wrh2/sputnik/Phase0/schedule/Project Schedule Calendar.pdf

# October 2015

Sunday | Monday | Tuesday | Wednesday | Thursday | Friday | Saturday
| | | | 1 | 2 | 3
4 | 5 | 6 | 7 | 8 | 9 | 10
11 | 12 | 13 | 14 | 15 | 16 | 17
18 | 19 | 20 | 21 | 22 | 23 | 24

Gather Requirement Information from PSAS, 1 day

25 | 26 | 27 | 28 | 29 | 30 | 31
Finalize Requirements, 3 days | | Design Initial RF Schematic, 1 day? | Design Initial MCU Schematic, 1 day?
Create Proposal, 1 day | Finalize Proposal, 1 day | Finalize Requirements, 3 days

Overflow Tasks

ID | Name | Start | Finish
27 | Part Selection | Sun 10/18/15 | Tue 10/20/15
47 | Test Completed Boards | Sun 10/18/15 | Tue 10/20/15
46 | Create Project Presentation Board | Wed 10/21/15 | Thu 10/22/15
16 | Design Initial USB to UART Schematic | Tue 10/27/15 | Tue 10/27/15
17 | Design Initial Battery Charger Schematic | Tue 10/27/15 | Tue 10/27/15

# November 2015

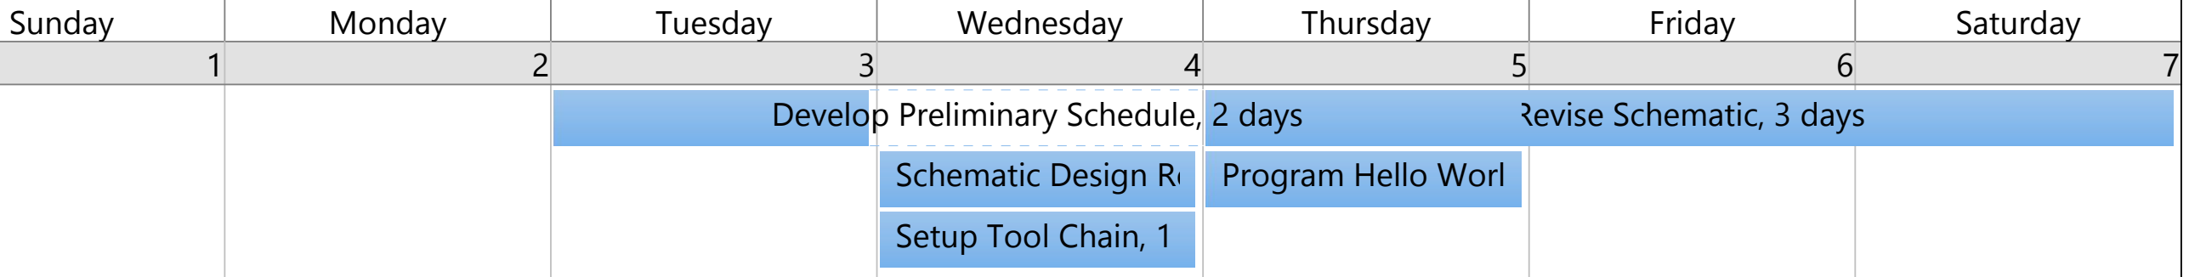
[picture p37: figure]
Sunday; Monday; Tuesday; Wednesday; Thursday; Friday; Saturday; Setup Tool Chain, 1 day

| | Develop Preliminary Schedule, 2 days | Schematic Design Review, 1 day Program Hello World, | Revise Schematic, 3 days | 1 day

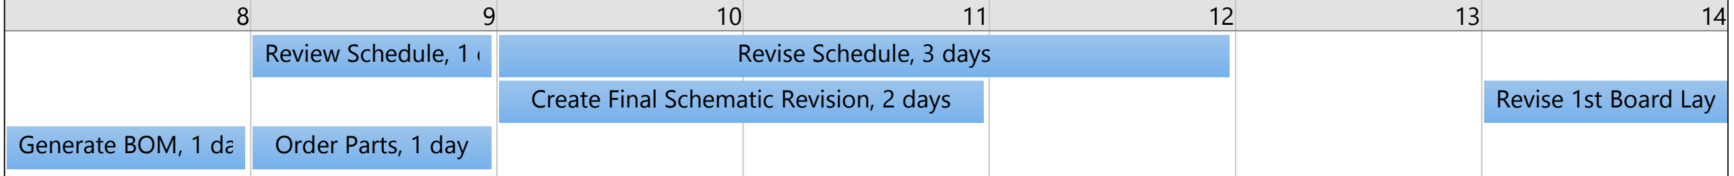
[picture p38: figure]

Generate BOM, 1 day | Review Schedule, 1 day Order Parts, 1 day | Revise Schedule, 3 days
Develop Final Board Layout, 2 days | | Order Boards, 1 day | Develop Test Plans, 3 daysReview Board Layout, 1 day

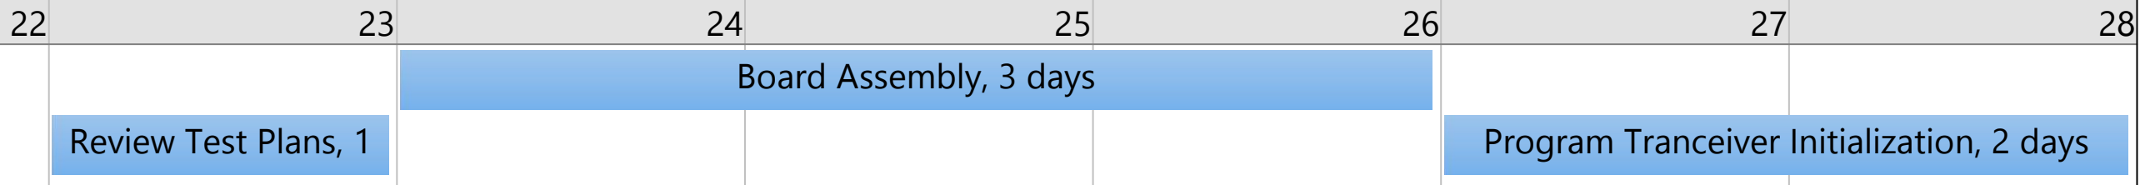
[picture p39: figure]
Review Test Plans, 1 day; Board Assembly, 3 days; Program Tranceiver Initialization, 2 days

29 | 30
Create Final Schematic Revision, 2 days | Revise 1st Board Layout, 5 days

Revise 1st Board Layout, 5 days Develop Block Diagrams, 2 days

Overflow Tasks

ID | Name | Start | Finish
21 | Develop Initial Board Layout | Thu 11/12/15 | Fri 11/13/15
26 | Create Solder Paste Stencil | Sun 11/22/15 | Sun 11/22/15
41 | Program Test of GPIO | Fri 11/27/15 | Sat 11/28/15
33 | Program Tansceiver Listening Interrupt | Sun 11/29/15 | Mon 11/30/15
35 | Program Tranceiver Broadcasting | Sun 11/29/15 | Mon 11/30/15
38 | Program Test of Timers | Sun 11/29/15 | Mon 11/30/15

# December 2015

Sunday | Monday | Tuesday | Wednesday | Thursday | Friday | Saturday
| | 1 | 2 | 3 | 4 | 5
6 | 7 | 8 | 9 | 10 | 11 | 12
Create Project Presentation Video, 3 days
13 | 14 | 15 | 16 | 17 | 18 | 19
20 | 21 | 22 | 23 | 24 | 25 | 26
27 | 28 | 29 | 30 | 31

Create Project Presentation Video, 3 days

Overflow Tasks

ID | Name | Start | Finish
39 | Program Test of SPI | Tue 12/1/15 | Wed 12/2/15
40 | Program Test of UART | Tue 12/1/15 | Wed 12/2/15
