wrh2/sputnik/Phase0/schedule/Project Schedule.pdf

ID | Task
Mode
| Task Name | Duration | Start | Finish | Predecessors
1 | Development Board for Cubesat Communication | 65 days
2 | Project Proposal
3 | Create Proposal | 1 day | Sun 10/18/15Sun 10/18/15
4 | Finalize Proposal | 1 day | Wed 10/21/15Wed 10/21/153
5 | Project Requirements
6 | Gather Requirement Information from PSAS | 6 days | Sun 10/18/15 | Fri 10/23/15
7 | Finalize Requirements | 3 days | Sat 10/24/15 Mon 10/26/156
8 | Project Schedule
10 | Schedule Review | 1 day | Mon 11/9/15Mon 11/9/159
9 | Preliminary Schedule | 2 days | Tue 11/3/15 | Wed 11/4/15
11 | Schedule Revision | 3 days | Tue 11/10/15Thu 11/12/1510
12 | Board Schematic
14 | Schematic Design Review1 day | Wed 11/4/15Wed 11/4/1513
15 | Schematic Revision | 7 days | Thu 11/5/15 | Wed 11/11/1514
13 | Preliminary Schematic | 12 days | Thu 10/22/15Mon 11/2/155
16 | Final Schematic Revision2 days | Thu 11/12/15Fri 11/13/15 | 15
17 | Board Layout
20 | Board Design Review | 1 day | Mon 11/16/15 | Mon 11/16/15 | 19
21 | Final Board Layout | 3 days | Sat 11/14/15 Mon 11/16/1516
18 | Preliminary Layout | 7 days | Tue 11/3/15 | Mon 11/9/1513
19 | Board Layout Revision | 6 days | Tue 11/10/15Sun 11/15/1518
22 | Create Boards
27 | Board Assembly | 5 days | Thu 11/26/15Mon 11/30/1526,25
23 | Part Selection | 5 days | Tue 11/3/15 | Sat 11/7/15 | 13
25 | Order and Receive Parts5 days | Fri 11/13/15 | Tue 11/17/1524
24 | Generate BOM | 1 day | Thu 11/12/15Thu 11/12/1515
26 | Order and Receive Boards9 days | Tue 11/17/15Wed 11/25/1516,21
28 | Board Programming
30 | Program Hello World | 4 days | Thu 11/5/15 | Sun 11/8/15 | 29
S | S | M

Oct 18, '15

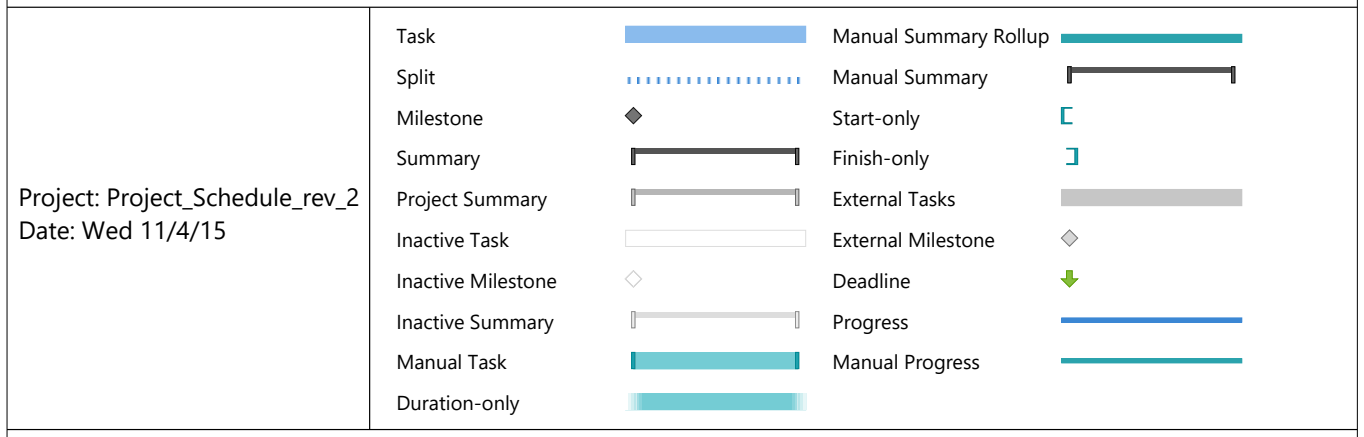
[picture p40: figure]
Task; Split; Milestone; Summary; Project Summary; Inactive Task; Inactive Milestone; Inactive Summary; Manual Task; Duration-only; Manual Summary Rollup; Manual Summary; Start-only; Finish-only; External Tasks; External Milestone; Deadline; Progress; Manual Progress; Project: Project_Schedule_rev_2 Date: Wed 11/4/15

ID | Task
Mode
Task Name | Duration | Start | Finish | Predecessors
31 | Program Transceiver | 16 days | Mon 11/9/15Tue 11/24/1530
29 | Setup Tool Chain | 1 day | Wed 11/4/15Wed 11/4/15
32 | System Design/Modeling | 5 days | Sat 11/14/15 Wed
11/18/15
33 | Test Plan | 5 days | Sat 11/21/15 Wed
11/25/15
34 | Project Presentation/Demo5 days | Thu 12/3/15 | Mon 12/7/1533
S | S | M

Oct 18, '15

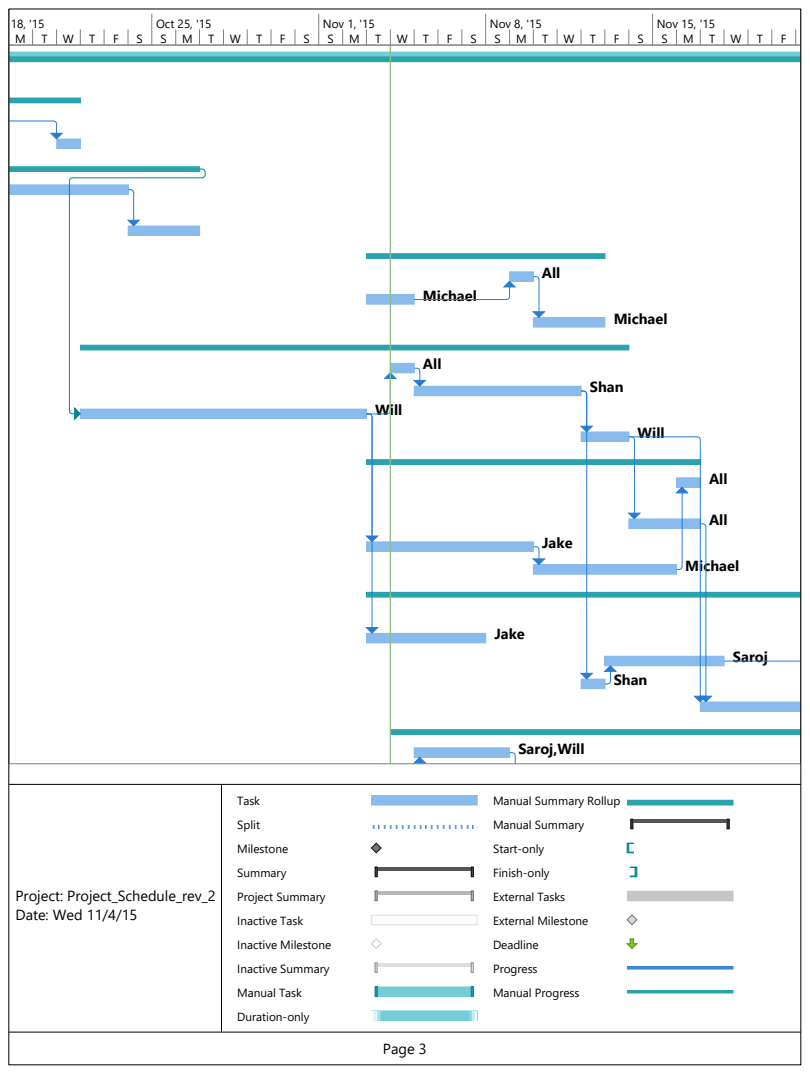
[picture p41: page 3]
All; Michael; Shan; Will; Jake; Saroj; Saroj,Will; Oct 18, '15; Oct 25, '15; Nov 1, '15; Nov 8, '15; Nov 15, '15; Task; Split; Milestone; Summary; Project Summary; Inactive Task; Inactive Milestone; Inactive Summary; Manual Task; Duration-only; Manual Summary; Start-only; Finish-only; External Tasks; External Milestone; Deadline; Progress; Manual Progress; Project: Project_Schedule_rev_2 Date: Wed 11/4/15

Manual Summary Rollup

### Will,Saroj,Michael

### All

M | T | W | T | F | S | S | M | T | W | T | F | S | S | M | T | W | T | F | S | S | M | T | W | T | F | S | S | M | T | W | T | F
Oct 18, '15 | Oct 25, '15 | Nov 1, '15 | Nov 8, '15 | Nov 15, '15

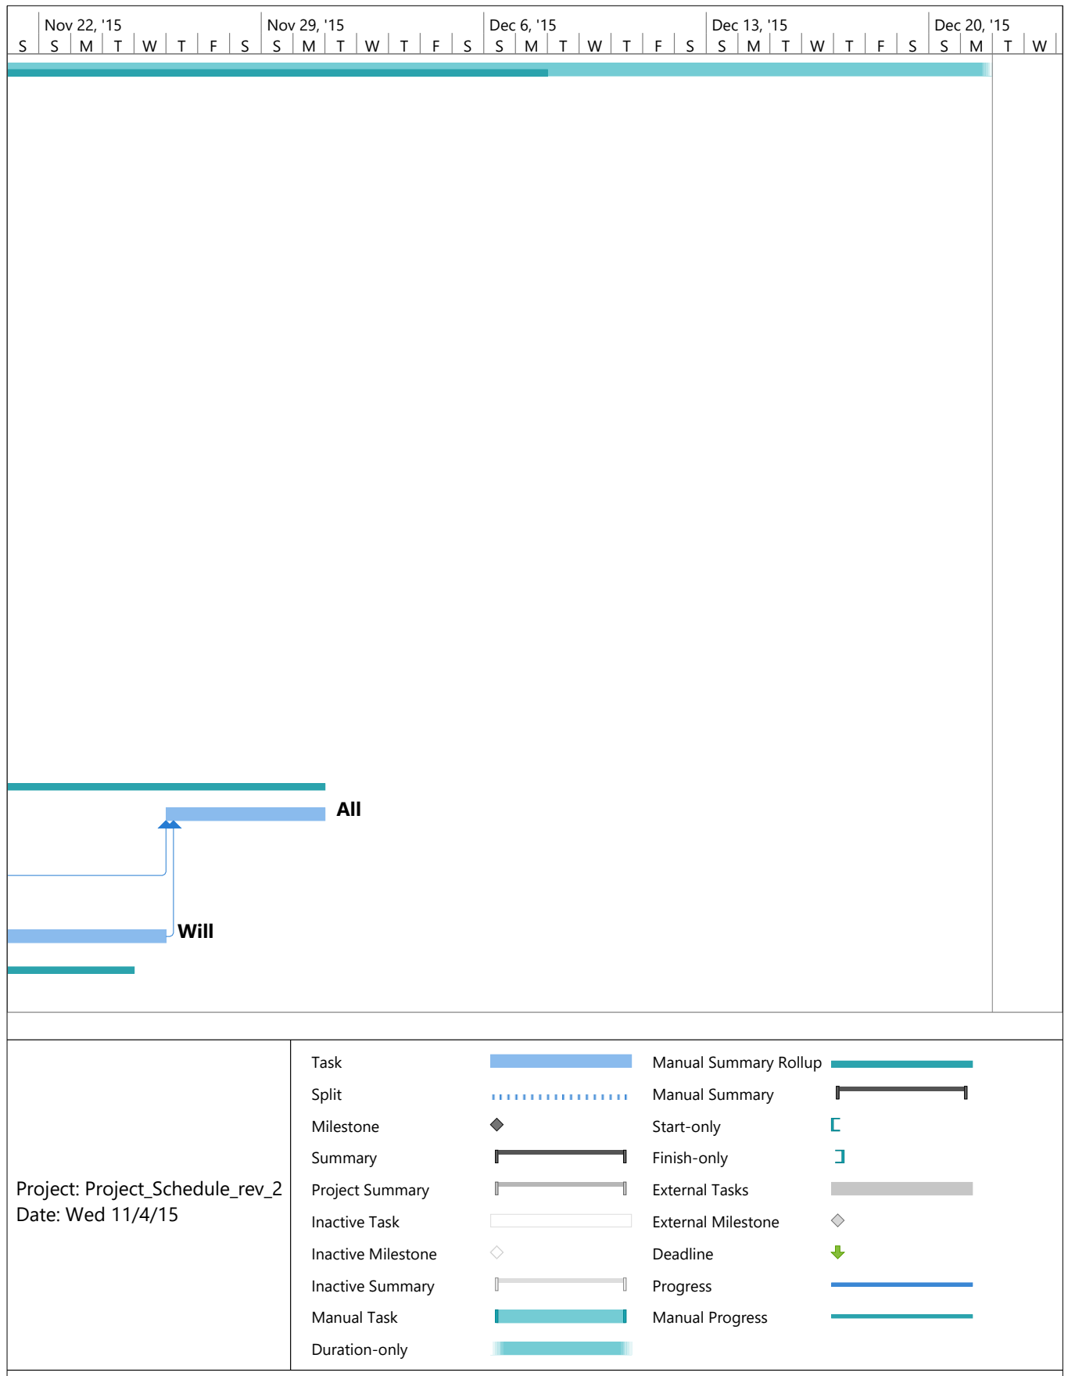
[picture p42: figure]
All; Saroj; Will; Nov 22, '15; Nov 29, '15; Dec 6, '15; Dec 13, '15; Dec 20, '15; Task; Split; Milestone; Summary; Project Summary; Inactive Task; Inactive Milestone; Inactive Summary; Manual Task; Duration-only; Manual Summary Rollup; Manual Summary; Start-only; Finish-only; External Tasks; External Milestone; Deadline; Progress; Manual Progress; Project: Project_Schedule_rev_2 Date: Wed 11/4/15

### Michael

### Will,Saroj

### All

### All

### All

S | S | M | T | W | T | F | S | S | M | T | W | T | F | S | S | M | T | W | T | F | S | S | M | T | W | T | F | S | S | M | T | W
Nov 22, '15 | Nov 29, '15 | Dec 6, '15 | Dec 13, '15 | Dec 20, '15
