wrh2/sputnik/images/phase0/BW.JPG

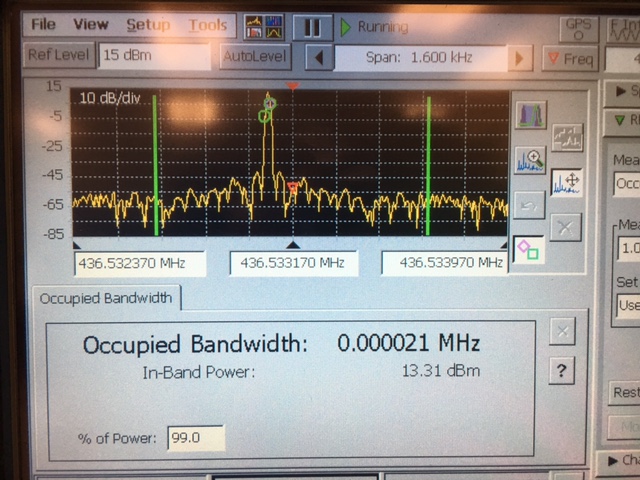
images/phase0/BW.JPG
