wrh2/sputnik/images/phase0/Channel_Power.JPG

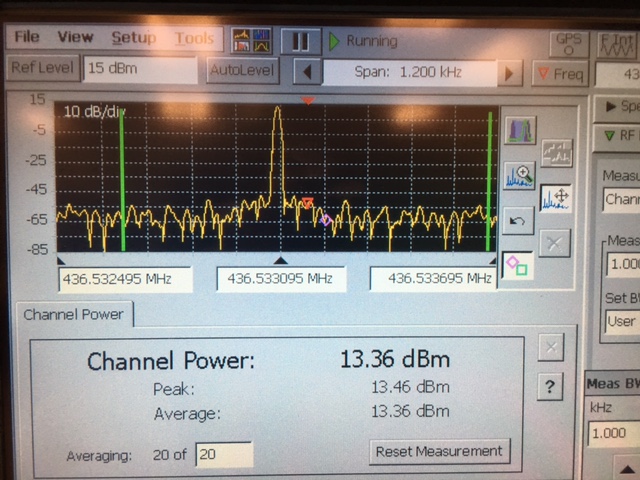
images/phase0/Channel_Power.JPG
