wrh2/sputnik/images/phase0/Field_Strength.JPG

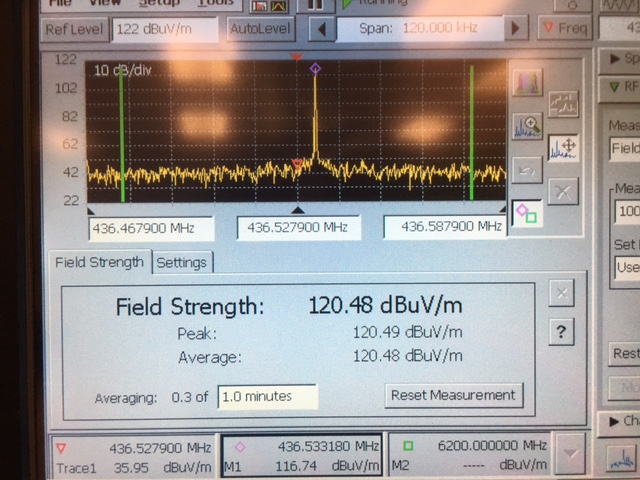
images/phase0/Field_Strength.JPG
