wrh2/sputnik/images/phase0/IMG_0521.JPG

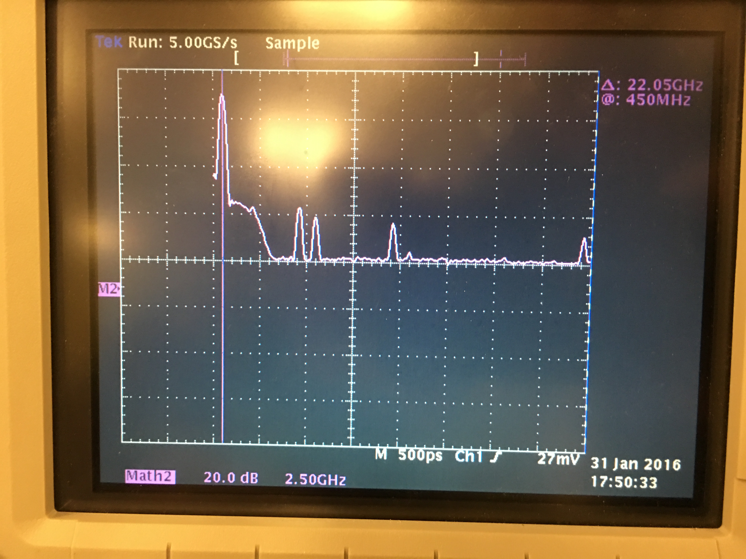
images/phase0/IMG_0521.JPG
