wrh2/sputnik/images/phase0/IMG_0522.JPG

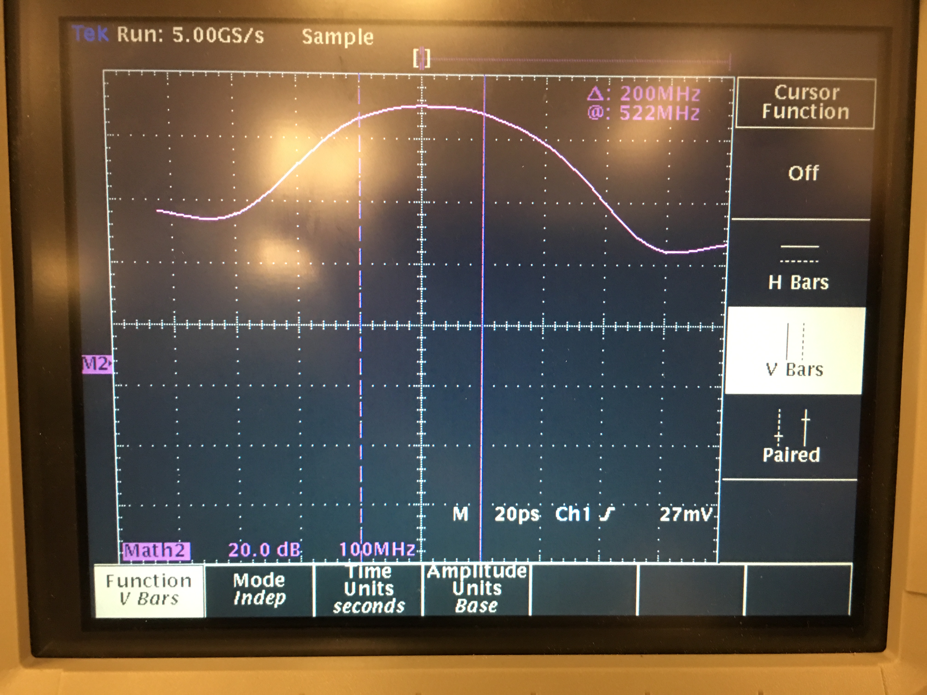
images/phase0/IMG_0522.JPG
