wrh2/sputnik/images/phase0/IMG_0523.JPG

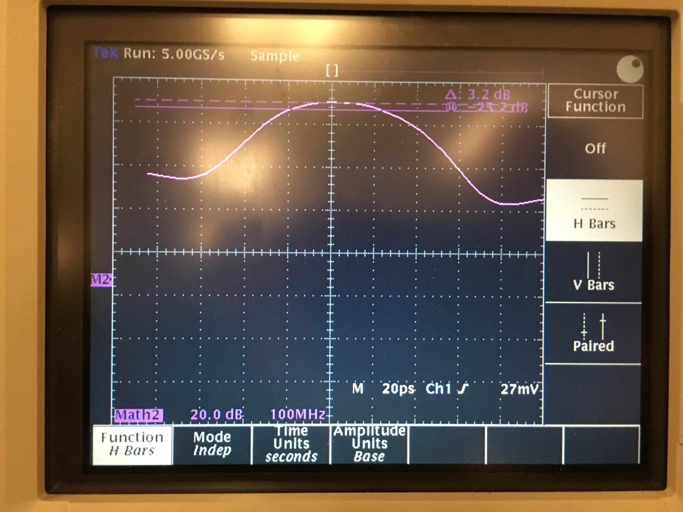
images/phase0/IMG_0523.JPG
