wrh2/sputnik/images/phase0/IMG_0524.JPG

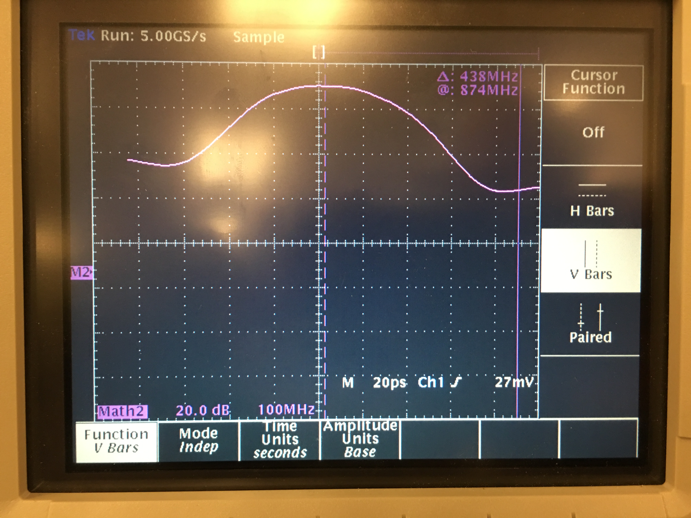
images/phase0/IMG_0524.JPG
