wrh2/sputnik/images/phase0/IMG_0525.JPG

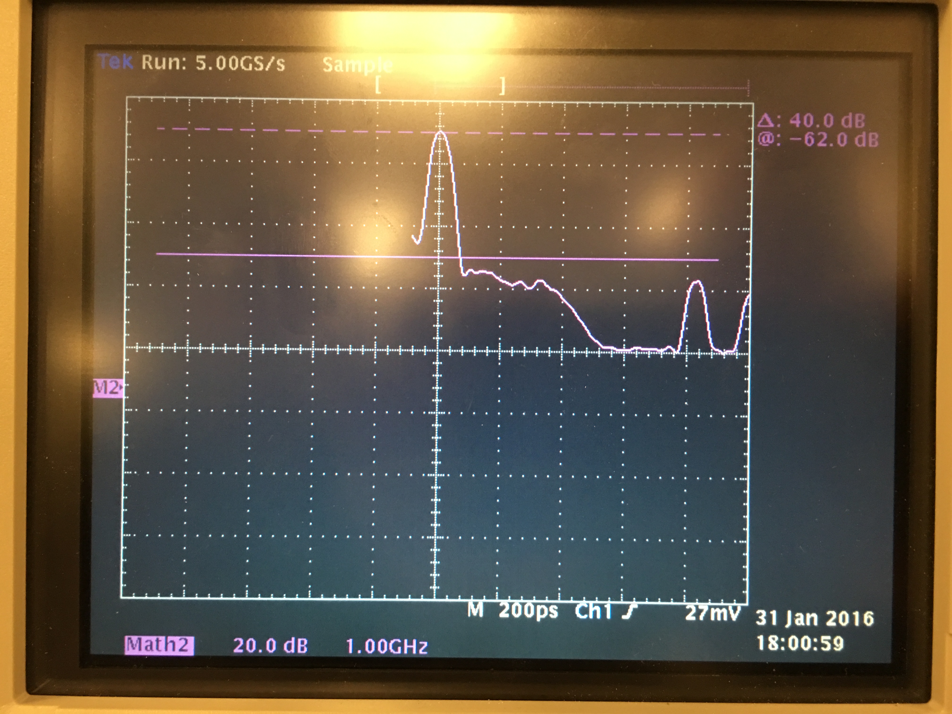
images/phase0/IMG_0525.JPG
