wrh2/sputnik/images/phase0/IMG_0526.JPG

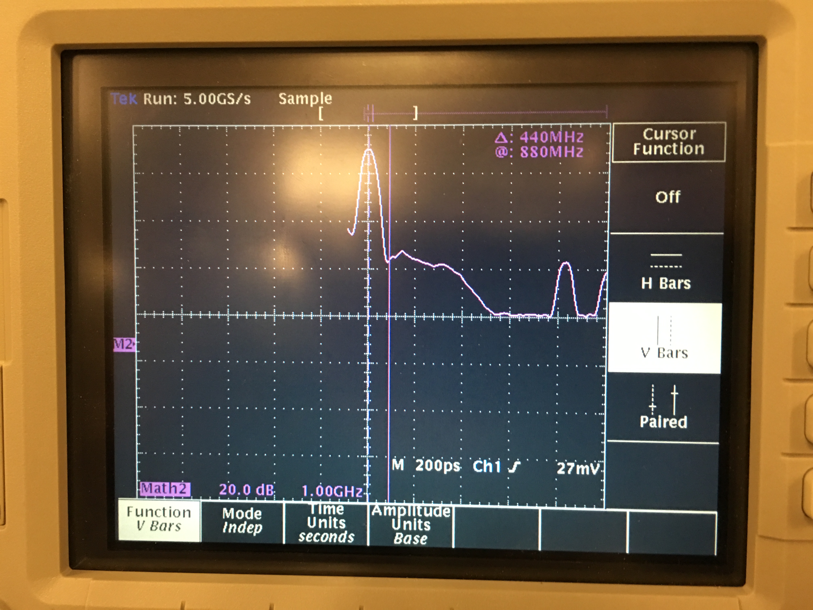
images/phase0/IMG_0526.JPG
