wrh2/sputnik/images/phase0/spurs.JPG

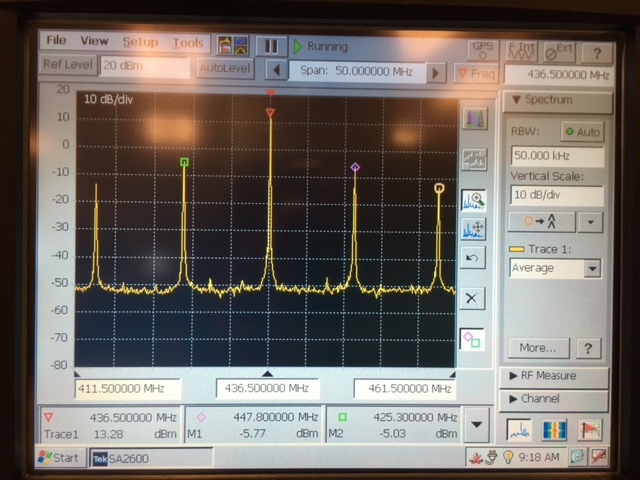
images/phase0/spurs.JPG
