wrh2/sputnik/images/phase1/phase1_HL.png

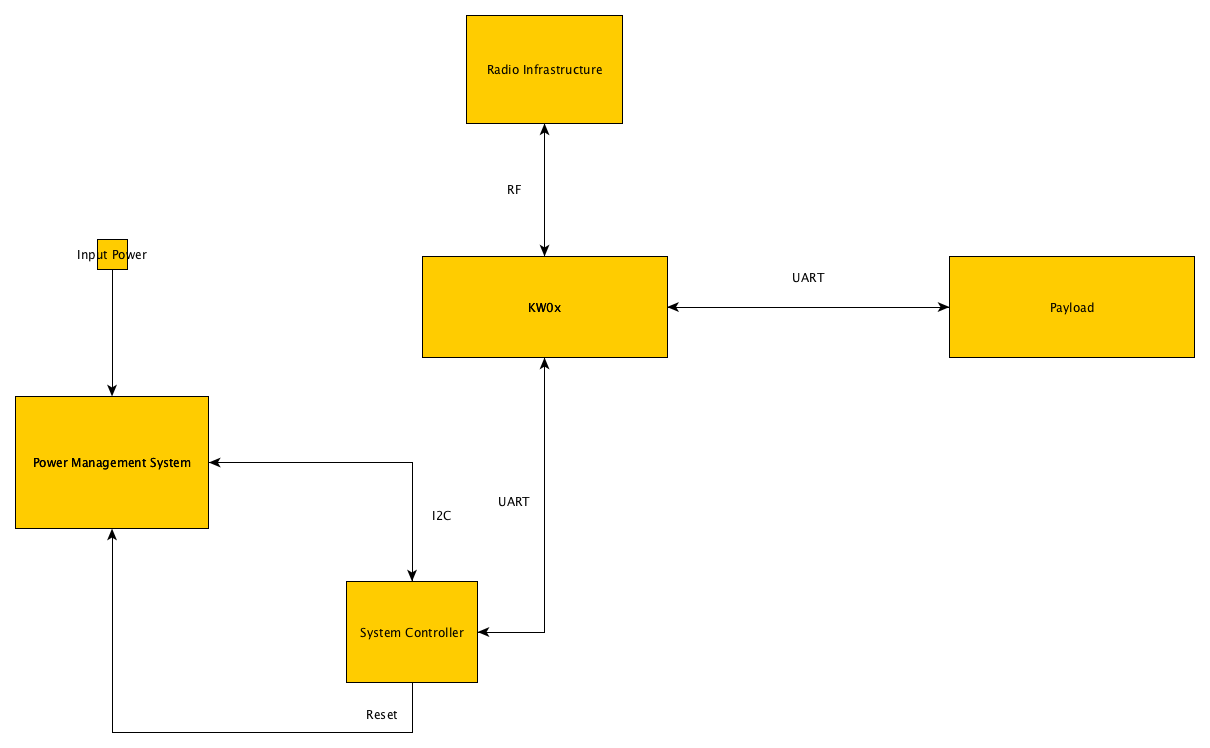
images/phase1/phase1_HL.png
