wrh2/sputnik/Phase0/eagle/psas_c3_sch.png

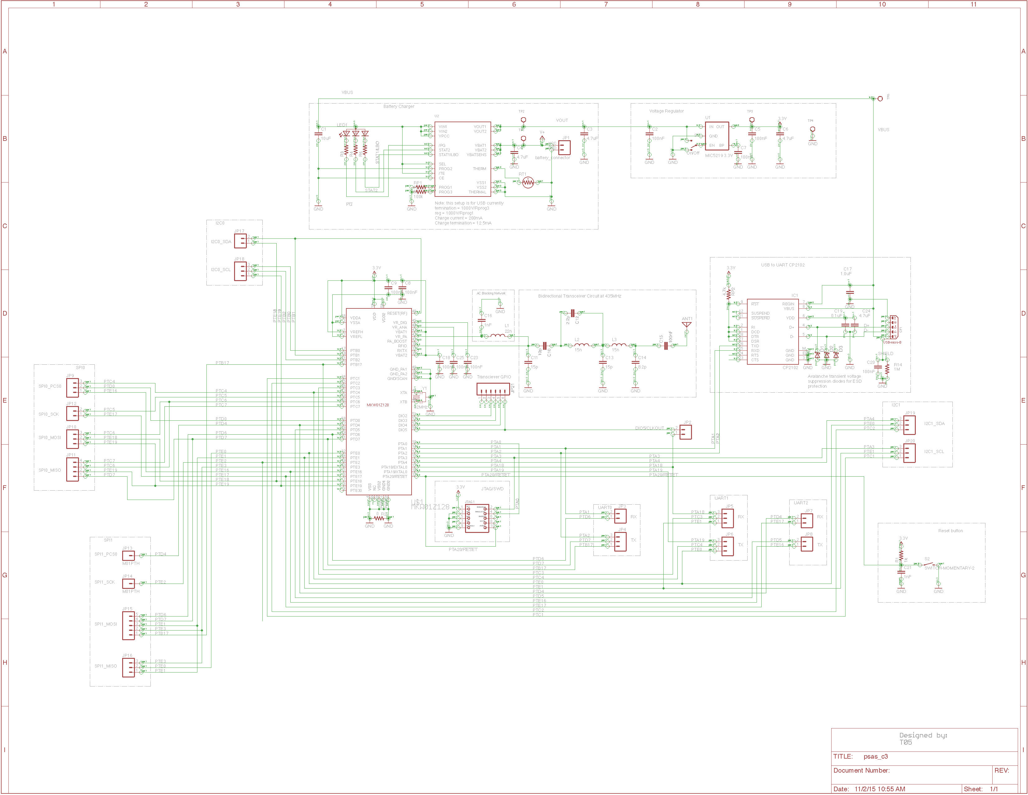
Phase0/eagle/psas_c3_sch.png
