wrh2/sputnik/Phase0/eagle/psas_c3_sch_v2.png

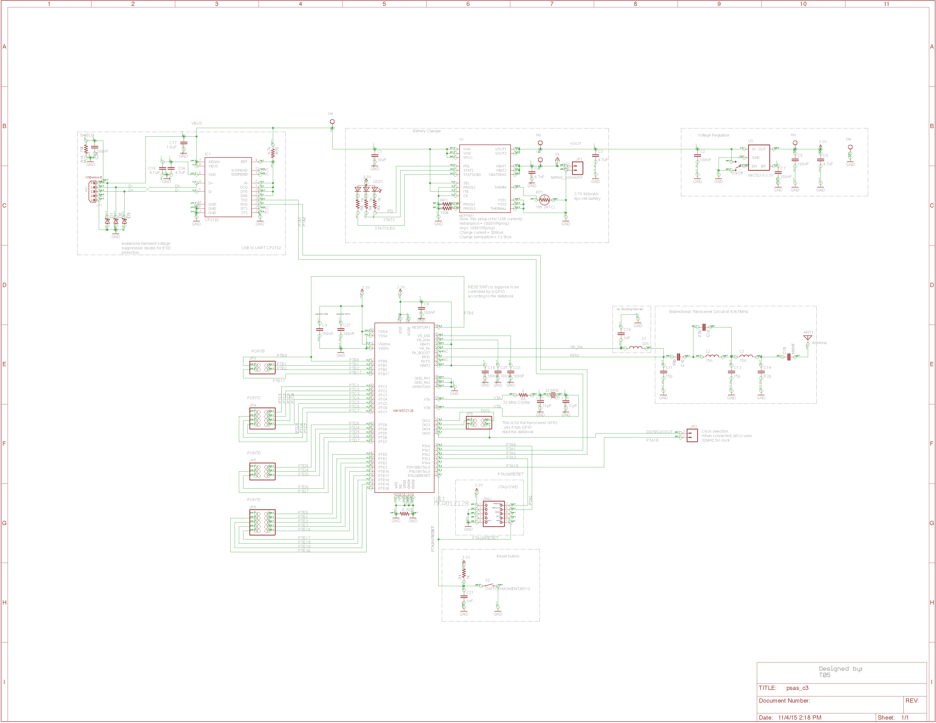
Phase0/eagle/psas_c3_sch_v2.png
