wrh2/sputnik/RF_Materials/Antenna_Filters/prototype_photos/PA210077.JPG

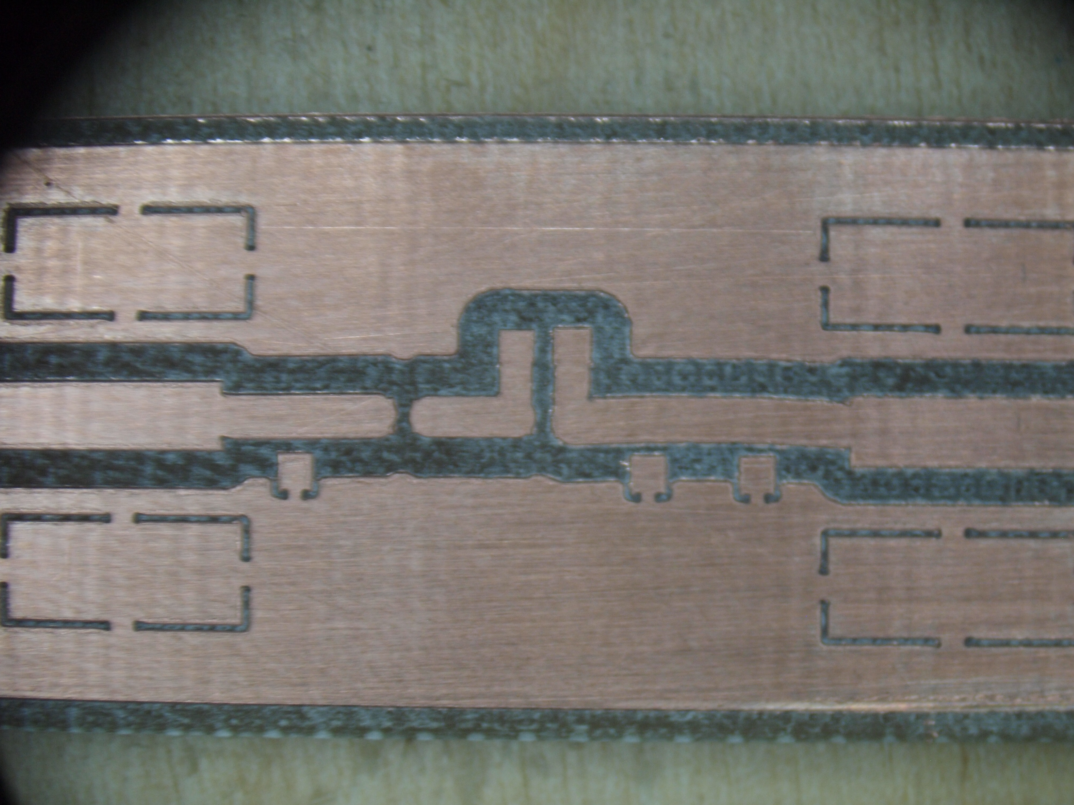
RF_Materials/Antenna_Filters/prototype_photos/PA210077.JPG
