wrh2/sputnik/RF_Materials/Antenna_Filters/prototype_photos/PA210079.JPG

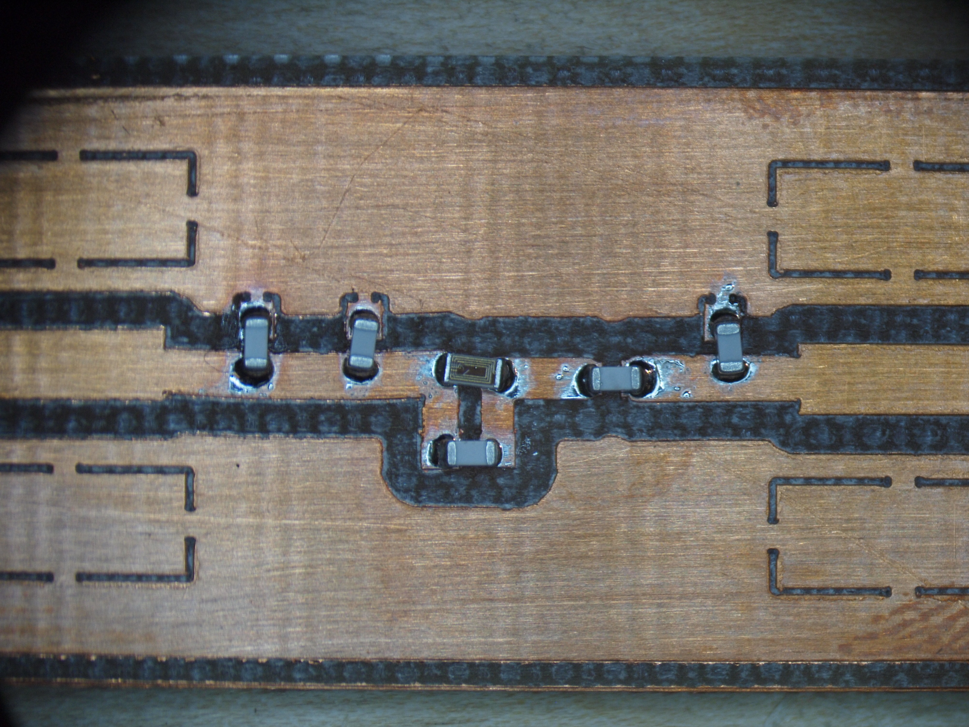
RF_Materials/Antenna_Filters/prototype_photos/PA210079.JPG
