wrh2/sputnik/RF_Materials/Antenna_Filters/prototype_photos/PA270084.JPG

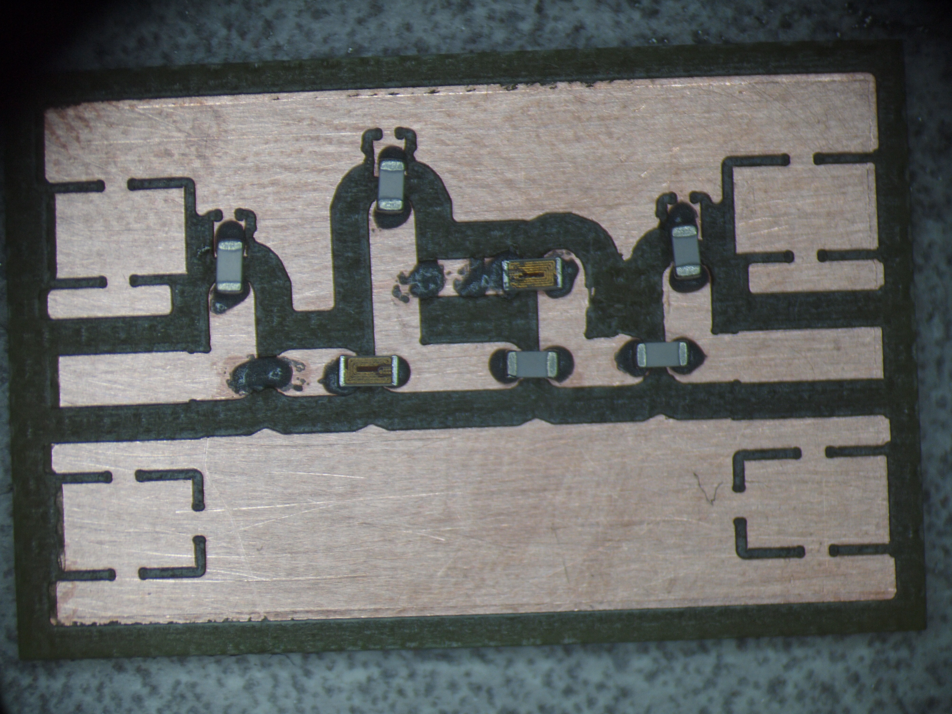
RF_Materials/Antenna_Filters/prototype_photos/PA270084.JPG
