wrh2/sputnik/RF_Materials/Antenna_Filters/prototype_photos/PA270085.JPG

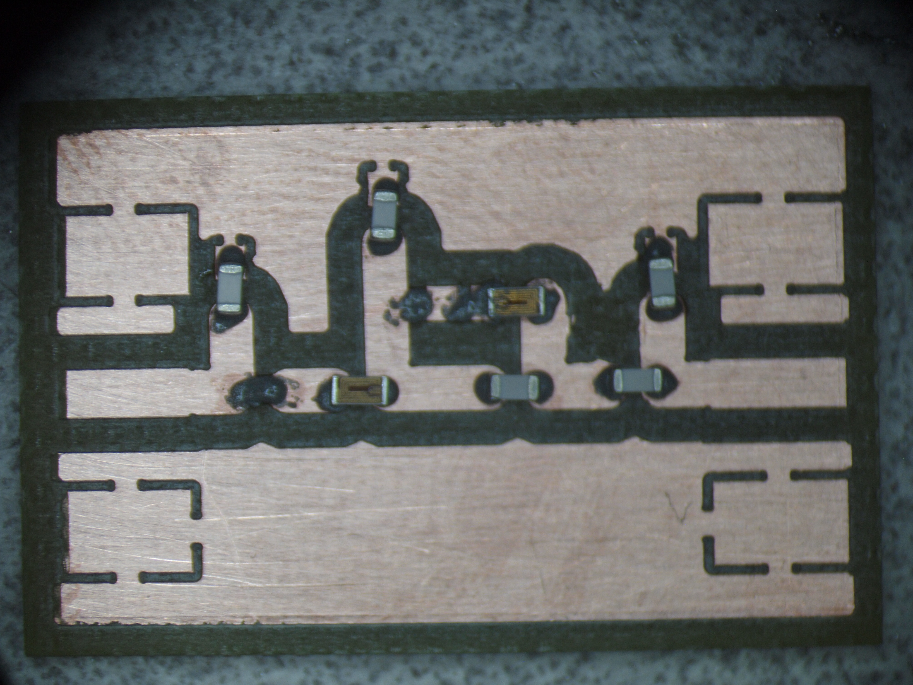
RF_Materials/Antenna_Filters/prototype_photos/PA270085.JPG
