wrh2/sputnik/Vendor Firmware/Kinetis SDK v.1.3.0 API Reference Manual/Kinetis_SDK_Block_Diagram.png

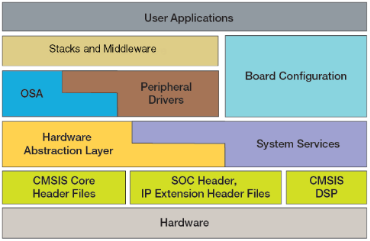
Vendor Firmware/Kinetis SDK v.1.3.0 API Reference Manual/Kinetis_SDK_Block_Diagram.png
