wrh2/sputnik/RF_Materials/Testing/RFPAtest.csv

# [0]current | [1]temp | [2]input | [3]gain | [4]attenuation | [5]output
.998 | 57 | -1.62 | 30 | 4 | 24.6
1.053 | 61 | -1 | 30 | 4 | 25.3
1.115 | 63 | 0 | 30 | 4 | 25.8
1.2 | 65 | 1.3 | 30 | 4 | 26.5
1.26 | 68.5 | 2.0 | 30 | 4 | 26.8
