wrh2/sputnik/RF_Materials/Simulations/project front end 433.asc

C1: cap; 14p
C2: cap; 2.2p
C3: cap; 0.1µ
C3a: cap; 15p
C3b: cap; 8.2p
C4: cap; 100n
Cin: cap; 15p
L1: ind; 15n
L2: ind; 15n
L3: ind; 22n
Load: res; 50
R3: res; 50
R4: res; 50
V3: voltage; 3.6
V4: voltage; SINE(0 5 1k); AC 1
Named nets: 0, Vout, Vin
.AC dec 1000 100Meg 1G
