wrh2/sputnik/RF_Materials/Antenna_Filters/LTSpice_filter_designs/DualOutPutFilter.asc

C1: cap; 2.2p
C2: cap; 15p
C3: cap; 100n
C3a: cap; 15p
C3b: cap; 8.2p
C4: cap; 15p
C5: cap; 2.2p
C6: cap; 8.2p
C7: cap; 100n
C8: cap; 15p
Cin1: cap; 15p
Cin: cap; 15p
L1: ind; 5.6n
L2: ind; 15n
L3: ind; 22n
L4: ind; 15n
L5: ind; 15n
L6: ind; 22n
Load1: res; 50
Load: res; 50
R1: res; 50
R2: res; 1e9
R3: res; 1e9
R4: res; 50
V1: voltage; ""; AC 2
V2: voltage; ""; AC 1
V3: voltage; ""; AC 2
V4: voltage; ""; AC 1
Named nets: 0, Vin, s11, s21, RFIO
.AC dec 10000 100k 100G
24p
Cauer filter
AC blocking network
Lowpass filter
24p
Cauer filter
AC blocking network
Lowpass filter
