wrh2/sputnik/RF_Materials/Antenna_Filters/LTSpice_filter_designs/project_front_end_433_with_V+version3.asc

C1: cap; 2.2p
C2: cap; 15p
C3: cap; 100n
C3a: cap; 15p
C3b: cap; 8.2p
Cin: cap; 15p
L1: ind; 15n
L2: ind; 15n
L3: ind; 22n
Load: res; 50
R1: res; 50
R3: res; 1e9
V1: voltage; ""; AC 2
V2: voltage; ""; AC 1
Named nets: 0, Vin, s11, s21
.AC dec 10000 100k 100G
24p
Cauer filter
AC blocking network
Lowpass filter
