wrh2/sputnik/RF_Materials/Antenna_Filters/LTSpice_filter_designs/Cauer_4-stage.asc

C1: cap; 602p
C3: cap; 1.9p
C5: cap; 17p
C7: cap; 602p
L1: ind; {L}
L2: ind; 7.9n
L3: ind; 71n
L4: ind; {L}
R1: res; 50
R2: res; 50
V1: voltage; SINE(0 1 400Meg); AC 1
Named nets: 0, Vin, Vout
.ac dec 100 100k 100t
.param L 0.22n
