wrh2/sputnik/RF_Materials/Antenna_Filters/LTSpice_filter_designs/Cauer_bandpass_standard.asc

C1: cap; 560p
C2: cap; 47p
C3: cap; 18p
C4: cap; 1.8p
C5: cap; 560p
C6: cap; 47p
L1: ind; 220p
L2: ind; 8.2n
L3: ind; 68n
L4: ind; 220p
R1: res; 50
R2: res; 50
V1: voltage; SINE(0 1 400Meg); AC 1
Named nets: 0, Vin, Vout
.ac dec 100 100k 100t
