wrh2/sputnik/RF_Materials/Antenna_Filters/LTSpice_filter_designs/433MHz filter with 14nH inductors.asc

C2: cap; 10p
C3: cap; 2.4p
C5: cap; 15p
C6: cap; 15p
C7: cap; 8.2p
L3: ind; 14n
L4: ind; 14n
Load: res; 50
R3: res; 50
V3: voltage; SINE(0 5 1k); AC 1
Named nets: 0, In, OUT
.ac dec 100 10 100t
