wrh2/sputnik/RF_Materials/Antenna_Filters/LTSpice_filter_designs/433MHz filter with added low pass_and increased high pass.asc

C1: cap; 7p
C2: cap; 10p
C3: cap; 2.4p
C4: cap; 3p
C5: cap; 15p
C6: cap; 15p
C7: cap; 8.2p
C8: cap; 22.5p
L1: ind; 7n
L2: ind; 16n
L3: ind; 14n
L4: ind; 14n
L5: ind; 56.3n
Load: res; 50
R3: res; 50
V3: voltage; SINE(0 5 1k); AC 1
Named nets: 0, In, OUT
.ac dec 100 10 100t
