wrh2/sputnik/RF_Materials/Antenna_Filters/LTSpice_filter_designs/433MHz filter with added low pass_vs 2.asc

C1: cap; 6.54p
C2: cap; 10p
C3: cap; 2.4p
C4: cap; 2.7p
C5: cap; 15p
C6: cap; 15p
C7: cap; 8.2p
L1: ind; 6.77n
L2: ind; 16.3n
L3: ind; 14n
L4: ind; 14n
Load: res; 50
R3: res; 50
V3: voltage; SINE(0 5 1k); AC 1
Named nets: 0, In, OUT
.ac dec 100 10 100t
