wrh2/sputnik/Vendor Firmware/Kinetis SDK v.1.3.0 API Reference Manual/group__lpuart__driver.js

var group__lpuart__driver =
[
    [ "lpuart_dma_state_t", "group__lpuart__driver.html#structlpuart__dma__state__t", [
      [ "isTxBusy", "group__lpuart__driver.html#a3a689e6b54fb17b7c5823cecb08b9a0e", null ],
      [ "isRxBusy", "group__lpuart__driver.html#a4239b25df7820ad2fbd40c017d151b90", null ],
      [ "isTxBlocking", "group__lpuart__driver.html#a84bea4d3fa9e30b7e6c1da7450ca2ee6", null ],
      [ "isRxBlocking", "group__lpuart__driver.html#a3e918f3a9816ecbf655beef6e266a62c", null ],
      [ "txIrqSync", "group__lpuart__driver.html#aa53315df3bda186ab21acc512f5ff757", null ],
      [ "rxIrqSync", "group__lpuart__driver.html#ad5a91401bf62dfa76ea65561fd3db5c3", null ],
      [ "dmaLpuartTx", "group__lpuart__driver.html#a0803017d7c560a7152fa0561023c33f8", null ],
      [ "dmaLpuartRx", "group__lpuart__driver.html#af0382804027a583672f50afb624c2ed1", null ]
    ] ],
    [ "lpuart_dma_user_config_t", "group__lpuart__driver.html#structlpuart__dma__user__config__t", [
      [ "clockSource", "group__lpuart__driver.html#a32b3c83c9b66c824bf49eea075bec03e", null ],
      [ "baudRate", "group__lpuart__driver.html#ae81d05456c27fefe36b2256d02be1c9b", null ],
      [ "parityMode", "group__lpuart__driver.html#a44200b5818a781ae1dc2400b4c35c713", null ],
      [ "stopBitCount", "group__lpuart__driver.html#a3858f79a30b208d26a1d680b9924bc7c", null ],
      [ "bitCountPerChar", "group__lpuart__driver.html#ad7588d650143f84bdefd4710ebafe274", null ]
    ] ],
    [ "lpuart_state_t", "group__lpuart__driver.html#structlpuart__state__t", [
      [ "txFifoEntryCount", "group__lpuart__driver.html#a0f7eab0bab7ae6671d9d3fb3fa05310e", null ],
      [ "txBuff", "group__lpuart__driver.html#a79927fda606bbb12346d53ff7f765ac5", null ],
      [ "rxBuff", "group__lpuart__driver.html#a1f05e6e6e1d4f81d07e99872e659f2bd", null ],
      [ "txSize", "group__lpuart__driver.html#a9df841a1813731cfd4a6b9d24d200e3f", null ],
      [ "rxSize", "group__lpuart__driver.html#a2deadfc3116883447f3c48f44604e71e", null ],
      [ "isTxBusy", "group__lpuart__driver.html#a984904d546bdca3a938543ec21f9eebf", null ],
      [ "isRxBusy", "group__lpuart__driver.html#aceb9bc59aa86d1828ba8cb159d7fa953", null ],
      [ "isTxBlocking", "group__lpuart__driver.html#aab191956c24287f40c1248bb39622cff", null ],
      [ "isRxBlocking", "group__lpuart__driver.html#acaf7d16fb526a357d3f2debc79b862b7", null ],
      [ "txIrqSync", "group__lpuart__driver.html#a68e12f88dc53743327f093db788ccbe1", null ],
      [ "rxIrqSync", "group__lpuart__driver.html#ad4396a435b923aa96c7d135c5af35098", null ],
      [ "rxCallback", "group__lpuart__driver.html#aa41155f86d7c5044c34076e18dbcb911", null ],
      [ "rxCallbackParam", "group__lpuart__driver.html#a682b85e3a1e70ecccd7d443a0fec961a", null ],
      [ "txCallback", "group__lpuart__driver.html#a567b26956e5ed3f445486dd4548a0b7d", null ],
      [ "txCallbackParam", "group__lpuart__driver.html#acce178541939c8cd48a62e0d6ea49afe", null ]
    ] ],
    [ "lpuart_user_config_t", "group__lpuart__driver.html#structlpuart__user__config__t", [
      [ "clockSource", "group__lpuart__driver.html#adf5616486d24dfa8d0d7a10bfdbf910e", null ],
      [ "baudRate", "group__lpuart__driver.html#a838c0f0439ea4d5bed2b0bf908ee9b74", null ],
      [ "parityMode", "group__lpuart__driver.html#ac6e3ed134826929f1a2bfbbb7126690f", null ],
      [ "stopBitCount", "group__lpuart__driver.html#ad566a09f6a9edf689eb83e7ad7802072", null ],
      [ "bitCountPerChar", "group__lpuart__driver.html#a20608b8b3f959345c6f5d69db967b76c", null ]
    ] ],
    [ "lpuart_edma_state_t", "group__lpuart__driver.html#structlpuart__edma__state__t", [
      [ "isTxBusy", "group__lpuart__driver.html#a6631de98722ba199382ba16d42d2b79e", null ],
      [ "isRxBusy", "group__lpuart__driver.html#a4c83bc7dc02ad3a233d69f08be30a873", null ],
      [ "isTxBlocking", "group__lpuart__driver.html#a9ae19f11bd76bc1fe0c290cc50de4726", null ],
      [ "isRxBlocking", "group__lpuart__driver.html#a090267e2e6e06304aa02197fa18e3e3e", null ],
      [ "txIrqSync", "group__lpuart__driver.html#a80e910501014d0cb82c5ae247ff53902", null ],
      [ "rxIrqSync", "group__lpuart__driver.html#abedae58f55b129c8e97ee0d236ee4d81", null ],
      [ "edmaLpuartTx", "group__lpuart__driver.html#aa75e1ab75755e98d854eafa916ada999", null ],
      [ "edmaLpuartRx", "group__lpuart__driver.html#ac40f68885bc04eb3866f895510d9ddd0", null ]
    ] ],
    [ "lpuart_edma_user_config_t", "group__lpuart__driver.html#structlpuart__edma__user__config__t", [
      [ "clockSource", "group__lpuart__driver.html#a6a774b677bc2c328d56d0cf924cf9b2e", null ],
      [ "baudRate", "group__lpuart__driver.html#acb2483eabdfc3a2d23d35008ae67a666", null ],
      [ "parityMode", "group__lpuart__driver.html#aaee6726a0fb8a404c2d69b574683586c", null ],
      [ "stopBitCount", "group__lpuart__driver.html#afdbc013e0149b7012950e316a8a54c0f", null ],
      [ "bitCountPerChar", "group__lpuart__driver.html#ac70443e806978dbb0384edfb605120bb", null ]
    ] ],
    [ "lpuart_rx_callback_t", "group__lpuart__driver.html#gae0e1521e8a5c398ded255b4e36b41e4d", null ],
    [ "lpuart_tx_callback_t", "group__lpuart__driver.html#ga60256f1c1ba46e8d782a65652ddb7839", null ],
    [ "LPUART_DRV_DmaInit", "group__lpuart__driver.html#ga064269ac98e83e64b82d21ba1aff609d", null ],
    [ "LPUART_DRV_DmaDeinit", "group__lpuart__driver.html#ga0c6a401a0e31556630c35db18e0039f0", null ],
    [ "LPUART_DRV_DmaSendDataBlocking", "group__lpuart__driver.html#ga895b47dff3caa0c4980bc18a3e3ced7f", null ],
    [ "LPUART_DRV_DmaSendData", "group__lpuart__driver.html#ga418843ddf234a07da1846f2aa8c3de34", null ],
    [ "LPUART_DRV_DmaGetTransmitStatus", "group__lpuart__driver.html#ga2d9e6996101e54c7a7ea386794806033", null ],
    [ "LPUART_DRV_DmaAbortSendingData", "group__lpuart__driver.html#ga1a2b42f7116473f4b8b1b333353982a9", null ],
    [ "LPUART_DRV_DmaReceiveDataBlocking", "group__lpuart__driver.html#gadc708acb4ce03500db3cc61ba4d556e3", null ],
    [ "LPUART_DRV_DmaReceiveData", "group__lpuart__driver.html#ga05ee28edb3dba0c61f03a82db7e6b6b8", null ],
    [ "LPUART_DRV_DmaGetReceiveStatus", "group__lpuart__driver.html#ga63c0b5b001e22819e6c95dbbc9ed0693", null ],
    [ "LPUART_DRV_DmaAbortReceivingData", "group__lpuart__driver.html#ga93c78fd45df40e79528ef7719f3dda4e", null ],
    [ "LPUART_DRV_Init", "group__lpuart__driver.html#gaa2018ae76bd49730483a8baae25c53f6", null ],
    [ "LPUART_DRV_Deinit", "group__lpuart__driver.html#gabd4450191129e27133c3e9d7b9b0835b", null ],
    [ "LPUART_DRV_InstallRxCallback", "group__lpuart__driver.html#gadd244afb53632ae945f06eb26c8f75ed", null ],
    [ "LPUART_DRV_InstallTxCallback", "group__lpuart__driver.html#gad69abd22677c3bad6ad2272f5c5c6b46", null ],
    [ "LPUART_DRV_SendDataBlocking", "group__lpuart__driver.html#ga39f1029b67e998a3d6bb37713a92c07a", null ],
    [ "LPUART_DRV_SendData", "group__lpuart__driver.html#ga324abd6831da2a38d37f02e6e407364d", null ],
    [ "LPUART_DRV_GetTransmitStatus", "group__lpuart__driver.html#gad07fff86ac66ba3ad124d9f6667bf4c8", null ],
    [ "LPUART_DRV_AbortSendingData", "group__lpuart__driver.html#ga6220d004196297778a295f18ae6f7a56", null ],
    [ "LPUART_DRV_ReceiveDataBlocking", "group__lpuart__driver.html#gae3fbdc9c2c35d844a32f72a4621429e9", null ],
    [ "LPUART_DRV_ReceiveData", "group__lpuart__driver.html#ga83af85267fa43659a6b30ee73ae4666e", null ],
    [ "LPUART_DRV_GetReceiveStatus", "group__lpuart__driver.html#ga8fd64e4e817e5a212da5d7aebe9e41e4", null ],
    [ "LPUART_DRV_AbortReceivingData", "group__lpuart__driver.html#gaa4d27bb305848e284ec7378b380ca755", null ],
    [ "LPUART_DRV_EdmaInit", "group__lpuart__driver.html#ga2e4a5a1c2e9f2dbae1752397b89e7e3e", null ],
    [ "LPUART_DRV_EdmaDeinit", "group__lpuart__driver.html#ga11246aa932598eef5afcfd8c728c4e11", null ],
    [ "LPUART_DRV_EdmaSendDataBlocking", "group__lpuart__driver.html#ga952e9ea150c1ed05cc9e5b099d8f8052", null ],
    [ "LPUART_DRV_EdmaSendData", "group__lpuart__driver.html#gadabd0e9c30fd7a50a7a03e11632526a3", null ],
    [ "LPUART_DRV_EdmaGetTransmitStatus", "group__lpuart__driver.html#ga3f5df97b1be4b65125d6ac45db6efdcb", null ],
    [ "LPUART_DRV_EdmaAbortSendingData", "group__lpuart__driver.html#gac702acc3061f98fe54f5ae3148ae3271", null ],
    [ "LPUART_DRV_EdmaReceiveDataBlocking", "group__lpuart__driver.html#ga4b4b255b05556b358ee97805fc67bf42", null ],
    [ "LPUART_DRV_EdmaReceiveData", "group__lpuart__driver.html#ga2e1167a6579821c40895f749a9544033", null ],
    [ "LPUART_DRV_EdmaGetReceiveStatus", "group__lpuart__driver.html#ga09d3edd194a36db527e10ca22c5fc831", null ],
    [ "LPUART_DRV_EdmaAbortReceivingData", "group__lpuart__driver.html#ga07f856d5aa814e920a03d126349936db", null ],
    [ "g_lpuartBase", "group__lpuart__driver.html#gab74388760f721ce45a2b67ba94c621da", null ],
    [ "g_lpuartBase", "group__lpuart__driver.html#gab74388760f721ce45a2b67ba94c621da", null ],
    [ "g_lpuartRxTxIrqId", "group__lpuart__driver.html#ga508fad7b5e3ffdec93efedbac9820b3a", null ],
    [ "g_lpuartBase", "group__lpuart__driver.html#gab74388760f721ce45a2b67ba94c621da", null ]
];
