wrh2/sputnik/Vendor Firmware/Kinetis SDK v.1.3.0 API Reference Manual/group__pwm__driver.js

var group__pwm__driver =
[
    [ "pwm_module_signal_setup_t", "group__pwm__driver.html#structpwm__module__signal__setup__t", [
      [ "pwmPeriod", "group__pwm__driver.html#ae7a4e767daaae462fa391f80dd93aa96", null ],
      [ "pwmType", "group__pwm__driver.html#af4c39111efa221cfe49294eb077357e5", null ],
      [ "pwmAPulseWidth", "group__pwm__driver.html#adfb1d1060fee7df63c525f214ad952c7", null ],
      [ "pwmBPulseWidth", "group__pwm__driver.html#ac0e34740e7d3486ad25e12e3a3a22df1", null ],
      [ "pwmAPolarity", "group__pwm__driver.html#aa4dc33ce84916f12bb7410f2f9d3f8f6", null ],
      [ "pwmBPolarity", "group__pwm__driver.html#aca418b4dc30eac2cbbd09ceb4a7164bf", null ]
    ] ],
    [ "FLEXPWM_NO_PWM_OUT_SIGNAL", "group__pwm__driver.html#ga09f64a61d040ce88a55cd7e702cd8faf", null ],
    [ "pwm_signal_type_t", "group__pwm__driver.html#ga418690e72e12a50d4cf390edee77a1c9", [
      [ "kFlexPwmSignedCenterAligned", "group__pwm__driver.html#gga418690e72e12a50d4cf390edee77a1c9aa9ea7ec7245d938f20044140073a9e0b", null ],
      [ "kFlexPwmCenterAligned", "group__pwm__driver.html#gga418690e72e12a50d4cf390edee77a1c9a5ac7f65075678930e6bac42da7474acb", null ],
      [ "kFlexPwmSignedEdgeAligned", "group__pwm__driver.html#gga418690e72e12a50d4cf390edee77a1c9a899fa90b38f59d993e37a1612b16c3bf", null ],
      [ "kFlexPwmEdgeAligned", "group__pwm__driver.html#gga418690e72e12a50d4cf390edee77a1c9abca6f6313ddd36534e47ac6dacf08978", null ]
    ] ],
    [ "PWM_DRV_Init", "group__pwm__driver.html#ga1a1d74230862ca6224fb2286a69f9e75", null ],
    [ "PWM_DRV_Deinit", "group__pwm__driver.html#ga1a2586fb78a71ffaebf159f22a54f231", null ],
    [ "PWM_DRV_SetupPwm", "group__pwm__driver.html#ga11e45fd13c20af3dd4a8923cab6dd4ba", null ],
    [ "PWM_DRV_UpdatePwmSignal", "group__pwm__driver.html#ga866d91538827c871556e725d5de94d4b", null ],
    [ "PWM_DRV_SetTriggerCmd", "group__pwm__driver.html#ga4ca7aa594b836ba1cd088c5add60edb9", null ],
    [ "PWM_DRV_SetTriggerVal", "group__pwm__driver.html#ga6693fefc5c6a7170d1043f75df53fff9", null ],
    [ "PWM_DRV_SetupFault", "group__pwm__driver.html#ga62183e85b3fd98253421d1733cc5559d", null ],
    [ "PWM_DRV_CounterStart", "group__pwm__driver.html#ga1c203c4456d092f0239ed078df085dcc", null ],
    [ "PWM_DRV_CounterStop", "group__pwm__driver.html#ga622e0a0707dd094df8371ca446d2b072", null ],
    [ "PWM_DRV_SetExternalClkFreq", "group__pwm__driver.html#ga77bf6fc02c1b931c639765dfac5bcc30", null ],
    [ "g_pwmBase", "group__pwm__driver.html#ga915ef3b006e3bb275904165021dab135", null ],
    [ "g_pwmCmpIrqId", "group__pwm__driver.html#ga328076863f8f0934ee12db7f489038d4", null ]
];
