wrh2/sputnik/Vendor Firmware/Kinetis SDK v.1.3.0 API Reference Manual/group__flexio__uart__driver.js

var group__flexio__uart__driver =
[
    [ "flexio_uart_dmastate_t", "group__flexio__uart__driver.html#structflexio__uart__dmastate__t", [
      [ "isTxBusy", "group__flexio__uart__driver.html#a0b95a94c7cf63712cfe23538db27b72c", null ],
      [ "isRxBusy", "group__flexio__uart__driver.html#aad8f9894693d8c3127c4b783208c54a5", null ],
      [ "isTxBlocking", "group__flexio__uart__driver.html#ac911a6de51c93d611de033d52b8695d0", null ],
      [ "isRxBlocking", "group__flexio__uart__driver.html#a472fdf35aefb848847eb339f421b05fa", null ],
      [ "txIrqSync", "group__flexio__uart__driver.html#a1d619424f27a422bc37673e0e3325216", null ],
      [ "rxIrqSync", "group__flexio__uart__driver.html#a2cda41debc3700c267b16f20934d8b4a", null ],
      [ "dmaUartTx", "group__flexio__uart__driver.html#a4547c34fa0e113c274ef498fcb1540b0", null ],
      [ "dmaUartRx", "group__flexio__uart__driver.html#ab62ed167e91aadb6f4169686d2d0cbfb", null ]
    ] ],
    [ "flexio_uartdma_userconfig_t", "group__flexio__uart__driver.html#structflexio__uartdma__userconfig__t", [
      [ "baudRate", "group__flexio__uart__driver.html#a22dbfeeadbf3d23ae1c3be1386746763", null ],
      [ "bitCountPerChar", "group__flexio__uart__driver.html#a8c9f5e6b05bda80b2fb624a90507bf2e", null ],
      [ "uartMode", "group__flexio__uart__driver.html#a468aab8fb5bf197ba7686b676d6b254b", null ],
      [ "txConfig", "group__flexio__uart__driver.html#aeda5df060392965a5dc0b7c22817963e", null ],
      [ "rxConfig", "group__flexio__uart__driver.html#a3179673a223ddc43f6276375f4465935", null ]
    ] ],
    [ "flexio_uartedma_userconfig_t", "group__flexio__uart__driver.html#structflexio__uartedma__userconfig__t", null ],
    [ "flexio_uart_edmastate_t", "group__flexio__uart__driver.html#structflexio__uart__edmastate__t", [
      [ "isTxBlocking", "group__flexio__uart__driver.html#a46586a9bd384a3df9451056c573d40ed", null ],
      [ "isRxBlocking", "group__flexio__uart__driver.html#a4d3aa957fdca8b6cb93d1712fc7c1310", null ],
      [ "txIrqSync", "group__flexio__uart__driver.html#a9f591f3ba660bfdbf2d58cbca85677a4", null ],
      [ "rxIrqSync", "group__flexio__uart__driver.html#abe65392c7f67c05326435197adf81960", null ],
      [ "edmaUartTx", "group__flexio__uart__driver.html#a4c5ceacbfc18e3749e2ee228696820df", null ],
      [ "edmaUartRx", "group__flexio__uart__driver.html#a84bf996be5517021fcb42aaf8f665261", null ]
    ] ],
    [ "FLEXIO_UART_DRV_DmaInit", "group__flexio__uart__driver.html#ga5d0551193d4ff9d8a4d48e3cdc4a34f4", null ],
    [ "FLEXIO_UART_DRV_DmaDeinit", "group__flexio__uart__driver.html#ga8708579ba9702a99fe85f045caac732a", null ],
    [ "FLEXIO_UART_DRV_DmaSendDataBlocking", "group__flexio__uart__driver.html#gafbfda157e07ced0d8fb32046a1fd6536", null ],
    [ "FLEXIO_UART_DRV_DmaSendData", "group__flexio__uart__driver.html#gaa2df52ca2dab29927967d6deb89883c1", null ],
    [ "FLEXIO_UART_DRV_DmaGetTransmitStatus", "group__flexio__uart__driver.html#gac93bdfe387676b6e58400eaf7d4edda3", null ],
    [ "FLEXIO_UART_DRV_DmaAbortSendingData", "group__flexio__uart__driver.html#gacd2c9931bd6caa54ccdad571a33a6dc5", null ],
    [ "FLEXIO_UART_DRV_DmaReceiveDataBlocking", "group__flexio__uart__driver.html#ga0acf6c1e8e3fac6e941d417959d4af9b", null ],
    [ "FLEXIO_UART_DRV_DmaReceiveData", "group__flexio__uart__driver.html#ga201685aab6833150fc15dde63156ae50", null ],
    [ "FLEXIO_UART_DRV_DmaGetReceiveStatus", "group__flexio__uart__driver.html#gae5eadc701e0dd177827b79cd4c7149ad", null ],
    [ "FLEXIO_UART_DRV_DmaAbortReceivingData", "group__flexio__uart__driver.html#ga783ceef2efbaa8b214363f4d5077d2f3", null ],
    [ "FLEXIO_UART_DRV_EdmaInit", "group__flexio__uart__driver.html#ga18465ea2edd72b40ce692e03ab4b0b04", null ],
    [ "FLEXIO_UART_DRV_EdmaDeinit", "group__flexio__uart__driver.html#gaff6b6b1cb459b86ba48a61124053a0bf", null ],
    [ "FLEXIO_UART_DRV_EdmaSendDataBlocking", "group__flexio__uart__driver.html#ga9444f700b548a15f9545f9c3cd91c71d", null ],
    [ "FLEXIO_UART_DRV_EdmaSendData", "group__flexio__uart__driver.html#ga8b04a16c91159de11e18a42bf68d178d", null ],
    [ "FLEXIO_UART_DRV_EdmaGetTransmitStatus", "group__flexio__uart__driver.html#ga6f33d0100f2fd67a0d2d06d9c8d4eee0", null ],
    [ "FLEXIO_UART_DRV_EdmaAbortSendingData", "group__flexio__uart__driver.html#gaa5175bbefb66ae395dcc29d34d619a22", null ],
    [ "FLEXIO_UART_DRV_EdmaReceiveDataBlocking", "group__flexio__uart__driver.html#gaa72f4acd1090f172d83ecad7c862b572", null ],
    [ "FLEXIO_UART_DRV_EdmaReceiveData", "group__flexio__uart__driver.html#gae973cd081a3b380ac23156d291cb6ec5", null ],
    [ "FLEXIO_UART_DRV_EdmaGetReceiveStatus", "group__flexio__uart__driver.html#gaa8c6ebea85db1b9d8bb0605b1eb5bdc8", null ],
    [ "FLEXIO_UART_DRV_EdmaAbortReceivingData", "group__flexio__uart__driver.html#ga0f0c5187036a77d01de875988269a258", null ]
];
