wrh2/sputnik/Vendor Firmware/Kinetis SDK v.1.3.0 API Reference Manual/group__gpio__driver.js

var group__gpio__driver =
[
    [ "gpio_input_pin_t", "group__gpio__driver.html#structgpio__input__pin__t", null ],
    [ "gpio_output_pin_t", "group__gpio__driver.html#structgpio__output__pin__t", [
      [ "outputLogic", "group__gpio__driver.html#a8024cb60c6eeaa32fa0d570a67e8d45e", null ]
    ] ],
    [ "gpio_input_pin_user_config_t", "group__gpio__driver.html#structgpio__input__pin__user__config__t", [
      [ "pinName", "group__gpio__driver.html#ab5c2397746c6ec120adb9a3555166ee5", null ],
      [ "config", "group__gpio__driver.html#ab011e274e7ede3bff48d1917b3edf27f", null ]
    ] ],
    [ "gpio_output_pin_user_config_t", "group__gpio__driver.html#structgpio__output__pin__user__config__t", [
      [ "pinName", "group__gpio__driver.html#a52acf3d87b64423a342297710c0a5a8f", null ],
      [ "config", "group__gpio__driver.html#a9fd82561736c3006a94f42c4c5f9cb71", null ]
    ] ],
    [ "GPIO_PINS_OUT_OF_RANGE", "group__gpio__driver.html#ga8fadf6d1f11818123c5881043e5bac33", null ],
    [ "GPIO_PORT_SHIFT", "group__gpio__driver.html#ga4bd03957600cd62f4ba25af9281a223a", null ],
    [ "GPIO_MAKE_PIN", "group__gpio__driver.html#ga55cb7776e46f0c3b2f1875ccd86b92ef", null ],
    [ "GPIO_EXTRACT_PORT", "group__gpio__driver.html#gab9a0c385d01c2bd3abc5a3197dc527a5", null ],
    [ "GPIO_EXTRACT_PIN", "group__gpio__driver.html#ga058c4c49b327b09c72c832e363e3464d", null ],
    [ "GPIO_DRV_Init", "group__gpio__driver.html#ga9534ea8266bc449c534a406a7dc0a7ac", null ],
    [ "GPIO_DRV_InputPinInit", "group__gpio__driver.html#gab5eb8dab16ae7be3d8a2d77f514fe959", null ],
    [ "GPIO_DRV_OutputPinInit", "group__gpio__driver.html#gaeeacdc15820b5689024eed02ed8c94b6", null ],
    [ "GPIO_DRV_GetPinDir", "group__gpio__driver.html#ga6a3d3963b0e96e170dd665c75a2d85b4", null ],
    [ "GPIO_DRV_SetPinDir", "group__gpio__driver.html#ga7a058a7f94fdce91104c63ede1546bc9", null ],
    [ "GPIO_DRV_WritePinOutput", "group__gpio__driver.html#ga83e07292f50ab5afe9a1b81f64678ac8", null ],
    [ "GPIO_DRV_SetPinOutput", "group__gpio__driver.html#gae56e29dc05c29f53e2961b4a3af39b3a", null ],
    [ "GPIO_DRV_ClearPinOutput", "group__gpio__driver.html#ga135e6b616e1e5f5f4d11536dc0471301", null ],
    [ "GPIO_DRV_TogglePinOutput", "group__gpio__driver.html#ga2acd89462efb8418341fe8337081414d", null ],
    [ "GPIO_DRV_ReadPinInput", "group__gpio__driver.html#ga92f2f72d3de59489976009b1629223f2", null ],
    [ "GPIO_DRV_IsPinIntPending", "group__gpio__driver.html#ga68adc8a76570f1adf6018b6bd1800fc0", null ],
    [ "GPIO_DRV_ClearPinIntFlag", "group__gpio__driver.html#ga1747d6c587b11739eb4146d62ca71fa2", null ],
    [ "g_gpioBase", "group__gpio__driver.html#ga6e6139b3705f8067d2964cbf73851092", null ],
    [ "g_portBase", "group__gpio__driver.html#ga72de1c6ffe9640f9d520866ba8633dd6", null ]
];
