wrh2/sputnik/Vendor Firmware/Kinetis SDK v.1.3.0 API Reference Manual/group__pwm__hal.js

var group__pwm__hal =
[
    [ "pwm_module_setup_t", "group__pwm__hal.html#structpwm__module__setup__t", [
      [ "cntrInitSel", "group__pwm__hal.html#a3da1959e99fa9f77d6bd823f3ac3e086", null ],
      [ "clkSrc", "group__pwm__hal.html#afc224d8d0856ea75e9b763b885bd3eca", null ],
      [ "prescale", "group__pwm__hal.html#a3c9a827e26be3476efe262e1d61d91e3", null ],
      [ "chnlPairOper", "group__pwm__hal.html#a295b12e6899325b1406099d628afa224", null ],
      [ "reloadLogic", "group__pwm__hal.html#a5d0ffe47e93799ef99821dabc79b5733", null ],
      [ "reloadFreq", "group__pwm__hal.html#a44c84a25472d35b73cbf977c505a13bb", null ],
      [ "forceTrig", "group__pwm__hal.html#a5148c1c21966302d768af784751d90eb", null ]
    ] ],
    [ "pwm_fault_setup_t", "group__pwm__hal.html#structpwm__fault__setup__t", [
      [ "automaticClearing", "group__pwm__hal.html#a43f6deac6b274d127f125d3dda7a3cd0", null ],
      [ "faultLevel", "group__pwm__hal.html#ad7e6d783b8e6e455ab04d83550444fb0", null ],
      [ "useFaultFilter", "group__pwm__hal.html#aa0b3f47288b39eb5f9d706d609478ab3", null ],
      [ "recMode", "group__pwm__hal.html#a81651a8d07504847c08bd9dc94694a05", null ]
    ] ],
    [ "pwm_capture_setup_t", "group__pwm__hal.html#structpwm__capture__setup__t", [
      [ "captureInputSel", "group__pwm__hal.html#a5adb9c4cfbff05c9df10d1d003bb42d7", null ],
      [ "edgeCompareVal", "group__pwm__hal.html#a13add871895491151b5afa30ead992f7", null ],
      [ "edge0", "group__pwm__hal.html#a18c42d72bf37d640a0efaf642bd86e22", null ],
      [ "edge1", "group__pwm__hal.html#adfaa1af226405a9cadb2d124c7a8dbc1", null ],
      [ "oneShotCapture", "group__pwm__hal.html#a372c6ae66fc3c6fbdc77ca0b3f8151a6", null ]
    ] ],
    [ "pwm_module_t", "group__pwm__hal.html#ga070c130931a957a3268f00645664e471", [
      [ "kFlexPwmModule0", "group__pwm__hal.html#gga070c130931a957a3268f00645664e471a32b6b5a776d5d0bc59b528dce9f4ad40", null ],
      [ "kFlexPwmModule1", "group__pwm__hal.html#gga070c130931a957a3268f00645664e471a7e111db770afef8abbe0bb85d9b17be4", null ],
      [ "kFlexPwmModule2", "group__pwm__hal.html#gga070c130931a957a3268f00645664e471a2183d2572b97e5c80034e38ecf4be844", null ],
      [ "kFlexPwmModule3", "group__pwm__hal.html#gga070c130931a957a3268f00645664e471aa87b86e6b55efc40b7008ea579e3450a", null ]
    ] ],
    [ "pwm_module_signal_t", "group__pwm__hal.html#ga72476b342fe9d79d45ab5f72bbd8f9ac", null ],
    [ "pwm_val_regs_t", "group__pwm__hal.html#ga2b04fe35947b2e0e0aee38a2ec8a7941", [
      [ "kFlexPwmVAL0", "group__pwm__hal.html#gga2b04fe35947b2e0e0aee38a2ec8a7941ad5227f3af8490ca79ee1fb10569a7f97", null ],
      [ "kFlexPwmVAL1", "group__pwm__hal.html#gga2b04fe35947b2e0e0aee38a2ec8a7941a4c11b3116882a1afb1be72a36a4cb569", null ],
      [ "kFlexPwmVAL2", "group__pwm__hal.html#gga2b04fe35947b2e0e0aee38a2ec8a7941abeb62a7a633741b781feac378c28329a", null ],
      [ "kFlexPwmVAL3", "group__pwm__hal.html#gga2b04fe35947b2e0e0aee38a2ec8a7941a73af89deedb153a1081341e687a744e8", null ],
      [ "kFlexPwmVAL4", "group__pwm__hal.html#gga2b04fe35947b2e0e0aee38a2ec8a7941acdde2ca90d1bca316239576cc99f375b", null ],
      [ "kFlexPwmVAL5", "group__pwm__hal.html#gga2b04fe35947b2e0e0aee38a2ec8a7941ab53442b13d7e7cff9e1692d11f91b282", null ]
    ] ],
    [ "pwm_status_t", "group__pwm__hal.html#ga4d42a1b957d0ee97d31883db86f9286f", [
      [ "kStatusPwmSuccess", "group__pwm__hal.html#gga4d42a1b957d0ee97d31883db86f9286fad14e4213f346328d16a7268b4edc8dc7", null ],
      [ "kStatusPwmError", "group__pwm__hal.html#gga4d42a1b957d0ee97d31883db86f9286fa53b2e26486baa3ba9013ef9331162a2a", null ],
      [ "kStatusPwmInvalidArgument", "group__pwm__hal.html#gga4d42a1b957d0ee97d31883db86f9286fa9328332a6cf875896c099f7f3357a37f", null ]
    ] ],
    [ "pwm_clock_src_t", "group__pwm__hal.html#ga3845aa46c7902e1e931b61d463e685ff", [
      [ "kClkSrcPwmIPBusClk", "group__pwm__hal.html#gga3845aa46c7902e1e931b61d463e685ffad8e4d15b8ee1eb8ea79ab0e873ff0624", null ],
      [ "kClkSrcPwmExtClk", "group__pwm__hal.html#gga3845aa46c7902e1e931b61d463e685ffa7bbf58f4ddcb8f0361487e2fae574d79", null ],
      [ "kClkSrcPwm0Clk", "group__pwm__hal.html#gga3845aa46c7902e1e931b61d463e685ffa4782ceb7048ad5a63a0fe89ecce4a5b0", null ]
    ] ],
    [ "pwm_clock_ps_t", "group__pwm__hal.html#ga1f97453676e34d7967af352f7ec676d4", [
      [ "kPwmDividedBy1", "group__pwm__hal.html#gga1f97453676e34d7967af352f7ec676d4abbff72c59adbd2cb03f4c23b77b7d5a6", null ],
      [ "kPwmDividedBy2", "group__pwm__hal.html#gga1f97453676e34d7967af352f7ec676d4a6cf496eb04f81ce04c178fc0de1cd62a", null ],
      [ "kPwmDividedBy4", "group__pwm__hal.html#gga1f97453676e34d7967af352f7ec676d4ae16dbf1db70031319d7c36c53e41ed47", null ],
      [ "kPwmDividedBy8", "group__pwm__hal.html#gga1f97453676e34d7967af352f7ec676d4ad00a960c243ad82598667f7e43fa4bc3", null ],
      [ "kPwmDividedBy16", "group__pwm__hal.html#gga1f97453676e34d7967af352f7ec676d4a3f39a01e53c604c61c86f8e8dd0ed15c", null ],
      [ "kPwmDividedBy32", "group__pwm__hal.html#gga1f97453676e34d7967af352f7ec676d4af03fa4bf66d5c0650ae070115c7f2da5", null ],
      [ "kPwmDividedBy64", "group__pwm__hal.html#gga1f97453676e34d7967af352f7ec676d4a1dbafd2377fd3846de9ef041198b09ef", null ],
      [ "kPwmDividedBy128", "group__pwm__hal.html#gga1f97453676e34d7967af352f7ec676d4a8046c60dded6f119911135eee878c15a", null ]
    ] ],
    [ "pwm_force_output_trigger_t", "group__pwm__hal.html#ga199c9464fb869977d72535e508628966", [
      [ "kForceOutputLocalForce", "group__pwm__hal.html#gga199c9464fb869977d72535e508628966a81e047213911409a4c021fb100a439a8", null ],
      [ "kForceOutputMasterForce", "group__pwm__hal.html#gga199c9464fb869977d72535e508628966afc6527146013514947178c9fb6f281c2", null ],
      [ "kForceOutputLocalReload", "group__pwm__hal.html#gga199c9464fb869977d72535e508628966a303423b729ae76a351faa29acbb552bc", null ],
      [ "kForceOutputMasterReload", "group__pwm__hal.html#gga199c9464fb869977d72535e508628966ae9355996ce8524a4594ee5044dd9c4b8", null ],
      [ "kForceOutputLocalSync", "group__pwm__hal.html#gga199c9464fb869977d72535e508628966a41e3be3b251a841b284b9442db854044", null ],
      [ "kForceOutputMasterSync", "group__pwm__hal.html#gga199c9464fb869977d72535e508628966a541b0a6d4bb76ef3a8dc8ab7c5766d6f", null ],
      [ "kForceOutputExternalForce", "group__pwm__hal.html#gga199c9464fb869977d72535e508628966afeb4a83c6854ac924c5b4bb77bf42fd9", null ],
      [ "kForceOutputExternalSync", "group__pwm__hal.html#gga199c9464fb869977d72535e508628966a1f8eaf6767cbc3d8639d76d2ee09d31b", null ]
    ] ],
    [ "pwm_init_src_t", "group__pwm__hal.html#ga71fad63bc65cc3e620ba657de9004c3a", [
      [ "kInitSrcLocalSync", "group__pwm__hal.html#gga71fad63bc65cc3e620ba657de9004c3aa439eac97bb3f5b1befc54bc183de3fb7", null ],
      [ "kInitSrcMasterReload", "group__pwm__hal.html#gga71fad63bc65cc3e620ba657de9004c3aa02b674a45c5d0565cb82376cb6e9fa39", null ],
      [ "kInitSrcMasterSync", "group__pwm__hal.html#gga71fad63bc65cc3e620ba657de9004c3aa87c6bc9648e714ead10a63c4c14564ac", null ],
      [ "kInitSrcExtSync", "group__pwm__hal.html#gga71fad63bc65cc3e620ba657de9004c3aa3d0e24c4bddc635b8fbf06657c2919a8", null ]
    ] ],
    [ "pwm_load_frequency_t", "group__pwm__hal.html#ga636ca143685fed2cb715c8e74b8e7d91", [
      [ "kPwmLoadEvery1Oportunity", "group__pwm__hal.html#gga636ca143685fed2cb715c8e74b8e7d91ad7b0eef6504edec184a1740aa86cca48", null ],
      [ "kPwmLoadEvery2Oportunity", "group__pwm__hal.html#gga636ca143685fed2cb715c8e74b8e7d91a034f75cf5242262c2491009c81f31d9b", null ],
      [ "kPwmLoadEvery3Oportunity", "group__pwm__hal.html#gga636ca143685fed2cb715c8e74b8e7d91a661138d7eb04cdda52b0f04ab70fab73", null ],
      [ "kPwmLoadEvery4Oportunity", "group__pwm__hal.html#gga636ca143685fed2cb715c8e74b8e7d91a9f1b564eade896ca38f9109c6f86422a", null ],
      [ "kPwmLoadEvery5Oportunity", "group__pwm__hal.html#gga636ca143685fed2cb715c8e74b8e7d91a8652d62fec0acea9c59874c8ec345a24", null ],
      [ "kPwmLoadEvery6Oportunity", "group__pwm__hal.html#gga636ca143685fed2cb715c8e74b8e7d91a3ee4a25e7ddcad3c49f75e80831cc7ba", null ],
      [ "kPwmLoadEvery7Oportunity", "group__pwm__hal.html#gga636ca143685fed2cb715c8e74b8e7d91acb18bab0aea561b9c21034c81b037bbd", null ],
      [ "kPwmLoadEvery8Oportunity", "group__pwm__hal.html#gga636ca143685fed2cb715c8e74b8e7d91ad1bbf806071c8e3d9e3402f30309a261", null ],
      [ "kPwmLoadEvery9Oportunity", "group__pwm__hal.html#gga636ca143685fed2cb715c8e74b8e7d91a3ca444ca58ecc6d34abd6ecfdf4f44b1", null ],
      [ "kPwmLoadEvery10Oportunity", "group__pwm__hal.html#gga636ca143685fed2cb715c8e74b8e7d91a3861739a9ea24dce88024da67c64dae9", null ],
      [ "kPwmLoadEvery11Oportunity", "group__pwm__hal.html#gga636ca143685fed2cb715c8e74b8e7d91aa352ac28fa9077f64ac9b493fde32d3b", null ],
      [ "kPwmLoadEvery12Oportunity", "group__pwm__hal.html#gga636ca143685fed2cb715c8e74b8e7d91ad9f987067c40744396ef2460ee659100", null ],
      [ "kPwmLoadEvery13Oportunity", "group__pwm__hal.html#gga636ca143685fed2cb715c8e74b8e7d91ae04eb39d8e16a29339f0bd02f54a6dd2", null ],
      [ "kPwmLoadEvery14Oportunity", "group__pwm__hal.html#gga636ca143685fed2cb715c8e74b8e7d91a33ba85545af6eff0476f4cf4a59782c8", null ],
      [ "kPwmLoadEvery15Oportunity", "group__pwm__hal.html#gga636ca143685fed2cb715c8e74b8e7d91a4348b4f162c4a8cf99f0db24ea3555f3", null ],
      [ "kPwmLoadEvery16Oportunity", "group__pwm__hal.html#gga636ca143685fed2cb715c8e74b8e7d91a69488fa41e4d6ff1c029d73c5bc88e70", null ]
    ] ],
    [ "pwm_fault_input_t", "group__pwm__hal.html#ga5b339bfb308c5c3b4a1f3170a8653926", [
      [ "kFlexPwmFault0", "group__pwm__hal.html#gga5b339bfb308c5c3b4a1f3170a8653926a659730b5b0e121ba3b3eb558884f6d53", null ],
      [ "kFlexPwmFault1", "group__pwm__hal.html#gga5b339bfb308c5c3b4a1f3170a8653926ad69270baa43d9750d8a80b8a5aee79b9", null ],
      [ "kFlexPwmFault2", "group__pwm__hal.html#gga5b339bfb308c5c3b4a1f3170a8653926aa64229272490dc6bf0a03fa633af71d8", null ],
      [ "kFlexPwmFault3", "group__pwm__hal.html#gga5b339bfb308c5c3b4a1f3170a8653926a9eece79d3ac221d6d41f885e33b1d31b", null ]
    ] ],
    [ "pwm_capture_edge_t", "group__pwm__hal.html#gaedd7b5d94a532f360672e0c15a9a0fca", [
      [ "kCaptureDisable", "group__pwm__hal.html#ggaedd7b5d94a532f360672e0c15a9a0fcaa8f0202a12f978406440338e58121c350", null ],
      [ "kCaptureFallingEdges", "group__pwm__hal.html#ggaedd7b5d94a532f360672e0c15a9a0fcaaa1cc20bc888020fa11510a5d75eb00a7", null ],
      [ "kCaptureRisingEdges", "group__pwm__hal.html#ggaedd7b5d94a532f360672e0c15a9a0fcaab62e9f982b89decfb07fa8d2662ad3d9", null ],
      [ "kCaptureAnyEdges", "group__pwm__hal.html#ggaedd7b5d94a532f360672e0c15a9a0fcaa3e37833b82b98e7f7689a145391b8e9c", null ]
    ] ],
    [ "pwm_force_signal_t", "group__pwm__hal.html#ga6429e832c8b26915f2448463ab396cd1", [
      [ "kFlexPwmUsePwm", "group__pwm__hal.html#gga6429e832c8b26915f2448463ab396cd1a9af8ab48c16ee7f8362614fc53c70935", null ],
      [ "kFlexPwmInvertedPwm", "group__pwm__hal.html#gga6429e832c8b26915f2448463ab396cd1a0c2a96ce121fb48941e7e4d14211c121", null ],
      [ "kFlexPwmSoftwareControl", "group__pwm__hal.html#gga6429e832c8b26915f2448463ab396cd1a4cb119af4dbafcc3346ed9551835cb24", null ],
      [ "kFlexPwmUseExternal", "group__pwm__hal.html#gga6429e832c8b26915f2448463ab396cd1ae7cbae5ebf8334d25bcc7259f94cf9eb", null ]
    ] ],
    [ "pwm_chnl_pair_operation_t", "group__pwm__hal.html#ga74af21116f00e824d05e776ddccb0802", [
      [ "kFlexPwmIndependent", "group__pwm__hal.html#gga74af21116f00e824d05e776ddccb0802a926cfa525b8e285d2a150c49be2445d2", null ],
      [ "kFlexPwmComplementaryPwmA", "group__pwm__hal.html#gga74af21116f00e824d05e776ddccb0802a0e92fe80267c2ac71b45d17f9fc1f454", null ],
      [ "kFlexPwmComplementaryPwmB", "group__pwm__hal.html#gga74af21116f00e824d05e776ddccb0802a4ec3eca9c319e6efdc88eca937403dd9", null ]
    ] ],
    [ "pwm_reg_reload_t", "group__pwm__hal.html#gaa640c9fc5faf5d1648890f1a00248618", [
      [ "kFlexPwmReloadImmediate", "group__pwm__hal.html#ggaa640c9fc5faf5d1648890f1a00248618a267d9831be124d9a8191cd035de537c4", null ],
      [ "kFlexPwmReloadPwmHalfCycle", "group__pwm__hal.html#ggaa640c9fc5faf5d1648890f1a00248618a9b3ddc2de381ee9a3de933453f19af83", null ],
      [ "kFlexPwmReloadPwmFullCycle", "group__pwm__hal.html#ggaa640c9fc5faf5d1648890f1a00248618aab3b2e953378c672b750acd5afa07c24", null ],
      [ "kFlexPwmReloadPwmHalfAndFullCycle", "group__pwm__hal.html#ggaa640c9fc5faf5d1648890f1a00248618ac670efe5c17e15f61e9450871d2a7773", null ]
    ] ],
    [ "pwm_fault_recovery_mode_t", "group__pwm__hal.html#ga10bb013dcfa77ce708fe90ac290894e7", [
      [ "kFlexPwmNoRecovery", "group__pwm__hal.html#gga10bb013dcfa77ce708fe90ac290894e7a40882d029e59208d3443a3d120a5d24c", null ],
      [ "kFlexPwmRecoverHalfCycle", "group__pwm__hal.html#gga10bb013dcfa77ce708fe90ac290894e7a1de966d4f0d585fd4876e53796651e04", null ],
      [ "kFlexPwmRecoverFullCycle", "group__pwm__hal.html#gga10bb013dcfa77ce708fe90ac290894e7a6786c4ed1d4eeb231f2cc63a93368865", null ],
      [ "kFlexPwmRecoverHalfAndFullCycle", "group__pwm__hal.html#gga10bb013dcfa77ce708fe90ac290894e7a416abd4a5471f01b243a3c632c461eea", null ]
    ] ],
    [ "pwm_event_t", "group__pwm__hal.html#gaaaaf7eba4cef06e22ee8d5d89e7deb3e", [
      [ "kFlexPwmCompareVal0Event", "group__pwm__hal.html#ggaaaaf7eba4cef06e22ee8d5d89e7deb3ea142d4e49f26aa2242be00d85f315254b", null ],
      [ "kFlexPwmCompareVal1Event", "group__pwm__hal.html#ggaaaaf7eba4cef06e22ee8d5d89e7deb3ea56b26abcaf055ed56386265544fd17be", null ],
      [ "kFlexPwmCompareVal2Event", "group__pwm__hal.html#ggaaaaf7eba4cef06e22ee8d5d89e7deb3eaedfbe26b29110e0abb4bce32da9208f4", null ],
      [ "kFlexPwmCompareVal3Event", "group__pwm__hal.html#ggaaaaf7eba4cef06e22ee8d5d89e7deb3ea5ae0999f8580c2f6af161b36aea9265d", null ],
      [ "kFlexPwmCompareVal4Event", "group__pwm__hal.html#ggaaaaf7eba4cef06e22ee8d5d89e7deb3eaa6df7e90df7d402842b17c8fad0beae7", null ],
      [ "kFlexPwmCompareVal5Event", "group__pwm__hal.html#ggaaaaf7eba4cef06e22ee8d5d89e7deb3eac008f6019e3223e005350a03f678b35b", null ],
      [ "kFlexPwmCaptureX0Event", "group__pwm__hal.html#ggaaaaf7eba4cef06e22ee8d5d89e7deb3ea2dea9eeea82b1f1045e2e4f132b603cd", null ],
      [ "kFlexPwmCaptureX1Event", "group__pwm__hal.html#ggaaaaf7eba4cef06e22ee8d5d89e7deb3ea475fd680cea1330dbb15fbb74dc240a5", null ],
      [ "kFlexPwmCaptureB0Event", "group__pwm__hal.html#ggaaaaf7eba4cef06e22ee8d5d89e7deb3ea34f4b2281467d4645e5333561380f183", null ],
      [ "kFlexPwmCaptureB1Event", "group__pwm__hal.html#ggaaaaf7eba4cef06e22ee8d5d89e7deb3eaa3c1a2d7daf51d30fbda3d5bdb168286", null ],
      [ "kFlexPwmCaptureA0Event", "group__pwm__hal.html#ggaaaaf7eba4cef06e22ee8d5d89e7deb3eae4bcf1ff500600b2ce629c99846e8645", null ],
      [ "kFlexPwmCaptureA1Event", "group__pwm__hal.html#ggaaaaf7eba4cef06e22ee8d5d89e7deb3eafb1569cb09e9fbb76a4a55c1f9f8b1fb", null ],
      [ "kFlexPwmReloadEvent", "group__pwm__hal.html#ggaaaaf7eba4cef06e22ee8d5d89e7deb3ea10178b72201fe9b13863dfe1621fd5bf", null ],
      [ "kFlexPwmReloadErrorEvent", "group__pwm__hal.html#ggaaaaf7eba4cef06e22ee8d5d89e7deb3ea34eb474d6cb3a3ef2ee4884f8a28701d", null ],
      [ "kFlexPwmFault0Event", "group__pwm__hal.html#ggaaaaf7eba4cef06e22ee8d5d89e7deb3ea9a62f952d20b56e12d998e92785009ec", null ],
      [ "kFlexPwmFault1Event", "group__pwm__hal.html#ggaaaaf7eba4cef06e22ee8d5d89e7deb3ea5b11832b18a71e62cd329b8dfdf88eca", null ],
      [ "kFlexPwmFault2Event", "group__pwm__hal.html#ggaaaaf7eba4cef06e22ee8d5d89e7deb3ea58c8f7c5bd51593eb044d41b31587581", null ],
      [ "kFlexPwmFault3Event", "group__pwm__hal.html#ggaaaaf7eba4cef06e22ee8d5d89e7deb3ea51ae7aee538a6a7ea2c463207a24b641", null ]
    ] ],
    [ "PWM_HAL_Init", "group__pwm__hal.html#ga85ffef79be5d17d064b7e27ea6b37cb5", null ],
    [ "PWM_HAL_SetupPwmSubModule", "group__pwm__hal.html#ga957bb29dcf145881a9f246e74f028bb7", null ],
    [ "PWM_HAL_SetupFaults", "group__pwm__hal.html#ga9face6cee3981395a574ab32da38a4c4", null ],
    [ "PWM_HAL_SetupCapture", "group__pwm__hal.html#ga04194c042c61d0704310b45aa1ce8fe4", null ],
    [ "PWM_HAL_GetCaptureValReg", "group__pwm__hal.html#gac13146e446a6c2f1112c51e3803c797e", null ],
    [ "PWM_HAL_SetValReg", "group__pwm__hal.html#gada96798fe23907d01bd7695be59d157d", null ],
    [ "PWM_HAL_SetupForceSignal", "group__pwm__hal.html#ga316fa2deb7508722bab3890a8e4fad93", null ],
    [ "PWM_HAL_EnableInterrupts", "group__pwm__hal.html#ga9fa320799f9813a824e3a135f7db298a", null ],
    [ "PWM_HAL_DisableInterrupts", "group__pwm__hal.html#ga5203bbb3b001a5cc4b282f3fbf0ddd18", null ],
    [ "PWM_HAL_ClearStatus", "group__pwm__hal.html#ga8f2da905836254425cb57926ed5ffa1f", null ],
    [ "PWM_HAL_GetCounter", "group__pwm__hal.html#ga12611266a46a3060290969bfad72f9e0", null ],
    [ "PWM_HAL_SetCounterInitVal", "group__pwm__hal.html#gac67f0382777b75f15fa5048da8035054", null ],
    [ "PWM_HAL_SetForceCmd", "group__pwm__hal.html#ga35babc065a43b3e978f756b883666cab", null ],
    [ "PWM_HAL_SetOutputPolarityPwmBCmd", "group__pwm__hal.html#ga419c2cb2725610c8e9b4d2c5fd22ca9a", null ],
    [ "PWM_HAL_SetOutputPolarityPwmACmd", "group__pwm__hal.html#ga610632646ef8c8169ad67df30c5ffe10", null ],
    [ "PWM_HAL_SetOutputPolarityPwmXCmd", "group__pwm__hal.html#gacbeea223ce584c6eb56c7bf6bb23f66e", null ],
    [ "PWM_HAL_SetOutputTriggerCmd", "group__pwm__hal.html#ga30cca3d643cc63e5fff0fe7d95008fd6", null ],
    [ "PWM_HAL_SetPwmAFaultInputCmd", "group__pwm__hal.html#gaaa8e19126385c04f81e3968a75fac5fd", null ],
    [ "PWM_HAL_SetPwmBFaultInputCmd", "group__pwm__hal.html#ga713cedf2ee14000e80cc0e6c761199c5", null ],
    [ "PWM_HAL_SetPwmXFaultInputCmd", "group__pwm__hal.html#gad28a6bfaeabb3caa686e743f1fabca52", null ],
    [ "PWM_HAL_SetOutputPwmXCmd", "group__pwm__hal.html#ga4ec5c326d2d7d94728d6491809a98532", null ],
    [ "PWM_HAL_SetOutputPwmBCmd", "group__pwm__hal.html#gaef9cfe89a7fc99b2b9888f8fb4a8e967", null ],
    [ "PWM_HAL_SetOutputPwmACmd", "group__pwm__hal.html#ga2f2a9079a5649afbec344cde5db2c241", null ],
    [ "PWM_HAL_SetSwCtrlOutCmd", "group__pwm__hal.html#ga350a847be1ffa9f9125b064f46c727e9", null ],
    [ "PWM_HAL_SetPwmRunCmd", "group__pwm__hal.html#ga073661a067dcaf1a1aa1e6f7ea0577f9", null ]
];
