wrh2/sputnik/Vendor Firmware/Kinetis SDK v.1.3.0 API Reference Manual/group__ftm__hal.js

var group__ftm__hal =
[
    [ "ftm_edge_mode_t", "group__ftm__hal.html#unionftm__edge__mode__t", null ],
    [ "ftm_pwm_param_t", "group__ftm__hal.html#structftm__pwm__param__t", [
      [ "mode", "group__ftm__hal.html#aea02c3304a7ca5504272bed01238480a", null ],
      [ "edgeMode", "group__ftm__hal.html#a5a61645b2d68f8a809811d6afb577411", null ],
      [ "uFrequencyHZ", "group__ftm__hal.html#ac1c4af91ea0116f2f97fd04110bc025f", null ],
      [ "uDutyCyclePercent", "group__ftm__hal.html#ac06100f532dfed108e909794237adabd", null ],
      [ "uFirstEdgeDelayPercent", "group__ftm__hal.html#acf6f8590ce2c4f827936d1c107e4306e", null ]
    ] ],
    [ "ftm_dual_edge_capture_param_t", "group__ftm__hal.html#structftm__dual__edge__capture__param__t", [
      [ "mode", "group__ftm__hal.html#a050cfae880e244bdbb6a44dfbc1a9120", null ],
      [ "currChanEdgeMode", "group__ftm__hal.html#affbb53357f250ed1a2c348c5a46f04c2", null ],
      [ "nextChanEdgeMode", "group__ftm__hal.html#ab9c8ce754e9c2190157859182630a8e9", null ]
    ] ],
    [ "ftm_phase_params_t", "group__ftm__hal.html#structftm__phase__params__t", [
      [ "kFtmPhaseInputFilter", "group__ftm__hal.html#adac91b0778d0bd9af5c2043625143608", null ],
      [ "kFtmPhaseFilterVal", "group__ftm__hal.html#ae14a9fca295cf0649e496e6ac94345f7", null ],
      [ "kFtmPhasePolarity", "group__ftm__hal.html#a588d0cd5c8c2fe6031db4fdec05a424a", null ]
    ] ],
    [ "CHAN0_IDX", "group__ftm__hal.html#ga6b1f67caed873efe35030b681323f97f", null ],
    [ "CHAN1_IDX", "group__ftm__hal.html#ga110bde5ae5677b41aa41903af4ced032", null ],
    [ "CHAN2_IDX", "group__ftm__hal.html#ga46ede0a91dead1a3a7e396f09d640b31", null ],
    [ "CHAN3_IDX", "group__ftm__hal.html#gac90378bae7a0de9588ac755ece9d5577", null ],
    [ "CHAN4_IDX", "group__ftm__hal.html#ga11b082e38fabc3af4beabf874081fe5e", null ],
    [ "CHAN5_IDX", "group__ftm__hal.html#gaec622aa2fd7e5a27cc3858941ee8ef48", null ],
    [ "CHAN6_IDX", "group__ftm__hal.html#ga6560c48d1ecd247bbfde7656dbdfd389", null ],
    [ "CHAN7_IDX", "group__ftm__hal.html#gafed8d6cc8f9ad3e78df06d8d81efcae4", null ],
    [ "ftm_clock_source_t", "group__ftm__hal.html#gaa06173bb43f7666ce1f39dd68fe74edc", null ],
    [ "ftm_counting_mode_t", "group__ftm__hal.html#ga3c8f5689f791c627abd7b4910b7e2a9d", null ],
    [ "ftm_clock_ps_t", "group__ftm__hal.html#ga3c3e411f333eecedb94d9e865d321bcf", null ],
    [ "ftm_deadtime_ps_t", "group__ftm__hal.html#ga4ba0e8a6ee01ac1ead5aac305a183cbd", null ],
    [ "ftm_config_mode_t", "group__ftm__hal.html#gad807c3c9d7e0ccde621aef85081ea8a8", null ],
    [ "ftm_input_capture_edge_mode_t", "group__ftm__hal.html#ga1498c18edd4263db86066e8f980b0807", null ],
    [ "ftm_output_compare_edge_mode_t", "group__ftm__hal.html#ga39563277d30cd5f3fb59ce5359562191", null ],
    [ "ftm_pwm_edge_mode_t", "group__ftm__hal.html#gac9d6c8d65d9bba3c96c817c06a104f71", null ],
    [ "ftm_dual_capture_edge_mode_t", "group__ftm__hal.html#ga557d011049a9a871e2c7917ca48916d0", null ],
    [ "ftm_quad_decode_mode_t", "group__ftm__hal.html#ga6ed10d63677b23c68008aff9eda1c01b", null ],
    [ "ftm_quad_phase_polarity_t", "group__ftm__hal.html#gaf34dee060844d8ba45920f1d8e7f7eb3", [
      [ "kFtmQuadPhaseNormal", "group__ftm__hal.html#ggaf34dee060844d8ba45920f1d8e7f7eb3ad1e0090dd5f3b1d9094678259a8db712", null ],
      [ "kFtmQuadPhaseInvert", "group__ftm__hal.html#ggaf34dee060844d8ba45920f1d8e7f7eb3ad54342ca593c4884fadcacff07a69657", null ]
    ] ],
    [ "ftm_sync_method_t", "group__ftm__hal.html#ga6d2b70af7197a8b9584901b7f4daa2af", null ],
    [ "ftm_bdm_mode_t", "group__ftm__hal.html#gad56a34539f559be0d845c2f50b30961a", [
      [ "kFtmBdmMode_00", "group__ftm__hal.html#ggad56a34539f559be0d845c2f50b30961aaa4afd302a1fece25402526704432d3fe", null ],
      [ "kFtmBdmMode_01", "group__ftm__hal.html#ggad56a34539f559be0d845c2f50b30961aacac2ccd14b9e0eec20af7285e1ecb197", null ],
      [ "kFtmBdmMode_10", "group__ftm__hal.html#ggad56a34539f559be0d845c2f50b30961aae749fc0e4349432bbcba1065e9e97acf", null ],
      [ "kFtmBdmMode_11", "group__ftm__hal.html#ggad56a34539f559be0d845c2f50b30961aa1db8aa4108f3f206115b72204592d659", null ]
    ] ],
    [ "ftm_status_t", "group__ftm__hal.html#ga884a1a2aee43733710b1e03935e1806d", [
      [ "kStatusFtmSuccess", "group__ftm__hal.html#gga884a1a2aee43733710b1e03935e1806daf5c3da06642e59c57a99de34caf69722", null ],
      [ "kStatusFtmError", "group__ftm__hal.html#gga884a1a2aee43733710b1e03935e1806da82114ed041e5f601bbcee11c8ec028b9", null ]
    ] ],
    [ "FTM_HAL_SetClockSource", "group__ftm__hal.html#ga66a44495e370fa8e31ae973307d33d1b", null ],
    [ "FTM_HAL_GetClockSource", "group__ftm__hal.html#gadc3ef51a7e0f43195bc41b71629de756", null ],
    [ "FTM_HAL_SetClockPs", "group__ftm__hal.html#ga3c0976a502e6f98cd66c7dbcf1d25f5b", null ],
    [ "FTM_HAL_GetClockPs", "group__ftm__hal.html#gac777c9acc0f9bd8fd7b5f8c66accb414", null ],
    [ "FTM_HAL_EnableTimerOverflowInt", "group__ftm__hal.html#gac3803af0491872bc6bc4219d5dfdd36f", null ],
    [ "FTM_HAL_DisableTimerOverflowInt", "group__ftm__hal.html#gadf8eaabd0eb99b6ced14db0becfae5a3", null ],
    [ "FTM_HAL_IsOverflowIntEnabled", "group__ftm__hal.html#gac5485f44376b863dae8fd8b4d89e4ac9", null ],
    [ "FTM_HAL_ClearTimerOverflow", "group__ftm__hal.html#ga8afb00f13f64d6041ec66163da18f200", null ],
    [ "FTM_HAL_HasTimerOverflowed", "group__ftm__hal.html#ga38e50244b8c6173269e240300913dda6", null ],
    [ "FTM_HAL_SetCpwms", "group__ftm__hal.html#ga700adbbe109c48a0128ef32790637e6d", null ],
    [ "FTM_HAL_SetCounter", "group__ftm__hal.html#gaf202016025abd7b7bc6133874b1324be", null ],
    [ "FTM_HAL_GetCounter", "group__ftm__hal.html#ga57de31222766082c082aec4b8661dc48", null ],
    [ "FTM_HAL_SetMod", "group__ftm__hal.html#ga00d4576440532289a01de5e01c8b5404", null ],
    [ "FTM_HAL_GetMod", "group__ftm__hal.html#ga1b22ea197b5b09428ecfe449f85f4fc8", null ],
    [ "FTM_HAL_SetCounterInitVal", "group__ftm__hal.html#gae70d77c90b7ac5b090e78f9c135ca099", null ],
    [ "FTM_HAL_GetCounterInitVal", "group__ftm__hal.html#ga141d6944cdda97f5a78cda4d885670d6", null ],
    [ "FTM_HAL_SetChnMSnBAMode", "group__ftm__hal.html#ga8f920581b6f21068349dc828bba17717", null ],
    [ "FTM_HAL_SetChnEdgeLevel", "group__ftm__hal.html#ga7119bc3ae28c6be749aa4b42e9e24d7b", null ],
    [ "FTM_HAL_GetChnMode", "group__ftm__hal.html#ga9dfdca04f48e5b0a06aff80c969c7269", null ],
    [ "FTM_HAL_GetChnEdgeLevel", "group__ftm__hal.html#gaec5b853c79a48d3b5b523486605a9622", null ],
    [ "FTM_HAL_SetChnDmaCmd", "group__ftm__hal.html#ga49527d14f4b12262faa06ada86e7cf55", null ],
    [ "FTM_HAL_IsChnDma", "group__ftm__hal.html#ga56b902c5254454d53a716aee9a8d17ba", null ],
    [ "FTM_HAL_IsChnIntEnabled", "group__ftm__hal.html#ga9f40e34a2ae55d48afeea0920335c9ed", null ],
    [ "FTM_HAL_EnableChnInt", "group__ftm__hal.html#ga7e8c0a7ee38776917e94775df208adac", null ],
    [ "FTM_HAL_DisableChnInt", "group__ftm__hal.html#gaac41ed39b59eb61f53780b5062a7f3b9", null ],
    [ "FTM_HAL_HasChnEventOccurred", "group__ftm__hal.html#ga12d590d663fe0d13fdb0c5de45183816", null ],
    [ "FTM_HAL_ClearChnEventFlag", "group__ftm__hal.html#gaa5f09f317ea6db9195712df6112dbbd3", null ],
    [ "FTM_HAL_SetChnCountVal", "group__ftm__hal.html#gaff12386572df66140850c005d5f069a1", null ],
    [ "FTM_HAL_GetChnCountVal", "group__ftm__hal.html#ga244ff9221173db1b56ce1e17be51587b", null ],
    [ "FTM_HAL_GetChnEventStatus", "group__ftm__hal.html#ga9c58f7ed5e9add763cb13a5509522da2", null ],
    [ "FTM_HAL_ClearChnEventStatus", "group__ftm__hal.html#ga53679aebdd97d66faf27e1efa64269af", null ],
    [ "FTM_HAL_SetOutmaskReg", "group__ftm__hal.html#ga629f693abd2f5f19e11a4144127bd911", null ],
    [ "FTM_HAL_SetChnOutputMask", "group__ftm__hal.html#ga030d39192ed6a25dbc4512f70944fc00", null ],
    [ "FTM_HAL_SetChnOutputInitStateCmd", "group__ftm__hal.html#ga21285671411a48189fe87aced97614dc", null ],
    [ "FTM_HAL_SetChnOutputPolarityCmd", "group__ftm__hal.html#ga0ff3dcddc63d92a4e6abcb780be503c1", null ],
    [ "FTM_HAL_SetChnFaultInputPolarityCmd", "group__ftm__hal.html#ga92a1f30568aeeaed60fdfc40634ced2f", null ],
    [ "FTM_HAL_EnableFaultInt", "group__ftm__hal.html#ga3f82c676483d3bdd6a428b2b8bb9ff96", null ],
    [ "FTM_HAL_DisableFaultInt", "group__ftm__hal.html#gabd95138871cef3eb148a7c165e8c0653", null ],
    [ "FTM_HAL_SetFaultControlMode", "group__ftm__hal.html#gaefd4b676543b6917159ecb33e78d042a", null ],
    [ "FTM_HAL_SetCaptureTestCmd", "group__ftm__hal.html#ga9ae20f80ed6c6da93d6283f3cb496eeb", null ],
    [ "FTM_HAL_SetWriteProtectionCmd", "group__ftm__hal.html#ga5f98734b44025c6c0fb74b4c9a32ce69", null ],
    [ "FTM_HAL_Enable", "group__ftm__hal.html#gacadf27a899254d39a8f230a829a51ca4", null ],
    [ "FTM_HAL_SetInitChnOutputCmd", "group__ftm__hal.html#ga0d56f0b515f210e14265958b862ba853", null ],
    [ "FTM_HAL_SetPwmSyncMode", "group__ftm__hal.html#ga19023542cbd4aeef3b8a18982d1882aa", null ],
    [ "FTM_HAL_SetSoftwareTriggerCmd", "group__ftm__hal.html#ga31ae804475802dfd50516ac437fdc1ba", null ],
    [ "FTM_HAL_SetHardwareSyncTriggerSrc", "group__ftm__hal.html#ga969630079bd300cc45eaa6288790dcd2", null ],
    [ "FTM_HAL_SetOutmaskPwmSyncModeCmd", "group__ftm__hal.html#gaa778368d5aefea4347963fea5839453a", null ],
    [ "FTM_HAL_SetCountReinitSyncCmd", "group__ftm__hal.html#gab916677423464566a3364299f15ddd44", null ],
    [ "FTM_HAL_SetMaxLoadingCmd", "group__ftm__hal.html#ga7b9f44f31374a9d950223d0505e51d07", null ],
    [ "FTM_HAL_SetMinLoadingCmd", "group__ftm__hal.html#gad3c70054331ef98cb6dc4d8106abdb24", null ],
    [ "FTM_HAL_GetChnPairIndex", "group__ftm__hal.html#ga16b264b492e4eaa1c5de876eb8400529", null ],
    [ "FTM_HAL_SetDualChnFaultCmd", "group__ftm__hal.html#ga1b48885b6a3e6519585c9e7c5006fd4b", null ],
    [ "FTM_HAL_SetDualChnPwmSyncCmd", "group__ftm__hal.html#gaee7014abe4956d253e1a9affab66d767", null ],
    [ "FTM_HAL_SetDualChnDeadtimeCmd", "group__ftm__hal.html#gae94fe398729b6ca0c63d40c0ecde1003", null ],
    [ "FTM_HAL_SetDualChnDecapCmd", "group__ftm__hal.html#ga340c8200c2ba1676326ede3cf40bdf6e", null ],
    [ "FTM_HAL_SetDualEdgeCaptureCmd", "group__ftm__hal.html#ga11718eacdf7959133a8fcfcc4313c9d3", null ],
    [ "FTM_HAL_SetDualChnCompCmd", "group__ftm__hal.html#ga1da969e4ea8a9fa4ad6f4f6e6fd483e6", null ],
    [ "FTM_HAL_SetDualChnCombineCmd", "group__ftm__hal.html#ga3246f25c9f0d10e4f47da2d8e0ea9930", null ],
    [ "FTM_HAL_SetDeadtimePrescale", "group__ftm__hal.html#ga80472c00ffaeee6c852f1dc6d5c6f6ef", null ],
    [ "FTM_HAL_SetDeadtimeCount", "group__ftm__hal.html#ga98b326be0caa2550aa6b62221a0ee73f", null ],
    [ "FTM_HAL_SetInitTriggerCmd", "group__ftm__hal.html#gaf3ddb35d85c422c5ac6c717213bfc116", null ],
    [ "FTM_HAL_SetChnTriggerCmd", "group__ftm__hal.html#ga24afadb1c8785fa77eeaaeeff9686bad", null ],
    [ "FTM_HAL_IsChnTriggerGenerated", "group__ftm__hal.html#ga9e23a662f4d12fbf9e8dbe786d5b5bc2", null ],
    [ "FTM_HAL_GetDetectedFaultInput", "group__ftm__hal.html#ga198c65ec5bc1572bdcaf09e28f970d07", null ],
    [ "FTM_HAL_IsWriteProtectionEnabled", "group__ftm__hal.html#gab2a75e8dcf6bd2a0e879136bc2689983", null ],
    [ "FTM_HAL_SetQuadDecoderCmd", "group__ftm__hal.html#ga3b46ecc73ed63a3a0a02814b3b7531b2", null ],
    [ "FTM_HAL_SetQuadPhaseAFilterCmd", "group__ftm__hal.html#ga7c8271be320a4f3bd57f310fe857365c", null ],
    [ "FTM_HAL_SetQuadPhaseBFilterCmd", "group__ftm__hal.html#ga2662176cc0030a22710c63c550e2e278", null ],
    [ "FTM_HAL_SetQuadPhaseAPolarity", "group__ftm__hal.html#ga4bd6442feb4df376f461da7ebf268a69", null ],
    [ "FTM_HAL_SetQuadPhaseBPolarity", "group__ftm__hal.html#ga08511b4d6d25b0d43fc89b5122e825dd", null ],
    [ "FTM_HAL_SetQuadMode", "group__ftm__hal.html#ga722f01598b6ed80a158d0c5a2a995cb3", null ],
    [ "FTM_HAL_GetQuadDir", "group__ftm__hal.html#gad746a673feaf9868e1896a8b9999031f", null ],
    [ "FTM_HAL_GetQuadTimerOverflowDir", "group__ftm__hal.html#ga0cfb22b0012b93508063d72139e83845", null ],
    [ "FTM_HAL_SetChnInputCaptureFilter", "group__ftm__hal.html#ga327604da0dcf131e64c4410b653151f1", null ],
    [ "FTM_HAL_SetFaultInputFilterVal", "group__ftm__hal.html#ga46a995a37da4a1f44c40cf2ed4e5457c", null ],
    [ "FTM_HAL_SetFaultInputFilterCmd", "group__ftm__hal.html#ga6d32b9df0d14aa73c6331222c96123db", null ],
    [ "FTM_HAL_SetFaultInputCmd", "group__ftm__hal.html#gaceb63d7c20966696017eba157f1840e0", null ],
    [ "FTM_HAL_SetDualChnInvertCmd", "group__ftm__hal.html#ga5d9d81d3af5ed1bcc210404746aa220f", null ],
    [ "FTM_HAL_SetInvctrlReg", "group__ftm__hal.html#gac4b6e44a5901c1e1c53dcbfe945ea75a", null ],
    [ "FTM_HAL_SetChnSoftwareCtrlCmd", "group__ftm__hal.html#gacd198c74f934831bc55679e1dae40e83", null ],
    [ "FTM_HAL_SetChnSoftwareCtrlVal", "group__ftm__hal.html#ga475aaf88ee0a7534fe489da3e9141d7a", null ],
    [ "FTM_HAL_SetPwmLoadCmd", "group__ftm__hal.html#gacaebea74b783f1368c1ae02742072b02", null ],
    [ "FTM_HAL_SetPwmLoadChnSelCmd", "group__ftm__hal.html#ga4def7a4dae21110ef26daad69ad70585", null ],
    [ "FTM_HAL_SetGlobalTimeBaseOutputCmd", "group__ftm__hal.html#ga69cf81b0d2be48b1bc075fc78b29f410", null ],
    [ "FTM_HAL_SetGlobalTimeBaseCmd", "group__ftm__hal.html#ga1de12f670ecdba9b073926c4287dcf1c", null ],
    [ "FTM_HAL_SetBdmMode", "group__ftm__hal.html#ga1849cd875d875e1ed13e8119d0ab21e7", null ],
    [ "FTM_HAL_SetTofFreq", "group__ftm__hal.html#ga0a5061948fffdde42de54831c7bdd962", null ],
    [ "FTM_HAL_SetSyncMode", "group__ftm__hal.html#ga037f2eb20259b07f2125f1bc0eae4841", null ],
    [ "FTM_HAL_SetSwoctrlHardwareSyncModeCmd", "group__ftm__hal.html#gaecceec4db1e444aafbaaa662c915e104", null ],
    [ "FTM_HAL_SetInvctrlHardwareSyncModeCmd", "group__ftm__hal.html#ga744314f8884181f65b1f265b4fadf5cf", null ],
    [ "FTM_HAL_SetOutmaskHardwareSyncModeCmd", "group__ftm__hal.html#gab2b1e55aa144f585a3421eb1ed5026e8", null ],
    [ "FTM_HAL_SetModCntinCvHardwareSyncModeCmd", "group__ftm__hal.html#ga3b3d8151f229e7053e6fbc409550070b", null ],
    [ "FTM_HAL_SetCounterHardwareSyncModeCmd", "group__ftm__hal.html#ga8c869522076e56a341df0fd460d6c844", null ],
    [ "FTM_HAL_SetSwoctrlSoftwareSyncModeCmd", "group__ftm__hal.html#ga6c87c77a92b18b48b81bbee5763fbc08", null ],
    [ "FTM_HAL_SetInvctrlSoftwareSyncModeCmd", "group__ftm__hal.html#ga67869faa725c71caf4b56ceba9b44385", null ],
    [ "FTM_HAL_SetOutmaskSoftwareSyncModeCmd", "group__ftm__hal.html#gaad75075da44e270f59470b1ed070236b", null ],
    [ "FTM_HAL_SetModCntinCvSoftwareSyncModeCmd", "group__ftm__hal.html#gac3688dc6d34ce05a54e2ed21ba20622f", null ],
    [ "FTM_HAL_SetCounterSoftwareSyncModeCmd", "group__ftm__hal.html#ga12d02b9536dab7bd5202fea1fbb4d08e", null ],
    [ "FTM_HAL_SetPwmSyncModeCmd", "group__ftm__hal.html#ga1eef3c8f39c5c96e8896c02509195733", null ],
    [ "FTM_HAL_SetSwoctrlPwmSyncModeCmd", "group__ftm__hal.html#gaefc5f47d0028a7c5b576cec0dbc120cf", null ],
    [ "FTM_HAL_SetInvctrlPwmSyncModeCmd", "group__ftm__hal.html#ga15b49929a9032a70b4283c0dafe756f0", null ],
    [ "FTM_HAL_SetCntinPwmSyncModeCmd", "group__ftm__hal.html#gabbf693d96fc97b977f89a00e567d99b0", null ],
    [ "FTM_HAL_Reset", "group__ftm__hal.html#ga0e29274858cacf349fa22a90c138e134", null ],
    [ "FTM_HAL_Init", "group__ftm__hal.html#ga9a4165a64b77a71e4cf169b5b4ca979f", null ],
    [ "FTM_HAL_EnablePwmMode", "group__ftm__hal.html#gaa7484a4b80264e75f644999619f6afaf", null ],
    [ "FTM_HAL_DisablePwmMode", "group__ftm__hal.html#gae67deff948e4d885f026202211792a1f", null ]
];
