wrh2/sputnik/Vendor Firmware/Kinetis SDK v.1.3.0 API Reference Manual/group__edma__hal.js

var group__edma__hal =
[
    [ "edma_transfer_config_t", "group__edma__hal.html#structedma__transfer__config__t", [
      [ "srcAddr", "group__edma__hal.html#aa1ff988241ea8238e8793f4236c55553", null ],
      [ "destAddr", "group__edma__hal.html#a70e10c552f356c4d2935e9f308a3317a", null ],
      [ "srcTransferSize", "group__edma__hal.html#ae5f96bb8d80f6f7a6c8a687e8a42a77e", null ],
      [ "destTransferSize", "group__edma__hal.html#afe8f8da3ed5f7c4079c818ef0197a4d7", null ],
      [ "srcOffset", "group__edma__hal.html#a25b479621f01e4e2cf7fcdab62d6e266", null ],
      [ "srcLastAddrAdjust", "group__edma__hal.html#a087cb3e95c1ffd79912e702206a22d90", null ],
      [ "destLastAddrAdjust", "group__edma__hal.html#ae03c3766ebfdae9f27874ede86dbe537", null ],
      [ "srcModulo", "group__edma__hal.html#a420da93107f7b1352a007eb7878effae", null ],
      [ "destModulo", "group__edma__hal.html#ac90c456add2a1190bb8806b504c61dd0", null ],
      [ "minorLoopCount", "group__edma__hal.html#a0352c5a1f0032ab7b160f636fb97f6a7", null ],
      [ "majorLoopCount", "group__edma__hal.html#a6e0ed32e1620b33dfce5a07e3eb6b9b5", null ]
    ] ],
    [ "edma_minorloop_offset_config_t", "group__edma__hal.html#structedma__minorloop__offset__config__t", [
      [ "enableSrcMinorloop", "group__edma__hal.html#a4bd72c1a536e10bd5519b04ae4f83e38", null ],
      [ "enableDestMinorloop", "group__edma__hal.html#ac36a906b54be61c75bc5c947fc17e2a2", null ],
      [ "offset", "group__edma__hal.html#ac702b97f2dc500aacacf4e7914e23dd8", null ]
    ] ],
    [ "edma_error_status_all_t", "group__edma__hal.html#structedma__error__status__all__t", [
      [ "errorChannel", "group__edma__hal.html#aba1acb9edf5ea2350f003426e2b1da98", null ],
      [ "destinationBusError", "group__edma__hal.html#a8283cf0023e38d708ef11cad55677ea3", null ],
      [ "sourceBusError", "group__edma__hal.html#a3a43366ea9116654a7a78c0e19520336", null ],
      [ "scatterOrGatherConfigurationError", "group__edma__hal.html#a22f29c93ca985beff99d6a4df0578f59", null ],
      [ "nbyteOrCiterConfigurationError", "group__edma__hal.html#ab2c259fc4f63ee352f840633ab8a26c7", null ],
      [ "destinationOffsetError", "group__edma__hal.html#a3e6449cbdff5005bbcd33575aae0e9da", null ],
      [ "destinationAddressError", "group__edma__hal.html#a08733e935ca6b1a61d5dbf017919432a", null ],
      [ "sourceOffsetError", "group__edma__hal.html#a27a8dedde4acb882e5cdffeeda8112e4", null ],
      [ "sourceAddressError", "group__edma__hal.html#a71099657c8db89f168da7015feefb5cb", null ],
      [ "channelPriorityError", "group__edma__hal.html#ab32edcf62fdeeba8ee100159eb302e4b", null ],
      [ "transferCancelledError", "group__edma__hal.html#a3b110c40bd735e5669b85d1db45eee8a", null ],
      [ "orOfAllError", "group__edma__hal.html#a968099004312c10b9ae84d77e2c29984", null ]
    ] ],
    [ "edma_software_tcd_t", "group__edma__hal.html#structedma__software__tcd__t", null ],
    [ "edma_status_t", "group__edma__hal.html#gab6319bfbfaebd007f7871ae5be5eebe4", [
      [ "kStatus_EDMA_InvalidArgument", "group__edma__hal.html#ggab6319bfbfaebd007f7871ae5be5eebe4a194322022386e0fdc50fcb7437c0742b", null ],
      [ "kStatus_EDMA_Fail", "group__edma__hal.html#ggab6319bfbfaebd007f7871ae5be5eebe4ab6b48173a20862eba0b60d25911253d2", null ]
    ] ],
    [ "edma_channel_arbitration_t", "group__edma__hal.html#ga1ae691e6c3e3af80d079f01dc4e0d9d9", [
      [ "kEDMAChnArbitrationFixedPriority", "group__edma__hal.html#gga1ae691e6c3e3af80d079f01dc4e0d9d9a6d292e4c74991982da967eef92aeceb5", null ],
      [ "kEDMAChnArbitrationRoundrobin", "group__edma__hal.html#gga1ae691e6c3e3af80d079f01dc4e0d9d9acb97728581b710ac5b456c4f52e4b9ad", null ]
    ] ],
    [ "edma_channel_priority_t", "group__edma__hal.html#ga6fd8085ea112952ca60275d66aa73946", null ],
    [ "edma_modulo_t", "group__edma__hal.html#ga13ac7c9e76c11d3dce06f8976d9e4dd7", null ],
    [ "edma_transfer_size_t", "group__edma__hal.html#gafeb85400b3b87188983f5d62e9e26cb6", null ],
    [ "edma_channel_indicator_t", "group__edma__hal.html#gad48323c254991e68d8aa87ea51029bdd", [
      [ "kEDMAChannel0", "group__edma__hal.html#ggad48323c254991e68d8aa87ea51029bddafe39d576f30be63283d3e6e848f7bba5", null ]
    ] ],
    [ "edma_bandwidth_config_t", "group__edma__hal.html#ga24742d66725095a97085d309c59a0e9d", [
      [ "kEDMABandwidthStallNone", "group__edma__hal.html#gga24742d66725095a97085d309c59a0e9daf46c62a5d66009cc2044686ee929fe9d", null ],
      [ "kEDMABandwidthStall4Cycle", "group__edma__hal.html#gga24742d66725095a97085d309c59a0e9da4d4d354f9915accd4ab274cef525e7fe", null ],
      [ "kEDMABandwidthStall8Cycle", "group__edma__hal.html#gga24742d66725095a97085d309c59a0e9dace96f42ec8428f1df985acfdc5452fe8", null ]
    ] ],
    [ "EDMA_HAL_Init", "group__edma__hal.html#gacc8c0881074ecc92b6e2deea92288a97", null ],
    [ "EDMA_HAL_CancelTransfer", "group__edma__hal.html#ga7865c396ce7fc641b217f1eacaac0364", null ],
    [ "EDMA_HAL_ErrorCancelTransfer", "group__edma__hal.html#gafb27989af5a3b8a27b7050f86a10dcad", null ],
    [ "EDMA_HAL_SetHaltCmd", "group__edma__hal.html#gac93e4fea1b0caec0ee81488b6efbc510", null ],
    [ "EDMA_HAL_SetHaltOnErrorCmd", "group__edma__hal.html#ga4ed8e60c9d3637d910761aee7c39ab2c", null ],
    [ "EDMA_HAL_SetDebugCmd", "group__edma__hal.html#ga77c7ffafdf0c2ef01619e7d38949a72e", null ],
    [ "EDMA_HAL_SetChannelPreemptMode", "group__edma__hal.html#gac90cee027a954fc990ad146e5d7792ca", null ],
    [ "EDMA_HAL_SetChannelPriority", "group__edma__hal.html#gab18b88484ffe2c1aa254593b548c26ed", null ],
    [ "EDMA_HAL_SetChannelArbitrationMode", "group__edma__hal.html#ga9aefae59b37fe89deb2c8895e17cbf79", null ],
    [ "EDMA_HAL_SetMinorLoopMappingCmd", "group__edma__hal.html#ga43e9e85ad4ee054613be59c438ea1d57", null ],
    [ "EDMA_HAL_SetContinuousLinkCmd", "group__edma__hal.html#ga798e277b31e0b8b82b1f96b9f84f7482", null ],
    [ "EDMA_HAL_GetErrorStatus", "group__edma__hal.html#ga5419d8bdd836f1cb3859c9e429e6326a", null ],
    [ "EDMA_HAL_SetErrorIntCmd", "group__edma__hal.html#ga13f6e5039e0ba4ed061bb511946309a7", null ],
    [ "EDMA_HAL_GetErrorIntStatusFlag", "group__edma__hal.html#ga72e11a8f988b95535c7796c409ba59e5", null ],
    [ "EDMA_HAL_ClearErrorIntStatusFlag", "group__edma__hal.html#gaa8d21b48c0c4e78e7c0edcac3611a170", null ],
    [ "EDMA_HAL_SetDmaRequestCmd", "group__edma__hal.html#ga4cac35fa93b8314344dd2370cf66bf15", null ],
    [ "EDMA_HAL_GetDmaRequestStatusFlag", "group__edma__hal.html#ga7d34e5e48623cef58338beb8f0c39d44", null ],
    [ "EDMA_HAL_ClearDoneStatusFlag", "group__edma__hal.html#ga30f70e825a7f0bce19bafa338c0817ea", null ],
    [ "EDMA_HAL_TriggerChannelStart", "group__edma__hal.html#gaa7fc655ea87e96ee3ca6c175b41b2c58", null ],
    [ "EDMA_HAL_GetIntStatusFlag", "group__edma__hal.html#gada9dd8ccd2b9602dc2cd246e3c1b563a", null ],
    [ "EDMA_HAL_ClearIntStatusFlag", "group__edma__hal.html#ga26309d8eded10fd87f1787199f2cb2cc", null ],
    [ "EDMA_HAL_HTCDClearReg", "group__edma__hal.html#ga121f3975f8105097bf10c2269d95786f", null ],
    [ "EDMA_HAL_HTCDSetSrcAddr", "group__edma__hal.html#gac65e68c14f4d1a0d067f76a63e577515", null ],
    [ "EDMA_HAL_HTCDSetSrcOffset", "group__edma__hal.html#ga3a70d0dcd6231eff551ca377f3aa6389", null ],
    [ "EDMA_HAL_HTCDSetAttribute", "group__edma__hal.html#gac9300d88ac984044f1c149d5c85de25c", null ],
    [ "EDMA_HAL_HTCDSetNbytes", "group__edma__hal.html#ga37efc218788fd610924b8c53ea268918", null ],
    [ "EDMA_HAL_HTCDGetNbytes", "group__edma__hal.html#ga3590b7b53019e0e55b4e6724768bb02a", null ],
    [ "EDMA_HAL_HTCDSetMinorLoopOffset", "group__edma__hal.html#ga0c7bc8583b9d582d0c15f3e684c88028", null ],
    [ "EDMA_HAL_HTCDSetSrcLastAdjust", "group__edma__hal.html#gac3ba3db4bc7194f2b75e7b1f4fd9905f", null ],
    [ "EDMA_HAL_HTCDSetDestAddr", "group__edma__hal.html#gacf976c51c2ca188087c89a81ebd7397b", null ],
    [ "EDMA_HAL_HTCDSetDestOffset", "group__edma__hal.html#ga893c02e4c136dd3a6a2fc7f264a6019c", null ],
    [ "EDMA_HAL_HTCDSetDestLastAdjust", "group__edma__hal.html#gacab2c927fc8d65e250a07822dc0ce964", null ],
    [ "EDMA_HAL_HTCDSetScatterGatherLink", "group__edma__hal.html#gae471dbb737e56595e768afc3520b2e90", null ],
    [ "EDMA_HAL_HTCDSetBandwidth", "group__edma__hal.html#ga313619251ce242044c84c9e35a035e33", null ],
    [ "EDMA_HAL_HTCDSetChannelMajorLink", "group__edma__hal.html#ga0f34f967043a4e2259e1ebf6d990e2f0", null ],
    [ "EDMA_HAL_HTCDSetScatterGatherCmd", "group__edma__hal.html#gac4e44ca1c503b792f8865f6c829da5b6", null ],
    [ "EDMA_HAL_HTCDSetDisableDmaRequestAfterTCDDoneCmd", "group__edma__hal.html#ga70f46f3c571f09e37bb14771bab8f503", null ],
    [ "EDMA_HAL_HTCDSetHalfCompleteIntCmd", "group__edma__hal.html#ga1dff6fd2323d0cf97bf2140aad72f0f9", null ],
    [ "EDMA_HAL_HTCDSetIntCmd", "group__edma__hal.html#gafe3d53a3a64fb60f9a8e63faf1323fdd", null ],
    [ "EDMA_HAL_HTCDTriggerChannelStart", "group__edma__hal.html#ga2a40973a2a38e725b59a2b2ce8e84216", null ],
    [ "EDMA_HAL_HTCDGetChannelActiveStatus", "group__edma__hal.html#gab7aabe41bb658121972b64f3de28276a", null ],
    [ "EDMA_HAL_HTCDSetChannelMinorLink", "group__edma__hal.html#ga0eaaaab41c743e47bf669d11e325fed2", null ],
    [ "EDMA_HAL_HTCDSetMajorCount", "group__edma__hal.html#ga6027d906817cbf52b00f65cc2e7caaa6", null ],
    [ "EDMA_HAL_HTCDGetFinishedBytes", "group__edma__hal.html#gac83a31af6f374bf89874f15394d13bd9", null ],
    [ "EDMA_HAL_HTCDGetUnfinishedBytes", "group__edma__hal.html#ga79c1d889ab11be6e310ca20b483420f6", null ],
    [ "EDMA_HAL_HTCDGetDoneStatusFlag", "group__edma__hal.html#ga2d708c9e86f555011cceca050dfb316f", null ],
    [ "EDMA_HAL_HTCDGetBeginMajorCount", "group__edma__hal.html#ga8381502e69eec8a6ff741bffb0d20b4f", null ],
    [ "EDMA_HAL_HTCDGetCurrentMajorCount", "group__edma__hal.html#ga5ec2cee71670225e0405402ea91a374b", null ],
    [ "EDMA_HAL_STCDSetSrcAddr", "group__edma__hal.html#gafa113de52b215b8ed3287ae16bc8c150", null ],
    [ "EDMA_HAL_STCDSetSrcOffset", "group__edma__hal.html#ga68e70e63032ba4d613a181219fb8df9e", null ],
    [ "EDMA_HAL_STCDSetAttribute", "group__edma__hal.html#ga1d27f98767e3b9255305f3d414a88439", null ],
    [ "EDMA_HAL_STCDSetNbytes", "group__edma__hal.html#ga4b6309cb6c7d14068dd6d66d16e48798", null ],
    [ "EDMA_HAL_STCDSetMinorLoopOffset", "group__edma__hal.html#ga657ea2d2b6faeb519088ff9e244ab41c", null ],
    [ "EDMA_HAL_STCDSetSrcLastAdjust", "group__edma__hal.html#gae04ae217d9da212ded44438d47245ef2", null ],
    [ "EDMA_HAL_STCDSetDestAddr", "group__edma__hal.html#ga3be28bf81baaa565f8b5ad5d49210258", null ],
    [ "EDMA_HAL_STCDSetDestOffset", "group__edma__hal.html#ga4d0191b0fbbd9f4a843b4cce2686898f", null ],
    [ "EDMA_HAL_STCDSetDestLastAdjust", "group__edma__hal.html#gad8b1555f01876a1303055c0a08f7459d", null ],
    [ "EDMA_HAL_STCDSetScatterGatherLink", "group__edma__hal.html#gaf1d05ba8a7dd8a5b8a54d97753bad20d", null ],
    [ "EDMA_HAL_STCDSetBandwidth", "group__edma__hal.html#gac5ac92366d54a9e308f6a5c3ccb4319b", null ],
    [ "EDMA_HAL_STCDSetChannelMajorLink", "group__edma__hal.html#gaf0f74c3c6d93f4586e2656e081703458", null ],
    [ "EDMA_HAL_STCDSetScatterGatherCmd", "group__edma__hal.html#gac93863dc9f144d69906bc30478a16a28", null ],
    [ "EDMA_HAL_STCDSetDisableDmaRequestAfterTCDDoneCmd", "group__edma__hal.html#gac959b4b9b82cb343a88fcaba54a833d5", null ],
    [ "EDMA_HAL_STCDSetHalfCompleteIntCmd", "group__edma__hal.html#gab57f148ba8f76a596363246129c7cf81", null ],
    [ "EDMA_HAL_STCDSetIntCmd", "group__edma__hal.html#ga04ee4b9623b60ba86b9feec816a01402", null ],
    [ "EDMA_HAL_STCDTriggerChannelStart", "group__edma__hal.html#ga888e2b239909b25f4ac5f35cccf517d8", null ],
    [ "EDMA_HAL_STCDSetChannelMinorLink", "group__edma__hal.html#ga36f154763e1214f033074a068ac9e242", null ],
    [ "EDMA_HAL_STCDSetMajorCount", "group__edma__hal.html#ga8f60631b84702a9acbd980d1946175a2", null ],
    [ "EDMA_HAL_PushSTCDToHTCD", "group__edma__hal.html#ga58bb1ae343a4829de9f9bbc6cac3ac2a", null ],
    [ "EDMA_HAL_STCDSetBasicTransfer", "group__edma__hal.html#ga48d4a3d31956d44e8f31fbbf9baffb67", null ]
];
