wrh2/sputnik/Vendor Firmware/Kinetis SDK v.1.3.0 API Reference Manual/group__emvsim__hal.js

var group__emvsim__hal =
[
    [ "emvsim_module_param_t", "group__emvsim__hal.html#ga027072a42f2dd2a35da1df62319549a3", [
      [ "kEmvsimParamVersion", "group__emvsim__hal.html#gga027072a42f2dd2a35da1df62319549a3a172e30f9cc5af5709f93cd8fdac66278", null ],
      [ "kEmvsimParamTxFifoSize", "group__emvsim__hal.html#gga027072a42f2dd2a35da1df62319549a3a09bd0282f70beb155f132aa29934607a", null ],
      [ "kEmvsimParamRxFifoSize", "group__emvsim__hal.html#gga027072a42f2dd2a35da1df62319549a3a1477a4a90ad04a78ee478d73f3aa9a9a", null ]
    ] ],
    [ "emvsim_gpc_clock_select_t", "group__emvsim__hal.html#gacd1edab274da411c5a531be31a5bcff2", [
      [ "kEmvsimGPCClockDisable", "group__emvsim__hal.html#ggacd1edab274da411c5a531be31a5bcff2aed4d3f7fddb7390eb1c5fe5207612751", null ],
      [ "kEmvsimGPCCardClock", "group__emvsim__hal.html#ggacd1edab274da411c5a531be31a5bcff2aea102366523db2605bebd3d2c1f0ddfc", null ],
      [ "kEmvsimGPCRxClock", "group__emvsim__hal.html#ggacd1edab274da411c5a531be31a5bcff2a64c4ec3bee31acdeed7071cccca70718", null ],
      [ "kEmvsimGPCTxClock", "group__emvsim__hal.html#ggacd1edab274da411c5a531be31a5bcff2affc3bb1b0ad7a6d4705389f6692ff56d", null ]
    ] ],
    [ "emvsim_crc_flip_control_t", "group__emvsim__hal.html#gafd3f20549749471869608808bc716335", [
      [ "kEmvsimCrcNoFlip", "group__emvsim__hal.html#ggafd3f20549749471869608808bc716335a272286595565024aff1a1909e9851177", null ],
      [ "kEmvsimCrcFlip", "group__emvsim__hal.html#ggafd3f20549749471869608808bc716335a36697accb72b01ab65d6dccc0531de29", null ]
    ] ],
    [ "emvsim_crc_inv_control_t", "group__emvsim__hal.html#ga09f36ea7891cdaaa196ef0d192aaabc9", [
      [ "kEmvsimCrcNoInv", "group__emvsim__hal.html#gga09f36ea7891cdaaa196ef0d192aaabc9ad6ce5194534fd320c457850c31c088d9", null ],
      [ "kEmvsimCrcInv", "group__emvsim__hal.html#gga09f36ea7891cdaaa196ef0d192aaabc9a4b85a8a2ba9a175ec63cfd23b886b70c", null ]
    ] ],
    [ "emvsim_stop_clock_control_t", "group__emvsim__hal.html#ga81aaeb18fcfc8b68250c3ac818072eba", [
      [ "kEmvsimStopDownAllClocks", "group__emvsim__hal.html#gga81aaeb18fcfc8b68250c3ac818072ebaada1e7681392a8f1e37906e9d7190625f", null ],
      [ "kEmvsimStopDownAllButCardClock", "group__emvsim__hal.html#gga81aaeb18fcfc8b68250c3ac818072ebaa3d4f536296079e0ec422227740294cfe", null ]
    ] ],
    [ "emvsim_doze_clock_control_t", "group__emvsim__hal.html#ga0979753f80abd900e84d330a58e1fec1", [
      [ "kEmvsimDozeDownAllClocks", "group__emvsim__hal.html#gga0979753f80abd900e84d330a58e1fec1ace8e671a8a2d68b4ee1f7002fc368d73", null ],
      [ "kEmvsimDozeDownNoClocks", "group__emvsim__hal.html#gga0979753f80abd900e84d330a58e1fec1a5212a45395477ef782f45c5f3d1932e4", null ]
    ] ],
    [ "emvsim_data_convention_t", "group__emvsim__hal.html#gae0dab07b44baf1c22c12c20ed5bab3fc", [
      [ "kEmvsimDirectConvention", "group__emvsim__hal.html#ggae0dab07b44baf1c22c12c20ed5bab3fca0af10b5da546918f840ce08dc9e61abd", null ],
      [ "kEmvsimInverseConvention", "group__emvsim__hal.html#ggae0dab07b44baf1c22c12c20ed5bab3fcaa860a77a9f6f3b20c0d2216e89323d04", null ]
    ] ],
    [ "emvsim_character_mode_t", "group__emvsim__hal.html#ga255002d1ea3f1539b943415d3760a1ec", [
      [ "kEmvsimCharacter12EtuMode", "group__emvsim__hal.html#gga255002d1ea3f1539b943415d3760a1eca01c945e14245f29aedecfdf46da31213", null ],
      [ "kEmvsimCharacter11EtuMode", "group__emvsim__hal.html#gga255002d1ea3f1539b943415d3760a1eca330e4219f321eabdd07f5c1d58e8f156", null ]
    ] ],
    [ "emvsim_control_t", "group__emvsim__hal.html#ga298469a87a8125bda6789824f1def085", [
      [ "kEmvsimCtrlInverseConvention", "group__emvsim__hal.html#gga298469a87a8125bda6789824f1def085a947b463a3a3c64edc8e3b1efdeeae4c6", null ],
      [ "kEmvsimCtrlinitialCharacterMode", "group__emvsim__hal.html#gga298469a87a8125bda6789824f1def085a210afc8141a21f798b8361d482b4a3c7", null ],
      [ "kEmvsimCtrlANACKEnable", "group__emvsim__hal.html#gga298469a87a8125bda6789824f1def085a1374b65d7dcd4e6c4f2b1e31fbdd0050", null ],
      [ "kEmvsimCtrlONACKEnable", "group__emvsim__hal.html#gga298469a87a8125bda6789824f1def085ac8dd94400bb19f3f6a61345ab5e1e250", null ],
      [ "kEmvsimCtrlFlushRx", "group__emvsim__hal.html#gga298469a87a8125bda6789824f1def085ab432ffa2bf3dae8e8f21baae565bd9ac", null ],
      [ "kEmvsimCtrlFlushTx", "group__emvsim__hal.html#gga298469a87a8125bda6789824f1def085ad573a860dc0271cb31baeff1ab9200df", null ],
      [ "kEmvsimCtrlSwRst", "group__emvsim__hal.html#gga298469a87a8125bda6789824f1def085a6cc57a0193995ad1a8a149277d6f138b", null ],
      [ "kEmvsimCtrlKillClocks", "group__emvsim__hal.html#gga298469a87a8125bda6789824f1def085a10334ea39c702f119525d8cc10acbfea", null ],
      [ "kEmvsimCtrlDozeEnable", "group__emvsim__hal.html#gga298469a87a8125bda6789824f1def085a31313196aef41882ed793ce4ac139b0d", null ],
      [ "kEmvsimCtrlStopEnable", "group__emvsim__hal.html#gga298469a87a8125bda6789824f1def085ac52ba9bd005214519db383becd8dd51e", null ],
      [ "kEmvsimCtrlReceiverEnable", "group__emvsim__hal.html#gga298469a87a8125bda6789824f1def085a4e369f8312b5beb08d8d9d147e7a8176", null ],
      [ "kEmvsimCtrlTransmitterEnable", "group__emvsim__hal.html#gga298469a87a8125bda6789824f1def085a921d5502284c6facc8596cc463523694", null ],
      [ "kEmvsimCtrlRcvr11ModeEnable", "group__emvsim__hal.html#gga298469a87a8125bda6789824f1def085a5be62ab1270fb47cd457258c07c3a698", null ],
      [ "kEmvsimCtrlRxDmaEnable", "group__emvsim__hal.html#gga298469a87a8125bda6789824f1def085a6198e3487b13881f09ee05b902a3fbc5", null ],
      [ "kEmvsimCtrlTxDmaEnable", "group__emvsim__hal.html#gga298469a87a8125bda6789824f1def085ae1572e9aa37cc556b4a326de8243e538", null ],
      [ "kEmvsimCtrlInvertCrcOutput", "group__emvsim__hal.html#gga298469a87a8125bda6789824f1def085aefe7aa60b3fbd7ea14f7c9410968f816", null ],
      [ "kEmvsimCtrlFlipCrcOutput", "group__emvsim__hal.html#gga298469a87a8125bda6789824f1def085a37f5bc19c06471fe9c91b8eb816ad16d", null ],
      [ "kEmvsimCtrlFlipCrcInput", "group__emvsim__hal.html#gga298469a87a8125bda6789824f1def085afdd5af1e96167ace00a9b73195144971", null ],
      [ "kEmvsimCtrlCWTEnable", "group__emvsim__hal.html#gga298469a87a8125bda6789824f1def085a59bf4d699fc858b77d6ba90b06262232", null ],
      [ "kEmvsimCtrlLrcEnable", "group__emvsim__hal.html#gga298469a87a8125bda6789824f1def085ab8375bf7f1de6134836602c89350152c", null ],
      [ "kEmvsimCtrlCrcEnable", "group__emvsim__hal.html#gga298469a87a8125bda6789824f1def085aa5ad16bb17263dd3e658d6e8dc055ba4", null ],
      [ "kEmvsimCtrlXmtCrcOrLrcEnable", "group__emvsim__hal.html#gga298469a87a8125bda6789824f1def085a7237bb05ec35b9d438f65d06590ead4e", null ],
      [ "kEmvsimCtrlBWTEnable", "group__emvsim__hal.html#gga298469a87a8125bda6789824f1def085a35e0ac45d12f6c0d3530b034fc58ae90", null ]
    ] ],
    [ "emvsim_interrupt_t", "group__emvsim__hal.html#ga0c5b90d65070da7abe509085231dbae2", [
      [ "kEmvsimIntRxData", "group__emvsim__hal.html#gga0c5b90d65070da7abe509085231dbae2aeaa73d7869712c16c0535465b0385c26", null ],
      [ "kEmvsimIntGPCnt1", "group__emvsim__hal.html#gga0c5b90d65070da7abe509085231dbae2a8330f5e9697cc8e96c1f78311aa73735", null ],
      [ "kEmvsimIntBGTErr", "group__emvsim__hal.html#gga0c5b90d65070da7abe509085231dbae2ae5e2cb6331d4608a2989a8864a8522b4", null ],
      [ "kEmvsimIntBWTErr", "group__emvsim__hal.html#gga0c5b90d65070da7abe509085231dbae2aa8c997425fd9ae683ba78f27d8967927", null ],
      [ "kEmvsimIntRxNackThreshold", "group__emvsim__hal.html#gga0c5b90d65070da7abe509085231dbae2a48e37f3bd48a7345eb2c1d724fbabe7a", null ],
      [ "kEmvsimIntCWTErr", "group__emvsim__hal.html#gga0c5b90d65070da7abe509085231dbae2aa72fea2679b94bbc09dbe1a793b506f1", null ],
      [ "kEmvsimIntGPCnt0", "group__emvsim__hal.html#gga0c5b90d65070da7abe509085231dbae2a9df526df2910f48ba5467fc9e4f2a5aa", null ],
      [ "kEmvsimIntTxDataThreshold", "group__emvsim__hal.html#gga0c5b90d65070da7abe509085231dbae2a5acabc34e15a95f3ea65ad000f74cbf3", null ],
      [ "kEmvsimIntTxFIFOFull", "group__emvsim__hal.html#gga0c5b90d65070da7abe509085231dbae2a3376e3393c7f944ca1def2240b2345ec", null ],
      [ "kEmvsimIntTxNackThresold", "group__emvsim__hal.html#gga0c5b90d65070da7abe509085231dbae2ad3a4f5574a58fece244848ecc24d779b", null ],
      [ "kEmvsimIntTxFIFOEmpty", "group__emvsim__hal.html#gga0c5b90d65070da7abe509085231dbae2a3fffccff2e539b0c7f99101e02a7c41e", null ],
      [ "kEmvsimIntEarlyTxComplete", "group__emvsim__hal.html#gga0c5b90d65070da7abe509085231dbae2a2343134d637c2068bab1c9de34d5ab06", null ],
      [ "kEmvsimIntRxFIFOOverflow", "group__emvsim__hal.html#gga0c5b90d65070da7abe509085231dbae2a79a5817005f8676119b5d0b398c8fdbf", null ],
      [ "kEmvsimIntTxComplete", "group__emvsim__hal.html#gga0c5b90d65070da7abe509085231dbae2aadf330241753965affabb12ceaff5de4", null ],
      [ "kEmvsimIntRxDataThreshold", "group__emvsim__hal.html#gga0c5b90d65070da7abe509085231dbae2adab93ee0c2663e04e1d09b75f9e62d26", null ],
      [ "kEmvsimIntPresenceDetect", "group__emvsim__hal.html#gga0c5b90d65070da7abe509085231dbae2a7375de7a6ee2d152cf156bea6e7338f0", null ]
    ] ],
    [ "emvsim_rx_status_t", "group__emvsim__hal.html#ga7e74ff5f4f542908d5d87207f348452e", [
      [ "kEmvsimFrameErr", "group__emvsim__hal.html#gga7e74ff5f4f542908d5d87207f348452ea478531eb44785eaeb5c61abf2bd4f645", null ],
      [ "kEmvsimParityErr", "group__emvsim__hal.html#gga7e74ff5f4f542908d5d87207f348452ea7b76edf4aafaa6fdf68b027ff5740ca5", null ],
      [ "kEmvsimBGTErr", "group__emvsim__hal.html#gga7e74ff5f4f542908d5d87207f348452ea0cb1aaf99fb6eceebda0ada15c777917", null ],
      [ "kEmvsimBWTErr", "group__emvsim__hal.html#gga7e74ff5f4f542908d5d87207f348452eaf41b9e7a8a0ca542f7f2412307f7dfd4", null ],
      [ "kEmvsimRxNackThresholdErr", "group__emvsim__hal.html#gga7e74ff5f4f542908d5d87207f348452ea652b8d527042a40a9fe0df28aec6084e", null ],
      [ "kEmvsimCWTErr", "group__emvsim__hal.html#gga7e74ff5f4f542908d5d87207f348452ea679f2be53a97ba0a7d385e339f466f0c", null ],
      [ "kEmvsimCRCCheckOk", "group__emvsim__hal.html#gga7e74ff5f4f542908d5d87207f348452ea163612b36e16f8c16b9834ce0d8bd778", null ],
      [ "kEmvsimLRCCheckOk", "group__emvsim__hal.html#gga7e74ff5f4f542908d5d87207f348452eaaeab2b950c2079572481c8e935d3c585", null ],
      [ "kEmvsimRxDataThreshold", "group__emvsim__hal.html#gga7e74ff5f4f542908d5d87207f348452ea325aa67dd40ed44f83d70e2e29d3ab11", null ],
      [ "kEmvsimRxData", "group__emvsim__hal.html#gga7e74ff5f4f542908d5d87207f348452ea97ec05ed1edb80315c4f32d7f218cbdb", null ],
      [ "kEmvsimRxDataOverflow", "group__emvsim__hal.html#gga7e74ff5f4f542908d5d87207f348452eab3ca7f3df850a012e8fc8ce37cb29630", null ],
      [ "kEmvsimRxAllStatus", "group__emvsim__hal.html#gga7e74ff5f4f542908d5d87207f348452ea4c90ed446152ab336070cd921e786cc4", null ]
    ] ],
    [ "emvsim_tx_status_t", "group__emvsim__hal.html#ga9cfa10f80abdb57a203c0463419fd83d", [
      [ "kEmvsimGPCNT1Timeout", "group__emvsim__hal.html#gga9cfa10f80abdb57a203c0463419fd83da4dd52fcf2fffc7c61fa40b381417acff", null ],
      [ "kEmvsimGPCNT0Timeout", "group__emvsim__hal.html#gga9cfa10f80abdb57a203c0463419fd83daeb55b1941efcc522367d37777a80538f", null ],
      [ "kEmvsimTxDataThreshold", "group__emvsim__hal.html#gga9cfa10f80abdb57a203c0463419fd83dad17d71cd63e7abe829e6b50f276e2a7b", null ],
      [ "kEmvsimTxFIFOFull", "group__emvsim__hal.html#gga9cfa10f80abdb57a203c0463419fd83da56a6608a76ec3caa0a1aec7752ab2610", null ],
      [ "kEmvsimTxComplete", "group__emvsim__hal.html#gga9cfa10f80abdb57a203c0463419fd83da898085750092ad14639559fb917fddf3", null ],
      [ "kEmvsimEarlyTxComplete", "group__emvsim__hal.html#gga9cfa10f80abdb57a203c0463419fd83dafb04a57d2d4bd6577f2f58371d300ab1", null ],
      [ "kEmvsimTxFIFOEmpty", "group__emvsim__hal.html#gga9cfa10f80abdb57a203c0463419fd83dacbef82fc3a0752bde4823b18eb1dc56e", null ],
      [ "kEmvsimTxNackThresholdErr", "group__emvsim__hal.html#gga9cfa10f80abdb57a203c0463419fd83da7b868469f5645a2e3e048e8514266556", null ],
      [ "kEmvsimTxAllStatus", "group__emvsim__hal.html#gga9cfa10f80abdb57a203c0463419fd83da72322a45912de5e7c155b90c67ec80c4", null ]
    ] ],
    [ "emvsim_presence_detect_edge_t", "group__emvsim__hal.html#gab06714ff51f473821a5e91b5e84455e8", [
      [ "kEmvsimPDOnFallingEdge", "group__emvsim__hal.html#ggab06714ff51f473821a5e91b5e84455e8a6a552a7d6e8b9920396efd9df688dbbc", null ],
      [ "kEmvsimPDOnRisingEdge", "group__emvsim__hal.html#ggab06714ff51f473821a5e91b5e84455e8a9e977bbcb8efb2bea2c3c3c347886801", null ]
    ] ],
    [ "emvsim_presence_detect_status_t", "group__emvsim__hal.html#gabdd4317cf95974fafe18dffdd12c1f4b", [
      [ "kEmvsimPDPinIsLow", "group__emvsim__hal.html#ggabdd4317cf95974fafe18dffdd12c1f4baaadbc1aa34efa598dfceb9a9c6cea67f", null ],
      [ "kEmvsimPDPinIsHigh", "group__emvsim__hal.html#ggabdd4317cf95974fafe18dffdd12c1f4ba52c0cbda4b539fb1cf69be4dc0735e6d", null ]
    ] ],
    [ "emvsim_card_clock_stop_polarity_t", "group__emvsim__hal.html#ga2f5fd7908fafcb00602cb4d7bdbcd17d", [
      [ "kEmvsimCardClockStopPolarityIsLow", "group__emvsim__hal.html#gga2f5fd7908fafcb00602cb4d7bdbcd17da85310035831c2330ab2d92be2b392887", null ],
      [ "kEmvsimCardClockStopPolarityIsHigh", "group__emvsim__hal.html#gga2f5fd7908fafcb00602cb4d7bdbcd17da4b80d0776990b5ca7b384755d2684796", null ]
    ] ],
    [ "emvsim_reset_card_t", "group__emvsim__hal.html#gaf7c2ff60c9c9e0cc8ce20c826c779387", [
      [ "kEmvsimResetAssert", "group__emvsim__hal.html#ggaf7c2ff60c9c9e0cc8ce20c826c779387ac3b52940f92d974f9301112e536fefa8", null ],
      [ "kEmvsimResetDeassert", "group__emvsim__hal.html#ggaf7c2ff60c9c9e0cc8ce20c826c779387a794b9e54b113f68e0ca2288955062a42", null ]
    ] ],
    [ "emvsim_vcc_en_polarity_t", "group__emvsim__hal.html#ga1154ce5a8090978f639a0b4e6fd753d2", [
      [ "kEmvsimVccEnIsHigh", "group__emvsim__hal.html#gga1154ce5a8090978f639a0b4e6fd753d2aece1e1dbbbd197a09d3e9c2d915a3525", null ],
      [ "kEmvsimVccEnIsLow", "group__emvsim__hal.html#gga1154ce5a8090978f639a0b4e6fd753d2a8928c597ddccfc355449e0b80ea2ef8a", null ]
    ] ],
    [ "EMVSIM_HAL_Init", "group__emvsim__hal.html#gaa55079b7ca97c9946488c99e4123e521", null ],
    [ "EMVSIM_HAL_GetModuleParameter", "group__emvsim__hal.html#ga71a948f9e118fba7d4851f42844bc51a", null ],
    [ "EMVSIM_HAL_GetTxFifoSize", "group__emvsim__hal.html#ga3fa1885ab28e8201f1ea22d528341f75", null ],
    [ "EMVSIM_HAL_GetRxFifoSize", "group__emvsim__hal.html#ga4e8b6f6e687e37ca50504326a9dec512", null ],
    [ "EMVSIM_HAL_SetGPCClockSelect", "group__emvsim__hal.html#gae4c5af17e99d53f65df736ade524ae78", null ],
    [ "EMVSIM_HAL_SetClockPrescaler", "group__emvsim__hal.html#ga01203918688d94f7aac07b33e7553c07", null ],
    [ "EMVSIM_HAL_SetBaudrateDivisor", "group__emvsim__hal.html#gab5955522a2410cf59e6facb4315be7e3", null ],
    [ "EMVSIM_HAL_SetControl", "group__emvsim__hal.html#ga4925eb4905a56609bf7b1ccaec120310", null ],
    [ "EMVSIM_HAL_GetControl", "group__emvsim__hal.html#gad37948a74f4dce36df7bdd9507b1cf1a", null ],
    [ "EMVSIM_HAL_SetIntMode", "group__emvsim__hal.html#ga745f55dea3a81a005fc1fd384a05c80d", null ],
    [ "EMVSIM_HAL_GetIntMode", "group__emvsim__hal.html#ga6340cdb78c3ca894f652ee64a7b66581", null ],
    [ "EMVSIM_HAL_SetReceiverNackThreshold", "group__emvsim__hal.html#gaa12b2a65d656a20c4b8b5aa0c66c323a", null ],
    [ "EMVSIM_HAL_GetReceiverNackThreshold", "group__emvsim__hal.html#ga491a9c5952002e4dd401d2a4cc5bf9dc", null ],
    [ "EMVSIM_HAL_SetReceiverDataThreshold", "group__emvsim__hal.html#gabc7d44ea290a01033172be828818e301", null ],
    [ "EMVSIM_HAL_GetReceiverDataThreshold", "group__emvsim__hal.html#ga3eef1bad710827f0bb56c835df5272db", null ],
    [ "EMVSIM_HAL_SetTransmitterNackThreshold", "group__emvsim__hal.html#ga1a582af7a723da41a4daf913ba2c3603", null ],
    [ "EMVSIM_HAL_GetTransmitterNackThreshold", "group__emvsim__hal.html#ga907d57bc1eb8a84433929425b39e0f6f", null ],
    [ "EMVSIM_HAL_SetTransmitterDataThreshold", "group__emvsim__hal.html#gae0bd86b366cca9d842da1170a6b5bc12", null ],
    [ "EMVSIM_HAL_GetTransmitterDataThreshold", "group__emvsim__hal.html#ga6f0af5a0a4c18544a7724bfdddf976b5", null ],
    [ "EMVSIM_HAL_IsReceiveFifoEmpty", "group__emvsim__hal.html#gae8edbcc9fd943db5606a5337d4f69f28", null ],
    [ "EMVSIM_HAL_IsTransmitFifoFull", "group__emvsim__hal.html#gaa492959ecf3c7a629b5c02eb958f08bc", null ],
    [ "EMVSIM_HAL_GetReceiveStatus", "group__emvsim__hal.html#gace79f29b0267389203b05e79f3dd20da", null ],
    [ "EMVSIM_HAL_ClearReceiveStatus", "group__emvsim__hal.html#ga4cf136b52114825f7d0df8ef0f68482e", null ],
    [ "EMVSIM_HAL_GetTransmitStatus", "group__emvsim__hal.html#gaa1ebce578c23084895b8806752eb70f9", null ],
    [ "EMVSIM_HAL_ClearTransmitStatus", "group__emvsim__hal.html#ga529af0595a618b18eb207ffbe35a87ef", null ],
    [ "EMVSIM_HAL_SetCardPresenceDetectEdge", "group__emvsim__hal.html#ga53041939a5b7e9ab51bb68223d4ed013", null ],
    [ "EMVSIM_HAL_GetCardPresenceDetectEdge", "group__emvsim__hal.html#ga30a3cc1c10636f665869d3613d887acf", null ],
    [ "EMVSIM_HAL_GetCardPresenceDetectPinStatus", "group__emvsim__hal.html#gac1b61897517b0c03dea47377e81a2ab3", null ],
    [ "EMVSIM_HAL_GetCardPresenceDetectInterruptStatus", "group__emvsim__hal.html#gad750f171887210bb2b6fd192394c36eb", null ],
    [ "EMVSIM_HAL_ClearCardPresenceDetectInterruptStatus", "group__emvsim__hal.html#ga185f3ea070f4f5b92f775bec0a236e86", null ],
    [ "EMVSIM_HAL_SetAutoPowerDown", "group__emvsim__hal.html#ga1551edd3ddf8e58365b0a12f4e48ddcf", null ],
    [ "EMVSIM_HAL_GetAutoPowerDown", "group__emvsim__hal.html#ga71fae347ddda83b5d0a07b8946dc0b23", null ],
    [ "EMVSIM_HAL_SetCardClockStopPolarity", "group__emvsim__hal.html#gade99bb0467ec476e422e31aa3dcc9cb5", null ],
    [ "EMVSIM_HAL_GetCardClockStopPolarity", "group__emvsim__hal.html#ga03312aa5f9c02bbbeace339c4376038b", null ],
    [ "EMVSIM_HAL_EnableCardClock", "group__emvsim__hal.html#gae325bd84c70a5bb99355d6a403834a48", null ],
    [ "EMVSIM_HAL_DisableCardClock", "group__emvsim__hal.html#ga428b984f33303d0917ca9fa02ee25879", null ],
    [ "EMVSIM_HAL_IsCardClockEnabled", "group__emvsim__hal.html#gab41ffbddacf0ccf3d41926369de3dd64", null ],
    [ "EMVSIM_HAL_ResetCard", "group__emvsim__hal.html#ga36768eb83b2d78ab58070f12f52ac85c", null ],
    [ "EMVSIM_HAL_GetCardResetState", "group__emvsim__hal.html#gac7590d78260c8993ec5337991b48ad51", null ],
    [ "EMVSIM_HAL_SetCardVCCEnablePolarity", "group__emvsim__hal.html#ga0665d54fffe4d5088d559c1f401992d5", null ],
    [ "EMVSIM_HAL_GetCardVCCEnablePolarity", "group__emvsim__hal.html#ga2b17ad2af29bd9f29a7b484ef008dc1b", null ],
    [ "EMVSIM_HAL_SetVCCEnable", "group__emvsim__hal.html#ga0a6a64cbe6235748b9a9e9e5a7c222e3", null ],
    [ "EMVSIM_HAL_GetVCCEnable", "group__emvsim__hal.html#ga341d6a571e6be51068d5288e9426549c", null ],
    [ "EMVSIM_HAL_EnableAutoPowerDown", "group__emvsim__hal.html#ga20f7d2e3d5c181b53eed63f38fea2ed2", null ],
    [ "EMVSIM_HAL_DisableAutoPowerDown", "group__emvsim__hal.html#ga6dc3bbbfff5075dd151af3743bd002d4", null ],
    [ "EMVSIM_HAL_IsAutoPowerDownEnabled", "group__emvsim__hal.html#gacfd49fd7ac312bc1f14a4e0a6ebbab2f", null ],
    [ "EMVSIM_HAL_GetChar", "group__emvsim__hal.html#gae34eccf3925b26419c7e1ac32f8ee120", null ],
    [ "EMVSIM_HAL_GetRxDataRegAddr", "group__emvsim__hal.html#ga773329445541b40a0adc3d9ea2a2d7a4", null ],
    [ "EMVSIM_HAL_PutChar", "group__emvsim__hal.html#gadc9cb9b055e6ead8baeafb82ca5b3532", null ],
    [ "EMVSIM_HAL_GetTxDataRegAddr", "group__emvsim__hal.html#gac4289126ab88212a317a29ca26e5235c", null ],
    [ "EMVSIM_HAL_SetAdditionalTransmitterGuardTime", "group__emvsim__hal.html#ga3086278e970aebabca4d04718e4e6652", null ],
    [ "EMVSIM_HAL_GetAdditionalTransmitterGuardTime", "group__emvsim__hal.html#gadbc837b65fee56f16f9d6064b29cad88", null ],
    [ "EMVSIM_HAL_SetCharacterWaitTime", "group__emvsim__hal.html#gaff704ebeff5d9c9ef70f75f8caf3fe09", null ],
    [ "EMVSIM_HAL_GetCharacterWaitTime", "group__emvsim__hal.html#ga57c89b17c47f770070fa6c3095492138", null ],
    [ "EMVSIM_HAL_SetBlockWaitTime", "group__emvsim__hal.html#ga744d65e036b5e6142448ad9f43210251", null ],
    [ "EMVSIM_HAL_GetBlockWaitTime", "group__emvsim__hal.html#ga68ddd3748fdbc2e5e1b40fb03ca70987", null ],
    [ "EMVSIM_HAL_SetBlockGuardTime", "group__emvsim__hal.html#gabf37c13c2ab4ef53f93cd8676e762ec4", null ],
    [ "EMVSIM_HAL_GetBlockGuardTime", "group__emvsim__hal.html#ga2e8c786f5f053856134d41c5b736808d", null ],
    [ "EMVSIM_HAL_SetGPCNTValue", "group__emvsim__hal.html#ga80db48d1de7ad251ab46d0cf4db0e390", null ],
    [ "EMVSIM_HAL_GetGPCNTValue", "group__emvsim__hal.html#ga5e57d8054e9ff6c9a71aa92edc00d493", null ]
];
