wrh2/sputnik/Vendor Firmware/Kinetis SDK v.1.3.0 API Reference Manual/group__enc__hal.js

var group__enc__hal =
[
    [ "enc_status_t", "group__enc__hal.html#gab04838b1a1c883aa7573ae0276e101f0", [
      [ "kStatus_ENC_Success", "group__enc__hal.html#ggab04838b1a1c883aa7573ae0276e101f0aebc79dccc4688258d0ae1d4094fa5a1a", null ],
      [ "kStatus_ENC_Error", "group__enc__hal.html#ggab04838b1a1c883aa7573ae0276e101f0af28bd3b803ef03b731c3f317f8a8ed96", null ],
      [ "kStatus_ENC_InvalidArgument", "group__enc__hal.html#ggab04838b1a1c883aa7573ae0276e101f0a2910d3fecda6bdb9fd905861a937cc50", null ]
    ] ],
    [ "enc_operation_mode_t", "group__enc__hal.html#gab214329be985e6f0ef873fc14c9f297f", [
      [ "kEncNormalMode", "group__enc__hal.html#ggab214329be985e6f0ef873fc14c9f297faeba03355a16e50cd948721fe0695c99c", null ],
      [ "kEncModuloCountingMode", "group__enc__hal.html#ggab214329be985e6f0ef873fc14c9f297fae594fef267d21a75755a021cf7252add", null ],
      [ "kEncSignalPhaseCountMode", "group__enc__hal.html#ggab214329be985e6f0ef873fc14c9f297fa421c3722dee4eead8dfa2f1c7e576a87", null ]
    ] ],
    [ "enc_status_flag_t", "group__enc__hal.html#ga9594d56f19cdf31e8611d293421ab336", [
      [ "kEncCmpFlag", "group__enc__hal.html#gga9594d56f19cdf31e8611d293421ab336a9fe8398f7ea4cf1246fe9645566a86d0", null ],
      [ "kEncHomeSignalFlag", "group__enc__hal.html#gga9594d56f19cdf31e8611d293421ab336a27b02a8bc6fa82dc95ca53be3de39a84", null ],
      [ "kEncWatchdogTimeoutFlag", "group__enc__hal.html#gga9594d56f19cdf31e8611d293421ab336ab95fc26a81db92208910ad677cbfb457", null ],
      [ "kEncIndexPulseFlag", "group__enc__hal.html#gga9594d56f19cdf31e8611d293421ab336adaea2db3b9795264f945132f3f0eb39b", null ],
      [ "kEncRollunderFlag", "group__enc__hal.html#gga9594d56f19cdf31e8611d293421ab336aec226fa122e3ed53887b96202d8a72af", null ],
      [ "kEncRolloverFlag", "group__enc__hal.html#gga9594d56f19cdf31e8611d293421ab336a0193bb5c2ece374e7b83ca6933b0c1ef", null ],
      [ "kEncSimultaneousFlag", "group__enc__hal.html#gga9594d56f19cdf31e8611d293421ab336a8f6d71e127ddd5f9d4ce801d3904eca8", null ],
      [ "kEncCountDirectionFlag", "group__enc__hal.html#gga9594d56f19cdf31e8611d293421ab336a826dcfc73237bc4c17f6e0bc2478d0c1", null ]
    ] ],
    [ "enc_int_source_t", "group__enc__hal.html#ga8aff871d4ca8aed9813bd7b58313ff74", [
      [ "kEncIntCmp", "group__enc__hal.html#gga8aff871d4ca8aed9813bd7b58313ff74a993a59b226399c5aa423de729c55f9f7", null ],
      [ "kEncIntHomeSignal", "group__enc__hal.html#gga8aff871d4ca8aed9813bd7b58313ff74a227ebfd541e634baa71cbc7591552c2c", null ],
      [ "kEncIntWatchdogTimeout", "group__enc__hal.html#gga8aff871d4ca8aed9813bd7b58313ff74a61b4b544681ecbce8ce7bceabd2b1f32", null ],
      [ "kEncIntIndexPulse", "group__enc__hal.html#gga8aff871d4ca8aed9813bd7b58313ff74a310a39860255537b5ec08d9ca64262ad", null ],
      [ "kEncIntRollunder", "group__enc__hal.html#gga8aff871d4ca8aed9813bd7b58313ff74af841d419a56f532b3eb34ba73aca9513", null ],
      [ "kEncIntRollover", "group__enc__hal.html#gga8aff871d4ca8aed9813bd7b58313ff74aa752984f1235b43ddc976264a73fdbf9", null ],
      [ "kEncIntSimultaneous", "group__enc__hal.html#gga8aff871d4ca8aed9813bd7b58313ff74a59247975b83bb8a29909403d6ba105a1", null ]
    ] ],
    [ "ENC_HAL_Init", "group__enc__hal.html#ga74cc1d938f66b3e37c39bb5acd0deee9", null ],
    [ "ENC_HAL_SetCmpIntCmd", "group__enc__hal.html#gac99467426385b8ebefb714468738db42", null ],
    [ "ENC_HAL_GetCmpIntCmd", "group__enc__hal.html#ga9bd2750d1e721e67ccff2c5eac2c8b7d", null ],
    [ "ENC_HAL_GetCmpIntFlag", "group__enc__hal.html#gadfb8f70b033f0d44a0fe4bdd6328b133", null ],
    [ "ENC_HAL_ClearCmpIntFlag", "group__enc__hal.html#gae27b7545953eb83dc3c2c3c2317e58b3", null ],
    [ "ENC_HAL_SetWatchdogCmd", "group__enc__hal.html#ga8d781034af1c4f1a884a689dd0b9d16e", null ],
    [ "ENC_HAL_GetWatchdogCmd", "group__enc__hal.html#ga11b539ce33f3ef51286891db49a771db", null ],
    [ "ENC_HAL_SetWatchdogIntCmd", "group__enc__hal.html#gabeede68ffa0de2026cf4b221c9cf9c00", null ],
    [ "ENC_HAL_GetWatchdogIntCmd", "group__enc__hal.html#gaa0d393ea31e2ce68aa956bcfc0c36c9c", null ],
    [ "ENC_HAL_GetWatchdogIntFlag", "group__enc__hal.html#gacffc2780466197d080350a5ac9b999ef", null ],
    [ "ENC_HAL_ClearWatchdogIntFlag", "group__enc__hal.html#gab0acc61baa3eb4c8fa2990031e671e2b", null ],
    [ "ENC_HAL_SetIndexPulseNegativeEdgeCmd", "group__enc__hal.html#gadf1fdb362c8e085b8b44a73bcbe0e947", null ],
    [ "ENC_HAL_GetIndexPulseNegativeEdgeCmd", "group__enc__hal.html#ga595144e13fbb13514d1655fe9c671bea", null ],
    [ "ENC_HAL_SetIndexInitPosCmd", "group__enc__hal.html#ga64ad3087a49f56306a427748a7925821", null ],
    [ "ENC_HAL_GetIndexInitPosCmd", "group__enc__hal.html#ga97f4f20906bdc1a2de06d8d794188d78", null ],
    [ "ENC_HAL_SetIndexPulseIntCmd", "group__enc__hal.html#ga8c2f0a9889075246d750cffd7c7aa932", null ],
    [ "ENC_HAL_GetIndexPulseIntCmd", "group__enc__hal.html#ga3ae899b8068f33a033ee2aefa7344230", null ],
    [ "ENC_HAL_GetIndexPulseIntFlag", "group__enc__hal.html#ga91918106daf1dc8aa3cbb19872538f20", null ],
    [ "ENC_HAL_ClearIndexPulseIntFlag", "group__enc__hal.html#gafedfeb5d1a305dca1120a6b0c9a99ed7", null ],
    [ "ENC_HAL_SetSignalPhaseCountModeCmd", "group__enc__hal.html#ga8b6323716994d6b00f87f387e99d2701", null ],
    [ "ENC_HAL_GetSignalPhaseCountModeCmd", "group__enc__hal.html#ga390ef2a57c2c219e94297ef6bedaa74d", null ],
    [ "ENC_HAL_SetReverseCountingCmd", "group__enc__hal.html#ga1d0c2e6e7536a956f9e30175c805b08c", null ],
    [ "ENC_HAL_GetReverseCountingCmd", "group__enc__hal.html#gaae406e2ca01c5cce5120dfd7364aa87d", null ],
    [ "ENC_HAL_GetLastCountDirectionFlag", "group__enc__hal.html#ga13748ac3aea5ec420995735f2c45ad5d", null ],
    [ "ENC_HAL_InitPosCounter", "group__enc__hal.html#ga8702afd9a60dc7f86cffbcd05f5b23bd", null ],
    [ "ENC_HAL_SetHomeSignalNegativeEdgeCmd", "group__enc__hal.html#ga9b7b33c5b74e241c3c664603e9de6d6a", null ],
    [ "ENC_HAL_GetHomeSignalNegativeEdgeCmd", "group__enc__hal.html#ga433602d9afe19cb7b573283f692fd489", null ],
    [ "ENC_HAL_SetHomeInitPosCmd", "group__enc__hal.html#ga336a5935e8f3cac3925097efb868dfd7", null ],
    [ "ENC_HAL_GetHomeInitPosCmd", "group__enc__hal.html#gaa2b8f0557eb54ce49cc912dbf809f51d", null ],
    [ "ENC_HAL_SetHomeSignalIntCmd", "group__enc__hal.html#gab5fc4c05465c606bd6b0a69d787eeebe", null ],
    [ "ENC_HAL_GetHomeSignalIntCmd", "group__enc__hal.html#ga9b466e1b9045f68f6e5d7d25d6a083f1", null ],
    [ "ENC_HAL_GetHomeSignalIntFlag", "group__enc__hal.html#ga22a31c69d2ebcdd4737ac004b07319c3", null ],
    [ "ENC_HAL_ClearHomeSignalIntFlag", "group__enc__hal.html#ga4a83efbd8590d0b3128350551dbe6953", null ],
    [ "ENC_HAL_SetInputFilterSampleCount", "group__enc__hal.html#gab4054404a73e2d1c7bdbcd569aa9ae5e", null ],
    [ "ENC_HAL_GetInputFilterSampleCount", "group__enc__hal.html#gaf10004137eb9fc399cb759fccaaa235a", null ],
    [ "ENC_HAL_SetInputFilterSamplePeriod", "group__enc__hal.html#ga61549328d8eb4b6c26737005941e6b18", null ],
    [ "ENC_HAL_GetInputFilterSamplePeriod", "group__enc__hal.html#gaecf7cbea488f182ddc3e9361b6c39dc1", null ],
    [ "ENC_HAL_SetWatchdogTimeout", "group__enc__hal.html#ga4af241404410efee011926e8d0ad53ff", null ],
    [ "ENC_HAL_GetWatchdogTimeout", "group__enc__hal.html#ga763234382671145763e8a27eeda394d5", null ],
    [ "ENC_HAL_SetPosDiffCounterReg", "group__enc__hal.html#gaea01d7c33c7443d52ebdac274d982a99", null ],
    [ "ENC_HAL_GetPosDiffCounterReg", "group__enc__hal.html#ga45c07e05f8fe4174b699aa76f8ef55eb", null ],
    [ "ENC_HAL_GetPosDiffHoldReg", "group__enc__hal.html#ga6790150e99159cdeb2410cc4877e5661", null ],
    [ "ENC_HAL_SetRevolutionCounterReg", "group__enc__hal.html#ga46209fad9c9600164975bb4cf1758549", null ],
    [ "ENC_HAL_GetRevolutionCounterReg", "group__enc__hal.html#gaee1bb2bd1ea1f62fdd38470458754aac", null ],
    [ "ENC_HAL_GetRevolutionHoldReg", "group__enc__hal.html#ga60457499f6faec62eca454571c1f565d", null ],
    [ "ENC_HAL_GetPosCounterReg", "group__enc__hal.html#ga07de86b83ac73b010725ac2ad95d85a9", null ],
    [ "ENC_HAL_SetPosCounterReg", "group__enc__hal.html#ga33959bab0579a79ae44f06537a6a77a7", null ],
    [ "ENC_HAL_GetPosHoldReg", "group__enc__hal.html#ga04a035c9b703611ef76deffb514eab09", null ],
    [ "ENC_HAL_SetInitReg", "group__enc__hal.html#ga59f51a74e4f3c5b7e8890fdd3638b952", null ],
    [ "ENC_HAL_GetInitReg", "group__enc__hal.html#gafeb9144215225bb2a4b6a9cf73ebdc7c", null ],
    [ "ENC_HAL_GetRawHomeInput", "group__enc__hal.html#ga02cd504ea5cd35b14845d3677fcbe862", null ],
    [ "ENC_HAL_GetRawIndexInput", "group__enc__hal.html#gabc4dd438d34278f357cb406b994ad0e0", null ],
    [ "ENC_HAL_GetRawPhaseBInput", "group__enc__hal.html#ga779150fade25c4cb480040022c1433a1", null ],
    [ "ENC_HAL_GetRawPhaseAInput", "group__enc__hal.html#gaccf0d53bd64bfe98696cd0243e7115df", null ],
    [ "ENC_HAL_GetFilteredHomeInput", "group__enc__hal.html#ga5878d350fa79660439e2d9a926f98ea9", null ],
    [ "ENC_HAL_GetFilteredIndexInput", "group__enc__hal.html#ga10e4aa5777e1a0a27b050ee0bdd00349", null ],
    [ "ENC_HAL_GetFilteredPhaseBInput", "group__enc__hal.html#ga892f5aa0db82bcf2c157121140c0eba7", null ],
    [ "ENC_HAL_GetFilteredPhaseAInput", "group__enc__hal.html#ga0c3aa7ae467d7729f73d67f683646d0d", null ],
    [ "ENC_HAL_GetTestCount", "group__enc__hal.html#ga0d97db609137db20c283ef8ac7db9337", null ],
    [ "ENC_HAL_SetTestCount", "group__enc__hal.html#ga9e6697e5390df1e644ea3325daf87508", null ],
    [ "ENC_HAL_GetTestPeriod", "group__enc__hal.html#ga6dfa7bad58016bd404832c2d1226e6c2", null ],
    [ "ENC_HAL_SetTestPeriod", "group__enc__hal.html#ga778d71c8676483ee2d2fd167e2c2d7f2", null ],
    [ "ENC_HAL_SetNegativeTestSignalCmd", "group__enc__hal.html#gaa2fba2090b58a568ca4cf11d1d17abc7", null ],
    [ "ENC_HAL_GetNegativeTestSignalCmd", "group__enc__hal.html#ga15544476b947ecd9e5fd03ea4f8a5496", null ],
    [ "ENC_HAL_SetTestCounterCmd", "group__enc__hal.html#gafe843a73152562628a96ec507e756cdf", null ],
    [ "ENC_HAL_GetTestCounterCmd", "group__enc__hal.html#ga8db673e9ae4c5ae12efede535fcf77d2", null ],
    [ "ENC_HAL_SetTestModuleCmd", "group__enc__hal.html#ga8bfe19b60b4999fb5a600c02b68b798f", null ],
    [ "ENC_HAL_GetTestModuleCmd", "group__enc__hal.html#ga71722a4d1a1330b04f46e99483e6bce0", null ],
    [ "ENC_HAL_SetModulusReg", "group__enc__hal.html#ga5136b80440788a9d6eda899fe325c07e", null ],
    [ "ENC_HAL_GetModulusReg", "group__enc__hal.html#ga274dbbed382b61e582d1d7d73d981005", null ],
    [ "ENC_HAL_SetCmpReg", "group__enc__hal.html#gaf91c5532af0e98760263099712b7becf", null ],
    [ "ENC_HAL_GetCmpReg", "group__enc__hal.html#gad08ced1fd855b7e875633093d5abeb5c", null ],
    [ "ENC_HAL_SetTriggerUpdateHoldRegCmd", "group__enc__hal.html#gae642315122b98bf276eeebaa0ade0aee", null ],
    [ "ENC_HAL_GetTriggerUpdateHoldRegCmd", "group__enc__hal.html#ga8032267cdd99fcdfad981f89eec1cfda", null ],
    [ "ENC_HAL_SetTriggerClearPosRegCmd", "group__enc__hal.html#gaeb614ff318f5daa20c09a54b76fc2e14", null ],
    [ "ENC_HAL_GetTriggerClearPosRegCmd", "group__enc__hal.html#ga9fea2b49a5ba842d7dbf7169e50555e1", null ],
    [ "ENC_HAL_SetModuloCountingCmd", "group__enc__hal.html#gaeb1f9ab5dc3cd818784387dbfebfee99", null ],
    [ "ENC_HAL_GetModuloCountingCmd", "group__enc__hal.html#ga17455b6142d8fbdd7f35814eb6d8c664", null ],
    [ "ENC_HAL_SetRollunderIntCmd", "group__enc__hal.html#ga3f6a02cf00da74c71a9c0c209c1ce9f6", null ],
    [ "ENC_HAL_GetRollunderIntCmd", "group__enc__hal.html#gaab0bb50f13ed2cc933d0f1a00c2d54ec", null ],
    [ "ENC_HAL_GetRollunderIntFlag", "group__enc__hal.html#gaa9e4ffbc697890e8813e95c89c82d109", null ],
    [ "ENC_HAL_ClearRollunderIntFlag", "group__enc__hal.html#gae189f7d3a68a8609ddc147d64f287556", null ],
    [ "ENC_HAL_SetRolloverIntCmd", "group__enc__hal.html#ga82178ff0eb94f07356233cec149def51", null ],
    [ "ENC_HAL_GetRolloverIntCmd", "group__enc__hal.html#gac3b9a7f438366f4f3329a859aa6085b1", null ],
    [ "ENC_HAL_GetRolloverIntFlag", "group__enc__hal.html#ga31b1acc6a3ab210b54633ea78fc7282d", null ],
    [ "ENC_HAL_ClearRolloverIntFlag", "group__enc__hal.html#ga56ab8d1d0fa617c7d7af83c40e59c6ab", null ],
    [ "ENC_HAL_SetModulusRevCounterCmd", "group__enc__hal.html#gadd4cbb2242a96cd40df8c383f6d39a19", null ],
    [ "ENC_HAL_GetModulusRevCounterCmd", "group__enc__hal.html#ga70470021792440956658a59fb156af7c", null ],
    [ "ENC_HAL_SetPosmatchOnReadingCmd", "group__enc__hal.html#ga0770acd43c34f1958a77609ecc75dc25", null ],
    [ "ENC_HAL_GetPosmatchOnReadingCmd", "group__enc__hal.html#ga88c136477ac71c28ebbc69d50290b608", null ],
    [ "ENC_HAL_SetSimultaneousIntCmd", "group__enc__hal.html#ga78bffbdd54c6d8cb954976d8ef0fcf96", null ],
    [ "ENC_HAL_GetSimultaneousIntCmd", "group__enc__hal.html#gaa06985d4f85bdc8f971013372312ba11", null ],
    [ "ENC_HAL_GetSimultaneousIntFlag", "group__enc__hal.html#ga2755d9c92c9eed52d7f467709d9e23c8", null ],
    [ "ENC_HAL_ClearSimultaneousIntFlag", "group__enc__hal.html#ga967b14372d7583b63e6d57fad36af3af", null ]
];
