wrh2/sputnik/Vendor Firmware/Kinetis SDK v.1.3.0 API Reference Manual/group__lpsci__hal.js

var group__lpsci__hal =
[
    [ "lpsci_status_t", "group__lpsci__hal.html#gae53b9de3437b86e0454e6d18e4b056ec", null ],
    [ "lpsci_stop_bit_count_t", "group__lpsci__hal.html#ga1e71c77aa3c6663fa13a36614ecd5218", [
      [ "kLpsciOneStopBit", "group__lpsci__hal.html#gga1e71c77aa3c6663fa13a36614ecd5218ac6551111fd848fa3da94aeea35927903", null ],
      [ "kLpsciTwoStopBit", "group__lpsci__hal.html#gga1e71c77aa3c6663fa13a36614ecd5218a8d59dbdcc8a72f10208e259b006ee107", null ]
    ] ],
    [ "lpsci_parity_mode_t", "group__lpsci__hal.html#ga914e25b9b58c086d6ee790f7bbe96de1", [
      [ "kLpsciParityDisabled", "group__lpsci__hal.html#gga914e25b9b58c086d6ee790f7bbe96de1af83e7c01bf31e80dd0c42648d6b3e5b8", null ],
      [ "kLpsciParityEven", "group__lpsci__hal.html#gga914e25b9b58c086d6ee790f7bbe96de1afe3bea112033ca2f9bc079367ba351a8", null ],
      [ "kLpsciParityOdd", "group__lpsci__hal.html#gga914e25b9b58c086d6ee790f7bbe96de1a37c2ec1e9612463a4ad19f16447bb10a", null ]
    ] ],
    [ "lpsci_bit_count_per_char_t", "group__lpsci__hal.html#ga6faa066fce41e4f592f4ae914cd04993", [
      [ "kLpsci8BitsPerChar", "group__lpsci__hal.html#gga6faa066fce41e4f592f4ae914cd04993a93fe1146390c0a8d0d0668f7b20e673f", null ],
      [ "kLpsci9BitsPerChar", "group__lpsci__hal.html#gga6faa066fce41e4f592f4ae914cd04993a306ded32b6358aa3617cd37084f1f86b", null ]
    ] ],
    [ "lpsci_operation_config_t", "group__lpsci__hal.html#ga69e476422adeb62e189febd6d7284999", [
      [ "kLpsciOperates", "group__lpsci__hal.html#gga69e476422adeb62e189febd6d7284999a20d078eb6493a7b8862355a32fa0508a", null ],
      [ "kLpsciStops", "group__lpsci__hal.html#gga69e476422adeb62e189febd6d7284999a4ad57ef704cd569a82bad1305a98e197", null ]
    ] ],
    [ "lpsci_receiver_source_t", "group__lpsci__hal.html#ga1c91171f3d523e8bda58ed1fc65ce3b6", [
      [ "kLpsciLoopBack", "group__lpsci__hal.html#gga1c91171f3d523e8bda58ed1fc65ce3b6af203716d9f7b9406585df0f7c706cea2", null ],
      [ "kLpsciSingleWire", "group__lpsci__hal.html#gga1c91171f3d523e8bda58ed1fc65ce3b6a7eb9076f785dbb615655843e9ed15475", null ]
    ] ],
    [ "lpsci_wakeup_method_t", "group__lpsci__hal.html#gaafd90b6e590b191222d0a22f6cc06e75", [
      [ "kLpsciIdleLineWake", "group__lpsci__hal.html#ggaafd90b6e590b191222d0a22f6cc06e75a54b83d4a743d82f5dabdb4b5b5e90aa9", null ],
      [ "kLpsciAddrMarkWake", "group__lpsci__hal.html#ggaafd90b6e590b191222d0a22f6cc06e75ae53db6fde8b3699ac75ac9a223ae614b", null ]
    ] ],
    [ "lpsci_idle_line_select_t", "group__lpsci__hal.html#ga3f896f0f5754a1203acb03afc896ef0c", [
      [ "kLpsciIdleLineAfterStartBit", "group__lpsci__hal.html#gga3f896f0f5754a1203acb03afc896ef0ca49dd10343c0169ccda2f0b1bcda537b7", null ],
      [ "kLpsciIdleLineAfterStopBit", "group__lpsci__hal.html#gga3f896f0f5754a1203acb03afc896ef0ca393142686153bd6a1ca16d22ac0b7265", null ]
    ] ],
    [ "lpsci_break_char_length_t", "group__lpsci__hal.html#gaaed3b10a751f8a4a2b6ad610f2582532", [
      [ "kLpsciBreakChar10BitMinimum", "group__lpsci__hal.html#ggaaed3b10a751f8a4a2b6ad610f2582532a3db1ce52d17bebf0a676afcb419920f2", null ],
      [ "kLpsciBreakChar13BitMinimum", "group__lpsci__hal.html#ggaaed3b10a751f8a4a2b6ad610f2582532ac80590f41c9e887565f2b44225e1845e", null ]
    ] ],
    [ "lpsci_singlewire_txdir_t", "group__lpsci__hal.html#gabe047ce8844f6b7885dba696b9c04bee", [
      [ "kLpsciSinglewireTxdirIn", "group__lpsci__hal.html#ggabe047ce8844f6b7885dba696b9c04beeabe7ad6b425b0e7ebc28419900031682b", null ],
      [ "kLpsciSinglewireTxdirOut", "group__lpsci__hal.html#ggabe047ce8844f6b7885dba696b9c04beea3b4fe4ff6389a73e462557f2ad7e8a2e", null ]
    ] ],
    [ "lpsci_ir_tx_pulsewidth_t", "group__lpsci__hal.html#gab80ff15c62eee72aa70f88de95858369", [
      [ "kLpsciIrThreeSixteenthsWidth", "group__lpsci__hal.html#ggab80ff15c62eee72aa70f88de95858369ad37b2b058f58214bf37016513dc4b3d2", null ],
      [ "kLpsciIrOneSixteenthWidth", "group__lpsci__hal.html#ggab80ff15c62eee72aa70f88de95858369a33d53247d655663071352da67fcd4d92", null ],
      [ "kLpsciIrOneThirtysecondsWidth", "group__lpsci__hal.html#ggab80ff15c62eee72aa70f88de95858369a3e415fe3cd5e83c54ecd3ae0983a8143", null ],
      [ "kLpsciIrOneFourthWidth", "group__lpsci__hal.html#ggab80ff15c62eee72aa70f88de95858369af5dc06b1c68751fc17bc690915eb1a07", null ]
    ] ],
    [ "lpsci_status_flag_t", "group__lpsci__hal.html#ga317ec873ae11d4c1e22bc9679a7b1632", [
      [ "kLpsciTxDataRegEmpty", "group__lpsci__hal.html#gga317ec873ae11d4c1e22bc9679a7b1632a68ab5b72f948f9dffe37ba510e1365be", null ],
      [ "kLpsciTxComplete", "group__lpsci__hal.html#gga317ec873ae11d4c1e22bc9679a7b1632a778905a26757d41140b85af9f0eda5b4", null ],
      [ "kLpsciRxDataRegFull", "group__lpsci__hal.html#gga317ec873ae11d4c1e22bc9679a7b1632ac897d1ada200cba9e2acfac314873136", null ],
      [ "kLpsciIdleLineDetect", "group__lpsci__hal.html#gga317ec873ae11d4c1e22bc9679a7b1632ac9ecbaffb4ea3bec9ae7764846f2a822", null ],
      [ "kLpsciRxOverrun", "group__lpsci__hal.html#gga317ec873ae11d4c1e22bc9679a7b1632a1254498cc6fe93de933548047a2697c7", null ],
      [ "kLpsciNoiseDetect", "group__lpsci__hal.html#gga317ec873ae11d4c1e22bc9679a7b1632ae21e1075dead178f37a8fdb228ae31e0", null ],
      [ "kLpsciFrameErr", "group__lpsci__hal.html#gga317ec873ae11d4c1e22bc9679a7b1632a70d8e161b36dbbc1f1b2529922c16961", null ],
      [ "kLpsciParityErr", "group__lpsci__hal.html#gga317ec873ae11d4c1e22bc9679a7b1632a7f71ff7e7d7b218fa880a30f73ca1131", null ],
      [ "kLpsciLineBreakDetect", "group__lpsci__hal.html#gga317ec873ae11d4c1e22bc9679a7b1632a0f8e6e239767889f9850a67c5b92146d", null ],
      [ "kLpsciRxActiveEdgeDetect", "group__lpsci__hal.html#gga317ec873ae11d4c1e22bc9679a7b1632ae719a3521e1210b994e2264180ba4aee", null ],
      [ "kLpsciRxActive", "group__lpsci__hal.html#gga317ec873ae11d4c1e22bc9679a7b1632a111f98a841fc8199dbc72b4f10d6347d", null ]
    ] ],
    [ "lpsci_interrupt_t", "group__lpsci__hal.html#ga823685ad40e8e8765514af6795af1595", [
      [ "kLpsciIntLinBreakDetect", "group__lpsci__hal.html#gga823685ad40e8e8765514af6795af1595a1b1f825cad9b0584a721344525b28cf2", null ],
      [ "kLpsciIntRxActiveEdge", "group__lpsci__hal.html#gga823685ad40e8e8765514af6795af1595a654045650fb564b8d87507a0de223c67", null ],
      [ "kLpsciIntTxDataRegEmpty", "group__lpsci__hal.html#gga823685ad40e8e8765514af6795af1595a1a3caab6183842076c53d4007b4d895e", null ],
      [ "kLpsciIntTxComplete", "group__lpsci__hal.html#gga823685ad40e8e8765514af6795af1595a66151a41ebb1263e7b405c72b1e2d9d4", null ],
      [ "kLpsciIntRxDataRegFull", "group__lpsci__hal.html#gga823685ad40e8e8765514af6795af1595abd20c2419e3f6684e1ddf6a5e5e8529c", null ],
      [ "kLpsciIntIdleLine", "group__lpsci__hal.html#gga823685ad40e8e8765514af6795af1595a5e233d8c417979ee7e542ed0be1251ac", null ],
      [ "kLpsciIntRxOverrun", "group__lpsci__hal.html#gga823685ad40e8e8765514af6795af1595ad7b854c435ac8059803aa53f3dd72f12", null ],
      [ "kLpsciIntNoiseErrFlag", "group__lpsci__hal.html#gga823685ad40e8e8765514af6795af1595af724a77f2ddf007687453b9c25f818b2", null ],
      [ "kLpsciIntFrameErrFlag", "group__lpsci__hal.html#gga823685ad40e8e8765514af6795af1595ac647e8f6d05fe064ce725f5abe6cd46b", null ],
      [ "kLpsciIntParityErrFlag", "group__lpsci__hal.html#gga823685ad40e8e8765514af6795af1595a4b6bfe6b8ef5ecadc4dbdbe73d3ba5c8", null ]
    ] ],
    [ "LPSCI_HAL_Init", "group__lpsci__hal.html#gaa673c77e63e44d167cab4391fb893379", null ],
    [ "LPSCI_HAL_EnableTransmitter", "group__lpsci__hal.html#gaf1970013d9f30251a843cbda02f1c11c", null ],
    [ "LPSCI_HAL_DisableTransmitter", "group__lpsci__hal.html#gad5167c2e9fa537f94fa22cfafae63801", null ],
    [ "LPSCI_HAL_IsTransmitterEnabled", "group__lpsci__hal.html#gadbbb65f6b19a2d8bdafc21118e99576f", null ],
    [ "LPSCI_HAL_EnableReceiver", "group__lpsci__hal.html#ga3e7d9ae3674ace42190c3c469b970bb2", null ],
    [ "LPSCI_HAL_DisableReceiver", "group__lpsci__hal.html#gac27966e824336a89610db3a59baac697", null ],
    [ "LPSCI_HAL_IsReceiverEnabled", "group__lpsci__hal.html#gaa0a90d3f4be926f169a7bf509853f722", null ],
    [ "LPSCI_HAL_SetBaudRate", "group__lpsci__hal.html#gaad7461ce75464a214b5e90414f5e2ad7", null ],
    [ "LPSCI_HAL_SetBaudRateDivisor", "group__lpsci__hal.html#ga9be55a6c2e4981de3b694ac3d268b0d6", null ],
    [ "LPSCI_HAL_SetBitCountPerChar", "group__lpsci__hal.html#gaf319d1c96fd38fabe48088950b7a7d75", null ],
    [ "LPSCI_HAL_SetParityMode", "group__lpsci__hal.html#gab5c5e46eac05c27b64fa0d2ec91ddd5f", null ],
    [ "LPSCI_HAL_SetIntMode", "group__lpsci__hal.html#gac927927d104706187799e3bd38b49edf", null ],
    [ "LPSCI_HAL_GetIntMode", "group__lpsci__hal.html#gabdf6f0bfd6c4684af25a3bae8d7f1c90", null ],
    [ "LPSCI_HAL_GetDataRegAddr", "group__lpsci__hal.html#ga8b778d1c8503e24dc8666f273915c0e9", null ],
    [ "LPSCI_HAL_Putchar", "group__lpsci__hal.html#gae2da34bf1c79cab128dfe55d3788ed07", null ],
    [ "LPSCI_HAL_Putchar9", "group__lpsci__hal.html#ga55705e7a67b757eaf9820debd42c0ac3", null ],
    [ "LPSCI_HAL_Putchar10", "group__lpsci__hal.html#ga166fbb10b9408f7b037a88757fe524ac", null ],
    [ "LPSCI_HAL_Getchar", "group__lpsci__hal.html#ga7b4da8cd5a026fd5cff4317dfe406ae5", null ],
    [ "LPSCI_HAL_Getchar9", "group__lpsci__hal.html#ga3101ff97e2980e0c4cb6f3e1b5a306d3", null ],
    [ "LPSCI_HAL_Getchar10", "group__lpsci__hal.html#ga45b629d63923fa3345a807a2ea4e3b4d", null ],
    [ "LPSCI_HAL_SendDataPolling", "group__lpsci__hal.html#ga2d175410823819416db658721f691925", null ],
    [ "LPSCI_HAL_ReceiveDataPolling", "group__lpsci__hal.html#gab16e3856541bdfe5f1bf05b41bcfc627", null ],
    [ "LPSCI_HAL_GetStatusFlag", "group__lpsci__hal.html#gadb7784c529ff4b312f6117d6ee5dbf8d", null ],
    [ "LPSCI_HAL_ClearStatusFlag", "group__lpsci__hal.html#ga6df6ce93f0a2ebd7d8c0d9bc6fa35527", null ],
    [ "LPSCI_HAL_SetWaitModeOperation", "group__lpsci__hal.html#ga85481a444e7ca1f0565bf7a6c19d5750", null ],
    [ "LPSCI_HAL_GetWaitModeOperation", "group__lpsci__hal.html#ga177d5403ec40d35d8b0e0177b44b48c7", null ],
    [ "LPSCI_HAL_SetLoopCmd", "group__lpsci__hal.html#ga1e70e922fcf2fbe38554173d2060c5ef", null ],
    [ "LPSCI_HAL_SetReceiverSource", "group__lpsci__hal.html#ga1f298f3731caed064157f110f53914b6", null ],
    [ "LPSCI_HAL_SetTransmitterDir", "group__lpsci__hal.html#ga7b819d39e2cd74da8bc10f34de0d5f9c", null ],
    [ "LPSCI_HAL_PutReceiverInStandbyMode", "group__lpsci__hal.html#ga45a09635d5d494c6337d5c4c99558367", null ],
    [ "LPSCI_HAL_PutReceiverInNormalMode", "group__lpsci__hal.html#ga651069e1a21543a89f8f811bf0e5dc9e", null ],
    [ "LPSCI_HAL_IsReceiverInStandby", "group__lpsci__hal.html#gafa8bbde184b66d1ea302621dbbbaa8cd", null ],
    [ "LPSCI_HAL_SetReceiverWakeupMethod", "group__lpsci__hal.html#gad59b60f483af33143acc3bafa7253549", null ],
    [ "LPSCI_HAL_GetReceiverWakeupMethod", "group__lpsci__hal.html#gab5297d94612d3d9c1bbe186013b8b941", null ],
    [ "LPSCI_HAL_ConfigIdleLineDetect", "group__lpsci__hal.html#gae87c6e96f7ba0966510f0f44fab4bc6f", null ],
    [ "LPSCI_HAL_SetBreakCharTransmitLength", "group__lpsci__hal.html#gabf552b1b963391d6cb87f07af90b5d57", null ],
    [ "LPSCI_HAL_SetBreakCharDetectLength", "group__lpsci__hal.html#gaad4168f9bd5df76c0cc009e5945c951b", null ],
    [ "LPSCI_HAL_SetBreakCharCmd", "group__lpsci__hal.html#ga9d343de9eacef91a5e5243fb45c2a016", null ],
    [ "LPSCI_HAL_SetMatchAddress", "group__lpsci__hal.html#gadf6e9d1a3ecf491b4a345c6ae3533d5f", null ]
];
