wrh2/sputnik/Vendor Firmware/Kinetis SDK v.1.3.0 API Reference Manual/group__lpuart__hal.js

var group__lpuart__hal =
[
    [ "lpuart_idle_line_config_t", "group__lpuart__hal.html#structlpuart__idle__line__config__t", [
      [ "idleLineType", "group__lpuart__hal.html#a106c1cec31cdfb269677bc4eb18f4057", null ],
      [ "rxWakeIdleDetect", "group__lpuart__hal.html#aab49e998425fad9e512605f652827736", null ]
    ] ],
    [ "lpuart_status_t", "group__lpuart__hal.html#gab508528fb5ec3c34ccf201c3ed2ac05f", null ],
    [ "lpuart_stop_bit_count_t", "group__lpuart__hal.html#ga7540d87bc3fa8a605d8da53fe08219f0", [
      [ "kLpuartOneStopBit", "group__lpuart__hal.html#gga7540d87bc3fa8a605d8da53fe08219f0a449645202e070ef07e6e709b5bf79224", null ],
      [ "kLpuartTwoStopBit", "group__lpuart__hal.html#gga7540d87bc3fa8a605d8da53fe08219f0a5d0100404ceeb4b12aae91cd4fc032ca", null ]
    ] ],
    [ "lpuart_parity_mode_t", "group__lpuart__hal.html#ga6fcd73abf900b8a17dab1f2b1f3f53c7", [
      [ "kLpuartParityDisabled", "group__lpuart__hal.html#gga6fcd73abf900b8a17dab1f2b1f3f53c7ab707ab52fda5eebbf905707ead80f9db", null ],
      [ "kLpuartParityEven", "group__lpuart__hal.html#gga6fcd73abf900b8a17dab1f2b1f3f53c7a985c0d4256eda6b1f4a6ac774c4b2724", null ],
      [ "kLpuartParityOdd", "group__lpuart__hal.html#gga6fcd73abf900b8a17dab1f2b1f3f53c7ac8ae9ae8cfac547820f4397259d3b9e6", null ]
    ] ],
    [ "lpuart_bit_count_per_char_t", "group__lpuart__hal.html#gadcdd4a875d1839a8ed41c162c2c67566", [
      [ "kLpuart8BitsPerChar", "group__lpuart__hal.html#ggadcdd4a875d1839a8ed41c162c2c67566a88bba48fe3fd65a75f30e6917e4b6b7f", null ],
      [ "kLpuart9BitsPerChar", "group__lpuart__hal.html#ggadcdd4a875d1839a8ed41c162c2c67566a478f617a0733c69bed877a93e446c193", null ],
      [ "kLpuart10BitsPerChar", "group__lpuart__hal.html#ggadcdd4a875d1839a8ed41c162c2c67566a5208a9d3dbbc57b9540e3f83b3e85911", null ]
    ] ],
    [ "lpuart_operation_config_t", "group__lpuart__hal.html#gac3b14b0fa037480832cbd0d8f44588c6", [
      [ "kLpuartOperates", "group__lpuart__hal.html#ggac3b14b0fa037480832cbd0d8f44588c6a53d055ba8ca7981824a65bcc88d5a20e", null ],
      [ "kLpuartStops", "group__lpuart__hal.html#ggac3b14b0fa037480832cbd0d8f44588c6ac7b3ee1628545f35b38c50dc40864d3b", null ]
    ] ],
    [ "lpuart_wakeup_method_t", "group__lpuart__hal.html#ga10e02b179f7e02bcb41454f19497364a", [
      [ "kLpuartIdleLineWake", "group__lpuart__hal.html#gga10e02b179f7e02bcb41454f19497364aad291a0f924396a25bb039f70afc2eb12", null ],
      [ "kLpuartAddrMarkWake", "group__lpuart__hal.html#gga10e02b179f7e02bcb41454f19497364aa1c1b03b329a53a83ee57e6fa86e6e163", null ]
    ] ],
    [ "lpuart_idle_line_select_t", "group__lpuart__hal.html#ga8e1446ddce4870c9ecf2d90ce405b94f", [
      [ "kLpuartIdleLineAfterStartBit", "group__lpuart__hal.html#gga8e1446ddce4870c9ecf2d90ce405b94fab84cb8c35d387035302782587a8a87b3", null ],
      [ "kLpuartIdleLineAfterStopBit", "group__lpuart__hal.html#gga8e1446ddce4870c9ecf2d90ce405b94fa1fa94636e63d4abf9096deff9b5566a8", null ]
    ] ],
    [ "lpuart_break_char_length_t", "group__lpuart__hal.html#ga448305cb3da749d64de10ed3f13655de", [
      [ "kLpuartBreakChar10BitMinimum", "group__lpuart__hal.html#gga448305cb3da749d64de10ed3f13655dea289447536ba20af2a878a5c78bbd2291", null ],
      [ "kLpuartBreakChar13BitMinimum", "group__lpuart__hal.html#gga448305cb3da749d64de10ed3f13655dea4732cb9b579b6a56c2b401bd365cf2a3", null ]
    ] ],
    [ "lpuart_singlewire_txdir_t", "group__lpuart__hal.html#ga5208b7d770923733b45174353647c318", [
      [ "kLpuartSinglewireTxdirIn", "group__lpuart__hal.html#gga5208b7d770923733b45174353647c318a1f0c083e2e656b45735c3a3be7eda1f4", null ],
      [ "kLpuartSinglewireTxdirOut", "group__lpuart__hal.html#gga5208b7d770923733b45174353647c318a09e429dc344e09c59f18889703ff379f", null ]
    ] ],
    [ "lpuart_match_config_t", "group__lpuart__hal.html#ga62c6b6c1f838c0de5b954d3a8662316e", [
      [ "kLpuartAddressMatchWakeup", "group__lpuart__hal.html#gga62c6b6c1f838c0de5b954d3a8662316ea7c7ee0104954f3c1d4b4ef098efe8042", null ],
      [ "kLpuartIdleMatchWakeup", "group__lpuart__hal.html#gga62c6b6c1f838c0de5b954d3a8662316eaa75a977e2b695e391f7059e5a4387a8d", null ],
      [ "kLpuartMatchOnAndMatchOff", "group__lpuart__hal.html#gga62c6b6c1f838c0de5b954d3a8662316ea1eb8f8fd06dfbcdde0ffc06fa0c03534", null ],
      [ "kLpuartEnablesRwuOnDataMatch", "group__lpuart__hal.html#gga62c6b6c1f838c0de5b954d3a8662316eab8d6742b9234da5bf1a7bbc9a65cd44c", null ]
    ] ],
    [ "lpuart_ir_tx_pulsewidth_t", "group__lpuart__hal.html#ga139587519d0bfd73c856b32092e69778", [
      [ "kLpuartIrThreeSixteenthsWidth", "group__lpuart__hal.html#gga139587519d0bfd73c856b32092e69778aed05bef287ad8ffe117613f33d5cb4cb", null ],
      [ "kLpuartIrOneSixteenthWidth", "group__lpuart__hal.html#gga139587519d0bfd73c856b32092e69778a993f5ec1f62ccdb6e1eff34c3b7b2ab8", null ],
      [ "kLpuartIrOneThirtysecondsWidth", "group__lpuart__hal.html#gga139587519d0bfd73c856b32092e69778ab1a05a6d27d6b081699a99daafaea1c9", null ],
      [ "kLpuartIrOneFourthWidth", "group__lpuart__hal.html#gga139587519d0bfd73c856b32092e69778a95ccdbeb16c7d67e2bf45740dbbf13e8", null ]
    ] ],
    [ "lpuart_idle_char_t", "group__lpuart__hal.html#ga5b16bf3e4bb11c8ff7ca4b96266c61fa", [
      [ "kLpuart_1_IdleChar", "group__lpuart__hal.html#gga5b16bf3e4bb11c8ff7ca4b96266c61faae73af8765da5db761b3fd5ff99c1c38d", null ],
      [ "kLpuart_2_IdleChar", "group__lpuart__hal.html#gga5b16bf3e4bb11c8ff7ca4b96266c61faa030fa81c6247c6803253dd41f64c5cfd", null ],
      [ "kLpuart_4_IdleChar", "group__lpuart__hal.html#gga5b16bf3e4bb11c8ff7ca4b96266c61faa11ee0740a509f011a10b337d34bd2da3", null ],
      [ "kLpuart_8_IdleChar", "group__lpuart__hal.html#gga5b16bf3e4bb11c8ff7ca4b96266c61faa4fb812bea2b002a182094a3a05441366", null ],
      [ "kLpuart_16_IdleChar", "group__lpuart__hal.html#gga5b16bf3e4bb11c8ff7ca4b96266c61faaa31baca4fa79cead8aaffc291abc7023", null ],
      [ "kLpuart_32_IdleChar", "group__lpuart__hal.html#gga5b16bf3e4bb11c8ff7ca4b96266c61faa98e11d6922346d4b02f3074441c79c34", null ],
      [ "kLpuart_64_IdleChar", "group__lpuart__hal.html#gga5b16bf3e4bb11c8ff7ca4b96266c61faa1db37ba2ef625c926b014b4eac729f38", null ],
      [ "kLpuart_128_IdleChar", "group__lpuart__hal.html#gga5b16bf3e4bb11c8ff7ca4b96266c61faaa3691a0bf84e3bf76a777fd9e62fa3ac", null ]
    ] ],
    [ "lpuart_cts_source_t", "group__lpuart__hal.html#gab6dab1e3009c9b0af421fcfed1863460", [
      [ "kLpuartCtsSourcePin", "group__lpuart__hal.html#ggab6dab1e3009c9b0af421fcfed1863460a532d2f01ce945099aad5ee7bf53808c4", null ],
      [ "kLpuartCtsSourceInvertedReceiverMatch", "group__lpuart__hal.html#ggab6dab1e3009c9b0af421fcfed1863460aef0d5fda7103fedfe433066777d83498", null ]
    ] ],
    [ "lpuart_cts_config_t", "group__lpuart__hal.html#gac24f2c8fbc92406c30a7351d26694b12", [
      [ "kLpuartCtsSampledOnEachChar", "group__lpuart__hal.html#ggac24f2c8fbc92406c30a7351d26694b12ad4ea508f7e0c85fc816fe6b6a6d02bc5", null ],
      [ "kLpuartCtsSampledOnIdle", "group__lpuart__hal.html#ggac24f2c8fbc92406c30a7351d26694b12a006a7dfadb7861bfcb6b054a4b178628", null ]
    ] ],
    [ "lpuart_rx_idle_empty_config_t", "group__lpuart__hal.html#ga632fa544e8a79661d84283ce55a22df5", [
      [ "kLpuartRxidDisabled", "group__lpuart__hal.html#gga632fa544e8a79661d84283ce55a22df5a272b1a27bc6aa02578ffc9e02c05e51d", null ],
      [ "kLpuartRxidEnabledFor1Char", "group__lpuart__hal.html#gga632fa544e8a79661d84283ce55a22df5af8e962374f4e4255a728008870da8476", null ],
      [ "kLpuartRxidEnabledFor2Char", "group__lpuart__hal.html#gga632fa544e8a79661d84283ce55a22df5a7b2a70a185a8450928f26a1da7486cfa", null ],
      [ "kLpuartRxidEnabledFor4Char", "group__lpuart__hal.html#gga632fa544e8a79661d84283ce55a22df5a068a4785ba64bf96ec1f20d16dd75a84", null ],
      [ "kLpuartRxidEnabledFor8Char", "group__lpuart__hal.html#gga632fa544e8a79661d84283ce55a22df5ae75ba23df7cd461769f8432fe6783249", null ],
      [ "kLpuartRxidEnabledFor16Char", "group__lpuart__hal.html#gga632fa544e8a79661d84283ce55a22df5ae08ecfe12cf9331400b093a638b4a54a", null ],
      [ "kLpuartRxidEnabledFor32Char", "group__lpuart__hal.html#gga632fa544e8a79661d84283ce55a22df5a5cc190ab2cfa5938c2df5ae90db97101", null ],
      [ "kLpuartRxidEnabledFor64Char", "group__lpuart__hal.html#gga632fa544e8a79661d84283ce55a22df5a981a597236c72353354702fd11afb4cc", null ]
    ] ],
    [ "lpuart_status_flag_t", "group__lpuart__hal.html#ga945da88a9c973d13346683b78f8b8b5c", [
      [ "kLpuartTxDataRegEmpty", "group__lpuart__hal.html#gga945da88a9c973d13346683b78f8b8b5ca44651e0c7b2567ec923fc5cb5d17eebb", null ],
      [ "kLpuartTxComplete", "group__lpuart__hal.html#gga945da88a9c973d13346683b78f8b8b5cad221f7bf30576aeb71dfac964478d710", null ],
      [ "kLpuartRxDataRegFull", "group__lpuart__hal.html#gga945da88a9c973d13346683b78f8b8b5ca30789579561d89a78d801e8828f7cfea", null ],
      [ "kLpuartIdleLineDetect", "group__lpuart__hal.html#gga945da88a9c973d13346683b78f8b8b5ca74ee1ff9cc5a2f929a54b6bc2f3ac6eb", null ],
      [ "kLpuartRxOverrun", "group__lpuart__hal.html#gga945da88a9c973d13346683b78f8b8b5ca2f7e9d3e9c5bebe7f133779d184e4b07", null ],
      [ "kLpuartNoiseDetect", "group__lpuart__hal.html#gga945da88a9c973d13346683b78f8b8b5ca5156b5650190de97576b0d42e8d641fe", null ],
      [ "kLpuartFrameErr", "group__lpuart__hal.html#gga945da88a9c973d13346683b78f8b8b5cad52decf68d603d5e373a95963fbb05a8", null ],
      [ "kLpuartParityErr", "group__lpuart__hal.html#gga945da88a9c973d13346683b78f8b8b5caf945200e68e9824cf7c480f1ed680b4e", null ],
      [ "kLpuartLineBreakDetect", "group__lpuart__hal.html#gga945da88a9c973d13346683b78f8b8b5ca3a0de0667a772a03cae01e5a109b13a2", null ],
      [ "kLpuartRxActiveEdgeDetect", "group__lpuart__hal.html#gga945da88a9c973d13346683b78f8b8b5cabb7c62cbd08b57993c7118f95b9af1a9", null ],
      [ "kLpuartRxActive", "group__lpuart__hal.html#gga945da88a9c973d13346683b78f8b8b5cae01991cffb85dc23c18eadb756758fca", null ],
      [ "kLpuartNoiseInCurrentWord", "group__lpuart__hal.html#gga945da88a9c973d13346683b78f8b8b5cac3e7a882925151916df1c6beda115f50", null ],
      [ "kLpuartParityErrInCurrentWord", "group__lpuart__hal.html#gga945da88a9c973d13346683b78f8b8b5cab600218107b1a00bc2d4a8d9954d683c", null ]
    ] ],
    [ "lpuart_interrupt_t", "group__lpuart__hal.html#ga36121b0e89a81cf8e20876f0efbcc2ac", [
      [ "kLpuartIntLinBreakDetect", "group__lpuart__hal.html#gga36121b0e89a81cf8e20876f0efbcc2aca61b687481b897bddefcd8add043f1ec9", null ],
      [ "kLpuartIntRxActiveEdge", "group__lpuart__hal.html#gga36121b0e89a81cf8e20876f0efbcc2aca2cfffd7d246fa9fc1c6a29e62c8f6bba", null ],
      [ "kLpuartIntTxDataRegEmpty", "group__lpuart__hal.html#gga36121b0e89a81cf8e20876f0efbcc2acaeb693d86f2cc77614cf43c37490942ea", null ],
      [ "kLpuartIntTxComplete", "group__lpuart__hal.html#gga36121b0e89a81cf8e20876f0efbcc2aca584e5aa49df2bdbebe84f5be885dbe5f", null ],
      [ "kLpuartIntRxDataRegFull", "group__lpuart__hal.html#gga36121b0e89a81cf8e20876f0efbcc2aca75a118ea2966933c9edb8e6164a1c60c", null ],
      [ "kLpuartIntIdleLine", "group__lpuart__hal.html#gga36121b0e89a81cf8e20876f0efbcc2aca225cf780376fc736c8070c885dd1a940", null ],
      [ "kLpuartIntRxOverrun", "group__lpuart__hal.html#gga36121b0e89a81cf8e20876f0efbcc2acac7240664ffcb42dffbdae24a686c78e9", null ],
      [ "kLpuartIntNoiseErrFlag", "group__lpuart__hal.html#gga36121b0e89a81cf8e20876f0efbcc2aca7ac26186ca185dd71cca07b864f703ab", null ],
      [ "kLpuartIntFrameErrFlag", "group__lpuart__hal.html#gga36121b0e89a81cf8e20876f0efbcc2aca5b52b233d969c209b25e180e526a057d", null ],
      [ "kLpuartIntParityErrFlag", "group__lpuart__hal.html#gga36121b0e89a81cf8e20876f0efbcc2acabddc9b979bc167577b9a8a1fc0547d8d", null ]
    ] ],
    [ "LPUART_HAL_Init", "group__lpuart__hal.html#gade3dd06e4b6539d9c3a9d1e3297ab1f3", null ],
    [ "LPUART_HAL_SetTransmitterCmd", "group__lpuart__hal.html#gae529a36a93607abd1277248a293346f1", null ],
    [ "LPUART_HAL_GetTransmitterCmd", "group__lpuart__hal.html#ga4a0b467f1097cab08405a25771d0705e", null ],
    [ "LPUART_HAL_SetReceiverCmd", "group__lpuart__hal.html#ga91efe2cade3174aa0ed4ccbd954e40e1", null ],
    [ "LPUART_HAL_GetReceiverCmd", "group__lpuart__hal.html#ga0104ce91e058d03ebc6ef87c47119255", null ],
    [ "LPUART_HAL_SetBaudRate", "group__lpuart__hal.html#ga6840450afbd2c0bde7de31f3c29c8dab", null ],
    [ "LPUART_HAL_SetBaudRateDivisor", "group__lpuart__hal.html#gaa9d2de637a0aa15ab146aa5c7eda8467", null ],
    [ "LPUART_HAL_SetBitCountPerChar", "group__lpuart__hal.html#ga62d432b8f0ece71054df9fff05daffc9", null ],
    [ "LPUART_HAL_SetParityMode", "group__lpuart__hal.html#ga94db7f21b14492ed19d62aa431c93c06", null ],
    [ "LPUART_HAL_SetStopBitCount", "group__lpuart__hal.html#gaa26acd3ac4aac65f37027fead7bf9edc", null ],
    [ "LPUART_HAL_GetDataRegAddr", "group__lpuart__hal.html#gac87423b8c10847c91473851207a3d729", null ],
    [ "LPUART_HAL_SetIntMode", "group__lpuart__hal.html#ga764e6b84527fb9b26acf4e99c3e95a95", null ],
    [ "LPUART_HAL_GetIntMode", "group__lpuart__hal.html#ga30af9362c593d3a2020141d97d3b99cf", null ],
    [ "LPUART_HAL_Putchar", "group__lpuart__hal.html#ga03765dbf5682e06ef8166741b1983b7d", null ],
    [ "LPUART_HAL_Putchar9", "group__lpuart__hal.html#ga0c339a79f8cb43c9f9a1e97acbbd3b70", null ],
    [ "LPUART_HAL_Putchar10", "group__lpuart__hal.html#gad3fa7abc2fe4c880e9b4fba166bd057d", null ],
    [ "LPUART_HAL_Getchar", "group__lpuart__hal.html#ga7f15aa80eb89bc27911961ccdffcbc02", null ],
    [ "LPUART_HAL_Getchar9", "group__lpuart__hal.html#gab8a8217795ce69217052e044f00a9f43", null ],
    [ "LPUART_HAL_Getchar10", "group__lpuart__hal.html#ga59b94a5d9fe04198eae7c641550bc48d", null ],
    [ "LPUART_HAL_SendDataPolling", "group__lpuart__hal.html#ga6ffd1f8440cde6b499f7390c8e1d011e", null ],
    [ "LPUART_HAL_ReceiveDataPolling", "group__lpuart__hal.html#gaf4ec8bdd023889114d3b2a26207051a8", null ],
    [ "LPUART_HAL_GetStatusFlag", "group__lpuart__hal.html#gaa089f36ff0360eecb42a6994924dc14c", null ],
    [ "LPUART_HAL_ClearStatusFlag", "group__lpuart__hal.html#gaea909ecaa0f057633b2729c92cd0eca4", null ],
    [ "LPUART_HAL_SetIdleChar", "group__lpuart__hal.html#gae40642011b8482d38c2eea32feb4b616", null ],
    [ "LPUART_HAL_GetIdleChar", "group__lpuart__hal.html#ga9755dbd34a0472b3c53dcb26dd05e7c5", null ],
    [ "LPUART_HAL_IsCurrentDataWithNoise", "group__lpuart__hal.html#ga2698610e806e87bbb599a053b23aad1c", null ],
    [ "LPUART_HAL_IsCurrentDataWithFrameError", "group__lpuart__hal.html#ga1df8fa417ed3ed71fb07948c05b169ec", null ],
    [ "LPUART_HAL_SetTxSpecialChar", "group__lpuart__hal.html#ga09f8e39b5b8fe00d48be55cbc5a9d89d", null ],
    [ "LPUART_HAL_IsCurrentDataWithParityError", "group__lpuart__hal.html#ga307dfcd2cf5010362c04a4e2c46f506f", null ],
    [ "LPUART_HAL_IsReceiveBufferEmpty", "group__lpuart__hal.html#ga2bf81bef055491e41085feff31f64a69", null ],
    [ "LPUART_HAL_WasPreviousReceiverStateIdle", "group__lpuart__hal.html#ga4c114187b8f2d9a0d306af1f3085e4f0", null ],
    [ "LPUART_HAL_SetWaitModeOperation", "group__lpuart__hal.html#gab610e5c4ed87c83d21c989bef278b23f", null ],
    [ "LPUART_HAL_GetWaitModeOperation", "group__lpuart__hal.html#ga1b792e7757721a8cab9c80750f923d8f", null ],
    [ "LPUART_HAL_SetLoopbackCmd", "group__lpuart__hal.html#ga4154d0bc02bd9e27aee629b21143cccc", null ],
    [ "LPUART_HAL_SetSingleWireCmd", "group__lpuart__hal.html#gab1951a988a549dfcf2671fc4e3f7b111", null ],
    [ "LPUART_HAL_SetTxdirInSinglewireMode", "group__lpuart__hal.html#ga3b6ee3ecc9495486f31aba5753f063b3", null ],
    [ "LPUART_HAL_SetReceiverInStandbyMode", "group__lpuart__hal.html#gaedb09f21ad89e3ad85bf99f818ef5ee6", null ],
    [ "LPUART_HAL_PutReceiverInNormalMode", "group__lpuart__hal.html#ga7e69a69beb4a640af7e1470c1186e03e", null ],
    [ "LPUART_HAL_IsReceiverInStandby", "group__lpuart__hal.html#ga209b65075b173aa346bca7bb5ecabe0d", null ],
    [ "LPUART_HAL_SetReceiverWakeupMode", "group__lpuart__hal.html#ga0d0767662bbb0a41c9e5222fd30b9267", null ],
    [ "LPUART_HAL_GetReceiverWakeupMode", "group__lpuart__hal.html#gab344d62c7a692bf23b80d418a5a527f6", null ],
    [ "LPUART_HAL_SetIdleLineDetect", "group__lpuart__hal.html#gaefc2d5bc061a1ee3b172ee1b377c29ab", null ],
    [ "LPUART_HAL_SetBreakCharTransmitLength", "group__lpuart__hal.html#gadf67f86447b63ceba30a91bd11a755d4", null ],
    [ "LPUART_HAL_SetBreakCharDetectLength", "group__lpuart__hal.html#gae4444c304e036ce971bb62e5a6642963", null ],
    [ "LPUART_HAL_QueueBreakCharToSend", "group__lpuart__hal.html#ga5a3c38e6f3ba908ce2dd19eed80fc38e", null ],
    [ "LPUART_HAL_SetMatchAddressMode", "group__lpuart__hal.html#gaaacf756dfde3c35deef037ea47333d85", null ],
    [ "LPUART_HAL_SetMatchAddressReg1", "group__lpuart__hal.html#ga0c41819d8273f06eec799c3f7d1842b5", null ],
    [ "LPUART_HAL_SetMatchAddressReg2", "group__lpuart__hal.html#ga9fd91c4281fac96180cef2e75b35572a", null ],
    [ "LPUART_HAL_SetSendMsbFirstCmd", "group__lpuart__hal.html#ga41879efc602b32aac0272d70bf758145", null ],
    [ "LPUART_HAL_SetReceiveResyncCmd", "group__lpuart__hal.html#gafe75c9148b28d8e59b44968e184d373a", null ]
];
