wrh2/sputnik/Vendor Firmware/Kinetis SDK v.1.3.0 API Reference Manual/group__ltc__hal.js

var group__ltc__hal =
[
    [ "ltc_hal_pkha_mode_params_t", "group__ltc__hal.html#structltc__hal__pkha__mode__params__t", null ],
    [ "ltc_hal_mode_t", "group__ltc__hal.html#ga2dfa32a50b88d53968eb9bdf36eeaadc", null ],
    [ "ltc_status_err_shift_t", "group__ltc__hal.html#ga3e768537e0fa4545d5c5b775a97262e5", [
      [ "kStatus_LTC_ErrShift", "group__ltc__hal.html#gga3e768537e0fa4545d5c5b775a97262e5aa9d6320e2d5cbbc863c10168f70db90f", null ]
    ] ],
    [ "ltc_status_t", "group__ltc__hal.html#ga77df9228d44d536d88049fcdb13f05b9", [
      [ "kStatus_LTC_Error", "group__ltc__hal.html#gga77df9228d44d536d88049fcdb13f05b9a3741404133a53cc4821e93f2a4bca2e3", null ],
      [ "kStatus_LTC_ModeError", "group__ltc__hal.html#gga77df9228d44d536d88049fcdb13f05b9a281b9644a819a591360653fc87002aa8", null ],
      [ "kStatus_LTC_DataSizeError", "group__ltc__hal.html#gga77df9228d44d536d88049fcdb13f05b9a258b5bcadf6fa164c3fe99be440ca2a1", null ],
      [ "kStatus_LTC_KeySizeError", "group__ltc__hal.html#gga77df9228d44d536d88049fcdb13f05b9a8dc8f79ffad9617cb7a25df3538364a7", null ],
      [ "kStatus_LTC_PKHA_RegASzError", "group__ltc__hal.html#gga77df9228d44d536d88049fcdb13f05b9a3e8ce3e2072f4bba5922d2c3b25d84b9", null ],
      [ "kStatus_LTC_PKHA_RegBSzError", "group__ltc__hal.html#gga77df9228d44d536d88049fcdb13f05b9a65a4f678bcc011481c0ddc652bd7b814", null ],
      [ "kStatus_LTC_DataOutOfSeqError", "group__ltc__hal.html#gga77df9228d44d536d88049fcdb13f05b9abbffe65938ee2a3cabaec7d2e1c64b56", null ],
      [ "kStatus_LTC_PKHA_DivByZeroError", "group__ltc__hal.html#gga77df9228d44d536d88049fcdb13f05b9a65bbb6f5da50196e36c345cc377bacf3", null ],
      [ "kStatus_LTC_PKHA_ModulusEvenError", "group__ltc__hal.html#gga77df9228d44d536d88049fcdb13f05b9a1efff3608f9ec5ece587066fc5aff44f", null ],
      [ "kStatus_LTC_DES_KeyParityError", "group__ltc__hal.html#gga77df9228d44d536d88049fcdb13f05b9a45938ad25c91e6134a62166c601d6a29", null ],
      [ "kStatus_LTC_ICV_CheckFailed", "group__ltc__hal.html#gga77df9228d44d536d88049fcdb13f05b9a2e85de4d4cb89f3bfd80263f9a4d59ff", null ],
      [ "kStatus_LTC_InternalHwFailure", "group__ltc__hal.html#gga77df9228d44d536d88049fcdb13f05b9aae75ed2b3ebeb60230dbbf8b18a86cbd", null ],
      [ "kStatus_LTC_CCM_AadSzError", "group__ltc__hal.html#gga77df9228d44d536d88049fcdb13f05b9ab2b219853c8b392db578857f3e4145fd", null ],
      [ "kStatus_LTC_CCM_InvalidCryptoSel", "group__ltc__hal.html#gga77df9228d44d536d88049fcdb13f05b9ac50d6bdd5f7a76b672ce9eaca74076cc", null ],
      [ "kStatus_LTC_OSAError", "group__ltc__hal.html#gga77df9228d44d536d88049fcdb13f05b9a58ff6c909075be6bac91740349ee6295", null ]
    ] ],
    [ "ltc_hal_algorithm_t", "group__ltc__hal.html#ga42c4f413ccb32adae68bffab4c537b58", null ],
    [ "ltc_hal_pkha_reg_area_t", "group__ltc__hal.html#ga2e4e6cc8531bdb04f7e1f521960844a7", null ],
    [ "ltc_hal_pkha_clr_quad_area_t", "group__ltc__hal.html#gaf89e5cf46804e598c3432e90150c77e6", null ],
    [ "ltc_hal_pkha_quad_area_t", "group__ltc__hal.html#gac0abc74205579d49d13049f64116875b", null ],
    [ "ltc_hal_pkha_montgomery_form_t", "group__ltc__hal.html#ga7d5377c95c2d08fe0df2ab357c43f353", null ],
    [ "ltc_hal_pkha_f2m_t", "group__ltc__hal.html#gac84409cb5b336126a4039a92160e3223", [
      [ "kLTC_PKHA_Integer_Arith", "group__ltc__hal.html#ggac84409cb5b336126a4039a92160e3223a62d29367f16342b4c0462b317e8e0472", null ],
      [ "kLTC_PKHA_F2M_Arith", "group__ltc__hal.html#ggac84409cb5b336126a4039a92160e3223a3e145a8dc64afbb466b8f8c61f1ae401", null ]
    ] ],
    [ "ltc_hal_pkha_r2_t", "group__ltc__hal.html#ga4caea4bcbde03cfe60f56a50732f66d7", [
      [ "kLTC_PKHA_R2_Calc", "group__ltc__hal.html#gga4caea4bcbde03cfe60f56a50732f66d7aee563749614c99f86ae9560dd2003f46", null ],
      [ "kLTC_PKHA_R2_Input", "group__ltc__hal.html#gga4caea4bcbde03cfe60f56a50732f66d7ab13e5502cde06c18b5c438be0cbf81af", null ]
    ] ],
    [ "ltc_hal_pkha_timing_t", "group__ltc__hal.html#ga3a73363280af36b83c81cadc895ecae4", null ],
    [ "ltc_hal_pkha_output_reg_t", "group__ltc__hal.html#ga4a8d538d36cece370fc5172cae8350b2", null ],
    [ "ltc_hal_pkha_func_t", "group__ltc__hal.html#ga65682d0ece15db2cfe43221f1bced7f0", [
      [ "kLTC_PKHA_Arith_ModAdd", "group__ltc__hal.html#gga65682d0ece15db2cfe43221f1bced7f0a906782eb68f732738a431dd2a9575f60", null ],
      [ "kLTC_PKHA_Arith_ModSub1", "group__ltc__hal.html#gga65682d0ece15db2cfe43221f1bced7f0a55c071baecb029a0577536b5172c3e88", null ],
      [ "kLTC_PKHA_Arith_ModSub2", "group__ltc__hal.html#gga65682d0ece15db2cfe43221f1bced7f0a9dfa4fe1c70b111c80c5222888ca7606", null ],
      [ "kLTC_PKHA_Arith_ModMul", "group__ltc__hal.html#gga65682d0ece15db2cfe43221f1bced7f0ae3784a7c3060fa4937d1cba0ac6903a0", null ],
      [ "kLTC_PKHA_Arith_ModExp", "group__ltc__hal.html#gga65682d0ece15db2cfe43221f1bced7f0aa84d91fd4b0b1ba81c84f0cf55862865", null ],
      [ "kLTC_PKHA_Arith_ModRed", "group__ltc__hal.html#gga65682d0ece15db2cfe43221f1bced7f0ab142a0519773fa735a0284d31187bc26", null ],
      [ "kLTC_PKHA_Arith_ModInv", "group__ltc__hal.html#gga65682d0ece15db2cfe43221f1bced7f0a90526d7e5af3867d39284b15ac224a13", null ],
      [ "kLTC_PKHA_Arith_ECCAdd", "group__ltc__hal.html#gga65682d0ece15db2cfe43221f1bced7f0a76526ae3d7c46d259fa2e37b50b30cb1", null ],
      [ "kLTC_PKHA_Arith_ECCDouble", "group__ltc__hal.html#gga65682d0ece15db2cfe43221f1bced7f0a78028411d7bef57b7481a27c5204cac5", null ],
      [ "kLTC_PKHA_Arith_ECCMul", "group__ltc__hal.html#gga65682d0ece15db2cfe43221f1bced7f0a475410a05ce74d75d5ad6ea3443e6ceb", null ],
      [ "kLTC_PKHA_Arith_ModR2", "group__ltc__hal.html#gga65682d0ece15db2cfe43221f1bced7f0abaa815f6f1a08b13d09495d3865d9811", null ],
      [ "kLTC_PKHA_Arith_GCD", "group__ltc__hal.html#gga65682d0ece15db2cfe43221f1bced7f0aacc95dba7b7cb6d090ae74034796fc67", null ],
      [ "kLTC_PKHA_Arith_PrimalityTest", "group__ltc__hal.html#gga65682d0ece15db2cfe43221f1bced7f0ab58695d24367838e594046167b2f6655", null ]
    ] ],
    [ "ltc_hal_mode_encrypt_t", "group__ltc__hal.html#gaec038f86ff209898416636cd628803e1", null ],
    [ "ltc_hal_mode_icv_check_t", "group__ltc__hal.html#gac013e6152c01799ac7c691d251e25aa2", null ],
    [ "ltc_hal_mode_algorithm_state_t", "group__ltc__hal.html#ga2475ac12180a49777e1828779ca92e47", null ],
    [ "ltc_hal_mode_symmetric_alg_t", "group__ltc__hal.html#ga429de2cf86c17397c7cdefc6a6e7fee7", null ],
    [ "ltc_hal_mode_decrypt_key_t", "group__ltc__hal.html#ga81e65ebfb88051371dc2279aae18911c", null ],
    [ "ltc_hal_cmd_t", "group__ltc__hal.html#ga4e696668dc8c53a72fe2c9a357a3cc80", [
      [ "kLTCCmd_ResetAll", "group__ltc__hal.html#gga4e696668dc8c53a72fe2c9a357a3cc80a6cc914eb8d245d5a2822fa6f68e73a3e", null ],
      [ "kLTCCmd_ResetAES", "group__ltc__hal.html#gga4e696668dc8c53a72fe2c9a357a3cc80ae76cd86b164124337b1b46d6a826dd34", null ],
      [ "kLTCCmd_ResetDES", "group__ltc__hal.html#gga4e696668dc8c53a72fe2c9a357a3cc80ae545eaf4b14ec6a9df7e735f8a474cd6", null ],
      [ "kLTCCmd_ResetPKHA", "group__ltc__hal.html#gga4e696668dc8c53a72fe2c9a357a3cc80a6d79347c36de643a215a08aed8c1531d", null ]
    ] ],
    [ "ltc_hal_key_lock_t", "group__ltc__hal.html#ga7fa70b50a0af56dd887022b77bbd4a75", [
      [ "kLTCCtrl_KeyRegisterReadable", "group__ltc__hal.html#gga7fa70b50a0af56dd887022b77bbd4a75a7f5871942307d7ffdfaa5d1bd90aeb92", null ],
      [ "kLTCCtrl_KeyRegisterNotReadable", "group__ltc__hal.html#gga7fa70b50a0af56dd887022b77bbd4a75aa31aa8e9e6bf3c6454161733c7aee505", null ]
    ] ],
    [ "ltc_hal_byte_swap_t", "group__ltc__hal.html#ga612d892a4671de8cf4bb9f62f572842d", [
      [ "kLTCCtrl_ByteNoSwap", "group__ltc__hal.html#gga612d892a4671de8cf4bb9f62f572842dac02a8f560854d96d8fc481b972bb9c22", null ],
      [ "kLTCCtrl_ByteSwap", "group__ltc__hal.html#gga612d892a4671de8cf4bb9f62f572842da777df625b3db928b68c7b03b40d9ff79", null ]
    ] ],
    [ "ltc_hal_fifo_dma_size_t", "group__ltc__hal.html#ga8493ab084f41f47bf2288bf32a173d97", [
      [ "kLTCCtrl_DMASize_1byte", "group__ltc__hal.html#gga8493ab084f41f47bf2288bf32a173d97ae78aaa7ec94c68554e3407fde45c62b2", null ],
      [ "kLTCCtrl_DMASize_4byte", "group__ltc__hal.html#gga8493ab084f41f47bf2288bf32a173d97afaa551ac79fd5e7877668a480cc47c10", null ]
    ] ],
    [ "ltc_hal_dma_enable_t", "group__ltc__hal.html#gac821311faa2c25f13ec0b4ea783e21d1", [
      [ "kLTCCtrl_DMA_Disabled", "group__ltc__hal.html#ggac821311faa2c25f13ec0b4ea783e21d1a7ce605651b866f6b0a6738170e623e8b", null ],
      [ "kLTCCtrl_DMA_Enabled", "group__ltc__hal.html#ggac821311faa2c25f13ec0b4ea783e21d1a243e986ed78186b6d34f76d9cd839554", null ]
    ] ],
    [ "ltc_hal_isr_mask_t", "group__ltc__hal.html#gaa18309bec8d89fd5eaccd21f97c79f3f", [
      [ "kLTCCtrl_ISR_Not_Masked", "group__ltc__hal.html#ggaa18309bec8d89fd5eaccd21f97c79f3fab0548650429940f8957b40e241325296", null ],
      [ "kLTCCtrl_ISR_Masked", "group__ltc__hal.html#ggaa18309bec8d89fd5eaccd21f97c79f3fa3ecd71ba33bd9fbbee2967be9fd161ab", null ]
    ] ],
    [ "ltc_hal_clear_written_t", "group__ltc__hal.html#ga815c75584c1bc17844a9a053a29b43d7", null ],
    [ "ltc_hal_status_flag_t", "group__ltc__hal.html#ga1afc3c45f1b8c303a1f389477a136026", null ],
    [ "ltc_hal_error_status_flag_t", "group__ltc__hal.html#gab43f304d0b356c4a5d740b58375b37ea", null ],
    [ "ltc_hal_fifo_status_t", "group__ltc__hal.html#gab4e5215e89ee12b38f758c4302b32b74", [
      [ "kLTCFIFO_OutputFifoFull", "group__ltc__hal.html#ggab4e5215e89ee12b38f758c4302b32b74a1ff325694bb50632b64640e9c33eaed4", null ],
      [ "kLTCFIFO_OutputFifoLevel", "group__ltc__hal.html#ggab4e5215e89ee12b38f758c4302b32b74aac22a0753f2fc0829ff42d8bb9cd85e4", null ],
      [ "kLTCFIFO_InputFifoFull", "group__ltc__hal.html#ggab4e5215e89ee12b38f758c4302b32b74aa487fc58b262c1b6e8156d4716e79507", null ],
      [ "kLTCFIFO_InputFifoLevel", "group__ltc__hal.html#ggab4e5215e89ee12b38f758c4302b32b74a3b836431a6022b3f0143b4294e58190c", null ]
    ] ],
    [ "LTC_HAL_GetWordFromUnaligned", "group__ltc__hal.html#gac5023113d29d9024c7088b4b0665b3f9", null ],
    [ "LTC_HAL_SetUnalignedFromWord", "group__ltc__hal.html#ga1ce73edc2b547a58f6033e70921d0169", null ],
    [ "LTC_HAL_Init", "group__ltc__hal.html#ga534a0e9232fed99c8c52b8f183058764", null ],
    [ "LTC_HAL_ModeSetAlgorithm", "group__ltc__hal.html#gad20168a4b9a1244d54caf34dbbe470d7", null ],
    [ "LTC_HAL_ModeSetEncrypt", "group__ltc__hal.html#gaac2f67ee0e6a698fafbc0361723fed87", null ],
    [ "LTC_HAL_ModeGetEncrypt", "group__ltc__hal.html#ga1571aca4c80567f7549e98005c639f41", null ],
    [ "LTC_HAL_ModeSetICVTest", "group__ltc__hal.html#ga5fabdb8a15eb2a90c9988b5353b2b8b0", null ],
    [ "LTC_HAL_ModeSetAlgorithmState", "group__ltc__hal.html#ga5674ffb1097b62a97fc7409ba33dbe0e", null ],
    [ "LTC_HAL_ModeGetAlgorithmState", "group__ltc__hal.html#gade4222364b5cc4890cff2cd927efbffa", null ],
    [ "LTC_HAL_ModeSetSymmetricAlg", "group__ltc__hal.html#gaa2649fb04382f60203e8773407547bc7", null ],
    [ "LTC_HAL_ModeSetDecryptKey", "group__ltc__hal.html#ga53128e74b9c67fc3bea2f8b7f08539fc", null ],
    [ "LTC_HAL_PKHA_ModeSetFunc", "group__ltc__hal.html#gadcafc09bd6b38a94b4dac4faf93dd122", null ],
    [ "LTC_HAL_PKHA_ModeSetMontgomeryInput", "group__ltc__hal.html#gaf633a02325e5507518d4d7453ba79ddd", null ],
    [ "LTC_HAL_PKHA_ModeSetMontgomeryOutput", "group__ltc__hal.html#ga52842756bf4154af1c9707b8d71f7572", null ],
    [ "LTC_HAL_PKHA_ModeSetF2M", "group__ltc__hal.html#gac5cc1be148efcd1790b538130119a663", null ],
    [ "LTC_HAL_PKHA_ModeSetR2", "group__ltc__hal.html#ga73a9deb6ccc0b12ab0e2e13516ff6423", null ],
    [ "LTC_HAL_PKHA_ModeSetTimingEqual", "group__ltc__hal.html#gaccc08787f4ee8c97dc02f6ddc12fde2c", null ],
    [ "LTC_HAL_PKHA_ModeSetOutput", "group__ltc__hal.html#ga7057af39ece0a7f6da271c900cde3e0f", null ],
    [ "LTC_HAL_PKHA_ModeSetRamArea", "group__ltc__hal.html#ga8da0f0839f1436623afbb15b7840dae8", null ],
    [ "LTC_HAL_PKHA_ModeSetQuadArea", "group__ltc__hal.html#ga4ed6cbfed29e4c6193312d2b040bfe79", null ],
    [ "LTC_HAL_WriteMode", "group__ltc__hal.html#ga0d420463d8be1166085e9d44e22b0d99", null ],
    [ "LTC_HAL_ReadMode", "group__ltc__hal.html#gacd49d19692f5ade06fb3594e3127fda1", null ],
    [ "LTC_HAL_GetKeySize", "group__ltc__hal.html#gad0a51bc472e5fb7fb62fa46a2d0b8e9d", null ],
    [ "LTC_HAL_SetKeySize", "group__ltc__hal.html#gafda8d4061937a5335c53f520e5ec2719", null ],
    [ "LTC_HAL_GetDataSize", "group__ltc__hal.html#ga22e386fe6dfc98c9dabd860a1f6f34c7", null ],
    [ "LTC_HAL_SetDataSize", "group__ltc__hal.html#gaec781a0cff31931a6ccdc2a9ee51406e", null ],
    [ "LTC_HAL_GetICVSize", "group__ltc__hal.html#gaae33ef1e5497b6c638a3eed2973efc27", null ],
    [ "LTC_HAL_SetICVSize", "group__ltc__hal.html#gaa655e4bd181993b22e144f52af3638d4", null ],
    [ "LTC_HAL_Command", "group__ltc__hal.html#ga922ad415b3089b022276c540a8428993", null ],
    [ "LTC_HAL_SetInterruptMask", "group__ltc__hal.html#gaf3842a0def4f68ff1be8348b073e9b40", null ],
    [ "LTC_HAL_SetPKHAEnableDMA", "group__ltc__hal.html#gaea6c0fd1279096737d458f6ec77933db", null ],
    [ "LTC_HAL_SetInputFIFOEnableDMA", "group__ltc__hal.html#ga21445bb532d0ef9dd60601287808a6cb", null ],
    [ "LTC_HAL_SetInputFIFORequestSizeDMA", "group__ltc__hal.html#gad382775b19ca4caa84505b9f165369af", null ],
    [ "LTC_HAL_SetOutputFIFOEnableDMA", "group__ltc__hal.html#ga832a3ba77cd267ec5e8bc7c2af7d2400", null ],
    [ "LTC_HAL_SetOutputFIFORequestSizeDMA", "group__ltc__hal.html#gab3d7e5d2f10548591c41bd615f5c74d6", null ],
    [ "LTC_HAL_SetInputFIFOByteSwap", "group__ltc__hal.html#ga8c77e618310b9d4e30b772daaf70c9a5", null ],
    [ "LTC_HAL_SetOutputFIFOByteSwap", "group__ltc__hal.html#gadbf1b951be764bead0f01f0b95504923", null ],
    [ "LTC_HAL_SetKeyRegInputByteSwap", "group__ltc__hal.html#gaf68dd900c1610287a362256f3a1bc803", null ],
    [ "LTC_HAL_SetKeyRegOutputByteSwap", "group__ltc__hal.html#ga24ed08e984161a4904f71c1be3dc92ec", null ],
    [ "LTC_HAL_SetCtxRegInputByteSwap", "group__ltc__hal.html#ga7becd7787fcaa41b851d5bf3b94d58d1", null ],
    [ "LTC_HAL_SetCtxRegOutputByteSwap", "group__ltc__hal.html#gae21cd2eb6621ed2ff31e7dbfbfebd8e9", null ],
    [ "LTC_HAL_SetKeyRegAccessLock", "group__ltc__hal.html#ga62552a20e4a7f9ea45ed6e7e03005e0b", null ],
    [ "LTC_HAL_ClearWritten", "group__ltc__hal.html#gab413931d120547ddd5188c428fcf6455", null ],
    [ "LTC_HAL_GetStatusFlag", "group__ltc__hal.html#gacf11d6b3077c3436f09b802bd7330c21", null ],
    [ "LTC_HAL_ClearDoneInterruptStatus", "group__ltc__hal.html#gaa74614dd26062f45726d19cb021c05f7", null ],
    [ "LTC_HAL_GetStatusFlagMasked", "group__ltc__hal.html#ga41f8379a8bf024d63ed2560bea6fb89a", null ],
    [ "LTC_HAL_GetErrorStatusFlag", "group__ltc__hal.html#ga21a3e72ee3d52cdb4ed25f12199b7395", null ],
    [ "LTC_HAL_GetErrorStatusFlagMasked", "group__ltc__hal.html#gae196a2b5c8c16ffd2501e555d8a5b758", null ],
    [ "LTC_HAL_GetAADSize", "group__ltc__hal.html#ga78ec519b4aceeb9b7137d148887253b6", null ],
    [ "LTC_HAL_SetAADSize", "group__ltc__hal.html#ga8e431f8f227c7e85f311323489258f41", null ],
    [ "LTC_HAL_GetIVSize", "group__ltc__hal.html#ga622b86107d6eff663fb59f554e72f7b9", null ],
    [ "LTC_HAL_SetIVSize", "group__ltc__hal.html#gac8ff3950486697d8ca547ef9fb510e76", null ],
    [ "LTC_HAL_SetDPAMaskSeed", "group__ltc__hal.html#ga79010c7d70b6eebfb54dfd3f78dc0a00", null ],
    [ "LTC_HAL_PKHA_SetASize", "group__ltc__hal.html#gaf932e0ef99a0d1bc2ee185ba18f8788a", null ],
    [ "LTC_HAL_PKHA_GetASize", "group__ltc__hal.html#ga35ec480a3eb6ee00d1ec8eee3007c3cd", null ],
    [ "LTC_HAL_PKHA_SetBSize", "group__ltc__hal.html#gacf40f44f3d2bdc8c6962f361aeb86b4a", null ],
    [ "LTC_HAL_PKHA_GetBSize", "group__ltc__hal.html#gaf1d80ce17debf047d22d37d89a146df8", null ],
    [ "LTC_HAL_PKHA_SetNSize", "group__ltc__hal.html#gaea9ccdb2045ba33c3d3f326528c13c12", null ],
    [ "LTC_HAL_PKHA_GetNSize", "group__ltc__hal.html#gab48972df9a9a77d1edde6ebd2f85b5f0", null ],
    [ "LTC_HAL_PKHA_SetESize", "group__ltc__hal.html#gabb21f49f21343795592ffdbbd92158b6", null ],
    [ "LTC_HAL_PKHA_GetESize", "group__ltc__hal.html#ga61c3a31f17cea02dfcf7d6f4838076ca", null ],
    [ "LTC_HAL_SetContext", "group__ltc__hal.html#ga350af2145b96263cde811ed0b33a1a9d", null ],
    [ "LTC_HAL_GetContext", "group__ltc__hal.html#gaf6150cf96cb71f356bbccdaaf2affd78", null ],
    [ "LTC_HAL_SetKey", "group__ltc__hal.html#ga2382c37c1b64ca26a6e7ddb70966eb48", null ],
    [ "LTC_HAL_GetKey", "group__ltc__hal.html#ga194138e48c7615e855ff0884ece509eb", null ],
    [ "LTC_HAL_InputFIFOGetLevel", "group__ltc__hal.html#ga2781817aae5431bf69778fc97b18a624", null ],
    [ "LTC_HAL_InputFIFOFull", "group__ltc__hal.html#gaf12210df0164319aae51fbd102f2adcb", null ],
    [ "LTC_HAL_OutputFIFOGetLevel", "group__ltc__hal.html#ga1acf6111a375cefe8993fd52dd7e90ec", null ],
    [ "LTC_HAL_OutputFIFOFull", "group__ltc__hal.html#ga3b2f8d4d46dcf2d1252a5edc159e8266", null ],
    [ "LTC_HAL_WriteInputFIFO", "group__ltc__hal.html#gad3e39e9b65e8d0eec3ebaa1fa1270e72", null ],
    [ "LTC_HAL_ReadOutputFIFO", "group__ltc__hal.html#ga2dc5007e03767846ca7f06cc8e1255be", null ],
    [ "LTC_HAL_GetStatusFIFO", "group__ltc__hal.html#gab31041c467b722a3fa260c4167ff8c21", null ],
    [ "LTC_HAL_WritePKA", "group__ltc__hal.html#gad7dc5664272fa733241362247db0723b", null ],
    [ "LTC_HAL_WriteSizedPKA", "group__ltc__hal.html#ga0d6b5768377c4609fc5c1d3177c7ce0f", null ],
    [ "LTC_HAL_ReadPKA", "group__ltc__hal.html#gaac1530db63fd8322ebd7cf45e88ce10a", null ],
    [ "LTC_HAL_WritePKB", "group__ltc__hal.html#ga0f14dcfbb5cf9d1e2b23afc05cdb87fa", null ],
    [ "LTC_HAL_WriteSizedPKB", "group__ltc__hal.html#ga77940b59c08e48570d2545d6f38063ac", null ],
    [ "LTC_HAL_ReadPKB", "group__ltc__hal.html#ga16e9f3ff45c26c14d8e977c5ed519488", null ],
    [ "LTC_HAL_WritePKN", "group__ltc__hal.html#gad9b4fa0d00b89b49af107bf146f5a498", null ],
    [ "LTC_HAL_WriteSizedPKN", "group__ltc__hal.html#gaff03d17720ca65256fbee54f53262121", null ],
    [ "LTC_HAL_ReadPKN", "group__ltc__hal.html#ga62af839f83a45eeb1c7a79de184be7dd", null ],
    [ "LTC_HAL_WritePKE", "group__ltc__hal.html#ga12bde84a9c7e06ed800d6b0864f31408", null ],
    [ "LTC_HAL_WriteSizedPKE", "group__ltc__hal.html#gaf0b1b32089a81cb614b1e330a2751b0d", null ],
    [ "LTC_HAL_ReadPKE", "group__ltc__hal.html#gaf5648594f0ef11d01c226a89c212d9cc", null ],
    [ "LTC_HAL_PKHA_ModeSetSrcRegCopy", "group__ltc__hal.html#gafa908f50144d9161610b1eb3b0693d94", null ],
    [ "LTC_HAL_PKHA_ModeSetDstRegCopy", "group__ltc__hal.html#gaccbf3c02e1f1e7d995f35fe6b4a33927", null ],
    [ "LTC_HAL_PKHA_ModeSetSrcSegCopy", "group__ltc__hal.html#ga23556e863fe8f3ec1afb669bbb70d6f6", null ],
    [ "LTC_HAL_PKHA_ModeSetDstSegCopy", "group__ltc__hal.html#gae1930bcaacf21c2a9ff0ae89dfac8ec1", null ]
];
