wrh2/sputnik/Vendor Firmware/Kinetis SDK v.1.3.0 API Reference Manual/group__mcg__hal.js

var group__mcg__hal =
[
    [ "MCG_MODE_CHECK_PARAM", "group__mcg__hal.html#gabce4c498d5df06e14d7360532587b270", null ],
    [ "_mcg_constant", "group__mcg__hal.html#gaadd12e80f98bc09e584342e08503ba56", null ],
    [ "mcg_fll_src_t", "group__mcg__hal.html#ga81ba0b535de3a51235d2f98030b13ff9", [
      [ "kMcgFllSrcExternal", "group__mcg__hal.html#gga81ba0b535de3a51235d2f98030b13ff9a3e6f1231b5d908d6151f30fc5872cda8", null ],
      [ "kMcgFllSrcInternal", "group__mcg__hal.html#gga81ba0b535de3a51235d2f98030b13ff9a0caf053d52602af6dee9961a1f7f0a5d", null ]
    ] ],
    [ "osc_range_t", "group__mcg__hal.html#gae4172a4914fa6e96133ed86d1e0484f8", [
      [ "kOscRangeLow", "group__mcglite__hal.html#ggae4172a4914fa6e96133ed86d1e0484f8aaaace19a42c5abe3ab1c618274c7b304", null ],
      [ "kOscRangeHigh", "group__mcglite__hal.html#ggae4172a4914fa6e96133ed86d1e0484f8ab4becd6da53ab13046ea007f140e919b", null ],
      [ "kOscRangeVeryHigh", "group__mcglite__hal.html#ggae4172a4914fa6e96133ed86d1e0484f8a7f1cad01e8a164a9176832adf11684a1", null ],
      [ "kOscRangeVeryHigh1", "group__mcglite__hal.html#ggae4172a4914fa6e96133ed86d1e0484f8a51119ba1f937fc9b9daf9f22ec309f43", null ],
      [ "kOscRangeLow", "group__mcglite__hal.html#ggae4172a4914fa6e96133ed86d1e0484f8aaaace19a42c5abe3ab1c618274c7b304", null ],
      [ "kOscRangeHigh", "group__mcglite__hal.html#ggae4172a4914fa6e96133ed86d1e0484f8ab4becd6da53ab13046ea007f140e919b", null ],
      [ "kOscRangeVeryHigh", "group__mcglite__hal.html#ggae4172a4914fa6e96133ed86d1e0484f8a7f1cad01e8a164a9176832adf11684a1", null ],
      [ "kOscRangeVeryHigh1", "group__mcglite__hal.html#ggae4172a4914fa6e96133ed86d1e0484f8a51119ba1f937fc9b9daf9f22ec309f43", null ]
    ] ],
    [ "osc_gain_t", "group__mcg__hal.html#ga43f8c5b27ab6f1737bf99adc18d672d0", [
      [ "kOscGainLow", "group__mcglite__hal.html#gga43f8c5b27ab6f1737bf99adc18d672d0acd4ca790b914aebc6fc652e530d34b3c", null ],
      [ "kOscGainHigh", "group__mcglite__hal.html#gga43f8c5b27ab6f1737bf99adc18d672d0a7898363c930c80bf2c5f9449c7cfdde1", null ],
      [ "kOscGainLow", "group__mcglite__hal.html#gga43f8c5b27ab6f1737bf99adc18d672d0acd4ca790b914aebc6fc652e530d34b3c", null ],
      [ "kOscGainHigh", "group__mcglite__hal.html#gga43f8c5b27ab6f1737bf99adc18d672d0a7898363c930c80bf2c5f9449c7cfdde1", null ]
    ] ],
    [ "osc_src_t", "group__mcg__hal.html#ga931f75a5969f2dda1abaa7ee1b2fb022", [
      [ "kOscSrcExt", "group__mcglite__hal.html#gga931f75a5969f2dda1abaa7ee1b2fb022acd7e4eca27cec23f150a462a09b7c4ae", null ],
      [ "kOscSrcOsc", "group__mcglite__hal.html#gga931f75a5969f2dda1abaa7ee1b2fb022aa5cc2db16b236ad514b83ec8235d4056", null ],
      [ "kOscSrcExt", "group__mcglite__hal.html#gga931f75a5969f2dda1abaa7ee1b2fb022acd7e4eca27cec23f150a462a09b7c4ae", null ],
      [ "kOscSrcOsc", "group__mcglite__hal.html#gga931f75a5969f2dda1abaa7ee1b2fb022aa5cc2db16b236ad514b83ec8235d4056", null ]
    ] ],
    [ "mcg_irc_mode_t", "group__mcg__hal.html#ga5cda306cd661f277d6d285c00a7d2283", [
      [ "kMcgIrcSlow", "group__mcg__hal.html#gga5cda306cd661f277d6d285c00a7d2283a96135f8aeed7326da7818f401927399b", null ],
      [ "kMcgIrcFast", "group__mcg__hal.html#gga5cda306cd661f277d6d285c00a7d2283a4e9ebfba519ab39e380163c127e2e222", null ]
    ] ],
    [ "mcg_dmx32_select_t", "group__mcg__hal.html#ga5153395dffc26a50637a3d6835ab11a0", [
      [ "kMcgDmx32Default", "group__mcg__hal.html#gga5153395dffc26a50637a3d6835ab11a0a83ff4a7a0a1795761faa143030f60519", null ],
      [ "kMcgDmx32Fine", "group__mcg__hal.html#gga5153395dffc26a50637a3d6835ab11a0a45aaff24cd29320a0b838c268c20ade7", null ]
    ] ],
    [ "mcg_dco_range_select_t", "group__mcg__hal.html#ga5027dcf86bb5d16d708caef0df666e12", [
      [ "kMcgDcoRangeSelLow", "group__mcg__hal.html#gga5027dcf86bb5d16d708caef0df666e12ad4bb068bfbe404d6fe911e24a5d94906", null ],
      [ "kMcgDcoRangeSelMid", "group__mcg__hal.html#gga5027dcf86bb5d16d708caef0df666e12ad2fc158fad0a0226f3e5f4d10102207e", null ],
      [ "kMcgDcoRangeSelMidHigh", "group__mcg__hal.html#gga5027dcf86bb5d16d708caef0df666e12aae0485b1a72fb7054d0d2c731a5fa842", null ],
      [ "kMcgDcoRangeSelHigh", "group__mcg__hal.html#gga5027dcf86bb5d16d708caef0df666e12afb43340441422bcc0ec7ca2969966e77", null ]
    ] ],
    [ "mcg_pll_ref_mode_t", "group__mcg__hal.html#gabf3009249d264a74fae977b255c1fd8c", [
      [ "kMcgPllRefOsc0", "group__mcg__hal.html#ggabf3009249d264a74fae977b255c1fd8cabe2d970e2663a8af77cf64f45df34691", null ],
      [ "kMcgPllRefOsc1", "group__mcg__hal.html#ggabf3009249d264a74fae977b255c1fd8ca69708d9700aea7922084a1142e6fb7e3", null ]
    ] ],
    [ "mcg_clkout_src_t", "group__mcg__hal.html#gad7d72119e0eb16ccbe4619d932414590", [
      [ "kMcgClkOutSrcOut", "group__mcg__hal.html#ggad7d72119e0eb16ccbe4619d932414590a35022e8bed9b1e83d87b1c4bebb1dd02", null ],
      [ "kMcgClkOutSrcInternal", "group__mcg__hal.html#ggad7d72119e0eb16ccbe4619d932414590a2d062bd7d4a18742022f30e1859dcfbd", null ],
      [ "kMcgClkOutSrcExternal", "group__mcg__hal.html#ggad7d72119e0eb16ccbe4619d932414590a29a5ae6c0bd5d992eba71db579085b54", null ]
    ] ],
    [ "mcg_clkout_stat_t", "group__mcg__hal.html#ga167be91e3b9018ec9c7fc4e13dd915e4", [
      [ "kMcgClkOutStatFll", "group__mcg__hal.html#gga167be91e3b9018ec9c7fc4e13dd915e4ae0d5cde272dbef116cdc2b689483a981", null ],
      [ "kMcgClkOutStatInternal", "group__mcg__hal.html#gga167be91e3b9018ec9c7fc4e13dd915e4a09b538596608994f27e01bf79e6e479a", null ],
      [ "kMcgClkOutStatExternal", "group__mcg__hal.html#gga167be91e3b9018ec9c7fc4e13dd915e4a6c9cb8e6606ab8e35a6f88724def9780", null ],
      [ "kMcgClkOutStatPll", "group__mcg__hal.html#gga167be91e3b9018ec9c7fc4e13dd915e4ac69a8d1e451092258720dc3622a9f3ac", null ]
    ] ],
    [ "mcg_atm_select_t", "group__mcg__hal.html#ga7b0b118f75aaeed3003e43627155b9ce", [
      [ "kMcgAtmSel32k", "group__mcg__hal.html#gga7b0b118f75aaeed3003e43627155b9cea96f775e97b48f147863962e17bae5297", null ],
      [ "kMcgAtmSel4m", "group__mcg__hal.html#gga7b0b118f75aaeed3003e43627155b9cea4fe153aabe22cc6f180a8f1dcfcee05a", null ]
    ] ],
    [ "mcg_oscsel_select_t", "group__mcg__hal.html#ga4d9cd137b2d8cd59edf124a24e1b5c63", [
      [ "kMcgOscselOsc", "group__mcg__hal.html#gga4d9cd137b2d8cd59edf124a24e1b5c63a04af5fd6da036ffc24bf786b278c0a21", null ],
      [ "kMcgOscselRtc", "group__mcg__hal.html#gga4d9cd137b2d8cd59edf124a24e1b5c63a88b809fffbcc594657801abbe658314d", null ]
    ] ],
    [ "mcg_osc_monitor_mode_t", "group__mcg__hal.html#ga4334eea666c4c0ce2d5669ed4b524f19", [
      [ "kMcgOscMonitorInt", "group__mcg__hal.html#gga4334eea666c4c0ce2d5669ed4b524f19a98e7298c8365ed323cb66a97683a9b24", null ],
      [ "kMcgOscMonitorReset", "group__mcg__hal.html#gga4334eea666c4c0ce2d5669ed4b524f19a3805a1d91a7c78c12ddeb4c1d0a2e76f", null ]
    ] ],
    [ "mcg_pll_clk_select_t", "group__mcg__hal.html#ga8969560e56b7068f4c71eb63afa04c41", [
      [ "kMcgPllClkSelPll0", "group__mcg__hal.html#gga8969560e56b7068f4c71eb63afa04c41ac093751bb089e7a4a5830daacbcd36e6", null ]
    ] ],
    [ "mcg_atm_error_t", "group__mcg__hal.html#ga79ae6695294617f948826b4f3e727ad4", [
      [ "kMcgAtmErrorNone", "group__mcg__hal.html#gga79ae6695294617f948826b4f3e727ad4ae571d62de79d3bb8fc26b8b4d778e636", null ],
      [ "kMcgAtmErrorBusClockRange", "group__mcg__hal.html#gga79ae6695294617f948826b4f3e727ad4a5b32313fb59bdb3dcdcfe0be324b6e00", null ],
      [ "kMcgAtmErrorDesireFreqRange", "group__mcg__hal.html#gga79ae6695294617f948826b4f3e727ad4aee893855a822fdebecc352531f8ecfd0", null ],
      [ "kMcgAtmErrorIrcUsed", "group__mcg__hal.html#gga79ae6695294617f948826b4f3e727ad4a6e27bd7b203dae2c40b90beb69c51725", null ],
      [ "kMcgAtmErrorTrimValueInvalid", "group__mcg__hal.html#gga79ae6695294617f948826b4f3e727ad4a6cde764607764cae43bacd9389776640", null ],
      [ "kMcgAtmErrorHardwareFail", "group__mcg__hal.html#gga79ae6695294617f948826b4f3e727ad4afadcfd039119c29e3dae78aab088b6dd", null ]
    ] ],
    [ "mcg_status_t", "group__mcg__hal.html#ga6d781089717408c9e2f7b6a9830b10ee", [
      [ "kStatus_MCG_Success", "group__mcg__hal.html#gga6d781089717408c9e2f7b6a9830b10eeaf92bebf6bbbd344cb9324e534cba393f", null ],
      [ "kStatus_MCG_Fail", "group__mcg__hal.html#gga6d781089717408c9e2f7b6a9830b10eea4455d7ea93c94e7d71f509982e41aaf0", null ]
    ] ],
    [ "mcg_modes_t", "group__mcg__hal.html#gafef7d5e6d9532379b1772f59a4c4baee", [
      [ "kMcgModeFEI", "group__mcg__hal.html#ggafef7d5e6d9532379b1772f59a4c4baeea20b76899ba6c7a68b561a251ed05502b", null ],
      [ "kMcgModeFBI", "group__mcg__hal.html#ggafef7d5e6d9532379b1772f59a4c4baeea7ab1f0926458c408474e121ce1a2bf60", null ],
      [ "kMcgModeBLPI", "group__mcg__hal.html#ggafef7d5e6d9532379b1772f59a4c4baeea7b748aa26f3878f1925782171b7ae85e", null ],
      [ "kMcgModeFEE", "group__mcg__hal.html#ggafef7d5e6d9532379b1772f59a4c4baeea75879b62bf1687aa790f0d2f1f4ad7b7", null ],
      [ "kMcgModeFBE", "group__mcg__hal.html#ggafef7d5e6d9532379b1772f59a4c4baeead7c449492aa9e80e731f22cc2de719ee", null ],
      [ "kMcgModeBLPE", "group__mcg__hal.html#ggafef7d5e6d9532379b1772f59a4c4baeea6732ea4f10d8333618cd486648a2dc31", null ],
      [ "kMcgModePBE", "group__mcg__hal.html#ggafef7d5e6d9532379b1772f59a4c4baeea6919c756c1471f5476c008259fabeec5", null ],
      [ "kMcgModePEE", "group__mcg__hal.html#ggafef7d5e6d9532379b1772f59a4c4baeea648e02316eb2c8890b8da4b9c8d6029d", null ],
      [ "kMcgModeSTOP", "group__mcg__hal.html#ggafef7d5e6d9532379b1772f59a4c4baeea9edb3421bebba4b84c47c166d4d1eada", null ],
      [ "kMcgModeError", "group__mcg__hal.html#ggafef7d5e6d9532379b1772f59a4c4baeea4953801133039659b0b126d0bbf50f7e", null ]
    ] ],
    [ "mcg_mode_error_t", "group__mcg__hal.html#gace94291d5ecc3e66c9340939f2cee520", [
      [ "kMcgModeErrNone", "group__mcg__hal.html#ggace94291d5ecc3e66c9340939f2cee520ab1b0392b55119b5d10557f4117970c7b", null ],
      [ "kMcgModeErrModeUnreachable", "group__mcg__hal.html#ggace94291d5ecc3e66c9340939f2cee520a7d72575f99c5866d2876e12621d95cc0", null ],
      [ "kMcgModeErrOscFreqRange", "group__mcg__hal.html#ggace94291d5ecc3e66c9340939f2cee520a064c3ec96bd6df6cfc74b84c6e7d3b66", null ],
      [ "kMcgModeErrIrcSlowRange", "group__mcg__hal.html#ggace94291d5ecc3e66c9340939f2cee520a3817b2f433bfc28b15f8e77c39f7cd9f", null ],
      [ "kMcgModeErrIrcFastRange", "group__mcg__hal.html#ggace94291d5ecc3e66c9340939f2cee520a22ee121a1ec1f95160be907daaca6603", null ],
      [ "kMcgModeErrFllRefRange", "group__mcg__hal.html#ggace94291d5ecc3e66c9340939f2cee520a9a8e01f51330c8fb2b55c551d08f9033", null ],
      [ "kMcgModeErrFllFrdivRange", "group__mcg__hal.html#ggace94291d5ecc3e66c9340939f2cee520adb19eda3182d6f0a1c8c4c40ad197b40", null ],
      [ "kMcgModeErrFllDrsRange", "group__mcg__hal.html#ggace94291d5ecc3e66c9340939f2cee520a586df23c9cad074942d28dc41fa80dda", null ],
      [ "kMcgModeErrFllDmx32Range", "group__mcg__hal.html#ggace94291d5ecc3e66c9340939f2cee520a7d089284200f5d855942b8fa8562a412", null ],
      [ "kMcgModeErrPllPrdivRange", "group__mcg__hal.html#ggace94291d5ecc3e66c9340939f2cee520ac90289504f93cda24de18b3abcb74730", null ],
      [ "kMcgModeErrPllVdivRange", "group__mcg__hal.html#ggace94291d5ecc3e66c9340939f2cee520ac5ce01ee11a0e6620925a98793d5d377", null ],
      [ "kMcgModeErrPllRefClkRange", "group__mcg__hal.html#ggace94291d5ecc3e66c9340939f2cee520a0cb4d8d1905ae37e614c28abd699ae7d", null ],
      [ "kMcgModeErrPllLockBit", "group__mcg__hal.html#ggace94291d5ecc3e66c9340939f2cee520aecdd158b1ed9e42d88a19955074995d7", null ],
      [ "kMcgModeErrPllOutClkRange", "group__mcg__hal.html#ggace94291d5ecc3e66c9340939f2cee520ae8becbcba5108e6c83cda40ab8b119fe", null ]
    ] ],
    [ "CLOCK_HAL_TestOscFreq", "group__mcg__hal.html#gac4c4fe89941704646281cea63391e61e", null ],
    [ "CLOCK_HAL_TestFllExternalRefFreq", "group__mcg__hal.html#ga93e716e837da07ad2f77e8bedf7e3da5", null ],
    [ "CLOCK_HAL_GetFllRefClk", "group__mcg__hal.html#ga1dd977bce1b00ca31ff3f536a5851a41", null ],
    [ "CLOCK_HAL_TestFllFreq", "group__mcg__hal.html#ga4a3d61f83f8b8261643a0a69d1ff8544", null ],
    [ "CLOCK_HAL_GetFllClk", "group__mcg__hal.html#ga0560eed777c8e4c1ac0e4e784261539e", null ],
    [ "CLOCK_HAL_GetInternalRefClk", "group__mcg__hal.html#gafd28dfa742191b2f757e88d0dc802ba4", null ],
    [ "CLOCK_HAL_GetFixedFreqClk", "group__mcg__hal.html#gaeb32fa7b2e477213f9db346cae7d3826", null ],
    [ "CLOCK_HAL_GetOutClk", "group__mcg__hal.html#ga49262b854a6064af00dec9a5f2e2b101", null ],
    [ "CLOCK_HAL_SetClkOutSrc", "group__mcg__hal.html#ga49d942dd4c5ba4aaf93554f8bdcc4171", null ],
    [ "CLOCK_HAL_SetClksFrdivIrefs", "group__mcg__hal.html#gacb47f74ab4d63403188d9725a68099b8", null ],
    [ "CLOCK_HAL_GetClkOutStat", "group__mcg__hal.html#ga58a9cceac3380e878947915352979521", null ],
    [ "CLOCK_HAL_SetLowPowerModeCmd", "group__mcg__hal.html#ga19d2edac6a4a8144ca609ad12aa78414", null ],
    [ "CLOCK_HAL_PrepareOsc", "group__mcg__hal.html#ga17754af5c0bae173661953e8928b4063", null ],
    [ "CLOCK_HAL_GetFllSrc", "group__mcg__hal.html#gabaef7421865391ddc66fca4016249df8", null ],
    [ "CLOCK_HAL_SetFllFilterPreserveCmd", "group__mcg__hal.html#gacebed0490424d4713541f60f14acffb5", null ],
    [ "CLOCK_HAL_GetAvailableFrdiv", "group__mcg__hal.html#ga581dda538e8c9c8ab8cd65169baeb626", null ],
    [ "CLOCK_HAL_SetInternalRefClkEnableCmd", "group__mcg__hal.html#ga9b98c6bd2ee40d09988dea9073037a22", null ],
    [ "CLOCK_HAL_SetInternalRefClkEnableInStopCmd", "group__mcg__hal.html#ga32b50c763419bb9e1409b6315faade05", null ],
    [ "CLOCK_HAL_SetInternalRefClkMode", "group__mcg__hal.html#ga8bfcfd8b314a2429523464db2666f1c4", null ],
    [ "CLOCK_HAL_GetInternalRefClkMode", "group__mcg__hal.html#ga43c6be4cc6a151ad2dd27500a7fd55f0", null ],
    [ "CLOCK_HAL_UpdateFastClkInternalRefDiv", "group__mcg__hal.html#gaf09050744252f47a65107eb609691c3b", null ],
    [ "CLOCK_HAL_UpdateInternalRefClk", "group__mcg__hal.html#ga846488534b58c780a3732edf2962aeda", null ],
    [ "CLOCK_HAL_SetOsc0Mode", "group__mcg__hal.html#ga8bf129a7e5336c7bb098664b65283517", null ],
    [ "CLOCK_HAL_IsOsc0Stable", "group__mcg__hal.html#gacdd164739e66bb1fc1f7e5ae8b5a3ff0", null ],
    [ "CLOCK_HAL_EnableOsc0Monitor", "group__mcg__hal.html#gabdeb2302041897ee4702bfb1c37e35cc", null ],
    [ "CLOCK_HAL_DisableOsc0Monitor", "group__mcg__hal.html#ga9f6cf9fc66de0c982e582b49dc4d679d", null ],
    [ "CLOCK_HAL_IsOsc0MonitorEnabled", "group__mcg__hal.html#ga49a9f2580994ce1c5ceb1f82e752e3e5", null ],
    [ "CLOCK_HAL_IsOsc0LostLock", "group__mcg__hal.html#ga0cb1fbd9b2e95bf2f4c7c663b2625254", null ],
    [ "CLOCK_HAL_ClearOsc0LostLock", "group__mcg__hal.html#ga5abb0d035405753d98970ea4280acc4a", null ],
    [ "CLOCK_HAL_TrimInternalRefClk", "group__mcg__hal.html#ga009f197e513647b5622de835d2b140d3", null ],
    [ "CLOCK_HAL_IsAutoTrimMachineFailed", "group__mcg__hal.html#gac335127c0108b53f1a9e9ade76dd6133", null ],
    [ "CLOCK_HAL_ClearAutoTrimMachineFailed", "group__mcg__hal.html#ga9c0e6d660ec7262985d89f47064391e5", null ],
    [ "CLOCK_HAL_GetMcgMode", "group__mcg__hal.html#ga06a1fd70998e94dfe96fb28a965fe558", null ],
    [ "CLOCK_HAL_SetFeiMode", "group__mcg__hal.html#ga795a53c24d061dad8641e5e59aef9550", null ],
    [ "CLOCK_HAL_SetFeeMode", "group__mcg__hal.html#ga7ccc21a7fd6827a284b553d2dc4fe306", null ],
    [ "CLOCK_HAL_SetFbiMode", "group__mcg__hal.html#gae72ee5060c84a00268ffb5029d7b3e95", null ],
    [ "CLOCK_HAL_SetFbeMode", "group__mcg__hal.html#gaf032bbc028d931dfb88cff5ab38e99ed", null ],
    [ "CLOCK_HAL_SetBlpiMode", "group__mcg__hal.html#gab101f486b4f7b324e4c071bf0ab380fc", null ],
    [ "CLOCK_HAL_SetBlpeMode", "group__mcg__hal.html#gab9c95ef0ad998e1648ac3a003a3a11f2", null ],
    [ "CLOCK_HAL_SetPbeMode", "group__mcg__hal.html#gaec352b6fb1805b0965a6b612e5e11433", null ],
    [ "CLOCK_HAL_SetPeeMode", "group__mcg__hal.html#gac9e05cda303797576cff1fbc68665d96", null ]
];
