wrh2/sputnik/Vendor Firmware/Kinetis SDK v.1.3.0 API Reference Manual/group__spi__hal.js

var group__spi__hal =
[
    [ "spi_status_t", "group__spi__hal.html#ga856ecadf3d7fe18c4fc3ae56500f8982", [
      [ "kStatus_SPI_SlaveTxUnderrun", "group__spi__hal.html#gga856ecadf3d7fe18c4fc3ae56500f8982a3aa575be3ede4f8eddabf55b3f4a9664", null ],
      [ "kStatus_SPI_SlaveRxOverrun", "group__spi__hal.html#gga856ecadf3d7fe18c4fc3ae56500f8982ad2207018f8aa8c1fc60200cf3d7861cc", null ],
      [ "kStatus_SPI_Timeout", "group__spi__hal.html#gga856ecadf3d7fe18c4fc3ae56500f8982a496ced6fffc33d7bbeb01d203dfc4836", null ],
      [ "kStatus_SPI_Busy", "group__spi__hal.html#gga856ecadf3d7fe18c4fc3ae56500f8982a703abdf7900047c4d13536480f3463ab", null ],
      [ "kStatus_SPI_NoTransferInProgress", "group__spi__hal.html#gga856ecadf3d7fe18c4fc3ae56500f8982a9b2cf00def0d1d7af16ba45f5961e209", null ],
      [ "kStatus_SPI_OutOfRange", "group__spi__hal.html#gga856ecadf3d7fe18c4fc3ae56500f8982a4ab0cca3415a1b4c13fb35e81a4ecb84", null ],
      [ "kStatus_SPI_TxBufferNotEmpty", "group__spi__hal.html#gga856ecadf3d7fe18c4fc3ae56500f8982a0ea63604d54b61940869b392be34af6b", null ],
      [ "kStatus_SPI_InvalidParameter", "group__spi__hal.html#gga856ecadf3d7fe18c4fc3ae56500f8982a65dbb8cb0fe307f0267f25c327dc1c79", null ],
      [ "kStatus_SPI_NonInit", "group__spi__hal.html#gga856ecadf3d7fe18c4fc3ae56500f8982ad38e34d71ddc6c0f78744d58ec4ef55b", null ],
      [ "kStatus_SPI_AlreadyInitialized", "group__spi__hal.html#gga856ecadf3d7fe18c4fc3ae56500f8982a98e422dfd6137ed4d957aa422726ba9a", null ],
      [ "kStatus_SPI_DMAChannelInvalid", "group__spi__hal.html#gga856ecadf3d7fe18c4fc3ae56500f8982a1acd06f343f37f64743f5aae61e8df93", null ],
      [ "kStatus_SPI_Error", "group__spi__hal.html#gga856ecadf3d7fe18c4fc3ae56500f8982a2ff91d774e93aed936b87ffaa18aaf9e", null ]
    ] ],
    [ "spi_master_slave_mode_t", "group__spi__hal.html#ga434258af00a12cef572d479de91f76e2", [
      [ "kSpiMaster", "group__spi__hal.html#gga434258af00a12cef572d479de91f76e2acbac46c94c0c7c713120dfc0e27c7ff0", null ],
      [ "kSpiSlave", "group__spi__hal.html#gga434258af00a12cef572d479de91f76e2a0f00448a47a24da9430b64f75f9a20de", null ]
    ] ],
    [ "spi_clock_polarity_t", "group__spi__hal.html#ga3e5a7cd043c9596779bc23b34cb3d1f9", [
      [ "kSpiClockPolarity_ActiveHigh", "group__spi__hal.html#gga3e5a7cd043c9596779bc23b34cb3d1f9a0b33c8e75da2f2c6a2e821f94cc77f46", null ],
      [ "kSpiClockPolarity_ActiveLow", "group__spi__hal.html#gga3e5a7cd043c9596779bc23b34cb3d1f9a41c5cc78a06ec9a47d2230244535ad38", null ]
    ] ],
    [ "spi_clock_phase_t", "group__spi__hal.html#ga9ad313685ade497f5cbcb71c74a1b4dc", [
      [ "kSpiClockPhase_FirstEdge", "group__spi__hal.html#gga9ad313685ade497f5cbcb71c74a1b4dcaac180df70db6fa5463501e6b7a38a183", null ],
      [ "kSpiClockPhase_SecondEdge", "group__spi__hal.html#gga9ad313685ade497f5cbcb71c74a1b4dca58859ca1e960ebb8f6e1121997c6fbbe", null ]
    ] ],
    [ "spi_shift_direction_t", "group__spi__hal.html#gaa68518c16202382c2e1f1c7c66a9d53d", [
      [ "kSpiMsbFirst", "group__spi__hal.html#ggaa68518c16202382c2e1f1c7c66a9d53daefa27165c331b1503fd02a79099e8dfe", null ],
      [ "kSpiLsbFirst", "group__spi__hal.html#ggaa68518c16202382c2e1f1c7c66a9d53dad0909dc10154689a11543cc01f4815ad", null ]
    ] ],
    [ "spi_ss_output_mode_t", "group__spi__hal.html#ga2e5a238c65f35a2d82cc1c55927030fe", [
      [ "kSpiSlaveSelect_AsGpio", "group__spi__hal.html#gga2e5a238c65f35a2d82cc1c55927030fea771df87a27a63668dea1cd3573f9a821", null ],
      [ "kSpiSlaveSelect_FaultInput", "group__spi__hal.html#gga2e5a238c65f35a2d82cc1c55927030fea7a158d51735115f93647f4a523dae0b3", null ],
      [ "kSpiSlaveSelect_AutomaticOutput", "group__spi__hal.html#gga2e5a238c65f35a2d82cc1c55927030feaa825f6b317d71b52432b265a47201cc6", null ]
    ] ],
    [ "spi_pin_mode_t", "group__spi__hal.html#gab55fee4d636428392047e3355f33a36f", [
      [ "kSpiPinMode_Normal", "group__spi__hal.html#ggab55fee4d636428392047e3355f33a36fa5fae1212c85e103914ae3bb0c6d96aff", null ],
      [ "kSpiPinMode_Input", "group__spi__hal.html#ggab55fee4d636428392047e3355f33a36fa2f3d4b10e84461dedc8351adaf6bebb3", null ],
      [ "kSpiPinMode_Output", "group__spi__hal.html#ggab55fee4d636428392047e3355f33a36faf46381ed47d439757bcfb172337c405a", null ]
    ] ],
    [ "spi_data_bitcount_mode_t", "group__spi__hal.html#gaa7bfe75c1f0ea3b349f19a3de19b24e4", [
      [ "kSpi8BitMode", "group__spi__hal.html#ggaa7bfe75c1f0ea3b349f19a3de19b24e4a58b5d3b706acf9ccf16d83b82ac53675", null ],
      [ "kSpi16BitMode", "group__spi__hal.html#ggaa7bfe75c1f0ea3b349f19a3de19b24e4a745c75d115cfe3f7b82cf604a79fa605", null ]
    ] ],
    [ "spi_interrupt_source_t", "group__spi__hal.html#ga269499ce5d3655fd1e5dc041b7f73b09", [
      [ "kSpiRxFullAndModfInt", "group__spi__hal.html#gga269499ce5d3655fd1e5dc041b7f73b09a31267de1e0158fc40b7ae6e9551a30ff", null ],
      [ "kSpiTxEmptyInt", "group__spi__hal.html#gga269499ce5d3655fd1e5dc041b7f73b09ae00e9298b5fc50dd45f9a43e13b86e97", null ],
      [ "kSpiMatchInt", "group__spi__hal.html#gga269499ce5d3655fd1e5dc041b7f73b09af6f2f5b9e7aea4081170a5a12ed15116", null ]
    ] ],
    [ "spi_int_status_flag_t", "group__spi__hal.html#gabfdd33e049fb7914d29989bb6bcb8e2f", [
      [ "kSpiRxBufferFullFlag", "group__spi__hal.html#ggabfdd33e049fb7914d29989bb6bcb8e2fae3eb66b80b434bcbaa5380925a2a2909", null ],
      [ "kSpiMatchFlag", "group__spi__hal.html#ggabfdd33e049fb7914d29989bb6bcb8e2fa65f19ddc9c658dc7c083be97a4a0df04", null ],
      [ "kSpiTxBufferEmptyFlag", "group__spi__hal.html#ggabfdd33e049fb7914d29989bb6bcb8e2fa447c5d6af62eac78c250abd79ee9622c", null ],
      [ "kSpiModeFaultFlag", "group__spi__hal.html#ggabfdd33e049fb7914d29989bb6bcb8e2faba7e64f3afacf3392fc1a2dfa5133c6a", null ]
    ] ],
    [ "spi_fifo_interrupt_source_t", "group__spi__hal.html#ga37e541920384d9a487d4b092a7bfedab", [
      [ "kSpiRxFifoNearFullInt", "group__spi__hal.html#gga37e541920384d9a487d4b092a7bfedabafb0d6c0d48b6a28ddbbd8f4b708a3077", null ],
      [ "kSpiTxFifoNearEmptyInt", "group__spi__hal.html#gga37e541920384d9a487d4b092a7bfedaba95661a341e749ceb5304b52c38584687", null ]
    ] ],
    [ "spi_w1c_interrupt_t", "group__spi__hal.html#gad61329dc7edac1f4ef75e0746e08b3d1", [
      [ "kSpiRxFifoFullClearInt", "group__spi__hal.html#ggad61329dc7edac1f4ef75e0746e08b3d1aec4d5688412815e33fa899468f9b94a7", null ],
      [ "kSpiTxFifoEmptyClearInt", "group__spi__hal.html#ggad61329dc7edac1f4ef75e0746e08b3d1aa8e534bfea04066da7e8d95a52407a84", null ],
      [ "kSpiRxNearFullClearInt", "group__spi__hal.html#ggad61329dc7edac1f4ef75e0746e08b3d1a7a6e4a8631a1a968aa154d60d9a546f6", null ],
      [ "kSpiTxNearEmptyClearInt", "group__spi__hal.html#ggad61329dc7edac1f4ef75e0746e08b3d1abc04b1258fd1569e666c42bca62e5f74", null ]
    ] ],
    [ "spi_txfifo_watermark_t", "group__spi__hal.html#ga9a479127a2051ded7945115657adc162", null ],
    [ "spi_rxfifo_watermark_t", "group__spi__hal.html#ga79f862820ec2bcbb8184ce9de72949a6", null ],
    [ "spi_fifo_status_flag_t", "group__spi__hal.html#ga47aa40bbe920e5f17a479e80ad061ebb", null ],
    [ "spi_fifo_error_flag_t", "group__spi__hal.html#ga44d3322ec5dd96711470e17654241edb", [
      [ "kSpiNoFifoError", "group__spi__hal.html#gga44d3322ec5dd96711470e17654241edbaeb7e58e9cb1baf320f05a167e12f7cd4", null ],
      [ "kSpiRxfof", "group__spi__hal.html#gga44d3322ec5dd96711470e17654241edbad905b3ef9a54e513cf1f7ce97d43b4e0", null ],
      [ "kSpiTxfof", "group__spi__hal.html#gga44d3322ec5dd96711470e17654241edba0a9ab401923ddc60e267afddc66de35d", null ],
      [ "kSpiRxfofTxfof", "group__spi__hal.html#gga44d3322ec5dd96711470e17654241edba6ce92a4860557a76da0807b641198c06", null ],
      [ "kSpiRxferr", "group__spi__hal.html#gga44d3322ec5dd96711470e17654241edbacb66046c9d5551a808ea93e9f2ba51c6", null ],
      [ "kSpiRxfofRxferr", "group__spi__hal.html#gga44d3322ec5dd96711470e17654241edbaca20d252e934f202d1d93b79a2d0fd85", null ],
      [ "kSpiTxfofRxferr", "group__spi__hal.html#gga44d3322ec5dd96711470e17654241edbab4ed2cff9ad5ffcfc86f5dd0aec0c515", null ],
      [ "kSpiRxfofTxfofRxferr", "group__spi__hal.html#gga44d3322ec5dd96711470e17654241edbab17c3f8e01067b571b42c45919fd543e", null ],
      [ "kSpiTxferr", "group__spi__hal.html#gga44d3322ec5dd96711470e17654241edbaaa89cfbc732bc2c8d891eb5c0965c91d", null ],
      [ "kSpiRxfofTxferr", "group__spi__hal.html#gga44d3322ec5dd96711470e17654241edba42ba1844a1b2fa05ecf21ce0bf24d801", null ],
      [ "kSpiTxfofTxferr", "group__spi__hal.html#gga44d3322ec5dd96711470e17654241edbabbecd61f1520df02602d5efe7d0187c0", null ],
      [ "kSpiRxfofTxfofTxferr", "group__spi__hal.html#gga44d3322ec5dd96711470e17654241edba232798bfdd49420fa66098c35b3b19aa", null ],
      [ "kSpiRxferrTxferr", "group__spi__hal.html#gga44d3322ec5dd96711470e17654241edbac53659152f5d3073315f9f7ce3d476db", null ],
      [ "kSpiRxfofRxferrTxferr", "group__spi__hal.html#gga44d3322ec5dd96711470e17654241edba9055e19e24888e7129f855e82b0a9e64", null ],
      [ "kSpiTxfofRxferrTxferr", "group__spi__hal.html#gga44d3322ec5dd96711470e17654241edba55c05d18bb6824c476f28dd40263f8f8", null ],
      [ "kSpiRxfofTxfofRxferrTxferr", "group__spi__hal.html#gga44d3322ec5dd96711470e17654241edbaad40dc615716a9d0b9ab5aca1ce426e8", null ]
    ] ],
    [ "SPI_HAL_Init", "group__spi__hal.html#ga86018c9526d0528b7940cf62d25b228e", null ],
    [ "SPI_HAL_Enable", "group__spi__hal.html#gab586f2b389c86608d237d13a0150ab7e", null ],
    [ "SPI_HAL_Disable", "group__spi__hal.html#gaac0b66458551bceeab267e5d8954d103", null ],
    [ "SPI_HAL_SetBaud", "group__spi__hal.html#ga794f3245ea38253a3bdf7a4018b6fbc3", null ],
    [ "SPI_HAL_SetBaudDivisors", "group__spi__hal.html#ga3980567eca68ce86ca0c117e15f832f3", null ],
    [ "SPI_HAL_SetMasterSlave", "group__spi__hal.html#ga712bdffc56a45f853651b3f48998d0da", null ],
    [ "SPI_HAL_IsMaster", "group__spi__hal.html#ga1b6cd02aeb74c1fa1f1416169d646eb4", null ],
    [ "SPI_HAL_SetSlaveSelectOutputMode", "group__spi__hal.html#ga3bf584830d27da48e9b979b11b4cc57c", null ],
    [ "SPI_HAL_SetDataFormat", "group__spi__hal.html#ga4b92ac0485a74c6babf1567f233581e6", null ],
    [ "SPI_HAL_GetDataRegAddr", "group__spi__hal.html#ga2ff886b066b1d6ad9d30ccb7e3b5c9f9", null ],
    [ "SPI_HAL_SetPinMode", "group__spi__hal.html#gae243ee70a10dfcddb64bad72c5482f82", null ],
    [ "SPI_HAL_SetIntMode", "group__spi__hal.html#gae25c252c733859054affeba6a15cd13f", null ],
    [ "SPI_HAL_SetReceiveAndFaultIntCmd", "group__spi__hal.html#ga77f746bd4e61336f2d029908db214fa5", null ],
    [ "SPI_HAL_SetTransmitIntCmd", "group__spi__hal.html#gaca0b094d545c15f111914bc0afc685b1", null ],
    [ "SPI_HAL_SetMatchIntCmd", "group__spi__hal.html#ga4c39fd451a1b616b34af8fdc77aaa23a", null ],
    [ "SPI_HAL_GetIntStatusFlag", "group__spi__hal.html#gaf97cc2e9f728c982caca001a84deebb6", null ],
    [ "SPI_HAL_IsReadBuffFullPending", "group__spi__hal.html#ga1fec14f8328ef8a8accbf800d5996c26", null ],
    [ "SPI_HAL_IsTxBuffEmptyPending", "group__spi__hal.html#gabc3eda3d79ed9dd481f56dc4b835a3c1", null ],
    [ "SPI_HAL_IsModeFaultPending", "group__spi__hal.html#ga8136461aac05b742aff7b300b8cea1d1", null ],
    [ "SPI_HAL_ClearModeFaultFlag", "group__spi__hal.html#ga045f7d9da40f548b9727f60bf6391ae2", null ],
    [ "SPI_HAL_IsMatchPending", "group__spi__hal.html#gae9dff9d9251c497c6d62b3211661e0b5", null ],
    [ "SPI_HAL_ClearMatchFlag", "group__spi__hal.html#ga5c9b7e8bfc56e793d98f727e8edc1e14", null ],
    [ "SPI_HAL_ReadData", "group__spi__hal.html#gad10d0a01018f880ef471b41cef54ed0e", null ],
    [ "SPI_HAL_WriteData", "group__spi__hal.html#ga82ad2139457a44eedd31100a5408954f", null ],
    [ "SPI_HAL_WriteDataBlocking", "group__spi__hal.html#ga1357b715adc1bd6768196acea3dc1ef1", null ],
    [ "SPI_HAL_SetMatchValue", "group__spi__hal.html#ga273f8f705ea4f5329753c64a0d250db4", null ]
];
