wrh2/sputnik/Vendor Firmware/Kinetis SDK v.1.3.0 API Reference Manual/group__irtc__hal.js

var group__irtc__hal =
[
    [ "irtc_datetime_t", "group__irtc__hal.html#structirtc__datetime__t", [
      [ "year", "group__irtc__hal.html#a9b8fe6ea992dce3c6bf8d51c33f3e5b7", null ],
      [ "month", "group__irtc__hal.html#ae0109390c8c7b0dbd34fa97431129751", null ],
      [ "day", "group__irtc__hal.html#ae5984acda4b22d837c6b3bffe407344a", null ],
      [ "weekDay", "group__irtc__hal.html#a0be64b08f3689437553cd9c631f01d59", null ],
      [ "hour", "group__irtc__hal.html#ab993922405a229b17aba59803a9c765a", null ],
      [ "minute", "group__irtc__hal.html#aa35819830c72e02d307c4c410ae5a1fb", null ],
      [ "second", "group__irtc__hal.html#ab1ea5cf2ac857991c1ff81f17d0c2010", null ]
    ] ],
    [ "irtc_daylight_time_t", "group__irtc__hal.html#structirtc__daylight__time__t", [
      [ "startMonth", "group__irtc__hal.html#a90b9c925bf50d991521161751a4d9311", null ],
      [ "endMonth", "group__irtc__hal.html#a1a6c2f8122c54cc0382068dc2b954ec5", null ],
      [ "startDay", "group__irtc__hal.html#a04d8cfa0c1473cad8d7a959360eededf", null ],
      [ "endDay", "group__irtc__hal.html#a24160e25f5b81a29a78486714ed8bd42", null ],
      [ "startHour", "group__irtc__hal.html#a48e7b49a844d37f0c951533bb1ba677c", null ],
      [ "endHour", "group__irtc__hal.html#aa61d7c6d64b5feb2015175bfdd978598", null ]
    ] ],
    [ "irtc_tamper_config_t", "group__irtc__hal.html#structirtc__tamper__config__t", [
      [ "pinPolarity", "group__irtc__hal.html#a7aab8ef935bfeef7fd334db480176314", null ],
      [ "filterClk", "group__irtc__hal.html#a6557400a702797b4e88b16e9975380e5", null ],
      [ "filterDuration", "group__irtc__hal.html#adf4ce97da4032caff3ec83544ef820de", null ]
    ] ],
    [ "irtc_status_t", "group__irtc__hal.html#ga13935613c56245c537af216de1b2cd61", null ],
    [ "irtc_filter_clock_source_t", "group__irtc__hal.html#ga77da640fb1e8340c4fb59d2143d68349", [
      [ "kIRTC32K", "group__irtc__hal.html#gga77da640fb1e8340c4fb59d2143d68349ad8f13b437ebede68695e5422bbc17eb1", null ],
      [ "kIRTC512", "group__irtc__hal.html#gga77da640fb1e8340c4fb59d2143d68349a697a011de8bebc9516afe78f13cbe074", null ],
      [ "kIRTC128", "group__irtc__hal.html#gga77da640fb1e8340c4fb59d2143d68349a2f81536cecacf64ad1234881011dd7c1", null ],
      [ "kIRTC64", "group__irtc__hal.html#gga77da640fb1e8340c4fb59d2143d68349ab473be2682cfeecefff469687015d310", null ],
      [ "kIRTC16", "group__irtc__hal.html#gga77da640fb1e8340c4fb59d2143d68349a77bbe78988c2d587af98720e9761702a", null ],
      [ "kIRTC8", "group__irtc__hal.html#gga77da640fb1e8340c4fb59d2143d68349a3e6c6fde21e06d2bf43f20e75e7087c7", null ],
      [ "kIRTC4", "group__irtc__hal.html#gga77da640fb1e8340c4fb59d2143d68349af875f1cee161e0e35010f50846a534df", null ],
      [ "kIRTC2", "group__irtc__hal.html#gga77da640fb1e8340c4fb59d2143d68349ad164a57ab73c215807fac4cd48bd829c", null ]
    ] ],
    [ "irtc_tamper_pins_t", "group__irtc__hal.html#ga87f4e9cfde6412cf203df5f4bf1635c7", [
      [ "kIRTCTamper0", "group__irtc__hal.html#gga87f4e9cfde6412cf203df5f4bf1635c7a5c10a34ff736b41ca355614bc4bfd5a8", null ],
      [ "kIRTCTamper1", "group__irtc__hal.html#gga87f4e9cfde6412cf203df5f4bf1635c7a95b9fb3a6bd446e76687e8930d5137ea", null ],
      [ "kIRTCTamper2", "group__irtc__hal.html#gga87f4e9cfde6412cf203df5f4bf1635c7ab82fd3a518cde3f1da8b286a8013fa40", null ],
      [ "kIRTCTamper3", "group__irtc__hal.html#gga87f4e9cfde6412cf203df5f4bf1635c7ab3134182d600ab39107e3996c9a5ce12", null ]
    ] ],
    [ "irtc_clock_output_t", "group__irtc__hal.html#ga33ee03d0c3bfc873bb4d1552ebf6e5b6", [
      [ "kIRTCNoOutputClk", "group__irtc__hal.html#gga33ee03d0c3bfc873bb4d1552ebf6e5b6a3ec21a9032e10863995225fdd2ceed64", null ],
      [ "kIRTCFine1hzClk", "group__irtc__hal.html#gga33ee03d0c3bfc873bb4d1552ebf6e5b6a7294ac84b69a4eba47880b9587041028", null ],
      [ "kIRTC32khzClk", "group__irtc__hal.html#gga33ee03d0c3bfc873bb4d1552ebf6e5b6ac3b33179a18199bfc19e448d899f3576", null ],
      [ "kIRTCCoarse1hzClck", "group__irtc__hal.html#gga33ee03d0c3bfc873bb4d1552ebf6e5b6ad75d3bf006681bfbfcdcfb61e17d462b", null ]
    ] ],
    [ "irtc_alarm_match_t", "group__irtc__hal.html#ga987f414fef32dcceef0de9fbd69085cd", [
      [ "kIRTCSecMinHour", "group__irtc__hal.html#gga987f414fef32dcceef0de9fbd69085cda92b89eac201a8cd6e465416f6a4e1b3a", null ],
      [ "kIRTCSecMinHourDay", "group__irtc__hal.html#gga987f414fef32dcceef0de9fbd69085cda92f9127fdbc8688f87499ec930681f76", null ],
      [ "kIRTCSecMinHourDayMon", "group__irtc__hal.html#gga987f414fef32dcceef0de9fbd69085cda72746a8f67d282fb002871f5254b5e6f", null ],
      [ "kIRTCSecMinHourDayMonYear", "group__irtc__hal.html#gga987f414fef32dcceef0de9fbd69085cdadb2ce7fdb26fde761ac0831dc6c5a8e8", null ]
    ] ],
    [ "irtc_status_flag_t", "group__irtc__hal.html#ga97574f13109b83d5d133dc35cc3fc280", null ],
    [ "irtc_int_status_flag_t", "group__irtc__hal.html#ga95ee9032bd8b078a16a6fb08c78e5f9e", null ],
    [ "irtc_int_t", "group__irtc__hal.html#ga60f24d68c7f7e2215316d8a53b780c1d", null ],
    [ "IRTC_HAL_Init", "group__irtc__hal.html#gaf89c5cb3100a50f24b8184e501be21f1", null ],
    [ "IRTC_HAL_SetLockRegisterCmd", "group__irtc__hal.html#ga406f24bee4a494498aa47895425879a5", null ],
    [ "IRTC_HAL_SetYearMonth", "group__irtc__hal.html#ga6bba7854b32d9704c18a4a1947a974f1", null ],
    [ "IRTC_HAL_GetYearMonth", "group__irtc__hal.html#ga9a24a0893273a3094bf13ffcb00992b4", null ],
    [ "IRTC_HAL_SetDayWeek", "group__irtc__hal.html#ga5aee93ecc3ead5c6c3730882a550b314", null ],
    [ "IRTC_HAL_GetDayWeek", "group__irtc__hal.html#gaf547026c0213093c71f80a4eb5590bf7", null ],
    [ "IRTC_HAL_SetHourMin", "group__irtc__hal.html#ga3ecd8dd32cfdc9f623055dc5245bfcdf", null ],
    [ "IRTC_HAL_GetHourMin", "group__irtc__hal.html#gabad714f37b9d0f22de967513857ee783", null ],
    [ "IRTC_HAL_SetSec", "group__irtc__hal.html#gab4af8e72140992e5b89b35286c63b96a", null ],
    [ "IRTC_HAL_GetSec", "group__irtc__hal.html#gac865e6cfa7f64deb42f6219030348e39", null ],
    [ "IRTC_HAL_SetDatetime", "group__irtc__hal.html#ga43c579b6b89ce6322dd80efaf37f0151", null ],
    [ "IRTC_HAL_GetDatetime", "group__irtc__hal.html#ga1f233451c393ff07c9e38ca2df0f3b40", null ],
    [ "IRTC_HAL_SetAlarmMatchMode", "group__irtc__hal.html#ga2e2a027300382319348d2fe67ad58afc", null ],
    [ "IRTC_HAL_SetAlarm", "group__irtc__hal.html#gad6c2bb85dc2d3d62a0a937929ef06b03", null ],
    [ "IRTC_HAL_GetAlarm", "group__irtc__hal.html#gad73309b08daee2e5b9b0f05be5627067", null ],
    [ "IRTC_HAL_SetDaylightMonth", "group__irtc__hal.html#gae1cc539702942d0daefa37dfffc487eb", null ],
    [ "IRTC_HAL_GetDaylightMonth", "group__irtc__hal.html#gacc635ada7d8d95d648ca88b107f881c4", null ],
    [ "IRTC_HAL_SetDaylightDay", "group__irtc__hal.html#gaa663e032b2d7a54d3cafa7ee5ed37563", null ],
    [ "IRTC_HAL_GetDaylightDay", "group__irtc__hal.html#ga03f879e9d6d2d23d8cc7f14c46d8e821", null ],
    [ "IRTC_HAL_SetDaylightHour", "group__irtc__hal.html#gab136fa8ea5977337eec21a3252140246", null ],
    [ "IRTC_HAL_GetDaylightHour", "group__irtc__hal.html#ga0ce2f5b470741c8b0a7b8b85efeb9711", null ],
    [ "IRTC_HAL_SetDaylightTime", "group__irtc__hal.html#gaf54136c744b6aa4be3dfb42cfdaeeb60", null ],
    [ "IRTC_HAL_GetDaylightTime", "group__irtc__hal.html#ga47d7c86fd1711c32b548a30df055d237", null ],
    [ "IRTC_HAL_GetStatusFlag", "group__irtc__hal.html#ga718a43ad968d95d62611ea83ba2341ef", null ],
    [ "IRTC_HAL_SetIntCmd", "group__irtc__hal.html#ga4a6cf6c12d59161fa809c38d06b3ea11", null ],
    [ "IRTC_HAL_GetIntCmd", "group__irtc__hal.html#ga5b19ddbc30fbf381f21917289172854b", null ],
    [ "IRTC_HAL_GetIntStatusFlag", "group__irtc__hal.html#ga5713f7a8f31af345f8833c293f3563f7", null ],
    [ "IRTC_HAL_ClearIntStatusFlag", "group__irtc__hal.html#gaf79255b63dc6abff35cb679e430ad746", null ],
    [ "IRTC_HAL_SetCoarseCompensation", "group__irtc__hal.html#gac15a38899a74ad1fd683dcc70804ba03", null ],
    [ "IRTC_HAL_SetFineCompensation", "group__irtc__hal.html#ga01aaf5ac5e42699acb15488035fa582c", null ],
    [ "IRTC_HAL_SetClockOutMode", "group__irtc__hal.html#ga94221b309cdfeb66bcc3305a13ec3d1d", null ],
    [ "IRTC_HAL_SoftwareReset", "group__irtc__hal.html#ga2c6af152355f833e27a6a4dd5d0f2f8d", null ],
    [ "IRTC_HAL_ConfigTamperParams", "group__irtc__hal.html#ga6ad9656982f2d543c07f9e2ffec942e2", null ],
    [ "IRTC_HAL_EnableTamper", "group__irtc__hal.html#ga7e79d8adc1c61cd1c50b35f965627c73", null ],
    [ "IRTC_HAL_DisableTamper", "group__irtc__hal.html#gaa4c07e23882c833640b7dd09813cf01a", null ]
];
