wrh2/sputnik/Vendor Firmware/Kinetis SDK v.1.3.0 API Reference Manual/group__crc__hal.js

var group__crc__hal =
[
    [ "crc_status_t", "group__crc__hal.html#ga0c5290f28783d1c94f87e051b517c5ba", [
      [ "kStatus_CRC_Success", "group__crc__hal.html#gga0c5290f28783d1c94f87e051b517c5baa5e774f306da8aa80b81e717792841157", null ],
      [ "kStatus_CRC_InvalidArgument", "group__crc__hal.html#gga0c5290f28783d1c94f87e051b517c5baa6a73f7f28d7e887b4cc1b98b68e141a8", null ],
      [ "kStatus_CRC_Failed", "group__crc__hal.html#gga0c5290f28783d1c94f87e051b517c5baa647920ce4a3434281af222938866e24d", null ]
    ] ],
    [ "crc_transpose_t", "group__crc__hal.html#gadb1b5cd59e936c5d7044da4febf8202b", [
      [ "kCrcNoTranspose", "group__crc__hal.html#ggadb1b5cd59e936c5d7044da4febf8202ba9a440653a2f6ec03dd8e68d4f6b7e7f6", null ],
      [ "kCrcTransposeBits", "group__crc__hal.html#ggadb1b5cd59e936c5d7044da4febf8202ba46b551076d7955ca4db9440ff039b1a5", null ],
      [ "kCrcTransposeBoth", "group__crc__hal.html#ggadb1b5cd59e936c5d7044da4febf8202baa471ef6a13bb09f700820f7d64693d75", null ],
      [ "kCrcTransposeBytes", "group__crc__hal.html#ggadb1b5cd59e936c5d7044da4febf8202bad69367d7b35a0437734d47d11461fcff", null ]
    ] ],
    [ "crc_prot_width_t", "group__crc__hal.html#ga6a299c253d58c4bd87725f4afd7d0bd3", [
      [ "kCrc16Bits", "group__crc__hal.html#gga6a299c253d58c4bd87725f4afd7d0bd3ad135d889cc43a525114a60a94c6ee180", null ],
      [ "kCrc32Bits", "group__crc__hal.html#gga6a299c253d58c4bd87725f4afd7d0bd3a42f45c361639be9f62d8ec50132ef0b7", null ]
    ] ],
    [ "CRC_HAL_Init", "group__crc__hal.html#gaf5110a8e26cfbc0154dc9143322880ee", null ],
    [ "CRC_HAL_GetDataReg", "group__crc__hal.html#gab1c35197a49815403ab19d8d1405a318", null ],
    [ "CRC_HAL_GetDataHReg", "group__crc__hal.html#gad55d47399556733a4344ef6c71def739", null ],
    [ "CRC_HAL_GetDataLReg", "group__crc__hal.html#ga553cbf9eb35769eb77ccc63033313a13", null ],
    [ "CRC_HAL_SetDataReg", "group__crc__hal.html#ga8d3861f53b956c72f1dc14a16559cfec", null ],
    [ "CRC_HAL_SetDataHReg", "group__crc__hal.html#ga0fc1b061b6dc1d2be970c33ff38f4ab7", null ],
    [ "CRC_HAL_SetDataLReg", "group__crc__hal.html#ga2a05d7ce866425ed35f70dc269b961ae", null ],
    [ "CRC_HAL_SetDataHLReg", "group__crc__hal.html#gac7ca25b2cf71b48a8ecd49822155d9d6", null ],
    [ "CRC_HAL_SetDataHUReg", "group__crc__hal.html#ga389f23a9c8bdde4ac0ee91e192a085cd", null ],
    [ "CRC_HAL_SetDataLLReg", "group__crc__hal.html#gada12707a1a70bdc33512239b0c234910", null ],
    [ "CRC_HAL_SetDataLUReg", "group__crc__hal.html#ga15d9f19826eaf05cfdb018e22acb7591", null ],
    [ "CRC_HAL_GetPolyReg", "group__crc__hal.html#ga66ec28703dd6108bd004bc93856ff337", null ],
    [ "CRC_HAL_GetPolyHReg", "group__crc__hal.html#ga49c078cf47b3452c468ce0ff3da6ed49", null ],
    [ "CRC_HAL_GetPolyLReg", "group__crc__hal.html#ga299cbeffde136c885fe4dd964bb9876a", null ],
    [ "CRC_HAL_SetPolyReg", "group__crc__hal.html#gae9ddfbd175ae4ce15fa0820f18777ace", null ],
    [ "CRC_HAL_SetPolyHReg", "group__crc__hal.html#ga129317efbfbee7cbe6a1a32eaae23c2a", null ],
    [ "CRC_HAL_SetPolyLReg", "group__crc__hal.html#ga6d5942844d984aa97c16016a738b78a4", null ],
    [ "CRC_HAL_GetCtrlReg", "group__crc__hal.html#ga4f42e12a5a4fcc4115064ef8d674beb5", null ],
    [ "CRC_HAL_SetCtrlReg", "group__crc__hal.html#ga91fadd2c06888b732a8396eb71a9cdb6", null ],
    [ "CRC_HAL_GetSeedOrDataMode", "group__crc__hal.html#ga0e3586eefbd8a9f4c48e3b03de5a797e", null ],
    [ "CRC_HAL_SetSeedOrDataMode", "group__crc__hal.html#ga677d0e9d2216d7875d1deba8d7513304", null ],
    [ "CRC_HAL_GetWriteTranspose", "group__crc__hal.html#ga94c90ae60d1f5ae0b74d63208a9d4d13", null ],
    [ "CRC_HAL_SetWriteTranspose", "group__crc__hal.html#ga1a29f07fae4598f7f2c897fc408f7159", null ],
    [ "CRC_HAL_GetReadTranspose", "group__crc__hal.html#gaf22832fe4791f3ca3564bd4e178a3b72", null ],
    [ "CRC_HAL_SetReadTranspose", "group__crc__hal.html#ga2b45aab4ccee31c03f254826aae5b112", null ],
    [ "CRC_HAL_GetXorMode", "group__crc__hal.html#ga958595bd0056ebc776d86772a159e2c2", null ],
    [ "CRC_HAL_SetXorMode", "group__crc__hal.html#gafc28354d2967b1c33ebb5e0922ad2d8a", null ],
    [ "CRC_HAL_GetProtocolWidth", "group__crc__hal.html#ga4f6ce9236a83d18633d52d56ddc4881e", null ],
    [ "CRC_HAL_SetProtocolWidth", "group__crc__hal.html#ga34b831643d209a61fb87f2afe07250b3", null ],
    [ "CRC_HAL_GetCrc32", "group__crc__hal.html#ga68ef4a35f4d9acbb208cfc85c06b1d1d", null ],
    [ "CRC_HAL_GetCrc16", "group__crc__hal.html#gadad564e3482b708ef0abf40a79a03fda", null ],
    [ "CRC_HAL_GetCrc8", "group__crc__hal.html#ga7e27e68d3820a92da7b465f8176e762c", null ],
    [ "CRC_HAL_GetCrcResult", "group__crc__hal.html#ga1a15d1328f20def8b4c54308c5ea0904", null ]
];
