wrh2/sputnik/Vendor Firmware/Kinetis SDK v.1.3.0 API Reference Manual/group__frac__instructions.js

var group__frac__instructions =
[
    [ "MMAU_HAL_lda_d", "group__frac__instructions.html#ga375947df9c2a0846ca5ddf282ed93bc1", null ],
    [ "MMAU_HAL_l_mul_ll", "group__frac__instructions.html#ga0a62a81b73e9306d7a00e56ff6d275ca", null ],
    [ "MMAU_HAL_l_muls_ll", "group__frac__instructions.html#ga98decc90fa7e79c0bd05f256b6dab564", null ],
    [ "MMAU_HAL_d_mul_ll", "group__frac__instructions.html#ga5b08fcc348e4156adc51834084396c20", null ],
    [ "MMAU_HAL_d_muls_ll", "group__frac__instructions.html#gab4862376acb3c4294d1c2362ce950768", null ],
    [ "MMAU_HAL_d_mul_dl", "group__frac__instructions.html#ga7a513f43d20c334dec722a65bfdbba0d", null ],
    [ "MMAU_HAL_d_muls_dl", "group__frac__instructions.html#gaa95d91fc960f9b8750b72469bd3d6548", null ],
    [ "MMAU_HAL_d_mula_l", "group__frac__instructions.html#ga84c44a628954c0231d71e9cac47c93ce", null ],
    [ "MMAU_HAL_d_mulas_l", "group__frac__instructions.html#ga2f5952c0e3808b332f8266fe69bf58d8", null ],
    [ "MMAU_HAL_l_mul_dl", "group__frac__instructions.html#ga26da4cee9c7a070fc13b0a1eec799caa", null ],
    [ "MMAU_HAL_l_muls_dl", "group__frac__instructions.html#ga20b2b95740c5cb69390d4d3563bc353c", null ],
    [ "MMAU_HAL_l_mula_l", "group__frac__instructions.html#gae850f870bf8bf4c3f52f08ecafdaab1d", null ],
    [ "MMAU_HAL_l_mulas_l", "group__frac__instructions.html#ga5f7b671d4133ca1da2eac1b083f6a297", null ],
    [ "MMAU_HAL_d_mac_ll", "group__frac__instructions.html#ga8942f9190734ed49bc25baa284e348ed", null ],
    [ "MMAU_HAL_d_macs_ll", "group__frac__instructions.html#ga86ca86b7408bbbf97bb07d8d85041ecb", null ],
    [ "MMAU_HAL_d_mac_dl", "group__frac__instructions.html#ga5e4dc36b95b4e27bc4a6926379965b15", null ],
    [ "MMAU_HAL_d_macs_dl", "group__frac__instructions.html#ga75d298a3cdf11019ca45914544d851d8", null ],
    [ "MMAU_HAL_d_maca_dl", "group__frac__instructions.html#ga47b6673c3273faa0b5c5260d446b70e7", null ],
    [ "MMAU_HAL_d_macas_dl", "group__frac__instructions.html#ga42b562e75ae7060c912dfeca13114a6b", null ],
    [ "MMAU_HAL_l_mac_ll", "group__frac__instructions.html#ga87b102d3a9b20f32b00583ba8197ccb5", null ],
    [ "MMAU_HAL_l_macs_ll", "group__frac__instructions.html#ga0a5b8c6b8790530404b56dcb4d8a4a8c", null ],
    [ "MMAU_HAL_l_mac_dl", "group__frac__instructions.html#ga6863a4c8f5fe268717cfe93660ba2f83", null ],
    [ "MMAU_HAL_l_macs_dl", "group__frac__instructions.html#ga8509f8a3d673ca64ced831f17dcf6d68", null ],
    [ "MMAU_HAL_l_maca_dl", "group__frac__instructions.html#ga15ce057c13489cba480c24398d349e6a", null ],
    [ "MMAU_HAL_l_macas_dl", "group__frac__instructions.html#ga4890a1dd18076535601ec63eec6e42ae", null ],
    [ "MMAU_HAL_l_div_ll", "group__frac__instructions.html#ga280b6965bb334b294ebe196ec7e0f793", null ],
    [ "MMAU_HAL_l_divs_ll", "group__frac__instructions.html#gad91d9370461b1d895d154558a7770a1d", null ],
    [ "MMAU_HAL_l_divas_l", "group__frac__instructions.html#ga0acbc45df394e8e27abbbb9842ed1c15", null ],
    [ "MMAU_HAL_d_div_dl", "group__frac__instructions.html#gadef313440c3ba6bd82a195b3a406ea93", null ],
    [ "MMAU_HAL_d_divs_dl", "group__frac__instructions.html#ga3d1a8ebe5633f0665f95057a94a831a8", null ],
    [ "MMAU_HAL_d_diva_l", "group__frac__instructions.html#ga7ba34b49f2fae2fab621594607d95b13", null ],
    [ "MMAU_HAL_d_divas_l", "group__frac__instructions.html#gada86ac50e9e7392f20b1e051db82349f", null ],
    [ "MMAU_HAL_l_diva_l", "group__frac__instructions.html#ga877c8627120bb1ff52edbc30a17d7574", null ],
    [ "MMAU_HAL_l_sqr_l", "group__frac__instructions.html#gaf6e582c15cc2d0e347646749c94493a1", null ],
    [ "MMAU_HAL_l_sqr_d", "group__frac__instructions.html#ga5a395359a6f8281d7a4e536aafe4cb73", null ],
    [ "MMAU_HAL_l_sqra", "group__frac__instructions.html#gaced393ecd5dc7dd7148ccf01f03e5583", null ]
];
