wrh2/sputnik/Vendor Firmware/Kinetis SDK v.1.3.0 API Reference Manual/group__i2c__hal.js

var group__i2c__hal =
[
    [ "i2c_status_t", "group__i2c__hal.html#gada1e8e589688e2d6626421d8d85d9c53", [
      [ "kStatus_I2C_Success", "group__i2c__hal.html#ggada1e8e589688e2d6626421d8d85d9c53a41b146d605a2dcf3daa92d2f8847f036", null ],
      [ "kStatus_I2C_Initialized", "group__i2c__hal.html#ggada1e8e589688e2d6626421d8d85d9c53ace6396a489bae0015c0629ba8abf2b3f", null ],
      [ "kStatus_I2C_Fail", "group__i2c__hal.html#ggada1e8e589688e2d6626421d8d85d9c53a64bbd841ac2d449dd2f8ea725a1407d4", null ],
      [ "kStatus_I2C_Busy", "group__i2c__hal.html#ggada1e8e589688e2d6626421d8d85d9c53a49091894b590d7e479605bf113918952", null ],
      [ "kStatus_I2C_Timeout", "group__i2c__hal.html#ggada1e8e589688e2d6626421d8d85d9c53a81ad7cc198436cabbe91ea55c5288747", null ],
      [ "kStatus_I2C_ReceivedNak", "group__i2c__hal.html#ggada1e8e589688e2d6626421d8d85d9c53a22495915fb9a79a80f89d93561e3769a", null ],
      [ "kStatus_I2C_SlaveTxUnderrun", "group__i2c__hal.html#ggada1e8e589688e2d6626421d8d85d9c53a59390c2b988d02e016ec014f9e014557", null ],
      [ "kStatus_I2C_SlaveRxOverrun", "group__i2c__hal.html#ggada1e8e589688e2d6626421d8d85d9c53ab286ded9de770504a53c67c4fa7ee64b", null ],
      [ "kStatus_I2C_AribtrationLost", "group__i2c__hal.html#ggada1e8e589688e2d6626421d8d85d9c53a436dd56a766dbe6a7f2bddd7f29463d1", null ],
      [ "kStatus_I2C_StopSignalFail", "group__i2c__hal.html#ggada1e8e589688e2d6626421d8d85d9c53a645e05fc502410278210540341111c61", null ],
      [ "kStatus_I2C_Idle", "group__i2c__hal.html#ggada1e8e589688e2d6626421d8d85d9c53a628d242f7bc0e3d5949c7f73eafaa508", null ],
      [ "kStatus_I2C_NoReceiveInProgress", "group__i2c__hal.html#ggada1e8e589688e2d6626421d8d85d9c53a779bf6493f125fdbbd840322ca7a3767", null ],
      [ "kStatus_I2C_NoSendInProgress", "group__i2c__hal.html#ggada1e8e589688e2d6626421d8d85d9c53ada96d88b7452662773fbfaea7f2b835d", null ]
    ] ],
    [ "i2c_status_flag_t", "group__i2c__hal.html#ga8d14ab93ed4623e6f160dead9efed688", null ],
    [ "i2c_direction_t", "group__i2c__hal.html#gab49c827b45635206f06e5737606e4611", [
      [ "kI2CReceive", "group__i2c__hal.html#ggab49c827b45635206f06e5737606e4611a452f63617b04cbce09e4a23338c21a4e", null ],
      [ "kI2CSend", "group__i2c__hal.html#ggab49c827b45635206f06e5737606e4611af381933c365d3290c3fceeec2178077a", null ]
    ] ],
    [ "I2C_HAL_Init", "group__i2c__hal.html#ga612488f71dd4e1746d944e15c068f539", null ],
    [ "I2C_HAL_Enable", "group__i2c__hal.html#ga223ead18bf4b640f06579d41b526e706", null ],
    [ "I2C_HAL_Disable", "group__i2c__hal.html#ga02fb42d5560e24860543ecc8e3efbc89", null ],
    [ "I2C_HAL_SetGlitchWidth", "group__i2c__hal.html#ga09983af1ebc6bcaff76fcf17bbc4178a", null ],
    [ "I2C_HAL_SetWakeupCmd", "group__i2c__hal.html#gad6eb1a7e55b4218db3d381cf3257f379", null ],
    [ "I2C_HAL_SetBaudRate", "group__i2c__hal.html#ga95bc2959f6c3741f79f8f4d5b5e26484", null ],
    [ "I2C_HAL_SetFreqDiv", "group__i2c__hal.html#ga4af5c469025f0708283a88b732b2c0f3", null ],
    [ "I2C_HAL_SetSlaveBaudCtrlCmd", "group__i2c__hal.html#ga1a1498dbacb3052d9aaaacebc5b7cfa0", null ],
    [ "I2C_HAL_SendStart", "group__i2c__hal.html#ga1b855ae101addbbf5a4ae118ff3638f8", null ],
    [ "I2C_HAL_SendStop", "group__i2c__hal.html#gaea46a003c9c97f25cce79a38495eff64", null ],
    [ "I2C_HAL_SendAck", "group__i2c__hal.html#ga517f1a351fad14af9d6c1bdd4780763a", null ],
    [ "I2C_HAL_SendNak", "group__i2c__hal.html#ga14f624337942fef72e9ddc9ffb015ea6", null ],
    [ "I2C_HAL_SetDirMode", "group__i2c__hal.html#ga88edc25211d7007f969896a4c18516d6", null ],
    [ "I2C_HAL_GetDirMode", "group__i2c__hal.html#gaa8815133ff74ef44a545474f29ac0252", null ],
    [ "I2C_HAL_ReadByte", "group__i2c__hal.html#gacf7428151ee2492fb9fea7b6e3cce9f1", null ],
    [ "I2C_HAL_WriteByte", "group__i2c__hal.html#gaac04ca8b43cb541ca94b7e8caecd7d4d", null ],
    [ "I2C_HAL_ReadByteBlocking", "group__i2c__hal.html#gabd0881f6e85889cbf3e2b214da179ff2", null ],
    [ "I2C_HAL_WriteByteBlocking", "group__i2c__hal.html#ga26417f4f08446debd1093d712e2774ed", null ],
    [ "I2C_HAL_MasterReceiveDataPolling", "group__i2c__hal.html#ga337664b695394834d54f85a881f57458", null ],
    [ "I2C_HAL_MasterSendDataPolling", "group__i2c__hal.html#ga830e5a950daa8fcf84e3d1456a1f3446", null ],
    [ "I2C_HAL_SlaveSendDataPolling", "group__i2c__hal.html#ga0ff2e6b112f07a136663e7799bb43ef5", null ],
    [ "I2C_HAL_SlaveReceiveDataPolling", "group__i2c__hal.html#ga81e66f1199de1a2d15a01e5bf774194b", null ],
    [ "I2C_HAL_SetAddress7bit", "group__i2c__hal.html#gabf320760e18ebe399e0963655af7f518", null ],
    [ "I2C_HAL_SetAddress10bit", "group__i2c__hal.html#ga9662ccb028bd2830f0a08516580899d6", null ],
    [ "I2C_HAL_SetExtensionAddrCmd", "group__i2c__hal.html#ga1008a264e485964238f653c98d0871d3", null ],
    [ "I2C_HAL_GetExtensionAddrCmd", "group__i2c__hal.html#ga38943c4d0c3fabebb1d09cb5b02f8285", null ],
    [ "I2C_HAL_SetGeneralCallCmd", "group__i2c__hal.html#ga9f7e9508bbbf3d9edab6ed5efa802c9c", null ],
    [ "I2C_HAL_SetRangeMatchCmd", "group__i2c__hal.html#ga0bc4b1636bd3b4a47c54787a3e8b681d", null ],
    [ "I2C_HAL_SetUpperAddress7bit", "group__i2c__hal.html#ga3bdac223d788fdc2e708ea667559f69f", null ],
    [ "I2C_HAL_GetStatusFlag", "group__i2c__hal.html#ga5ce6f2cb9bb31ec926fcb30fccb566ef", null ],
    [ "I2C_HAL_IsMaster", "group__i2c__hal.html#ga1d959f218e91b9b0790f95ec0fb4e65c", null ],
    [ "I2C_HAL_ClearArbitrationLost", "group__i2c__hal.html#gafba8a323edb7810ef15f29f485d4e663", null ],
    [ "I2C_HAL_SetIntCmd", "group__i2c__hal.html#ga2066c097b87d2daf94a6d3e142787115", null ],
    [ "I2C_HAL_GetIntCmd", "group__i2c__hal.html#ga7f2ccd61e82e56d17adb5d5380ad9e44", null ],
    [ "I2C_HAL_IsIntPending", "group__i2c__hal.html#ga47b921146b085140f4ecd325018a3502", null ],
    [ "I2C_HAL_ClearInt", "group__i2c__hal.html#ga12ffb18169f3b16ba252b6e02362b346", null ]
];
