wrh2/sputnik/Vendor Firmware/Kinetis SDK v.1.3.0 API Reference Manual/group__rtc__hal.js

var group__rtc__hal =
[
    [ "rtc_datetime_t", "group__rtc__hal.html#structrtc__datetime__t", [
      [ "year", "group__rtc__hal.html#a9d9b3f17954a41223c07440f08edaf74", null ],
      [ "month", "group__rtc__hal.html#a92d2d02da2453f341dcb1793c0c04a82", null ],
      [ "day", "group__rtc__hal.html#a6f83483ef1ae5709481c38554ba864fd", null ],
      [ "hour", "group__rtc__hal.html#ae3616150362fab20cae965fc38a8a03b", null ],
      [ "minute", "group__rtc__hal.html#a6d72fb0fc42bbee7bc3f447810b8d2a9", null ],
      [ "second", "group__rtc__hal.html#a35ffc6bb746f813d06f2814c6d5d9d83", null ]
    ] ],
    [ "rtc_status_t", "group__rtc__hal.html#gab1079685ed8a9d30f32062b3bfedd041", [
      [ "kStatusRtcSuccess", "group__rtc__hal.html#ggab1079685ed8a9d30f32062b3bfedd041a12341227555d3b28504b6a0156939d48", null ],
      [ "kStatusRtcFail", "group__rtc__hal.html#ggab1079685ed8a9d30f32062b3bfedd041aba151499c6ac1e83e8e35b10f58f4477", null ]
    ] ],
    [ "RTC_HAL_Init", "group__rtc__hal.html#ga9dde1bccdda2613738875253c092c9f4", null ],
    [ "RTC_HAL_ConvertSecsToDatetime", "group__rtc__hal.html#ga551804764741c28b3fb0591a1e54c57a", null ],
    [ "RTC_HAL_IsDatetimeCorrectFormat", "group__rtc__hal.html#ga69abdba3fea196506e19d70fe61b6cd0", null ],
    [ "RTC_HAL_ConvertDatetimeToSecs", "group__rtc__hal.html#ga84abf46938a553b62603cf69d2355adb", null ],
    [ "RTC_HAL_SetDatetime", "group__rtc__hal.html#ga7757060298500a565931271ea4949efd", null ],
    [ "RTC_HAL_SetDatetimeInsecs", "group__rtc__hal.html#ga25acb176dfd653aafec08adcefaf5e35", null ],
    [ "RTC_HAL_GetDatetime", "group__rtc__hal.html#gaf4e5981c51f532b89025f8144853aaf5", null ],
    [ "RTC_HAL_GetDatetimeInSecs", "group__rtc__hal.html#gab4ddb9eaf24ddd4b61e922719d82666b", null ],
    [ "RTC_HAL_GetAlarm", "group__rtc__hal.html#ga75720434c88ea9ad9ae2745c41d6ea3e", null ],
    [ "RTC_HAL_SetAlarm", "group__rtc__hal.html#gaddaa2e2c1c1b33b153e01fdffbe50105", null ],
    [ "RTC_HAL_GetSecsReg", "group__rtc__hal.html#gaa9be510cd54cad606d8fa3ef16eea3e1", null ],
    [ "RTC_HAL_SetSecsReg", "group__rtc__hal.html#ga26b92af825d6c01da8b7882121fa08c4", null ],
    [ "RTC_HAL_SetAlarmReg", "group__rtc__hal.html#ga2703e49d751ccbae377ed0b13274d3c7", null ],
    [ "RTC_HAL_GetAlarmReg", "group__rtc__hal.html#ga8f0555ea2cf74fea8dbaa8a2a3601c10", null ],
    [ "RTC_HAL_GetPrescaler", "group__rtc__hal.html#ga5c0135c5346bb3a07347f71baa207acd", null ],
    [ "RTC_HAL_SetPrescaler", "group__rtc__hal.html#gafe4ad5e2bb80a331519c4e12a7847480", null ],
    [ "RTC_HAL_GetCompensationReg", "group__rtc__hal.html#ga7c79a6c9094257be6cb8fa7b8d84717f", null ],
    [ "RTC_HAL_SetCompensationReg", "group__rtc__hal.html#ga48e67277564462f7c5c33345f102d141", null ],
    [ "RTC_HAL_GetCompensationIntervalCounter", "group__rtc__hal.html#ga2e1e33f3fd914b35537e2ccf1d2feb63", null ],
    [ "RTC_HAL_GetTimeCompensationValue", "group__rtc__hal.html#gadba7fba3727999e0bc7455953e7c9b64", null ],
    [ "RTC_HAL_GetCompensationIntervalRegister", "group__rtc__hal.html#ga8206198b45eab08f4bfe804871021adc", null ],
    [ "RTC_HAL_SetCompensationIntervalRegister", "group__rtc__hal.html#ga5b82b6d9f3a06a561a11f4fa289989a3", null ],
    [ "RTC_HAL_GetTimeCompensationRegister", "group__rtc__hal.html#ga9fe12e7266123b143a961140d7298c3b", null ],
    [ "RTC_HAL_SetTimeCompensationRegister", "group__rtc__hal.html#ga3668b3f2e413ae2367a78981bb17f296", null ],
    [ "RTC_HAL_SetOsc2pfLoadCmd", "group__rtc__hal.html#ga79f7b0c0affe355fb615d5a919e5b610", null ],
    [ "RTC_HAL_GetOsc2pfLoad", "group__rtc__hal.html#gae33f3fbdbaff3a8a66d694c01b21bead", null ],
    [ "RTC_HAL_SetOsc4pfLoadCmd", "group__rtc__hal.html#ga70810ace6aaa1b22401081683f6bd8c1", null ],
    [ "RTC_HAL_GetOsc4pfLoad", "group__rtc__hal.html#ga09161f41bb2f5f23e193d5588c1b5f68", null ],
    [ "RTC_HAL_SetOsc8pfLoadCmd", "group__rtc__hal.html#ga111eb99a5709cd7aa9d91910bb61630c", null ],
    [ "RTC_HAL_GetOsc8pfLoad", "group__rtc__hal.html#ga5b3c1b4d61d1d78a2ca126cbfaefefd6", null ],
    [ "RTC_HAL_SetOsc16pfLoadCmd", "group__rtc__hal.html#ga05746ca57a877da17fcd64d031fd4fb3", null ],
    [ "RTC_HAL_GetOsc16pfLoad", "group__rtc__hal.html#ga0763861203432889afc057355bab546a", null ],
    [ "RTC_HAL_SetClockOutCmd", "group__rtc__hal.html#ga40cd1b41b8133d50e2a3de1b317bfd61", null ],
    [ "RTC_HAL_GetClockOutCmd", "group__rtc__hal.html#ga8e4c4126e0b7b8ba993b90be89c659d9", null ],
    [ "RTC_HAL_SetOscillatorCmd", "group__rtc__hal.html#ga96938318ce36949f284644614ee5c20a", null ],
    [ "RTC_HAL_IsOscillatorEnabled", "group__rtc__hal.html#ga877144bb9dca35f8421653c60853d338", null ],
    [ "RTC_HAL_SoftwareReset", "group__rtc__hal.html#ga870d4295f26ca18bd203db93a3ab7686", null ],
    [ "RTC_HAL_SoftwareResetFlagClear", "group__rtc__hal.html#ga36df1051111e3f3205d7f6f5eabe9087", null ],
    [ "RTC_HAL_ReadSoftwareResetStatus", "group__rtc__hal.html#gacea6071b09855274425709e8c253aa25", null ],
    [ "RTC_HAL_IsCounterEnabled", "group__rtc__hal.html#ga603f5293e8209458feeea510203b86e9", null ],
    [ "RTC_HAL_EnableCounter", "group__rtc__hal.html#ga1e56c6e13f415f64a1912f9f7b10dce0", null ],
    [ "RTC_HAL_HasAlarmOccured", "group__rtc__hal.html#ga85912c15f3dbc92cddb7d904edd143cb", null ],
    [ "RTC_HAL_IsTimeInvalid", "group__rtc__hal.html#gad8c944dbc084dbb2ef6f5be95acdb251", null ],
    [ "RTC_HAL_IsSecsIntEnabled", "group__rtc__hal.html#gaca723f37d35c2f71e76854ac0f12f940", null ],
    [ "RTC_HAL_SetSecsIntCmd", "group__rtc__hal.html#ga478716f02317e1e34d430b1835834c5a", null ],
    [ "RTC_HAL_ReadAlarmInt", "group__rtc__hal.html#ga94d4b3861b12fbe7b739d20a6de203f7", null ],
    [ "RTC_HAL_SetAlarmIntCmd", "group__rtc__hal.html#gac65acfe9415c477ab4e83564d313d404", null ],
    [ "RTC_HAL_SetTimeOverflowIntCmd", "group__rtc__hal.html#ga5eda6eb2344a569761afb560d8f7b487", null ],
    [ "RTC_HAL_SetTimeInvalidIntCmd", "group__rtc__hal.html#gaa10031221833a8fc574ba37281496e46", null ]
];
