wrh2/sputnik/Vendor Firmware/Kinetis SDK v.1.3.0 API Reference Manual/group__gpio__hal.js

var group__gpio__hal =
[
    [ "gpio_pin_direction_t", "group__gpio__hal.html#gada41ca0a2ce239fe125ee96833e715c0", [
      [ "kGpioDigitalInput", "group__gpio__hal.html#ggada41ca0a2ce239fe125ee96833e715c0abec990a5b8f20f01f2beda22945fe54d", null ],
      [ "kGpioDigitalOutput", "group__gpio__hal.html#ggada41ca0a2ce239fe125ee96833e715c0aa00f38f21e6d42b0211d04e53e371247", null ]
    ] ],
    [ "kGpioDigitalInput", "group__gpio__hal.html#ggada41ca0a2ce239fe125ee96833e715c0abec990a5b8f20f01f2beda22945fe54d", null ],
    [ "kGpioDigitalOutput", "group__gpio__hal.html#ggada41ca0a2ce239fe125ee96833e715c0aa00f38f21e6d42b0211d04e53e371247", null ],
    [ "GPIO_HAL_SetPinDir", "group__gpio__hal.html#gab775560f8288d7e1ced931b5eaf38650", null ],
    [ "GPIO_HAL_SetPortDir", "group__gpio__hal.html#ga79542d4f8aff813f3cdbd7c14cf96a3b", null ],
    [ "GPIO_HAL_GetPinDir", "group__gpio__hal.html#ga63ed7999cb035fe27b3cbcb5e4b68067", null ],
    [ "GPIO_HAL_GetPortDir", "group__gpio__hal.html#ga735f803c0b22aef97dbc9c5e7ae91d80", null ],
    [ "GPIO_HAL_WritePinOutput", "group__gpio__hal.html#ga456972e7e9901d49991b7a05027d90d5", null ],
    [ "GPIO_HAL_ReadPinOutput", "group__gpio__hal.html#ga22b360bb348a65189b6a9844ff66064f", null ],
    [ "GPIO_HAL_SetPinOutput", "group__gpio__hal.html#ga31974803bd196cc1a677384c8a40a11b", null ],
    [ "GPIO_HAL_ClearPinOutput", "group__gpio__hal.html#ga880f3aa9a1706ddd641470332f1246a8", null ],
    [ "GPIO_HAL_TogglePinOutput", "group__gpio__hal.html#ga5da91b722169f6e464e329c5e687b6b4", null ],
    [ "GPIO_HAL_WritePortOutput", "group__gpio__hal.html#gaeec873272470df8330f5d17c1a118b3a", null ],
    [ "GPIO_HAL_ReadPortOutput", "group__gpio__hal.html#gaca786cd791583a348e8a986c0a306454", null ],
    [ "GPIO_HAL_SetPortOutput", "group__gpio__hal.html#gab833e191ca978011bf5a5290e600d886", null ],
    [ "GPIO_HAL_ClearPortOutput", "group__gpio__hal.html#gaad683c39763b4b51109753b86caa0c63", null ],
    [ "GPIO_HAL_TogglePortOutput", "group__gpio__hal.html#ga0798a86bc207c66ac3216da8dccb8684", null ],
    [ "GPIO_HAL_ReadPinInput", "group__gpio__hal.html#ga4ffc5a9ba7bc453bd0f1e40fe9e196fa", null ],
    [ "GPIO_HAL_ReadPortInput", "group__gpio__hal.html#gac9c993d2f85e07995f10495c8f048b65", null ]
];
