wrh2/sputnik/Vendor Firmware/Kinetis SDK v.1.3.0 API Reference Manual/group__i2c__master.js

var group__i2c__master =
[
    [ "i2c_device_t", "group__i2c__master.html#structi2c__device__t", [
      [ "address", "group__i2c__master.html#a26364104906075849c3a76463d8c0873", null ],
      [ "baudRate_kbps", "group__i2c__master.html#a9c16a0862e9e9d787fd106fa57832035", null ]
    ] ],
    [ "i2c_master_state_t", "group__i2c__master.html#structi2c__master__state__t", null ],
    [ "I2C_DRV_MasterInit", "group__i2c__master.html#ga63f2dbf66d2dea4668dd39b6caee6916", null ],
    [ "I2C_DRV_MasterDeinit", "group__i2c__master.html#ga913ba6967d5567b17e9d09b258b497c1", null ],
    [ "I2C_DRV_MasterSetBaudRate", "group__i2c__master.html#gaae54d448b2df018d3fd49949ca4e92cb", null ],
    [ "I2C_DRV_MasterSendDataBlocking", "group__i2c__master.html#ga473d98804a933d459ff0a793aae67eb2", null ],
    [ "I2C_DRV_MasterSendData", "group__i2c__master.html#gaf755f12e68acd65e453ed4860085d89e", null ],
    [ "I2C_DRV_MasterGetSendStatus", "group__i2c__master.html#ga2ff5b1a588c35c30bba8297644846bad", null ],
    [ "I2C_DRV_MasterAbortSendData", "group__i2c__master.html#ga1e7f8aae4bba068d525b858b6349e2f9", null ],
    [ "I2C_DRV_MasterReceiveDataBlocking", "group__i2c__master.html#ga444b4fcf097197afae3df33c92e31cb2", null ],
    [ "I2C_DRV_MasterReceiveData", "group__i2c__master.html#ga7562655558d37029f9c5974e4dc87206", null ],
    [ "I2C_DRV_MasterGetReceiveStatus", "group__i2c__master.html#ga5efe706c32633d92a9736c8dc72da551", null ],
    [ "I2C_DRV_MasterReceiveDataPolling", "group__i2c__master.html#ga7a4b48979803ae407565438be34ce6be", null ],
    [ "I2C_DRV_MasterSendDataPolling", "group__i2c__master.html#gace326e36cb3765bad08d4b2d239e1e31", null ],
    [ "I2C_DRV_MasterIRQHandler", "group__i2c__master.html#ga04418dd7e20969088db31e6fb6f88a17", null ],
    [ "g_i2cBase", "group__i2c__master.html#ga4e22d124919fe3a94a971f0fbd43374b", null ]
];
