wrh2/sputnik/Vendor Firmware/Kinetis SDK v.1.3.0 API Reference Manual/group__lpi2c__master.js

var group__lpi2c__master =
[
    [ "lpi2c_device_t", "group__lpi2c__master.html#structlpi2c__device__t", [
      [ "address", "group__lpi2c__master.html#a7367f63a94ba53ec7eb667898292acec", null ],
      [ "baudRate_kbps", "group__lpi2c__master.html#a071b716300450aea6f67c99f0c476a97", null ]
    ] ],
    [ "lpi2c_master_state_t", "group__lpi2c__master.html#structlpi2c__master__state__t", null ],
    [ "LPI2C_DRV_MasterInit", "group__lpi2c__master.html#ga6ebeedd8ec49cee31ed7d4a4078fc652", null ],
    [ "LPI2C_DRV_MasterDeinit", "group__lpi2c__master.html#gae46fcbe3275f7d880a35053ea1f97ca2", null ],
    [ "LPI2C_DRV_MasterSetBaudRate", "group__lpi2c__master.html#gae9ec403936fb77073340963cf8d671fd", null ],
    [ "LPI2C_DRV_MasterSendDataBlocking", "group__lpi2c__master.html#ga1d42e1b662381c45d2e9f35422d2f711", null ],
    [ "LPI2C_DRV_MasterSendData", "group__lpi2c__master.html#gae334f66660d4e68841c08e321655e699", null ],
    [ "LPI2C_DRV_MasterGetSendStatus", "group__lpi2c__master.html#gaa6ed2d40f23cf675cd562010d5c8d65c", null ],
    [ "LPI2C_DRV_MasterAbortSendData", "group__lpi2c__master.html#ga96e026b9fe0896ddb1855ae3249bdb63", null ],
    [ "LPI2C_DRV_MasterReceiveDataBlocking", "group__lpi2c__master.html#ga8ed7d9a16fa079e8118a6d408a05bad9", null ],
    [ "LPI2C_DRV_MasterReceiveData", "group__lpi2c__master.html#ga874ec90afc629d0405525dc49d096dfb", null ],
    [ "LPI2C_DRV_MasterGetReceiveStatus", "group__lpi2c__master.html#gafe25c95bbebf002fe0caa43e2c0e373f", null ],
    [ "LPI2C_DRV_MasterReceiveDataPolling", "group__lpi2c__master.html#ga53aea5d1e723a498755ad4484e16e540", null ],
    [ "LPI2C_DRV_MasterSendDataPolling", "group__lpi2c__master.html#gaffc9dca697e39651e5c993f4c9d4eea8", null ],
    [ "g_lpi2cBase", "group__lpi2c__master.html#gaebe70dbb1ff646f8e2614c9f8366dbc5", null ]
];
