wrh2/sputnik/Vendor Firmware/Kinetis SDK v.1.3.0 API Reference Manual/group__sim__hal__km34z7.js

var group__sim__hal__km34z7 =
[
    [ "clock_wdog_src_t", "group__sim__hal__km34z7.html#gaa31046c5040e2655e118b06a060a28b8", [
      [ "kClockWdogSrcLpoClk", "group__sim__hal.html#ggaa31046c5040e2655e118b06a060a28b8a4d591d3e6df106cb28f649f6128b6208", null ],
      [ "kClockWdogSrcAltClk", "group__sim__hal.html#ggaa31046c5040e2655e118b06a060a28b8aa2d5b1a35e5fec452791604cb6d981ca", null ],
      [ "kClockWdogSrcLpoClk", "group__sim__hal.html#ggaa31046c5040e2655e118b06a060a28b8a4d591d3e6df106cb28f649f6128b6208", null ],
      [ "kClockWdogSrcAltClk", "group__sim__hal.html#ggaa31046c5040e2655e118b06a060a28b8aa2d5b1a35e5fec452791604cb6d981ca", null ],
      [ "kClockWdogSrcLpoClk", "group__sim__hal.html#ggaa31046c5040e2655e118b06a060a28b8a4d591d3e6df106cb28f649f6128b6208", null ],
      [ "kClockWdogSrcAltClk", "group__sim__hal.html#ggaa31046c5040e2655e118b06a060a28b8aa2d5b1a35e5fec452791604cb6d981ca", null ],
      [ "kClockWdogSrcLpoClk", "group__sim__hal.html#ggaa31046c5040e2655e118b06a060a28b8a4d591d3e6df106cb28f649f6128b6208", null ],
      [ "kClockWdogSrcAltClk", "group__sim__hal.html#ggaa31046c5040e2655e118b06a060a28b8aa2d5b1a35e5fec452791604cb6d981ca", null ],
      [ "kClockWdogSrcLpoClk", "group__sim__hal.html#ggaa31046c5040e2655e118b06a060a28b8a4d591d3e6df106cb28f649f6128b6208", null ],
      [ "kClockWdogSrcAltClk", "group__sim__hal.html#ggaa31046c5040e2655e118b06a060a28b8aa2d5b1a35e5fec452791604cb6d981ca", null ]
    ] ],
    [ "clock_afe_src_t", "group__sim__hal__km34z7.html#gaa257ca12b12f83f15eebde553a2169ad", null ],
    [ "clock_lptmr_src_t", "group__sim__hal__km34z7.html#ga7abfe03462124ce8b805c57369c64baf", [
      [ "kClockLptmrSrcMcgIrClk", "group__sim__hal.html#gga7abfe03462124ce8b805c57369c64bafaaaeeb65c294b6241144643b172c224c4", null ],
      [ "kClockLptmrSrcLpoClk", "group__sim__hal.html#gga7abfe03462124ce8b805c57369c64bafa6398b711bae4bc45d240513206de8c16", null ],
      [ "kClockLptmrSrcEr32kClk", "group__sim__hal.html#gga7abfe03462124ce8b805c57369c64bafa3e95b16c2db532c505f408e655cf8ed8", null ],
      [ "kClockLptmrSrcOsc0erClkUndiv", "group__sim__hal.html#gga7abfe03462124ce8b805c57369c64bafa7675d64c6d5763888af7eb552d2b3d8f", null ],
      [ "kClockLptmrSrcMcgIrClk", "group__sim__hal.html#gga7abfe03462124ce8b805c57369c64bafaaaeeb65c294b6241144643b172c224c4", null ],
      [ "kClockLptmrSrcLpoClk", "group__sim__hal.html#gga7abfe03462124ce8b805c57369c64bafa6398b711bae4bc45d240513206de8c16", null ],
      [ "kClockLptmrSrcEr32kClk", "group__sim__hal.html#gga7abfe03462124ce8b805c57369c64bafa3e95b16c2db532c505f408e655cf8ed8", null ],
      [ "kClockLptmrSrcOsc0erClkUndiv", "group__sim__hal.html#gga7abfe03462124ce8b805c57369c64bafa7675d64c6d5763888af7eb552d2b3d8f", null ],
      [ "kClockLptmrSrcMcgIrClk", "group__sim__hal.html#gga7abfe03462124ce8b805c57369c64bafaaaeeb65c294b6241144643b172c224c4", null ],
      [ "kClockLptmrSrcLpoClk", "group__sim__hal.html#gga7abfe03462124ce8b805c57369c64bafa6398b711bae4bc45d240513206de8c16", null ],
      [ "kClockLptmrSrcEr32kClk", "group__sim__hal.html#gga7abfe03462124ce8b805c57369c64bafa3e95b16c2db532c505f408e655cf8ed8", null ],
      [ "kClockLptmrSrcOsc0erClkUndiv", "group__sim__hal.html#gga7abfe03462124ce8b805c57369c64bafa7675d64c6d5763888af7eb552d2b3d8f", null ],
      [ "kClockLptmrSrcMcgIrClk", "group__sim__hal.html#gga7abfe03462124ce8b805c57369c64bafaaaeeb65c294b6241144643b172c224c4", null ],
      [ "kClockLptmrSrcLpoClk", "group__sim__hal.html#gga7abfe03462124ce8b805c57369c64bafa6398b711bae4bc45d240513206de8c16", null ],
      [ "kClockLptmrSrcEr32kClk", "group__sim__hal.html#gga7abfe03462124ce8b805c57369c64bafa3e95b16c2db532c505f408e655cf8ed8", null ],
      [ "kClockLptmrSrcOsc0erClkUndiv", "group__sim__hal.html#gga7abfe03462124ce8b805c57369c64bafa7675d64c6d5763888af7eb552d2b3d8f", null ],
      [ "kClockLptmrSrcMcgIrClk", "group__sim__hal.html#gga7abfe03462124ce8b805c57369c64bafaaaeeb65c294b6241144643b172c224c4", null ],
      [ "kClockLptmrSrcLpoClk", "group__sim__hal.html#gga7abfe03462124ce8b805c57369c64bafa6398b711bae4bc45d240513206de8c16", null ],
      [ "kClockLptmrSrcEr32kClk", "group__sim__hal.html#gga7abfe03462124ce8b805c57369c64bafa3e95b16c2db532c505f408e655cf8ed8", null ],
      [ "kClockLptmrSrcOsc0erClkUndiv", "group__sim__hal.html#gga7abfe03462124ce8b805c57369c64bafa7675d64c6d5763888af7eb552d2b3d8f", null ]
    ] ],
    [ "clock_slcd_src_t", "group__sim__hal__km34z7.html#ga62bd36c49f78b42448c5f8536ee7b251", null ],
    [ "clock_er32k_src_t", "group__sim__hal__km34z7.html#gaf742fdd9595d966c25fb5c3069ea19ff", [
      [ "kClockEr32kSrcOsc0", "group__sim__hal.html#ggaf742fdd9595d966c25fb5c3069ea19ffa685bb36a05db298c2f523d25547bbd2e", null ],
      [ "kClockEr32kSrcLpo", "group__sim__hal.html#ggaf742fdd9595d966c25fb5c3069ea19ffac3e17b64d33827df911471d2036a0cb8", null ],
      [ "kClockEr32kSrcOsc0", "group__sim__hal.html#ggaf742fdd9595d966c25fb5c3069ea19ffa685bb36a05db298c2f523d25547bbd2e", null ],
      [ "kClockEr32kSrcLpo", "group__sim__hal.html#ggaf742fdd9595d966c25fb5c3069ea19ffac3e17b64d33827df911471d2036a0cb8", null ],
      [ "kClockEr32kSrcOsc0", "group__sim__hal.html#ggaf742fdd9595d966c25fb5c3069ea19ffa685bb36a05db298c2f523d25547bbd2e", null ],
      [ "kClockEr32kSrcLpo", "group__sim__hal.html#ggaf742fdd9595d966c25fb5c3069ea19ffac3e17b64d33827df911471d2036a0cb8", null ],
      [ "kClockEr32kSrcOsc0", "group__sim__hal.html#ggaf742fdd9595d966c25fb5c3069ea19ffa685bb36a05db298c2f523d25547bbd2e", null ],
      [ "kClockEr32kSrcLpo", "group__sim__hal.html#ggaf742fdd9595d966c25fb5c3069ea19ffac3e17b64d33827df911471d2036a0cb8", null ],
      [ "kClockEr32kSrcOsc0", "group__sim__hal.html#ggaf742fdd9595d966c25fb5c3069ea19ffa685bb36a05db298c2f523d25547bbd2e", null ],
      [ "kClockEr32kSrcLpo", "group__sim__hal.html#ggaf742fdd9595d966c25fb5c3069ea19ffac3e17b64d33827df911471d2036a0cb8", null ]
    ] ],
    [ "clock_clkout_src_t", "group__sim__hal__km34z7.html#ga0e25ec0133198cbd557d639f360f2316", null ],
    [ "clock_rtcout_src_t", "group__sim__hal__km34z7.html#ga99a39f5b45d6c1ef54c5e1a09b010cbd", null ],
    [ "clock_lpuart_src_t", "group__sim__hal__km34z7.html#gaf5568332140adfe7a5f40da0a91ed2bb", null ],
    [ "sim_tmr_cnt_freeze_sel_t", "group__sim__hal__km34z7.html#ga7cc6ebdf4e1f4ef3587c1b69b9d04d28", null ],
    [ "sim_afe_clk_div_sel_t", "group__sim__hal__km34z7.html#ga09bbc32218fa4bee4b4d939291f3105f", null ],
    [ "clock_xbar_out_src_t", "group__sim__hal__km34z7.html#gad2bdc9449967d44bcd1adccb360f9494", null ],
    [ "clock_pllfll_sel_t", "group__sim__hal__km34z7.html#ga59f81628f785d9171606b77940df6999", null ],
    [ "sim_spi_out_invert_sel_t", "group__sim__hal__km34z7.html#ga3066b6b661c1cad6a7ec5ab0cbe5932a", null ],
    [ "sim_sadc_trg_clk_sel_t", "group__sim__hal__km34z7.html#ga9bc930cf61daf6a08f0851af7b965ec1", null ],
    [ "sim_lptmr_src_sel_t", "group__sim__hal__km34z7.html#ga7fa205ce90b063d1f49be1de56be64fa", null ],
    [ "sim_vref_buff_input_sel_t", "group__sim__hal__km34z7.html#ga3608b1aaed4999775bdb49683e75b338", null ],
    [ "sim_tmr_Primary_src_sel_t", "group__sim__hal__km34z7.html#ga79e9c0795e1442e9d7eac1050cef66e0", null ],
    [ "sim_tmr_sencond_src_sel_t", "group__sim__hal__km34z7.html#gad37a0b6af1e19b1cda4661a2bc44afbd", null ],
    [ "clock_tmr0_pll_src_t", "group__sim__hal__km34z7.html#ga8d9ed9f2ea25cfdae458a8158bebe605", null ],
    [ "sim_ewm_input_sel_t", "group__sim__hal__km34z7.html#ga681668298e7782d7bcf0b9fb15ca0ef6", null ],
    [ "sim_uart_irda_sel_t", "group__sim__hal__km34z7.html#ga66a1a07a165a3a490db1c617a0ee8fde", null ],
    [ "sim_uart_irda_type_sel_t", "group__sim__hal__km34z7.html#ga460cf9a27ed19fd440a118e73c8f62de", null ],
    [ "sim_afe_clk_pad_dir_t", "group__sim__hal__km34z7.html#ga87c392853cf210af168d6078f5e1b69c", null ],
    [ "sim_dma_done_sel_t", "group__sim__hal__km34z7.html#ga30d60de4ebe5eb1458b04670b9807cb6", null ],
    [ "sim_adc_trg_src_sel_t", "group__sim__hal__km34z7.html#ga3af611167989d9a0cc3adf2b83dc7875", null ],
    [ "SIM_HAL_EnableClock", "group__sim__hal__km34z7.html#gaf1e9efe366866aa4eb2a958d131c140c", null ],
    [ "SIM_HAL_DisableClock", "group__sim__hal__km34z7.html#gaee4e0a8b2e78770d32db1fb316e62bb1", null ],
    [ "SIM_HAL_GetGateCmd", "group__sim__hal__km34z7.html#ga6d2988948b15cbad7301326ccac7e1bf", null ],
    [ "SIM_HAL_GetSRamSize", "group__sim__hal__km34z7.html#ga3f45fca90070cf55875e5cb29a70d445", null ],
    [ "CLOCK_HAL_SetExternalRefClock32kSrc", "group__sim__hal__km34z7.html#gab128ee1ea48ba4e43a84ead22b1ed914", null ],
    [ "CLOCK_HAL_GetExternalRefClock32kSrc", "group__sim__hal__km34z7.html#gaf57ea11a6b89c3ffcba773e9148082b3", null ],
    [ "SIM_HAL_SetRamBitlinePrechargeCmd", "group__sim__hal__km34z7.html#gadc19e33d7fdf882897bb6012fc75d929", null ],
    [ "SIM_HAL_GetRamBitlinePrechargeCmd", "group__sim__hal__km34z7.html#gaac01b8cacd21a9a757f28a6b9203964b", null ],
    [ "SIM_HAL_SetRamSrcBiasCmd", "group__sim__hal__km34z7.html#ga72f3a87c1788ab8e283610cafc4a94e6", null ],
    [ "SIM_HAL_GetRamSrcBiasCmd", "group__sim__hal__km34z7.html#ga52932f40059e5ec802e0d57564eac203", null ],
    [ "SIM_HAL_SetLptmrChSelMode", "group__sim__hal__km34z7.html#gac577b539400f34a5855b1e4c632acd72", null ],
    [ "SIM_HAL_GetLptmrChSelMode", "group__sim__hal__km34z7.html#ga464a99fbaa885bffabbd00ec430cca3a", null ],
    [ "CLOCK_HAL_SetClkOutSel", "group__sim__hal__km34z7.html#gab45f98ae4171552121942a5e5c14b26d", null ],
    [ "CLOCK_HAL_GetClkOutSel", "group__sim__hal__km34z7.html#ga45763ba7aabf6b6c98d78280fcf68fe8", null ],
    [ "CLOCK_HAL_SetSAdcTrgClkSel", "group__sim__hal__km34z7.html#gad1f5b1f3a8bf3a11bd88b53a596abd67", null ],
    [ "CLOCK_HAL_GetSAdcTrgClkSel", "group__sim__hal__km34z7.html#ga8266c34f77105c377fdd3457f7c1b5b0", null ],
    [ "CLOCK_HAL_SetTmrCntFreezeCmd", "group__sim__hal__km34z7.html#ga0445e09d7129f457a61d2b0e18406a26", null ],
    [ "CLOCK_HAL_GetTmrCntFreezeCmd", "group__sim__hal__km34z7.html#ga8938ac8bb932491ef42ba30d012de993", null ],
    [ "CLOCK_HAL_SetLpuartClkSel", "group__sim__hal__km34z7.html#ga828ea2ed6d04c6272411811bcaab44e7", null ],
    [ "CLOCK_HAL_GetLpuartClkSel", "group__sim__hal__km34z7.html#ga9717bc1dc08f5c2c564dfaa3cf164eec", null ],
    [ "CLOCK_HAL_SetAfeOutDivCmd", "group__sim__hal__km34z7.html#ga0799d7eb53befc3adfb8966bd8fd9f0a", null ],
    [ "CLOCK_HAL_GetAfeOutDivCmd", "group__sim__hal__km34z7.html#ga19154ee5f9d8df5be71ad9a18cb831f8", null ],
    [ "CLOCK_HAL_SetXbarOutSel", "group__sim__hal__km34z7.html#ga3864f34d293b4d758e0377ef92e4c50f", null ],
    [ "CLOCK_HAL_GetXbarOutSel", "group__sim__hal__km34z7.html#ga11a43b5797aa490b20e3e8ac6072554a", null ],
    [ "CLOCK_HAL_SetPllfllSel", "group__sim__hal__km34z7.html#ga16342ae68ee50da95a3bbe286abe762e", null ],
    [ "CLOCK_HAL_GetPllfllSel", "group__sim__hal__km34z7.html#ga2e2cf6cfa9b583a6704b42242cfc82cf", null ],
    [ "CLOCK_HAL_SetSpiOutInvCmd", "group__sim__hal__km34z7.html#ga5c050332e3c32fe45a59da71a95bc89a", null ],
    [ "CLOCK_HAL_GetSpiOutInvCmd", "group__sim__hal__km34z7.html#ga889a15627c776e977bd7f04aa5667c17", null ],
    [ "SIM_HAL_SetPllInVlpCmd", "group__sim__hal__km34z7.html#ga95f00708a40ea5ff500913455f40dcc5", null ],
    [ "SIM_HAL_GetPllInVlpCmd", "group__sim__hal__km34z7.html#ga45883c752ad5279257c67c4ab7262428", null ],
    [ "SIM_HAL_SetNmiDisCmd", "group__sim__hal__km34z7.html#ga9f16c09df6460cb6acc5ab53e98ff663", null ],
    [ "SIM_HAL_GetNmiDisCmd", "group__sim__hal__km34z7.html#ga818cdf8b64fc610f9e907f4e0d6f6b7b", null ],
    [ "SIM_HAL_GetFamilyId", "group__sim__hal__km34z7.html#ga4e58d9849ebfb707f9daf51c3003e18f", null ],
    [ "SIM_HAL_GetSubFamilyId", "group__sim__hal__km34z7.html#ga392ee1aadf70566d3b5b5df3bc376104", null ],
    [ "SIM_HAL_GetSeriesId", "group__sim__hal__km34z7.html#ga0b9f11425fa4278f3d3c2b95ceb9d797", null ],
    [ "SIM_HAL_GetAttributeId", "group__sim__hal__km34z7.html#ga9ba3a66fbf3a72cf43de0cd511a00276", null ],
    [ "SIM_HAL_GetSRamSizeId", "group__sim__hal__km34z7.html#ga0e721fc14d3c732f1e56eece615adf15", null ],
    [ "SIM_HAL_GetRevId", "group__sim__hal__km34z7.html#gaae905cba1e98882134e83e75451f2869", null ],
    [ "SIM_HAL_GetDieId", "group__sim__hal__km34z7.html#ga9a58484850e78e8918b1d350dfa0dd14", null ],
    [ "SIM_HAL_GetPinCntId", "group__sim__hal__km34z7.html#ga09da5535de0a201a9f70841a3d87876a", null ],
    [ "CLOCK_HAL_SetSysDiv", "group__sim__hal__km34z7.html#ga79459ce5aa2099ee01d443f0e383651e", null ],
    [ "CLOCK_HAL_GetSysDiv", "group__sim__hal__km34z7.html#ga4f26769d9fbaebe5cbd5c7193d9ca29b", null ],
    [ "CLOCK_HAL_SetBusDiv", "group__sim__hal__km34z7.html#ga964bc6917671cdadbe5449a28fbf5eb3", null ],
    [ "CLOCK_HAL_GetBusDiv", "group__sim__hal__km34z7.html#ga6a603d5150e30b74ebdad85d893ebcb0", null ],
    [ "CLOCK_HAL_SetFlashClkMode", "group__sim__hal__km34z7.html#ga781f6f073a3eb5af235ccd64dd052f99", null ],
    [ "CLOCK_HAL_GetFlashClkMode", "group__sim__hal__km34z7.html#gafff137edea56375117ffcf458e66a024", null ],
    [ "CLOCK_HAL_SetOutDiv", "group__sim__hal__km34z7.html#gab8723d587b2afb9f8fdafe681e6a486f", null ],
    [ "CLOCK_HAL_GetOutDiv", "group__sim__hal__km34z7.html#ga04fba94065f3b20c17aebf8d2144c9cc", null ],
    [ "SIM_HAL_GetProgramFlashSize", "group__sim__hal__km34z7.html#gae4ea1894bf90debffe256ab10ae0cda0", null ],
    [ "SIM_HAL_SetFlashDoze", "group__sim__hal__km34z7.html#ga6fb06ad054fac5a00c0d650fce967a3a", null ],
    [ "SIM_HAL_GetFlashDoze", "group__sim__hal__km34z7.html#ga69b2f1e76dcc935d731854c7180b7b7f", null ],
    [ "SIM_HAL_SetFlashDisableCmd", "group__sim__hal__km34z7.html#ga1d0455dcf1c6647c36acee9177e9d9ba", null ],
    [ "SIM_HAL_GetRamSize", "group__sim__hal__km34z7.html#gafaec8a8c6efaf1cba1b2f3c88facb4b5", null ],
    [ "SIM_HAL_GetFlashDisableCmd", "group__sim__hal__km34z7.html#gae94e2aa677fe7b92ac836853b750e9dc", null ],
    [ "SIM_HAL_GetFlashMaxAddrBlock0", "group__sim__hal__km34z7.html#gac2334d8630cc2f3b0dcbb93e875943f4", null ],
    [ "SIM_HAL_SetVrefBuffPowerDownCmd", "group__sim__hal__km34z7.html#gaf40645bbc0604dbfea53e2210ba3f13e", null ],
    [ "SIM_HAL_GetVrefBuffPowerDownCmd", "group__sim__hal__km34z7.html#gab344029abe2c8e91dd024621e989dcc0", null ],
    [ "CLOCK_HAL_SetVrefBuffInputSel", "group__sim__hal__km34z7.html#ga17486d4b1454a1a2f0e8da2b181ae0da", null ],
    [ "CLOCK_HAL_GetVrefBuffInputSel", "group__sim__hal__km34z7.html#ga63924c0871baf05422d9c283700ce430", null ],
    [ "SIM_HAL_SetVrefBuffOutCmd", "group__sim__hal__km34z7.html#ga2ced9354d2bb1da5660031c2d2f9ce3f", null ],
    [ "SIM_HAL_GetVrefBuffOutCmd", "group__sim__hal__km34z7.html#ga1bed6db4d415f4024de89df5759a7e6b", null ],
    [ "CLOCK_HAL_SetRtcClkSel", "group__sim__hal__km34z7.html#ga094817a81fe954cac74fc495a2e238ea", null ],
    [ "CLOCK_HAL_GetRtcClkSel", "group__sim__hal__km34z7.html#gabaafc6c17c03f6dfa45ba9db624f46ce", null ],
    [ "SIM_HAL_SetTmrPrimaryCntSrcSelMode", "group__sim__hal__km34z7.html#ga217a196238b7d85ed2febe1445438000", null ],
    [ "SIM_HAL_GetTmrPrimaryCntSrcSelMode", "group__sim__hal__km34z7.html#ga632034f390e1992a4211663f88cf3b15", null ],
    [ "SIM_HAL_SetTmrSecondCntSrcSelMode", "group__sim__hal__km34z7.html#ga752afe9877d4b71b8d84a586047af44e", null ],
    [ "SIM_HAL_GetTmrSecondCntSrcSelMode", "group__sim__hal__km34z7.html#ga334362845451c5a437a903acacc0dffc", null ],
    [ "SIM_HAL_SetTmr0PllClkSelMode", "group__sim__hal__km34z7.html#ga0e0cd42cf0d96f5ce20ccd49e947ff57", null ],
    [ "SIM_HAL_GetTmr0PllClkSelMode", "group__sim__hal__km34z7.html#ga8de983b1b5b03fcf5bc119c7757c9700", null ],
    [ "SIM_HAL_SetEwmInputSelMode", "group__sim__hal__km34z7.html#ga2b1220db49ba854564d79dbbdbbc2ee0", null ],
    [ "SIM_HAL_GetEwmInputSelMode", "group__sim__hal__km34z7.html#gae68b5ee7685b2b9908587b4a13c21661", null ],
    [ "SIM_HAL_SetUartIrdaSelMode", "group__sim__hal__km34z7.html#ga09588aa017361f29aa64b511aafc8ecc", null ],
    [ "SIM_HAL_GetUartIrdaSelMode", "group__sim__hal__km34z7.html#ga57192dfab239acef75dd1cb7d28fa9f3", null ],
    [ "SIM_HAL_SetUartModTypeSelMode", "group__sim__hal__km34z7.html#gaad41a31837d2389c96627ef66244a3c0", null ],
    [ "SIM_HAL_GetUartModTypeSelMode", "group__sim__hal__km34z7.html#ga22bc8884d4eb70e86e22bd7e8d3bd7ce", null ],
    [ "SIM_HAL_SetAfeClkPadDirCmd", "group__sim__hal__km34z7.html#ga750fc07838a80e6d174d88b16ff6b19e", null ],
    [ "SIM_HAL_GetAfeClkPadDirCmd", "group__sim__hal__km34z7.html#gaca4569020fd21bf5c881505c4548326a", null ],
    [ "CLOCK_HAL_SetAfeClkSrc", "group__sim__hal__km34z7.html#ga73cbba15f8bec3c092e4d1801d2d72af", null ],
    [ "CLOCK_HAL_GetAfeClkSrc", "group__sim__hal__km34z7.html#ga28fef915b2a66cbf378dabfaf267bfcb", null ],
    [ "SIM_HAL_SetDmaDoneSelMode", "group__sim__hal__km34z7.html#gaa21190af50a99f207f36d1e78beda473", null ],
    [ "SIM_HAL_GetDmaDoneSelMode", "group__sim__hal__km34z7.html#ga1ca643f4c120e9c954022fa07226973a", null ],
    [ "SIM_HAL_SetAdcTrgSelMode", "group__sim__hal__km34z7.html#ga15f544e9b9e2f0affc7094753f9530d1", null ],
    [ "SIM_HAL_GetAdcTrgSelMode", "group__sim__hal__km34z7.html#gadee6eb134f6902067d31984dbcfbd5a0", null ],
    [ "SIM_HAL_GetRtcOscStatusCmd", "group__sim__hal__km34z7.html#gaa6c203c62fcce2c389a529671dab3a07", null ],
    [ "SIM_HAL_GetAdcCompensationValueCmd", "group__sim__hal__km34z7.html#gab040883db5f77c6b1bb577e103eec679", null ]
];
