wrh2/sputnik/Vendor Firmware/Kinetis SDK v.1.3.0 API Reference Manual/group__sim__hal__kv31f51212.js

var group__sim__hal__kv31f51212 =
[
    [ "FSL_SIM_SCGC_BIT", "group__sim__hal__kv31f51212.html#ga0864794938afcfb3be1404fc0c46659b", null ],
    [ "clock_wdog_src_kv31f51212_t", "group__sim__hal__kv31f51212.html#ga92b4cb67f24030514d48bc3c38a192eb", [
      [ "kClockWdogSrcLpoClk", "group__sim__hal__kv31f51212.html#gga92b4cb67f24030514d48bc3c38a192eba4d591d3e6df106cb28f649f6128b6208", null ],
      [ "kClockWdogSrcAltClk", "group__sim__hal__kv31f51212.html#gga92b4cb67f24030514d48bc3c38a192ebaa2d5b1a35e5fec452791604cb6d981ca", null ]
    ] ],
    [ "clock_trace_src_kv31f51212_t", "group__sim__hal__kv31f51212.html#gac03844a9e997c601371e1ea43803edd8", [
      [ "kClockTraceSrcMcgoutClk", "group__sim__hal__kv31f51212.html#ggac03844a9e997c601371e1ea43803edd8ac49d028167c55753c397b351c045244f", null ],
      [ "kClockTraceSrcCoreClk", "group__sim__hal__kv31f51212.html#ggac03844a9e997c601371e1ea43803edd8aca39d41a608156a0ecf820b69d86a813", null ]
    ] ],
    [ "clock_port_filter_src_kv31f51212_t", "group__sim__hal__kv31f51212.html#gaee3bd8ef6d5812ecee440f6397c03e15", [
      [ "kClockPortFilterSrcBusClk", "group__sim__hal__kv31f51212.html#ggaee3bd8ef6d5812ecee440f6397c03e15a98c950266f15c73cd54fe863534758db", null ],
      [ "kClockPortFilterSrcLpoClk", "group__sim__hal__kv31f51212.html#ggaee3bd8ef6d5812ecee440f6397c03e15a019f43c72cd62f9c205d88076d906a34", null ]
    ] ],
    [ "clock_lptmr_src_kv31f51212_t", "group__sim__hal__kv31f51212.html#ga43fa31d43dd476d11d52a0beca84ad6b", [
      [ "kClockLptmrSrcMcgIrClk", "group__sim__hal__kv31f51212.html#gga43fa31d43dd476d11d52a0beca84ad6baaaeeb65c294b6241144643b172c224c4", null ],
      [ "kClockLptmrSrcLpoClk", "group__sim__hal__kv31f51212.html#gga43fa31d43dd476d11d52a0beca84ad6ba6398b711bae4bc45d240513206de8c16", null ],
      [ "kClockLptmrSrcEr32kClk", "group__sim__hal__kv31f51212.html#gga43fa31d43dd476d11d52a0beca84ad6ba3e95b16c2db532c505f408e655cf8ed8", null ],
      [ "kClockLptmrSrcOsc0erClkUndiv", "group__sim__hal__kv31f51212.html#gga43fa31d43dd476d11d52a0beca84ad6ba7675d64c6d5763888af7eb552d2b3d8f", null ]
    ] ],
    [ "clock_lpuart_src_kv31f51212_t", "group__sim__hal__kv31f51212.html#ga2fcd0bcadb48c93c84520b6a35615488", [
      [ "kClockLpuartSrcNone", "group__sim__hal__kv31f51212.html#gga2fcd0bcadb48c93c84520b6a35615488ad46a4e98079acad06a1252607ad90940", null ],
      [ "kClockLpuartSrcPllFllSel", "group__sim__hal__kv31f51212.html#gga2fcd0bcadb48c93c84520b6a35615488a7cf2dac0e57bd3b1b0563bb474bd5399", null ],
      [ "kClockLpuartSrcOsc0erClk", "group__sim__hal__kv31f51212.html#gga2fcd0bcadb48c93c84520b6a35615488a850e5c7bc0176bf2f5d62486072afabd", null ],
      [ "kClockLpuartSrcMcgIrClk", "group__sim__hal__kv31f51212.html#gga2fcd0bcadb48c93c84520b6a35615488a3db2022a69a54e7cd19ea2b169694b60", null ]
    ] ],
    [ "clock_pllfll_sel_kv31f51212_t", "group__sim__hal__kv31f51212.html#gadba802ec03b3621d00f9c9efb6b60900", [
      [ "kClockPllFllSelFll", "group__sim__hal__kv31f51212.html#ggadba802ec03b3621d00f9c9efb6b60900a250b294117acd4fc94d4cbfd3072ef8a", null ],
      [ "kClockPllFllSelPll", "group__sim__hal__kv31f51212.html#ggadba802ec03b3621d00f9c9efb6b60900a106298229e9f5b30be7341e167acf86a", null ],
      [ "kClockPllFllSelIrc48M", "group__sim__hal__kv31f51212.html#ggadba802ec03b3621d00f9c9efb6b60900ab526106256efd4b6943dca16fc381789", null ]
    ] ],
    [ "clock_er32k_src_kv31f51212_t", "group__sim__hal__kv31f51212.html#gae158ca08852854740201786bab731b3d", [
      [ "kClockEr32kSrcOsc0", "group__sim__hal__kv31f51212.html#ggae158ca08852854740201786bab731b3da685bb36a05db298c2f523d25547bbd2e", null ],
      [ "kClockEr32kSrcLpo", "group__sim__hal__kv31f51212.html#ggae158ca08852854740201786bab731b3dac3e17b64d33827df911471d2036a0cb8", null ]
    ] ],
    [ "clock_clkout_src_kv31f51212_t", "group__sim__hal__kv31f51212.html#ga3fda5a48d6f721445b3e55469c59a513", [
      [ "kClockClkoutSelFlexbusClk", "group__sim__hal__kv31f51212.html#gga3fda5a48d6f721445b3e55469c59a513abe32a3842028987105822fc382541502", null ],
      [ "kClockClkoutSelFlashClk", "group__sim__hal__kv31f51212.html#gga3fda5a48d6f721445b3e55469c59a513a6f5b3407f0a10fff0904b33a252f640f", null ],
      [ "kClockClkoutSelLpoClk", "group__sim__hal__kv31f51212.html#gga3fda5a48d6f721445b3e55469c59a513aeec80cdc4e8b43f9c1363c79a63efe2d", null ],
      [ "kClockClkoutSelMcgIrClk", "group__sim__hal__kv31f51212.html#gga3fda5a48d6f721445b3e55469c59a513a7c5bf1ff3663fd4a1a1249dee4f22fd9", null ],
      [ "kClockClkoutSelOsc0erClk", "group__sim__hal__kv31f51212.html#gga3fda5a48d6f721445b3e55469c59a513a9555f9925faed3174a98a08f7691c38a", null ],
      [ "kClockClkoutSelIrc48M", "group__sim__hal__kv31f51212.html#gga3fda5a48d6f721445b3e55469c59a513a25814da8bb45efb2019ed155c7cdf5f1", null ]
    ] ],
    [ "clock_osc32kout_sel_kv31f51212_t", "group__sim__hal__kv31f51212.html#gad1c817a4713d3d877e607d7c13f0b69c", null ],
    [ "sim_adc_pretrg_sel_kv31f51212_t", "group__sim__hal__kv31f51212.html#ga703761b3d966c1278f6bd072e79e3b73", [
      [ "kSimAdcPretrgselA", "group__sim__hal__kv31f51212.html#gga703761b3d966c1278f6bd072e79e3b73af6a1fdc3dfd392011b379d3112d61e2a", null ],
      [ "kSimAdcPretrgselB", "group__sim__hal__kv31f51212.html#gga703761b3d966c1278f6bd072e79e3b73a077187f1a51b5bf575722eed57ffcce6", null ]
    ] ],
    [ "sim_adc_trg_sel_kv31f51212_t", "group__sim__hal__kv31f51212.html#ga7da482dfdebc6ed98bb7f98e94660dd7", [
      [ "kSimAdcTrgselExt", "group__sim__hal__kv31f51212.html#gga7da482dfdebc6ed98bb7f98e94660dd7a4fe6a0758c44597f9857368bf4efb163", null ],
      [ "kSimAdcTrgSelHighSpeedComp0", "group__sim__hal__kv31f51212.html#gga7da482dfdebc6ed98bb7f98e94660dd7a346efddda85864e642771a6210dad582", null ],
      [ "kSimAdcTrgSelHighSpeedComp1", "group__sim__hal__kv31f51212.html#gga7da482dfdebc6ed98bb7f98e94660dd7a90105ef232dfd38b663223586fc29bf4", null ],
      [ "kSimAdcTrgSelPit0", "group__sim__hal__kv31f51212.html#gga7da482dfdebc6ed98bb7f98e94660dd7a7acc12673d9df13b482c8c2cd13bb1fb", null ],
      [ "kSimAdcTrgSelPit1", "group__sim__hal__kv31f51212.html#gga7da482dfdebc6ed98bb7f98e94660dd7a8a2803540c8e500db33b9410736e4ece", null ],
      [ "kSimAdcTrgSelPit2", "group__sim__hal__kv31f51212.html#gga7da482dfdebc6ed98bb7f98e94660dd7ad503f497a3dfe9d4b9f553849a3ce433", null ],
      [ "kSimAdcTrgSelPit3", "group__sim__hal__kv31f51212.html#gga7da482dfdebc6ed98bb7f98e94660dd7acc9f0546a3c673b06d4b42cb8e119752", null ],
      [ "kSimAdcTrgSelFtm0", "group__sim__hal__kv31f51212.html#gga7da482dfdebc6ed98bb7f98e94660dd7a988ceb384a2d56ec0bbf9568b1a96750", null ],
      [ "kSimAdcTrgSelFtm1", "group__sim__hal__kv31f51212.html#gga7da482dfdebc6ed98bb7f98e94660dd7a97096e61d1d1a1cfd7e5507b07ab6580", null ],
      [ "kSimAdcTrgSelFtm2", "group__sim__hal__kv31f51212.html#gga7da482dfdebc6ed98bb7f98e94660dd7a8139e426fa8695f6133cc6d59268907c", null ],
      [ "kSimAdcTrgSelFtm3", "group__sim__hal__kv31f51212.html#gga7da482dfdebc6ed98bb7f98e94660dd7aff0cf32760c663120c8c3e2ab075d81d", null ],
      [ "kSimAdcTrgSelLptimer", "group__sim__hal__kv31f51212.html#gga7da482dfdebc6ed98bb7f98e94660dd7afca49612c7638ad9c0178e3b29e8db47", null ]
    ] ],
    [ "sim_lpuart_rxsrc_kv31f51212_t", "group__sim__hal__kv31f51212.html#gadf503e4935cf00fecc4668ba92d8fb4f", [
      [ "kSimLpuartRxsrcPin", "group__sim__hal__kv31f51212.html#ggadf503e4935cf00fecc4668ba92d8fb4facb6e9bb94be7b8f88ae6173e7382599f", null ],
      [ "kSimLpuartRxsrcCmp0", "group__sim__hal__kv31f51212.html#ggadf503e4935cf00fecc4668ba92d8fb4fae52af7aa2a16f73fc066d09ba3a5ab24", null ],
      [ "kSimLpuartRxsrcCmp1", "group__sim__hal__kv31f51212.html#ggadf503e4935cf00fecc4668ba92d8fb4fa07ee40655c151d53d1414911c3a016ba", null ]
    ] ],
    [ "sim_uart_rxsrc_kv31f51212_t", "group__sim__hal__kv31f51212.html#ga8ccd870e07aea82992171f16f6ce81f9", [
      [ "kSimUartRxsrcPin", "group__sim__hal__kv31f51212.html#gga8ccd870e07aea82992171f16f6ce81f9ae7e1caafec14492f3688dcd294703dbb", null ],
      [ "kSimUartRxsrcCmp0", "group__sim__hal__kv31f51212.html#gga8ccd870e07aea82992171f16f6ce81f9a47a0cba48d63a0723fd21e7e6c022e08", null ],
      [ "kSimUartRxsrcCmp1", "group__sim__hal__kv31f51212.html#gga8ccd870e07aea82992171f16f6ce81f9a5da13824e68e3d0e2d180befb590019b", null ]
    ] ],
    [ "sim_uart_txsrc_kv31f51212_t", "group__sim__hal__kv31f51212.html#ga96b6983f2e226ca02cd660f93f90a718", [
      [ "kSimUartTxsrcPin", "group__sim__hal__kv31f51212.html#gga96b6983f2e226ca02cd660f93f90a718a456992f995affc8441e46f9f453cc3a7", null ],
      [ "kSimUartTxsrcFtm1", "group__sim__hal__kv31f51212.html#gga96b6983f2e226ca02cd660f93f90a718a46848df40ebe9aabaa6294e6b5b327e0", null ],
      [ "kSimUartTxsrcFtm2", "group__sim__hal__kv31f51212.html#gga96b6983f2e226ca02cd660f93f90a718a0ea6d180c732546354e51bf31fe7e8a6", null ]
    ] ],
    [ "sim_ftm_trg_src_kv31f51212_t", "group__sim__hal__kv31f51212.html#ga5842536c7ef4b54016a3619ad385957a", [
      [ "kSimFtmTrgSrc0", "group__sim__hal__kv31f51212.html#gga5842536c7ef4b54016a3619ad385957aaf2bb490704f0e4970978c0cd3c6a90f2", null ],
      [ "kSimFtmTrgSrc1", "group__sim__hal__kv31f51212.html#gga5842536c7ef4b54016a3619ad385957aad43534579e5b1c48f8e3bd8522a5ef7a", null ]
    ] ],
    [ "sim_ftm_clk_sel_kv31f51212_t", "group__sim__hal__kv31f51212.html#ga10eb37f2ec45f1b76bc197722fd699bb", [
      [ "kSimFtmClkSel0", "group__sim__hal__kv31f51212.html#gga10eb37f2ec45f1b76bc197722fd699bbabfc241747fbad6bead3477fbad992188", null ],
      [ "kSimFtmClkSel1", "group__sim__hal__kv31f51212.html#gga10eb37f2ec45f1b76bc197722fd699bba0734ad5baf313215b6942861094dda70", null ]
    ] ],
    [ "sim_ftm_ch_src_kv31f51212_t", "group__sim__hal__kv31f51212.html#ga5e252dfd4f6911f4213e6a0c8a703a58", [
      [ "kSimFtmChSrc0", "group__sim__hal__kv31f51212.html#gga5e252dfd4f6911f4213e6a0c8a703a58a33f3fae2d028c10963df5d77acff836c", null ],
      [ "kSimFtmChSrc1", "group__sim__hal__kv31f51212.html#gga5e252dfd4f6911f4213e6a0c8a703a58aa88ea6301af7610834b3ed4e75645f6e", null ],
      [ "kSimFtmChSrc2", "group__sim__hal__kv31f51212.html#gga5e252dfd4f6911f4213e6a0c8a703a58a99af809c29b418d37c30f3cacf94a883", null ],
      [ "kSimFtmChSrc3", "group__sim__hal__kv31f51212.html#gga5e252dfd4f6911f4213e6a0c8a703a58a5c52922b9adf63fc654cb3e98751c8ef", null ]
    ] ],
    [ "sim_ftm_ch_out_src_kv31f51212_t", "group__sim__hal__kv31f51212.html#gaf890489140a0e6994c057e396fc99b88", [
      [ "kSimFtmChOutSrc0", "group__sim__hal__kv31f51212.html#ggaf890489140a0e6994c057e396fc99b88af4f0f24db877c4b263a135d2004d85c5", null ],
      [ "kSimFtmChOutSrc1", "group__sim__hal__kv31f51212.html#ggaf890489140a0e6994c057e396fc99b88a8f5d6e6e0c741516ebb750638e231053", null ]
    ] ],
    [ "sim_ftm_flt_sel_kv31f51212_t", "group__sim__hal__kv31f51212.html#ga542ddba658801718196f897a8b519330", [
      [ "kSimFtmFltSel0", "group__sim__hal__kv31f51212.html#gga542ddba658801718196f897a8b519330a367771a55c7d86797ce0f9c6d551d8be", null ],
      [ "kSimFtmFltSel1", "group__sim__hal__kv31f51212.html#gga542ddba658801718196f897a8b519330a3f3e896c048f940ab1335645e59bfb44", null ]
    ] ],
    [ "sim_flexbus_security_level_kv31f51212_t", "group__sim__hal__kv31f51212.html#ga3c9f20effec76d571d9ebf2595be8723", [
      [ "kSimFbslLevel0", "group__sim__hal__kv31f51212.html#gga3c9f20effec76d571d9ebf2595be8723a087e86c92226bde8c04b7d35df5eaf13", null ],
      [ "kSimFbslLevel1", "group__sim__hal__kv31f51212.html#gga3c9f20effec76d571d9ebf2595be8723a398695e56413a8844850a8270dea6c5f", null ],
      [ "kSimFbslLevel2", "group__sim__hal__kv31f51212.html#gga3c9f20effec76d571d9ebf2595be8723aacd1891f91a52fc59bd5b573a0755cb3", null ],
      [ "kSimFbslLevel3", "group__sim__hal__kv31f51212.html#gga3c9f20effec76d571d9ebf2595be8723a212c37e111b8b17136f41af220b5f078", null ]
    ] ],
    [ "sim_clock_gate_name_kv31f51212_t", "group__sim__hal__kv31f51212.html#ga979041e84a0d8bd78b75cf2a30f607ea", null ],
    [ "SIM_HAL_EnableClock", "group__sim__hal__kv31f51212.html#gaf1e9efe366866aa4eb2a958d131c140c", null ],
    [ "SIM_HAL_DisableClock", "group__sim__hal__kv31f51212.html#gaee4e0a8b2e78770d32db1fb316e62bb1", null ],
    [ "SIM_HAL_GetGateCmd", "group__sim__hal__kv31f51212.html#ga6d2988948b15cbad7301326ccac7e1bf", null ],
    [ "CLOCK_HAL_SetLpuartSrc", "group__sim__hal__kv31f51212.html#ga7b7a01619edd1c148c4d1aab85ce0660", null ],
    [ "CLOCK_HAL_GetLpuartSrc", "group__sim__hal__kv31f51212.html#ga86850b89d1867a44100ad160e5bbc75a", null ],
    [ "CLOCK_HAL_SetTraceClkSrc", "group__sim__hal__kv31f51212.html#ga639000787b1c91dbb4060b89b87b5b91", null ],
    [ "CLOCK_HAL_GetTraceClkSrc", "group__sim__hal__kv31f51212.html#gab7767cff3b8fc9607fb11e9f2197b8f8", null ],
    [ "CLOCK_HAL_SetExternalRefClock32kSrc", "group__sim__hal__kv31f51212.html#gab128ee1ea48ba4e43a84ead22b1ed914", null ],
    [ "CLOCK_HAL_GetExternalRefClock32kSrc", "group__sim__hal__kv31f51212.html#gaf57ea11a6b89c3ffcba773e9148082b3", null ],
    [ "CLOCK_HAL_SetPllfllSel", "group__sim__hal__kv31f51212.html#ga16342ae68ee50da95a3bbe286abe762e", null ],
    [ "CLOCK_HAL_GetPllfllSel", "group__sim__hal__kv31f51212.html#ga2e2cf6cfa9b583a6704b42242cfc82cf", null ],
    [ "CLOCK_HAL_SetClkOutSel", "group__sim__hal__kv31f51212.html#gab45f98ae4171552121942a5e5c14b26d", null ],
    [ "CLOCK_HAL_GetClkOutSel", "group__sim__hal__kv31f51212.html#ga45763ba7aabf6b6c98d78280fcf68fe8", null ],
    [ "CLOCK_HAL_SetOsc32kOutSel", "group__sim__hal__kv31f51212.html#gaca7ed4f18b415107819a38c14252a371", null ],
    [ "CLOCK_HAL_GetOsc32kOutSel", "group__sim__hal__kv31f51212.html#ga26e3dceafb5bd7e7c459765f3c525a00", null ],
    [ "CLOCK_HAL_SetOutDiv1", "group__sim__hal__kv31f51212.html#ga507450d95147bbbbbafda7ae69454219", null ],
    [ "CLOCK_HAL_GetOutDiv1", "group__sim__hal__kv31f51212.html#ga8575da1e6d03ba77df89a146da737e29", null ],
    [ "CLOCK_HAL_SetOutDiv2", "group__sim__hal__kv31f51212.html#gab1e60c103a7c22a4543d31a858e91ebc", null ],
    [ "CLOCK_HAL_GetOutDiv2", "group__sim__hal__kv31f51212.html#ga3aa0f4d8e8337cd7af652e0ae8dc5332", null ],
    [ "CLOCK_HAL_SetOutDiv3", "group__sim__hal__kv31f51212.html#gab11b2f24dcf4ff58974cf5fffba5ecc5", null ],
    [ "CLOCK_HAL_GetOutDiv3", "group__sim__hal__kv31f51212.html#gaecc242ad7b3bf9d757dd338af6a0458b", null ],
    [ "CLOCK_HAL_SetOutDiv4", "group__sim__hal__kv31f51212.html#ga521654536df9f84c38140c264b1680e0", null ],
    [ "CLOCK_HAL_GetOutDiv4", "group__sim__hal__kv31f51212.html#ga7703471ba9324bace3e2306292dc841e", null ],
    [ "CLOCK_HAL_SetOutDiv", "group__sim__hal__kv31f51212.html#gab8c09f5ab708404e5c4aeaf2e701a0ae", null ],
    [ "CLOCK_HAL_GetOutDiv", "group__sim__hal__kv31f51212.html#ga46fbac1126e15abc3e5b5ea730cb35c0", null ],
    [ "SIM_HAL_GetRamSize", "group__sim__hal__kv31f51212.html#gaf4f76a3c80ef488a7cdac5150831d16b", null ],
    [ "SIM_HAL_SetFlexbusSecurityLevelMode", "group__sim__hal__kv31f51212.html#gac93172a9544b3510d0bc039b48ccb2b5", null ],
    [ "SIM_HAL_GetFlexbusSecurityLevelMode", "group__sim__hal__kv31f51212.html#ga8dba085b10935357ae18aeaa67c8e03a", null ],
    [ "SIM_HAL_SetAdcAlternativeTriggerCmd", "group__sim__hal__kv31f51212.html#ga86c4bae5dbcf8ff08ddc3550255f7b55", null ],
    [ "SIM_HAL_GetAdcAlternativeTriggerCmd", "group__sim__hal__kv31f51212.html#gacdfa8af56ce15b0c928cecc8b022e2b3", null ],
    [ "SIM_HAL_SetAdcPreTriggerMode", "group__sim__hal__kv31f51212.html#ga09a3fab6ca0182f5726e04ce7da8a8bf", null ],
    [ "SIM_HAL_GetAdcPreTriggerMode", "group__sim__hal__kv31f51212.html#ga80f1ad02c7a8ea90773a744367bcc4f4", null ],
    [ "SIM_HAL_SetAdcTriggerMode", "group__sim__hal__kv31f51212.html#gaaa523e228a0df249965dc29189cd65d6", null ],
    [ "SIM_HAL_GetAdcTriggerMode", "group__sim__hal__kv31f51212.html#gaa5a93497fc4b0e62faeffb96ec493315", null ],
    [ "SIM_HAL_SetAdcTriggerModeOneStep", "group__sim__hal__kv31f51212.html#gad2c86b5081c181f6a3e0a9b9d5cd774a", null ],
    [ "SIM_HAL_SetUartRxSrcMode", "group__sim__hal__kv31f51212.html#ga27ac418a1878efca141db6851c27365c", null ],
    [ "SIM_HAL_GetUartRxSrcMode", "group__sim__hal__kv31f51212.html#gad2778cce07236498126e70be384a1b1c", null ],
    [ "SIM_HAL_SetUartTxSrcMode", "group__sim__hal__kv31f51212.html#ga689a2247187478d4bab5866b81f8cbe0", null ],
    [ "SIM_HAL_GetUartTxSrcMode", "group__sim__hal__kv31f51212.html#ga37f9940e5a996d1a83895a6178587305", null ],
    [ "SIM_HAL_SetLpuartRxSrcMode", "group__sim__hal__kv31f51212.html#ga75c2436a2c6938515afda6446afd1d3c", null ],
    [ "SIM_HAL_GetLpuartRxSrcMode", "group__sim__hal__kv31f51212.html#gad4141b13dc253417f8f97891e918240c", null ],
    [ "SIM_HAL_SetFtmTriggerSrcMode", "group__sim__hal__kv31f51212.html#ga7aa9c3ace931ef177e690b3f8c72c3d0", null ],
    [ "SIM_HAL_GetFtmTriggerSrcMode", "group__sim__hal__kv31f51212.html#ga10c93ac455f47bacc50c469f75f3f63d", null ],
    [ "SIM_HAL_SetFtmExternalClkPinMode", "group__sim__hal__kv31f51212.html#ga332aae80aacd3e5036529cc07c54aede", null ],
    [ "SIM_HAL_GetFtmExternalClkPinMode", "group__sim__hal__kv31f51212.html#ga36de3c1e242b28ef67dd03d4a9ebd955", null ],
    [ "SIM_HAL_SetFtmChSrcMode", "group__sim__hal__kv31f51212.html#ga8bac18f53245f6f4b67f2b9a36e0f35f", null ],
    [ "SIM_HAL_GetFtmChSrcMode", "group__sim__hal__kv31f51212.html#gad4cbeba007dcfff154a6d4bde10085a7", null ],
    [ "SIM_HAL_SetFtmChOutSrcMode", "group__sim__hal__kv31f51212.html#gaee829aaf3de4119b9910ae579c491673", null ],
    [ "SIM_HAL_GetFtmChOutSrcMode", "group__sim__hal__kv31f51212.html#ga8e24d16b0755462f429b3dee75b41434", null ],
    [ "SIM_HAL_SetFtmSyncCmd", "group__sim__hal__kv31f51212.html#ga8181cb388e9466923ab296ade8c59d64", null ],
    [ "SIM_HAL_GetFtmSyncCmd", "group__sim__hal__kv31f51212.html#ga28fbfac31fc0eb0d80b5653c9c607cd7", null ],
    [ "SIM_HAL_SetFtmFaultSelMode", "group__sim__hal__kv31f51212.html#ga3d7c0879f17ccf8e35444d3327d31e80", null ],
    [ "SIM_HAL_GetFtmFaultSelMode", "group__sim__hal__kv31f51212.html#gaa19a9c25f4bdd9675918fb1343d32b68", null ],
    [ "SIM_HAL_GetFamilyId", "group__sim__hal__kv31f51212.html#ga4e58d9849ebfb707f9daf51c3003e18f", null ],
    [ "SIM_HAL_GetSubFamilyId", "group__sim__hal__kv31f51212.html#ga392ee1aadf70566d3b5b5df3bc376104", null ],
    [ "SIM_HAL_GetSeriesId", "group__sim__hal__kv31f51212.html#ga0b9f11425fa4278f3d3c2b95ceb9d797", null ],
    [ "SIM_HAL_GetPinCntId", "group__sim__hal__kv31f51212.html#ga09da5535de0a201a9f70841a3d87876a", null ],
    [ "SIM_HAL_GetRevId", "group__sim__hal__kv31f51212.html#gaae905cba1e98882134e83e75451f2869", null ],
    [ "SIM_HAL_GetDieId", "group__sim__hal__kv31f51212.html#ga9a58484850e78e8918b1d350dfa0dd14", null ],
    [ "SIM_HAL_GetProgramFlashSize", "group__sim__hal__kv31f51212.html#gae4ea1894bf90debffe256ab10ae0cda0", null ],
    [ "SIM_HAL_SetFlashDoze", "group__sim__hal__kv31f51212.html#ga6fb06ad054fac5a00c0d650fce967a3a", null ],
    [ "SIM_HAL_GetFlashDoze", "group__sim__hal__kv31f51212.html#ga69b2f1e76dcc935d731854c7180b7b7f", null ],
    [ "SIM_HAL_SetFlashDisableCmd", "group__sim__hal__kv31f51212.html#ga1d0455dcf1c6647c36acee9177e9d9ba", null ],
    [ "SIM_HAL_GetFlashDisableCmd", "group__sim__hal__kv31f51212.html#gae94e2aa677fe7b92ac836853b750e9dc", null ],
    [ "SIM_HAL_GetFlashMaxAddrBlock0", "group__sim__hal__kv31f51212.html#gac2334d8630cc2f3b0dcbb93e875943f4", null ],
    [ "SIM_HAL_GetFlashMaxAddrBlock1", "group__sim__hal__kv31f51212.html#gaf212f34129ec4cc846f10857a28fdea9", null ]
];
